L0op/medtronic-pb560/file-set-2/Mechanical Part Drawings/2971700/2971700B00.pdf

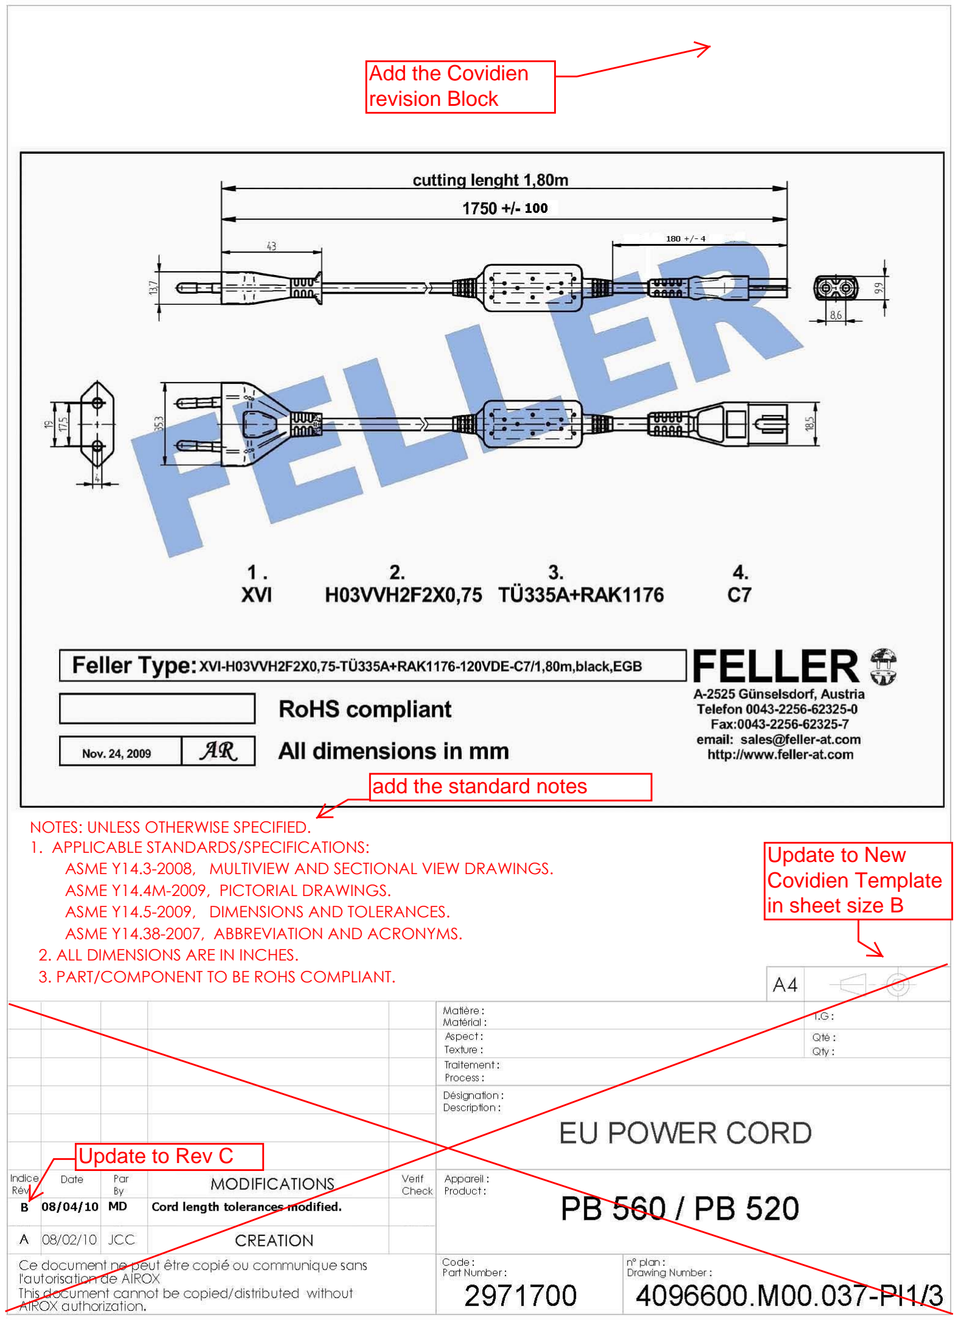
[picture p10: page 1]

NOTES: UNLESS OTHERWISE SPECIFIED.
1. APPLICABLE STANDARDS/SPECIFICATIONS:
ASME Y14.3-2008, MULTIVIEW AND SECTIONAL VIEW DRAWINGS. ASME Y14.4M-2009, PICTORIAL DRAWINGS.
ASME Y14.5-2009, DIMENSIONS AND TOLERANCES.
ASME Y14.38-2007, ABBREVIATION AND ACRONYMS.
2. ALL DIMENSIONS ARE IN INCHES.
3. PART/COMPONENT TO BE ROHS COMPLIANT.

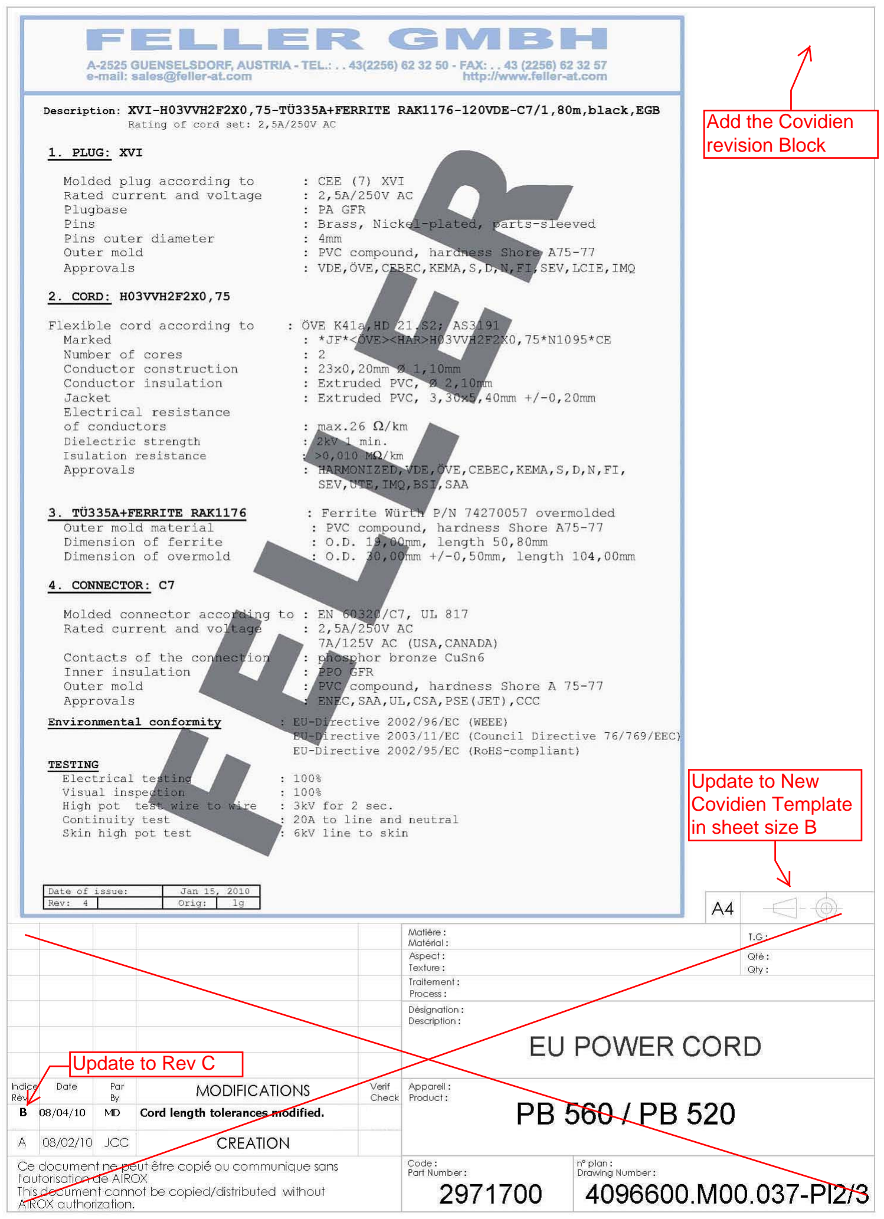
[picture p11: page 2]
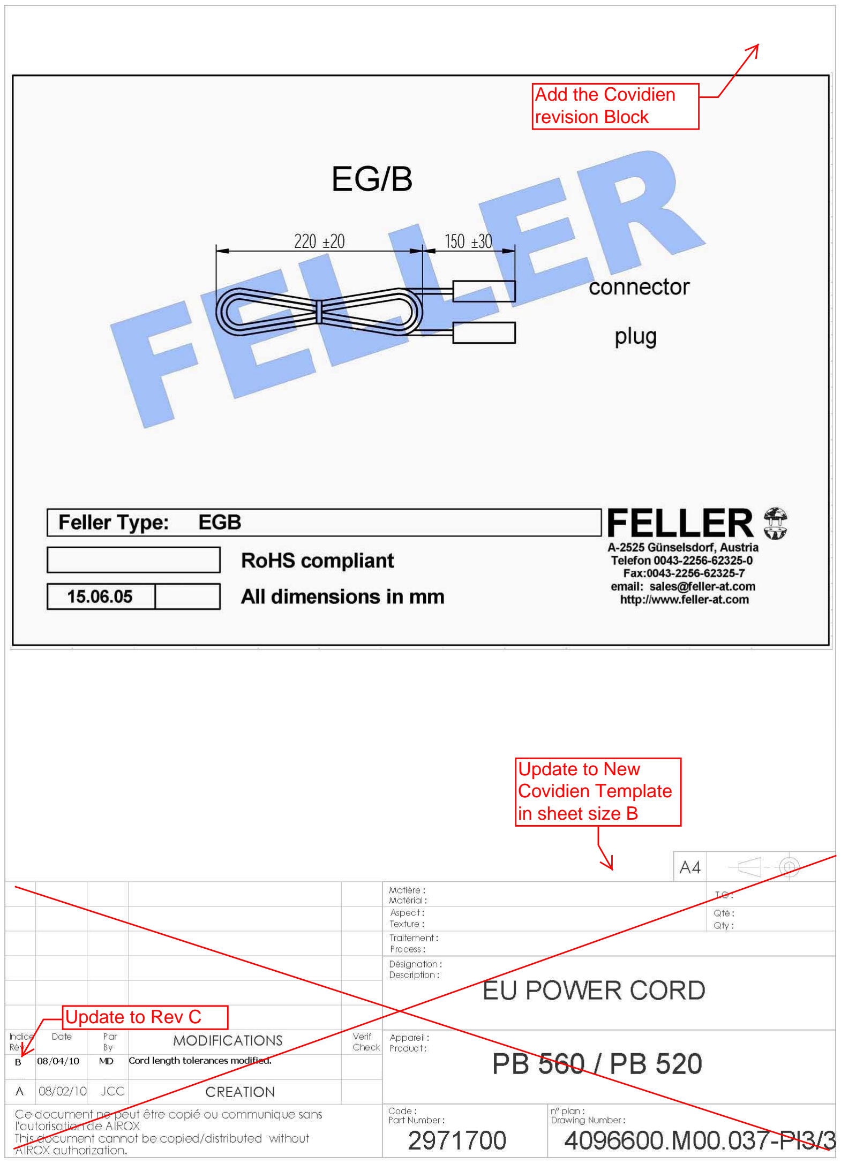
[picture p12: page 3]
