L0op/medtronic-pb560/file-set-2/Mechanical Part Drawings/3810200/38102000300.pdf

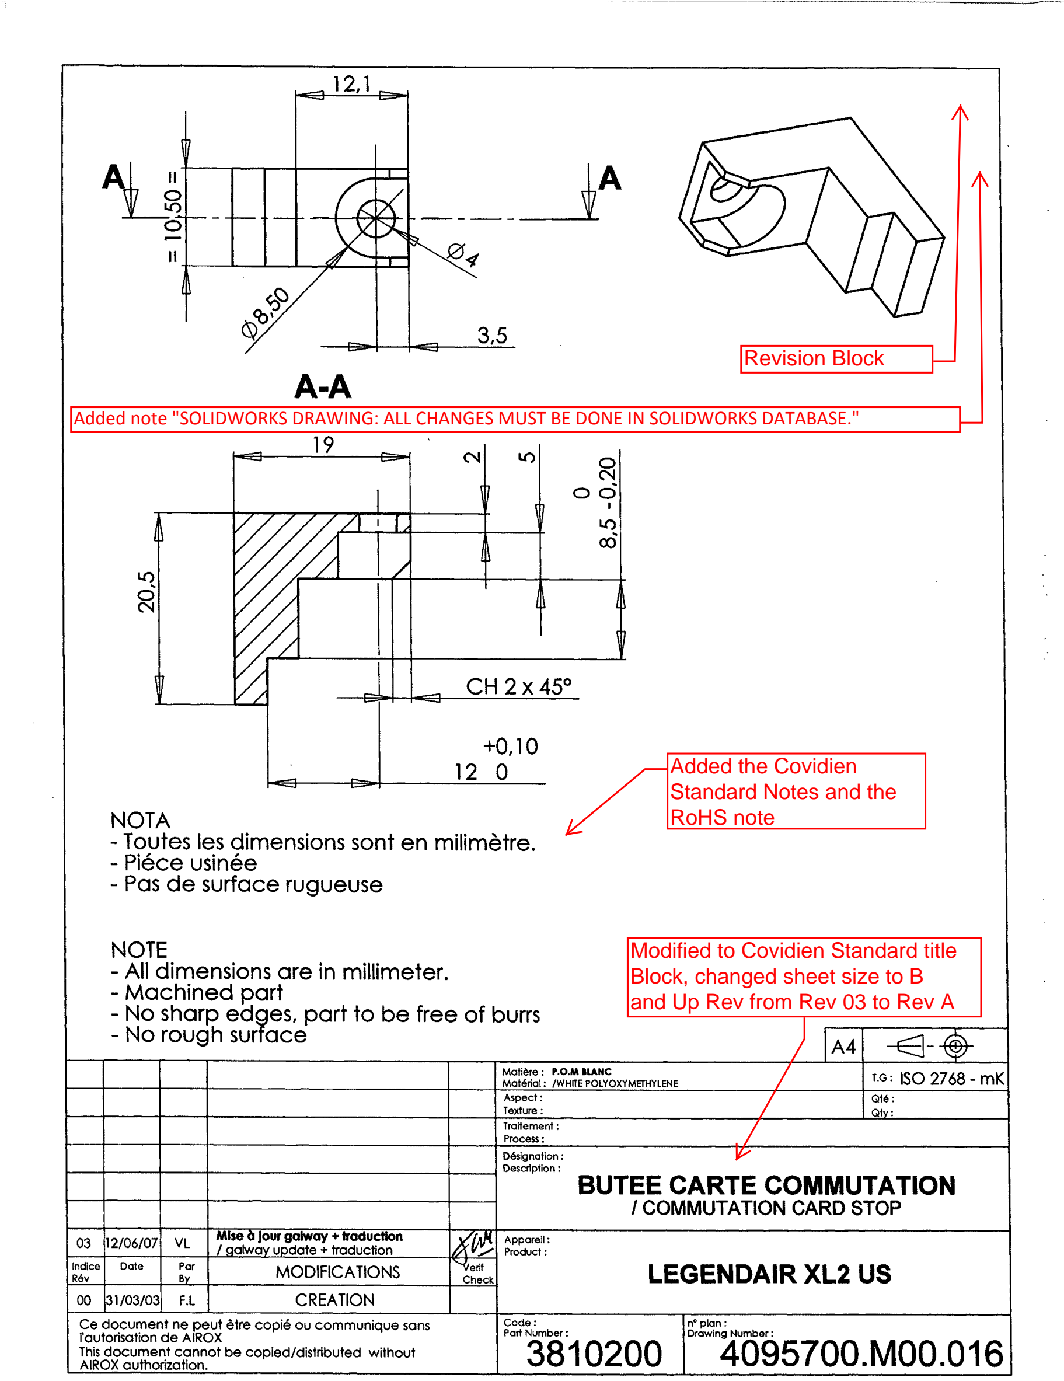
[picture p13: page 1]
