L0op/medtronic-pb560/file-set-2/Mechanical Part Drawings/3810200/3810200_Approved_Revision_03.pdf

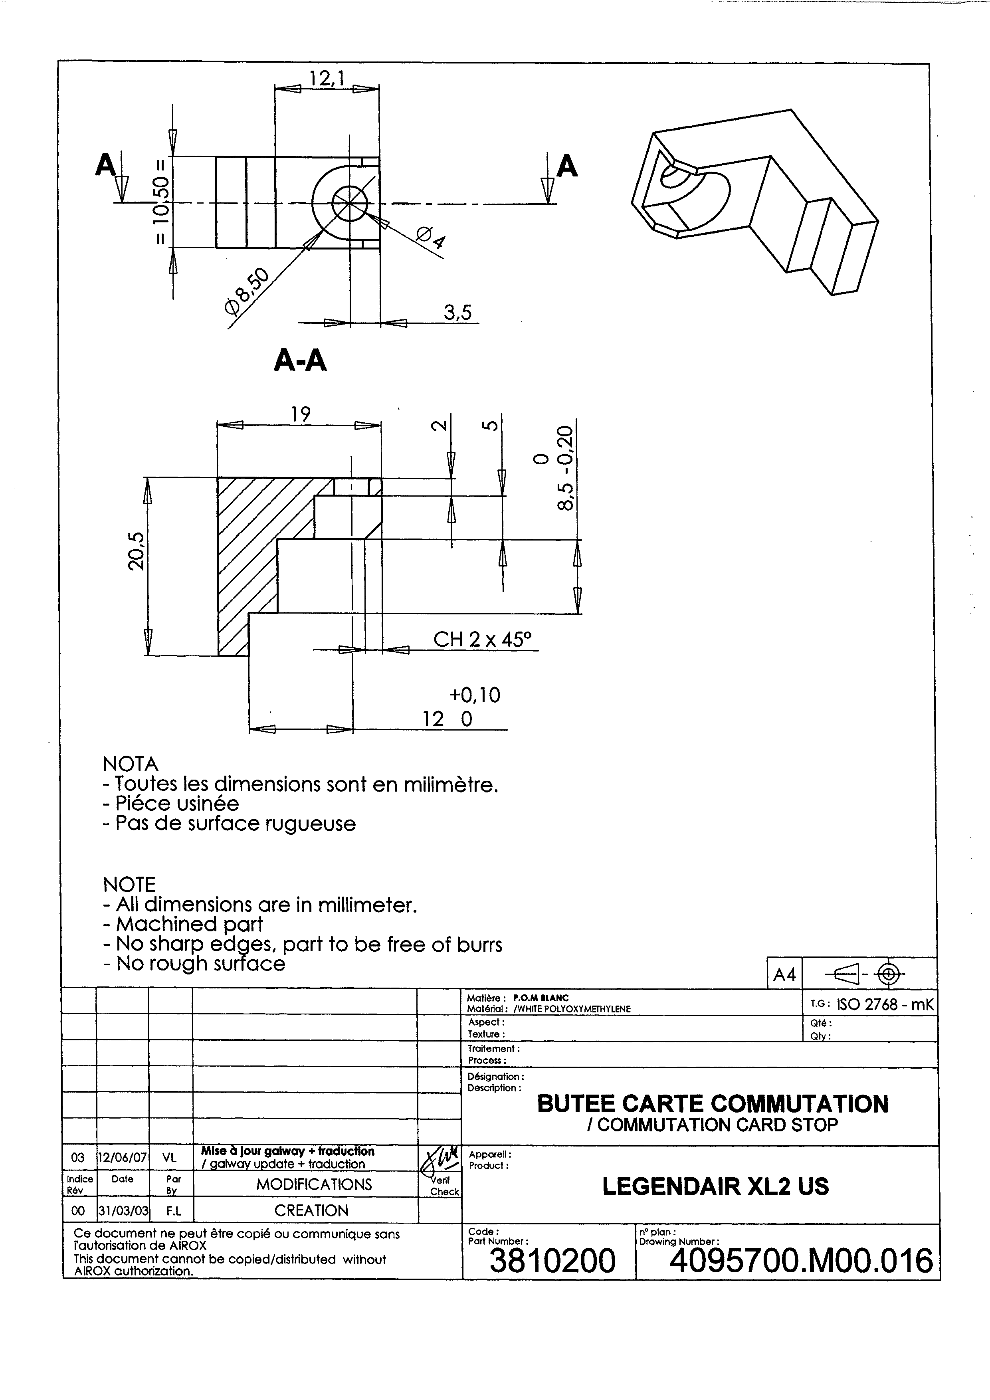
[picture p14: page 1]
