L0op/medtronic-pb560/file-set-2/Electronic PCBAs/10096315_Blower_Driver_PCBA/BOM/10096315_Blower_Driver_PCBA_BOM.xls

Creator | Jenaro | Julio
Type
Description
Title Block
Item Number | Description | Subclass | Lifecycle Phase | Rev | Rev Incorp Date | Rev Release Date | Effectivity Date
10096315 | BLOWER DRIVER CARD | Part | Production | A ECO-R252633 | 31/Jul/2013 05:51:48 PM BST | 06/Jan/2015 04:58:11 PM GMT
Page Two
UOM | Additional Categories Part | Alternate Part(s) | Alternate FG Part(s) | Restricted Access | Vendor User Group | Data Classification | Attachment Destination | Created By | Create Date | Legacy Data Source | Divesture Destination
Each | PART CATEGORY|Pc Board |  |  |  | V - Jabil SH | Confidential |  | Searcy, Teresa | 07/Jun/2012 06:03:06 PM BST | Agile RMS
Page Three
Product Family(s) | Item Type | Lot Serial Control | Document Number | RoHS Compliant | Bio Approval Number | Integration Description | Project(s) | Notes | Handling/Storage | Legacy Number
 | Customized | None | NODOCUMENT | Unknown |  | BLOWER DRIVER CARD | RSP - PB560-520 | Product Family : RSP - VENTILATOR SYSTEMS, Commodity Code: BPCS Add-Updt : FC02.17, Country of Origin: BPCS Add : FR = FRANCE, Shelf Life Days:BPCS Add-Updt : 0, Must Single Issue: BPCS Add : NO, Item Class: BPCS Add-Updt : GL-66 PB500 Series Ventilators/Gen 1, Controlled AML? : YES
Manufacturers
Attachments(Image) | Manufacture Part Has Redline | Mfr. Name | Mfr. Part Number | Mfr. Part Description | Mfr. Part Lifecycle Phase | Preferred Status | Sites | Reference Notes | RoHS Compliant? | RoHS Compliance Statement
true | false | JABIL SUPPLIER - SHANGHAI UPP CO.,LTD.(LOC) | 10096315 |  | Active | Preferred |  | CUSTOM PART PER COVIDIEN P/N 10096315 | Yes | Legacy Inventory Status: Cleared
Attachments
Is Checked Out | Has Been Redlined | Filename | File Description | File Size | File Type | Attachment Type | Modified Date | Last View Date | Checkout User | Checkout Date | Checkout Location | Checkin User | Folder Number | Folder Version
false | false | 10096315X0100.pdf | Redlined Rev-X01 to Rev-A | 141245 | pdf |  | 17/Jun/2015 06:55:30 AM BST | 17/Jun/2015 06:55:30 AM BST |  |  |  | Migration, Data | FF0007734088 | 1
false | false | 10096315_A_ECO-R252633.pdf | RMS Historical PDF - ECO-R252633 | 118400 | pdf |  | 17/Aug/2015 04:53:30 PM BST | 17/Aug/2015 04:53:30 PM BST |  |  |  | Migration, Data | FF0009842444 | 1
false | false | 10096315A00.PDF | Approved Rev-A | 122083 | PDF |  | 17/Jun/2015 06:55:30 AM BST | 17/Jun/2015 06:55:30 AM BST |  |  |  | Migration, Data | FF0007734091 | 1
false | false | 10096315A00.zip | Approved Rev-A, Source Files | 6838324 | zip |  | 17/Jun/2015 06:55:31 AM BST | 17/Jun/2015 06:55:31 AM BST |  |  |  | Migration, Data | FF0007734094 | 1
false | false | 10096315_A_ECO-R231090.pdf | RMS Historical PDF - ECO-R231090 | 118415 | pdf |  | 17/Aug/2015 04:53:30 PM BST | 17/Aug/2015 04:53:29 PM BST |  |  |  | Migration, Data | FF0009842442 | 1
