L0op/medtronic-pb560/file-set-2/Electronic PCBAs/10096315_Blower_Driver_PCBA/PCB/10096505A00/eqfs.dxf

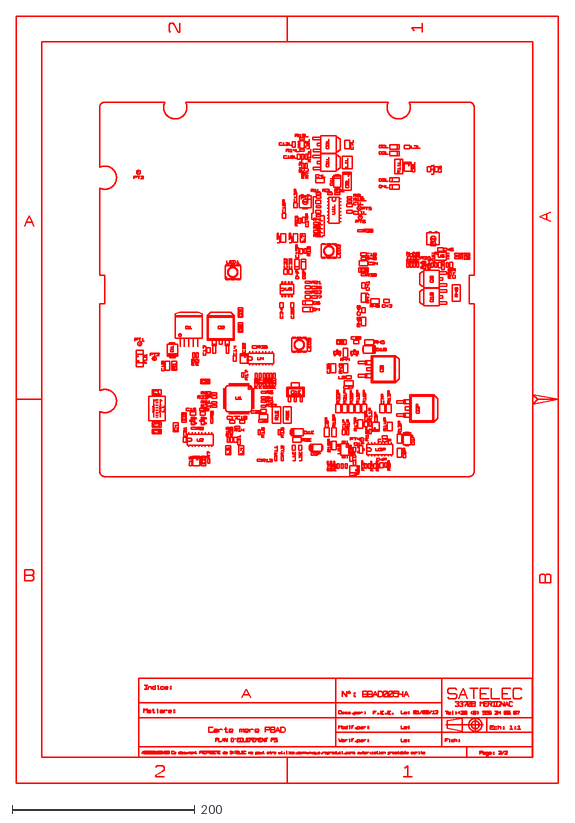
[picture p29: CAD file, 2020-04-01]
file-set-2/Electronic PCBAs/10096315_Blower_Driver_PCBA/PCB/10096505A00/eqfs.dxf
594.7 x 840.3
