L0op/medtronic-pb560/file-set-2/Electronic PCBAs/10096510_Battery_Connection_PCBA/3D_Model/contact ressort.SLDPRT

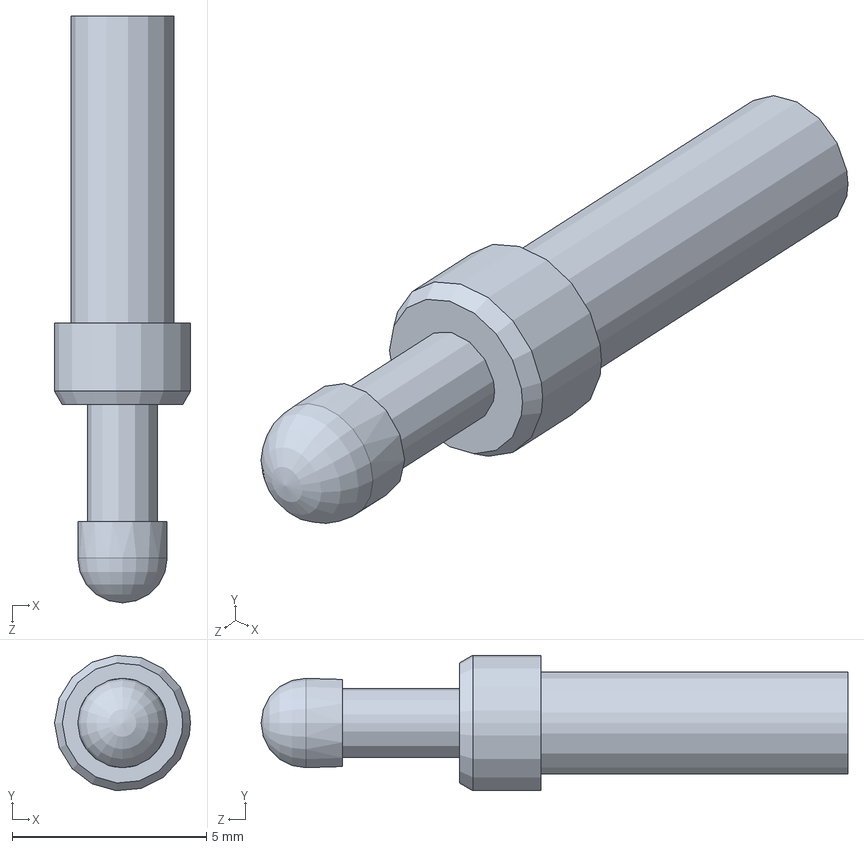
[picture p30: CAD file, 2020-04-01]
file-set-2/Electronic PCBAs/10096510_Battery_Connection_PCBA/3D_Model/contact ressort.SLDPRT
3.50 x 3.49 x 15.1 mm
