L0op/medtronic-pb560/file-set-2/Electronic PCBAs/GR106768_Buzzer_PCBA/3D_Model/cache transfo.SLDPRT

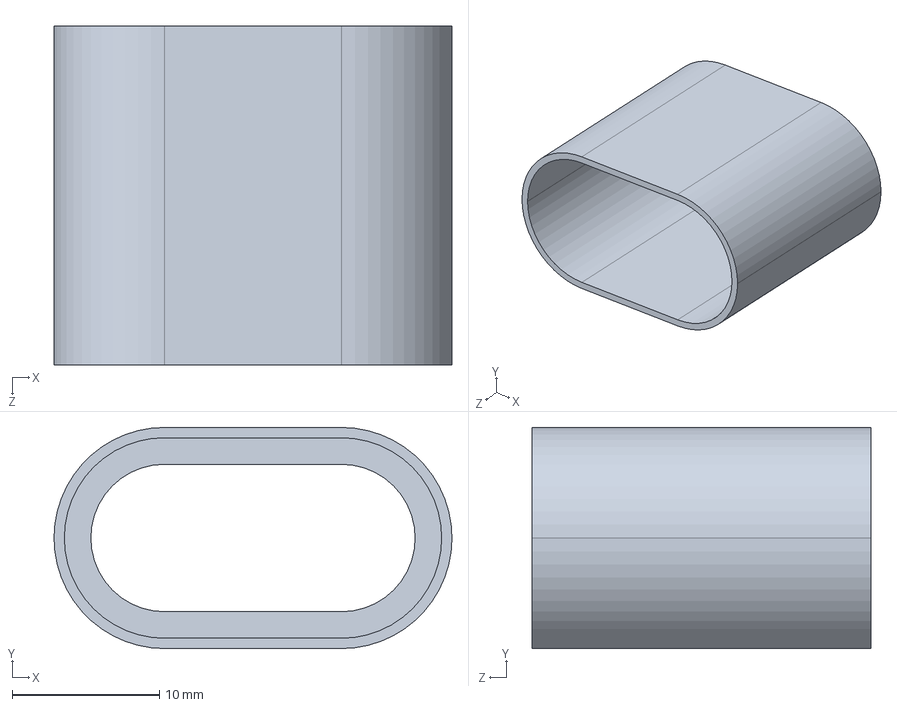
[picture p32: CAD file, 2020-04-01]
file-set-2/Electronic PCBAs/GR106768_Buzzer_PCBA/3D_Model/cache transfo.SLDPRT
27.0 x 15.0 x 23.0 mm
