L0op/medtronic-pb560/file-set-2/Electronic PCBAs/GR106768_Buzzer_PCBA/PCBA/switch.SLDPRT

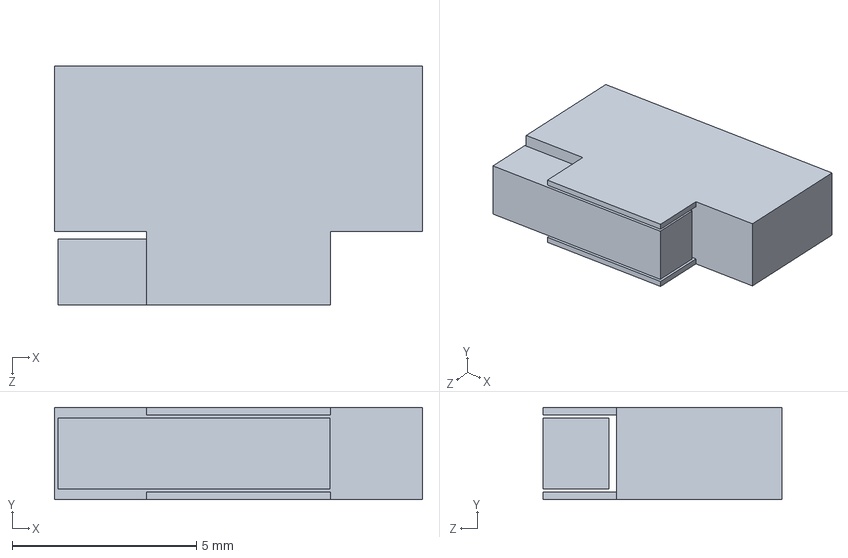
[picture p33: CAD file, 2020-04-01]
file-set-2/Electronic PCBAs/GR106768_Buzzer_PCBA/PCBA/switch.SLDPRT
10.0 x 2.50 x 6.50 mm
