L0op/medtronic-pb560/file-set-2/Mechanical Part Drawings/2982400/Battery Drawing.SLDPRT

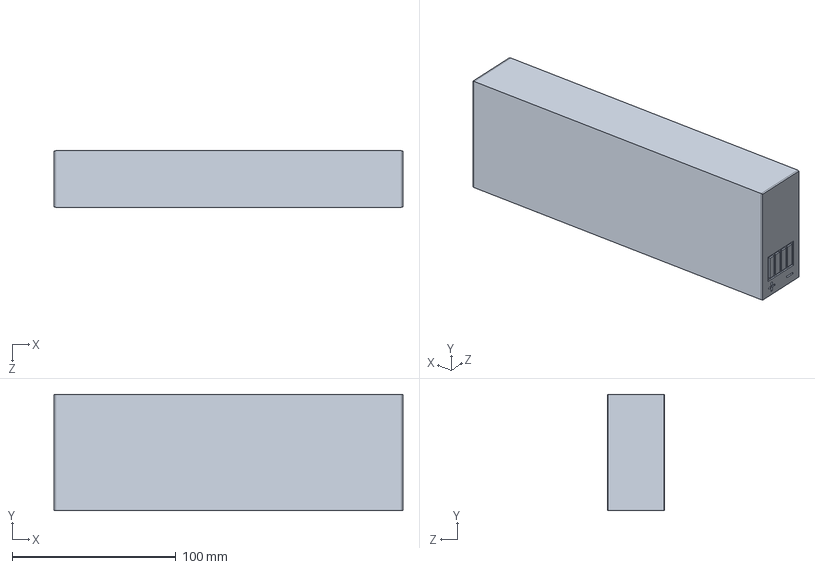
[picture p34: CAD file, 2020-04-01]
file-set-2/Mechanical Part Drawings/2982400/Battery Drawing.SLDPRT
213.0 x 71.0 x 34.5 mm
