L0op/medtronic-pb560/file-set-2/Mechanical Part Drawings/3829000/mica transparent.SLDPRT

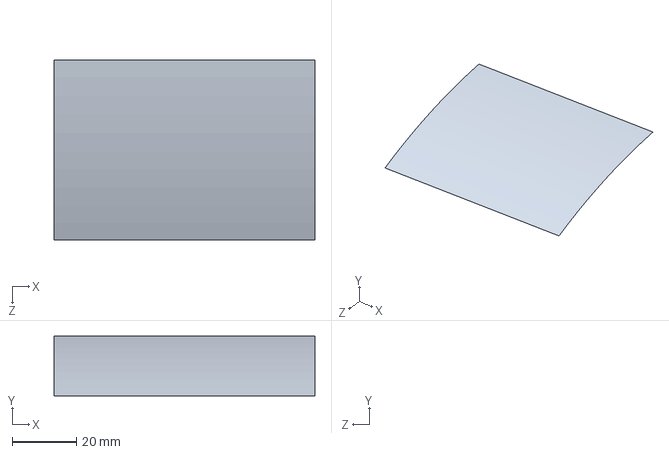
[picture p35: CAD file, 2020-04-01]
file-set-2/Mechanical Part Drawings/3829000/mica transparent.SLDPRT
81.0 x 18.5 x 56.0 mm
