L0op/medtronic-pb560/file-set-2/Electronic PCBAs/10005011_Power Management_PCBA/3842800_POWER SUPPLY BOARD - TANTALUM LESS_PCBA/PCB/Power Supply Board 3842800 (Tantalum Less) INDC/eqfc.dxf

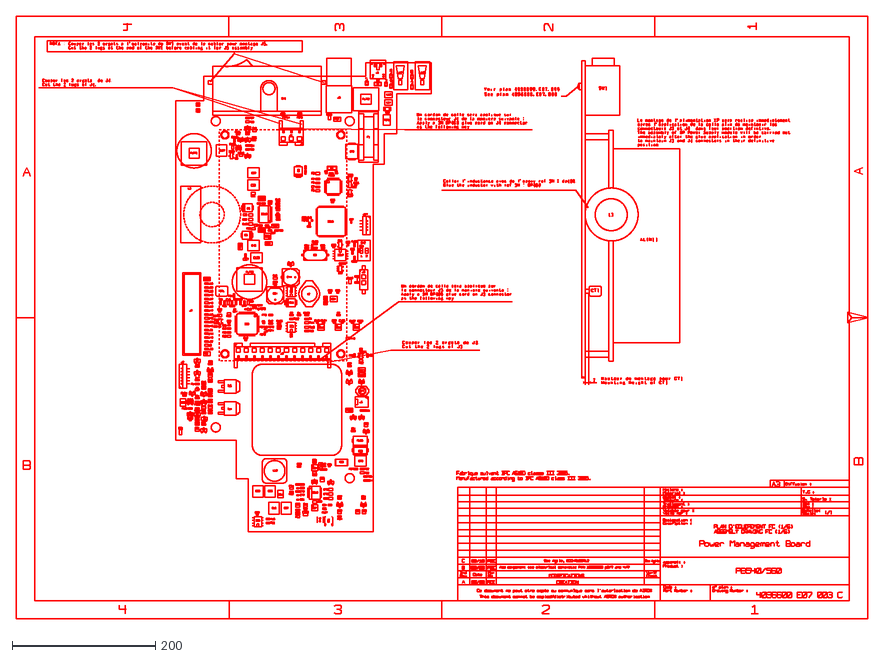
[picture p36: CAD file, 2020-04-01]
file-set-2/Electronic PCBAs/10005011_Power Management_PCBA/3842800_POWER SUPPLY BOARD - TANTALUM LESS_PCBA/PCB/Power Supply Board 3842800 (Tantalum Less) INDC/eqfc.dxf
1188.3 x 840.3
