L0op/medtronic-pb560/file-set-2/Electronic PCBAs/10005011_Power Management_PCBA/3842800_POWER SUPPLY BOARD - TANTALUM LESS_PCBA/PCBA/39-26-7265.SLDPRT

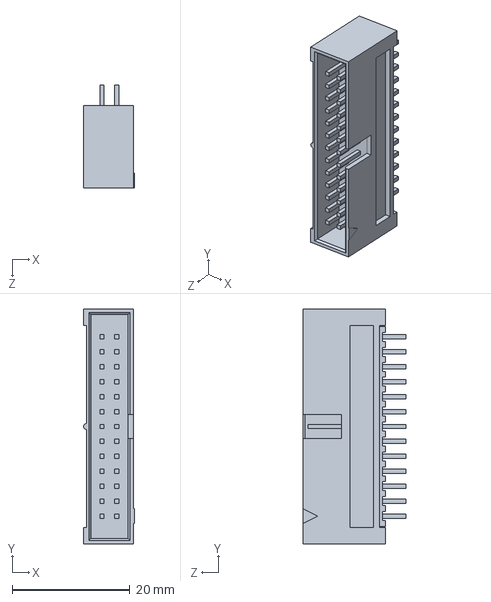
[picture p37: CAD file, 2020-04-01]
file-set-2/Electronic PCBAs/10005011_Power Management_PCBA/3842800_POWER SUPPLY BOARD - TANTALUM LESS_PCBA/PCBA/39-26-7265.SLDPRT
8.65 x 40.0 x 17.5 mm
