L0op/medtronic-pb560/file-set-2/Electronic PCBAs/10096510_Battery_Connection_PCBA/3D_Model/39-26-7108.SLDPRT

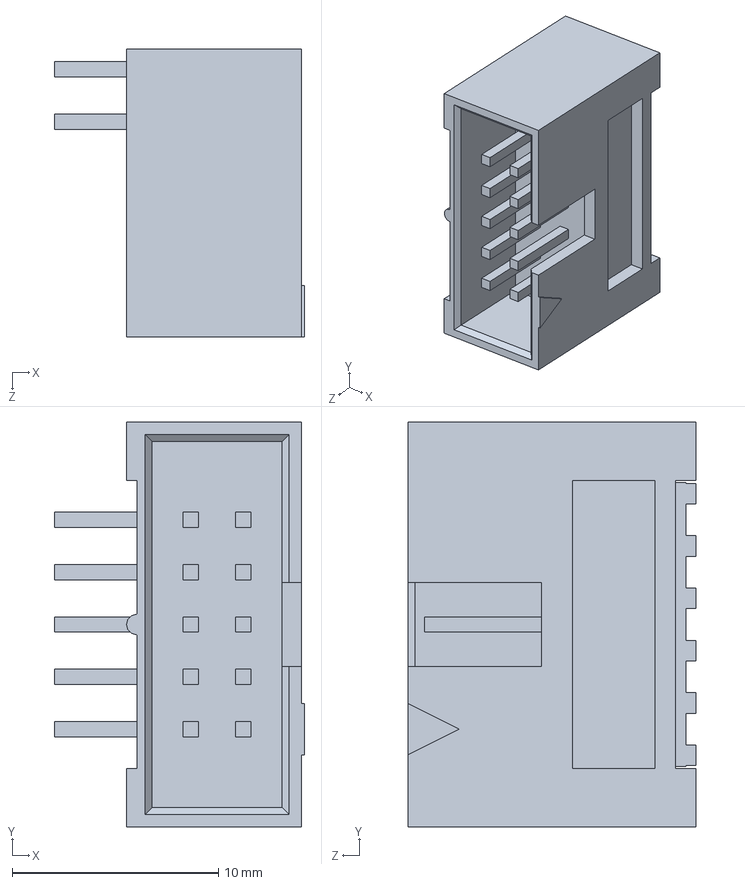
[picture p39: CAD file, 2020-04-01]
file-set-2/Electronic PCBAs/10096510_Battery_Connection_PCBA/3D_Model/39-26-7108.SLDPRT
12.1 x 19.7 x 14.0 mm
