L0op/medtronic-pb560/file-set-2/Electronic PCBAs/10096510_Battery_Connection_PCBA/PCB/10096506A00/eqfc.dxf

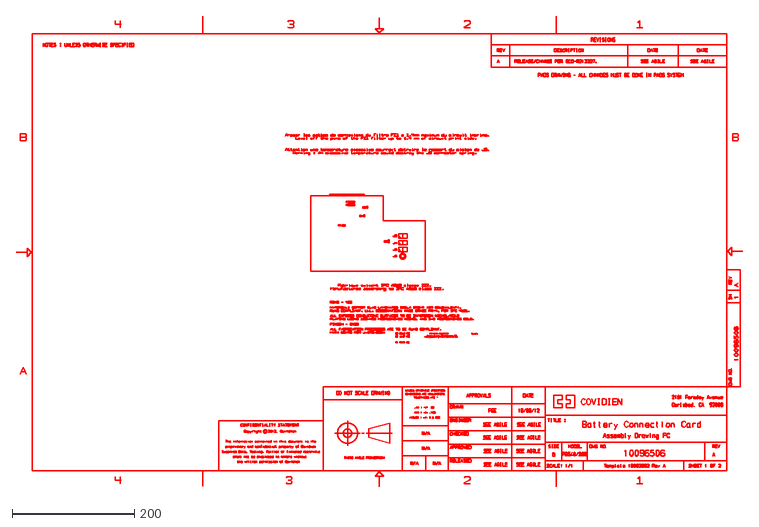
[picture p40: CAD file, 2020-04-01]
file-set-2/Electronic PCBAs/10096510_Battery_Connection_PCBA/PCB/10096506A00/eqfc.dxf
1188.1 x 770.1
