L0op/medtronic-pb560/file-set-2/Electronic PCBAs/10106052_PowerPack_PCBA/PCBA/MOLEX 02661-4020.SLDPRT

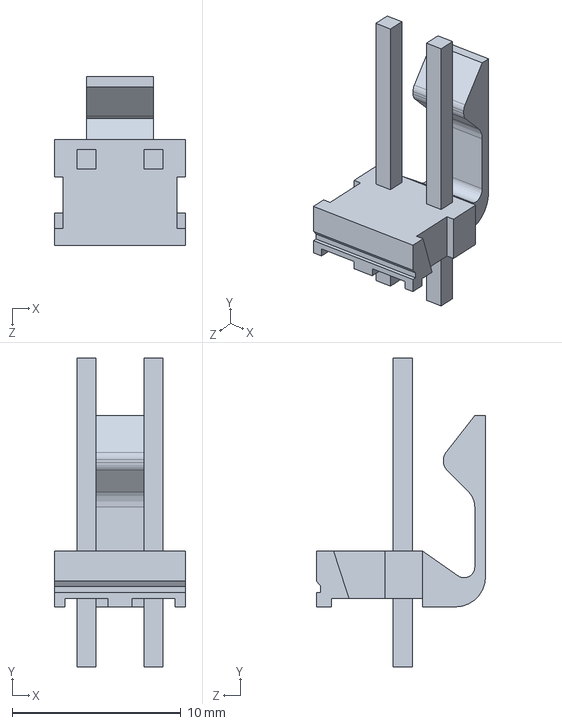
[picture p41: CAD file, 2020-04-01]
file-set-2/Electronic PCBAs/10106052_PowerPack_PCBA/PCBA/MOLEX 02661-4020.SLDPRT
7.77 x 18.3 x 10.0 mm
