L0op/medtronic-pb560/file-set-2/Electronic PCBAs/GR106768_Buzzer_PCBA/PCBA/buzzer1.SLDPRT

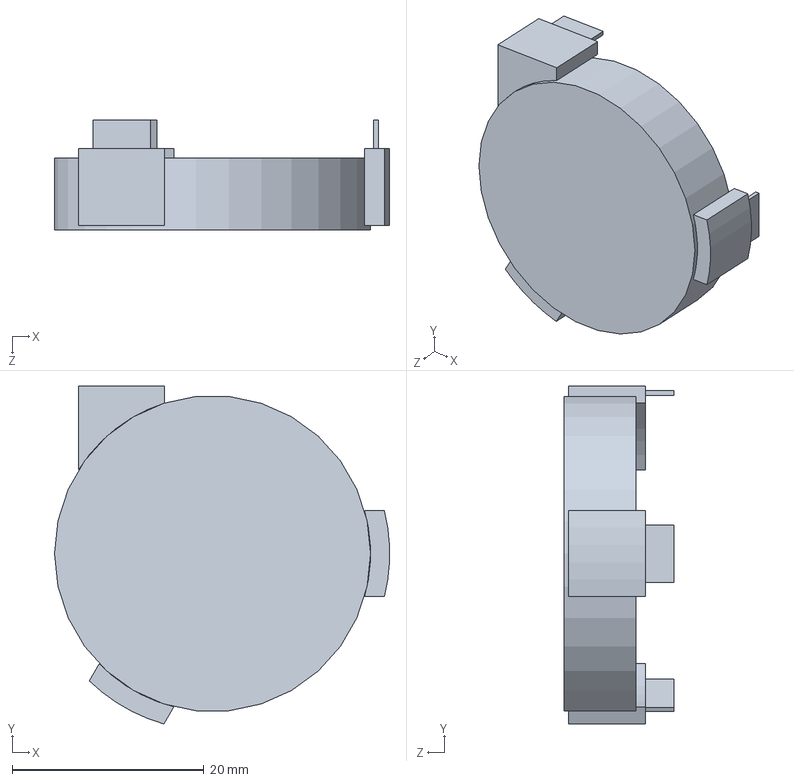
[picture p42: CAD file, 2020-04-01]
file-set-2/Electronic PCBAs/GR106768_Buzzer_PCBA/PCBA/buzzer1.SLDPRT
35.0 x 35.3 x 11.5 mm
