L0op/medtronic-pb560/file-set-2/Electronic PCBAs/GR106769_CPU_PCBA/3D_Model/capteurpressionASDX001D44R.SLDPRT

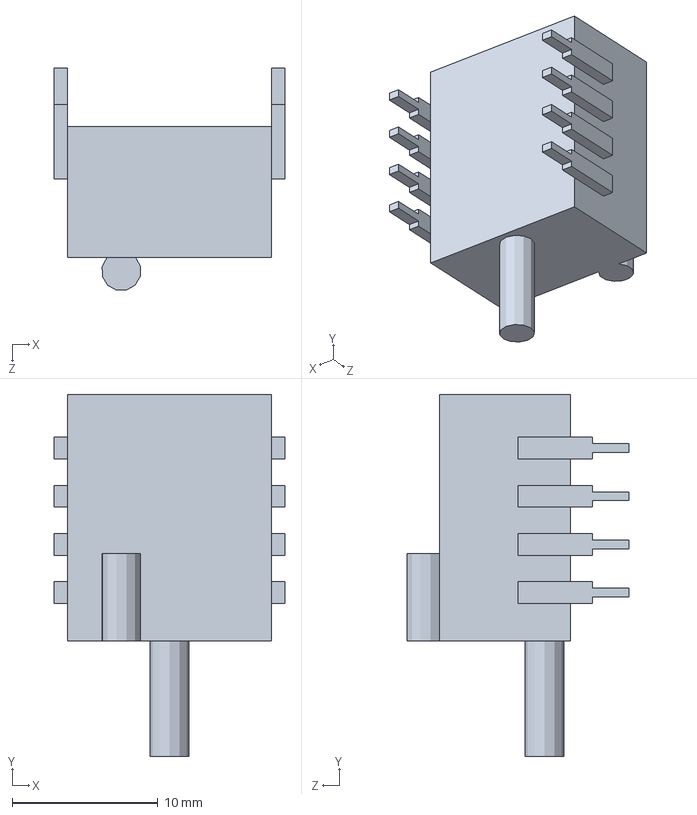
[picture p43: CAD file, 2020-04-01]
file-set-2/Electronic PCBAs/GR106769_CPU_PCBA/3D_Model/capteurpressionASDX001D44R.SLDPRT
15.8 x 24.8 x 15.2 mm
