L0op/medtronic-pb560/file-set-2/Mechanical Part Drawings/2967200/suspente.SLDPRT

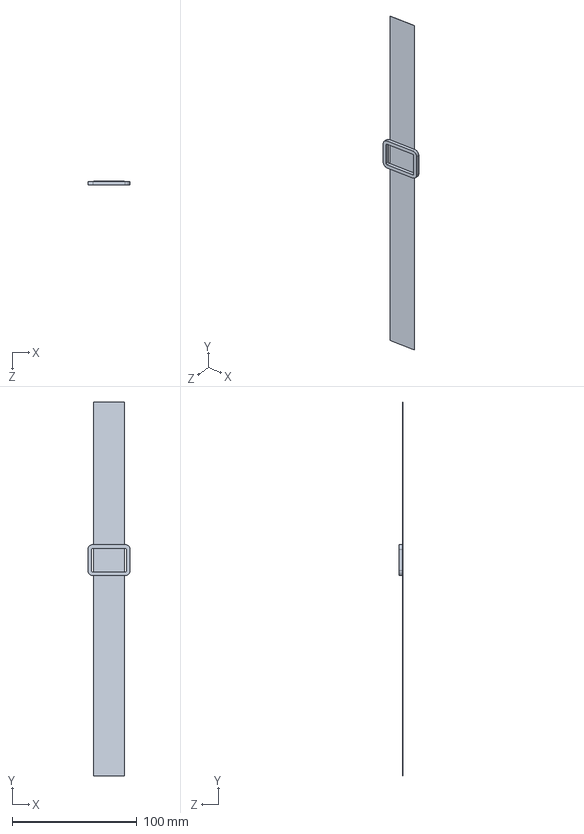
[picture p44: CAD file, 2020-04-01]
file-set-2/Mechanical Part Drawings/2967200/suspente.SLDPRT
34.0 x 300.0 x 3.20 mm
