L0op/medtronic-pb560/file-set-2/Mechanical Part Drawings/3829000/accroche sangle 25.SLDPRT

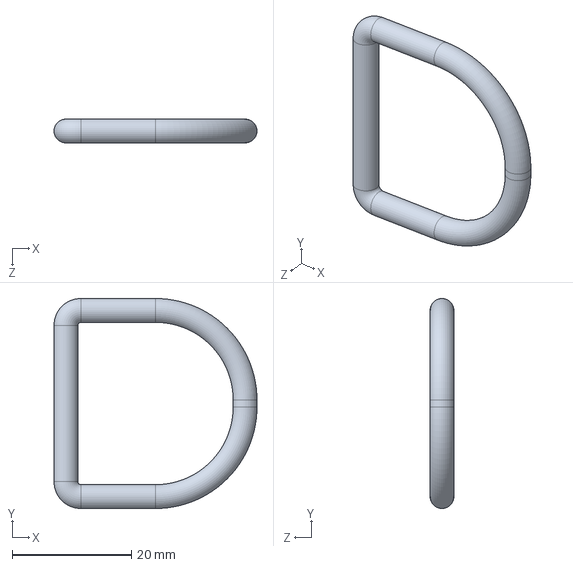
[picture p45: CAD file, 2020-04-01]
file-set-2/Mechanical Part Drawings/3829000/accroche sangle 25.SLDPRT
34.0 x 35.2 x 4.00 mm
