L0op/medtronic-pb560/file-set-2/Electronic PCBAs/10005011_Power Management_PCBA/3842800_POWER SUPPLY BOARD - TANTALUM LESS_PCBA/PCBA/condensateur dia 10.SLDPRT

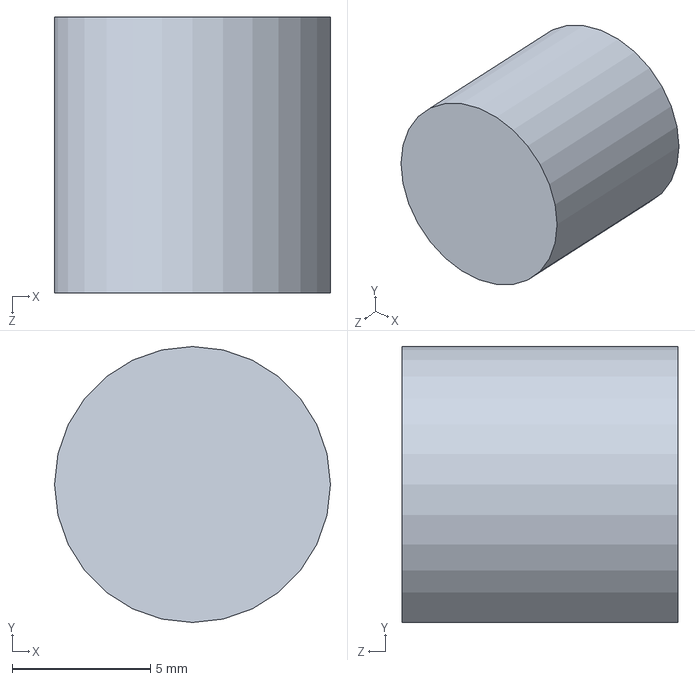
[picture p46: CAD file, 2020-04-01]
file-set-2/Electronic PCBAs/10005011_Power Management_PCBA/3842800_POWER SUPPLY BOARD - TANTALUM LESS_PCBA/PCBA/condensateur dia 10.SLDPRT
10.0 x 10.0 x 10.0 mm
