L0op/medtronic-pb560/file-set-2/Electronic PCBAs/10096315_Blower_Driver_PCBA/PCB/10096505A00/per.dxf

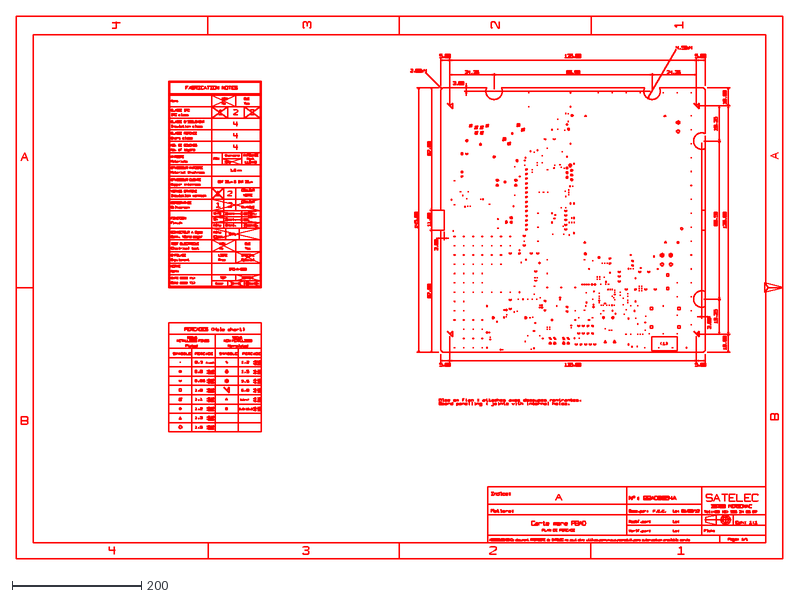
[picture p47: CAD file, 2020-04-01]
file-set-2/Electronic PCBAs/10096315_Blower_Driver_PCBA/PCB/10096505A00/per.dxf
1188.3 x 840.3
