L0op/medtronic-pb560/file-set-2/Electronic PCBAs/10096510_Battery_Connection_PCBA/PCB/10096506A00/eqfs.dxf

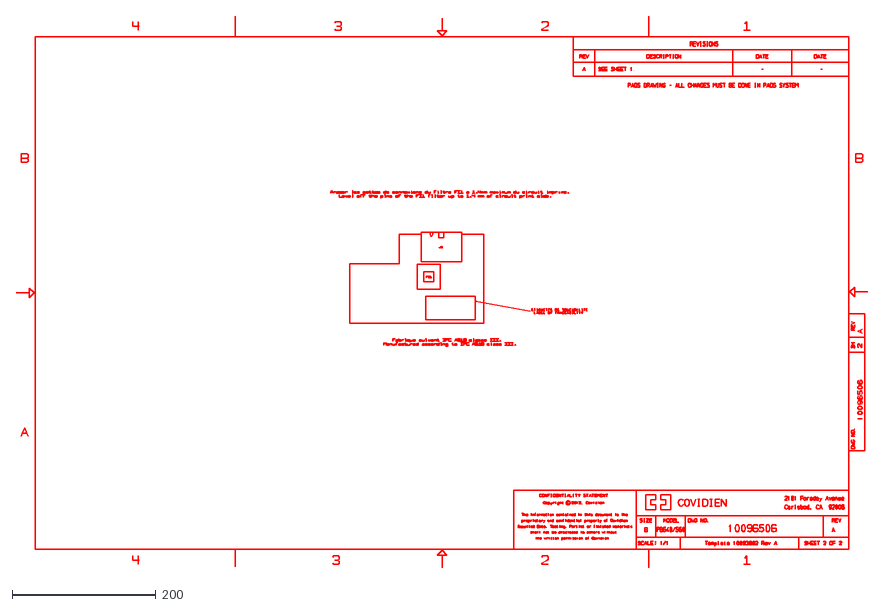
[picture p48: CAD file, 2020-04-01]
file-set-2/Electronic PCBAs/10096510_Battery_Connection_PCBA/PCB/10096506A00/eqfs.dxf
1186.1 x 768.8
