L0op/medtronic-pb560/file-set-2/Mechanical Part Drawings/10079556/Insp Mod Connector.SLDPRT

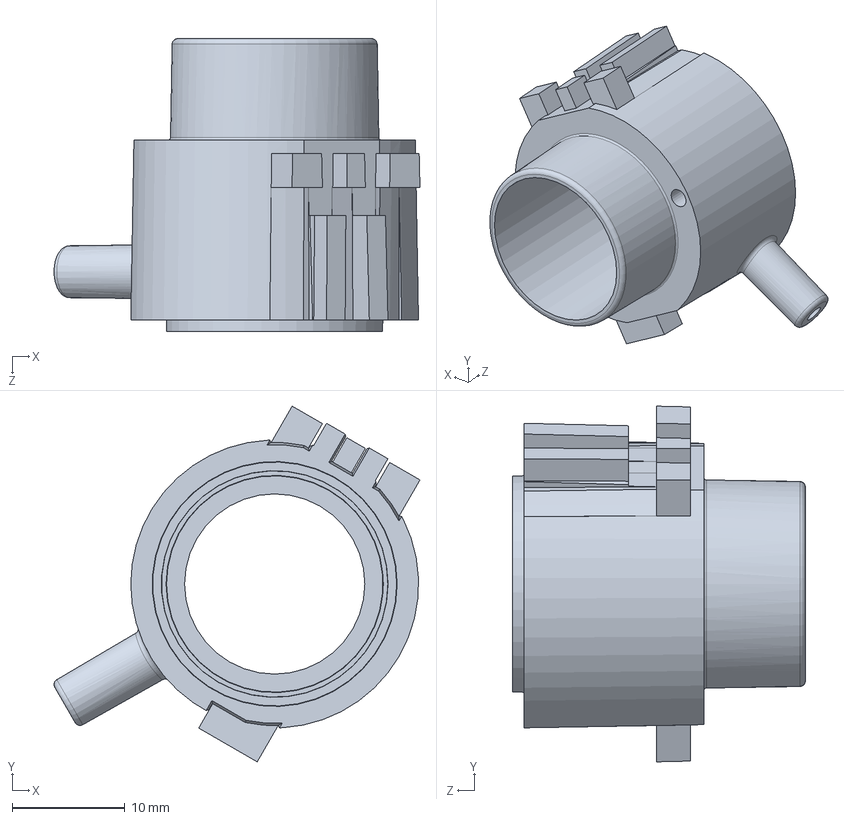
[picture p49: CAD file, 2020-04-01]
file-set-2/Mechanical Part Drawings/10079556/Insp Mod Connector.SLDPRT
32.5 x 31.6 x 26.0 mm
