L0op/medtronic-pb560/file-set-2/Electronic PCBAs/10005011_Power Management_PCBA/3842800_POWER SUPPLY BOARD - TANTALUM LESS_PCBA/PCBA/09-48-4128.SLDPRT

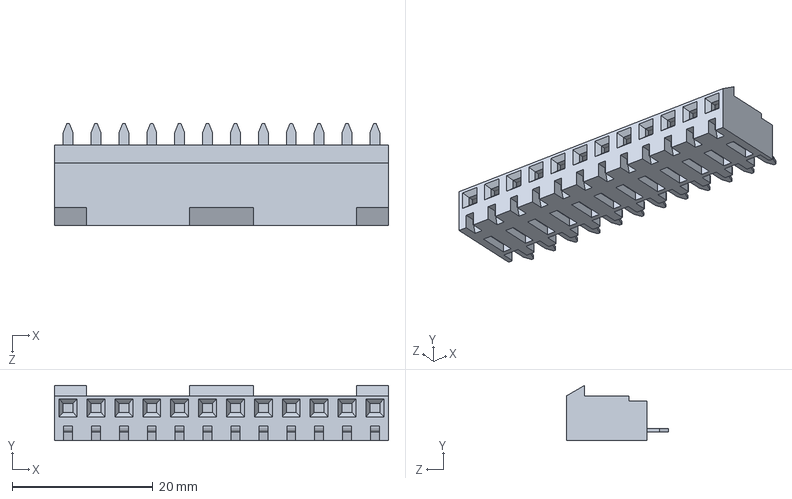
[picture p50: CAD file, 2020-04-01]
file-set-2/Electronic PCBAs/10005011_Power Management_PCBA/3842800_POWER SUPPLY BOARD - TANTALUM LESS_PCBA/PCBA/09-48-4128.SLDPRT
47.4 x 7.82 x 14.5 mm
