L0op/medtronic-pb560/file-set-2/Electronic PCBAs/10096510_Battery_Connection_PCBA/3D_Model/connecteur batterie.SLDPRT

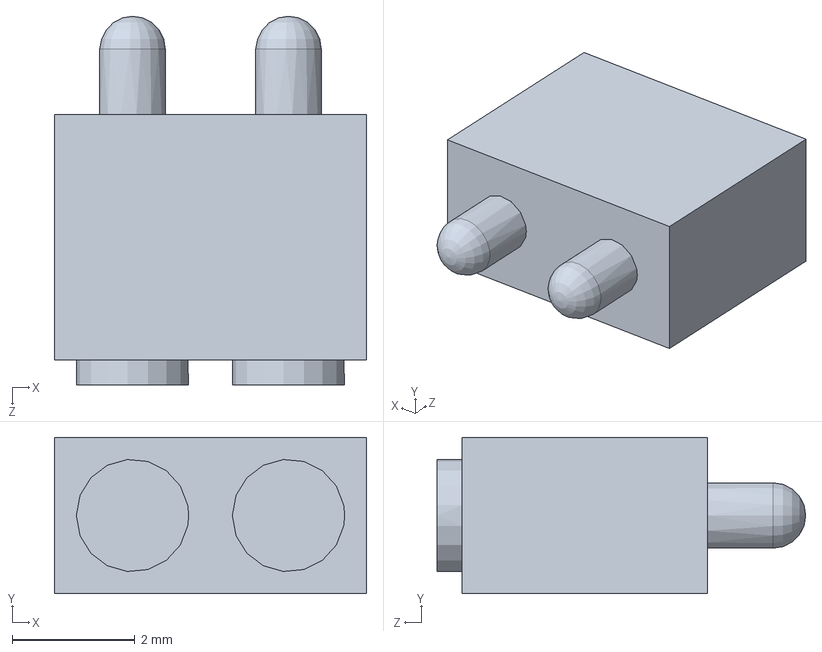
[picture p51: CAD file, 2020-04-01]
file-set-2/Electronic PCBAs/10096510_Battery_Connection_PCBA/3D_Model/connecteur batterie.SLDPRT
5.08 x 2.54 x 6.00 mm
