L0op/medtronic-pb560/file-set-2/Electronic PCBAs/GR106769_CPU_PCBA/3D_Model/capteur pression absolue.SLDPRT

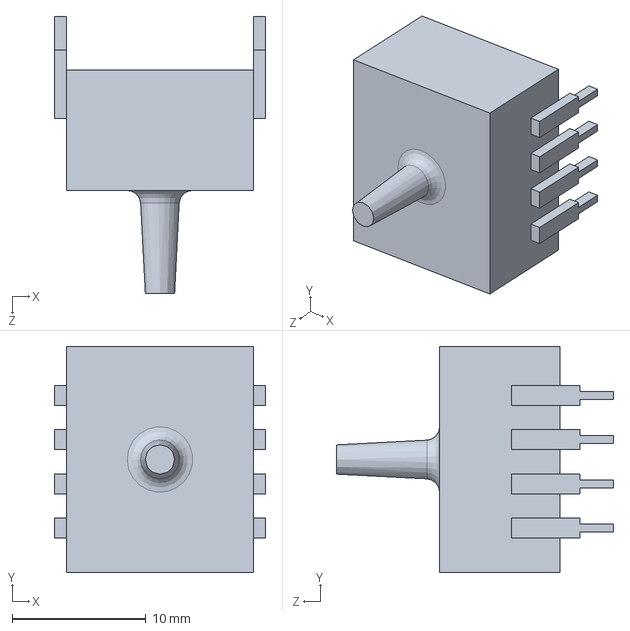
[picture p52: CAD file, 2020-04-01]
file-set-2/Electronic PCBAs/GR106769_CPU_PCBA/3D_Model/capteur pression absolue.SLDPRT
15.8 x 16.9 x 20.7 mm
