L0op/medtronic-pb560/file-set-2/3D CAD Models/entretoise hexa  m3x8.SLDPRT

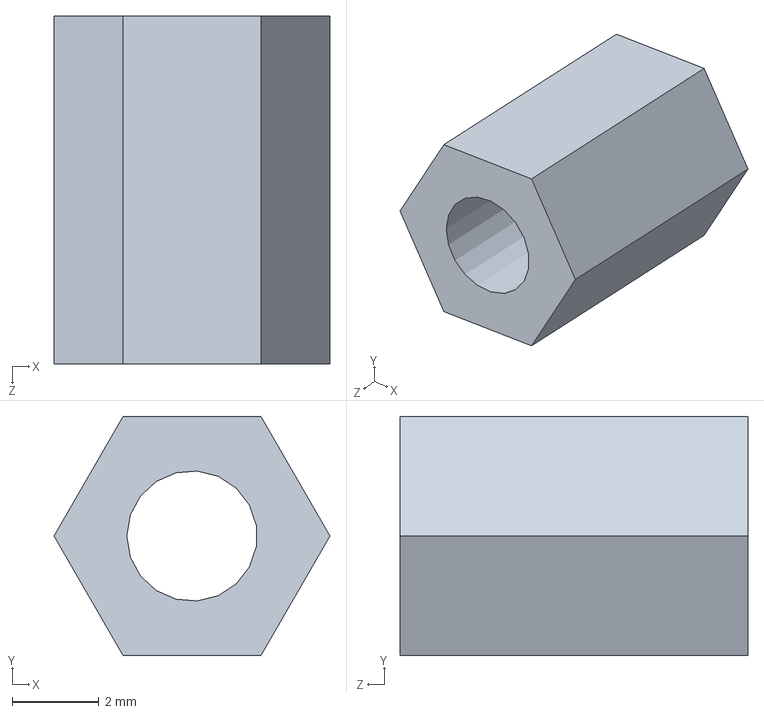
[picture p53: CAD file, 2020-04-01]
file-set-2/3D CAD Models/entretoise hexa m3x8.SLDPRT
6.35 x 5.50 x 8.00 mm
