L0op/medtronic-pb560/file-set-2/Electronic PCBAs/10106052_PowerPack_PCBA/PCBA/JST S2B-ZR-SM4A-TF.SLDPRT

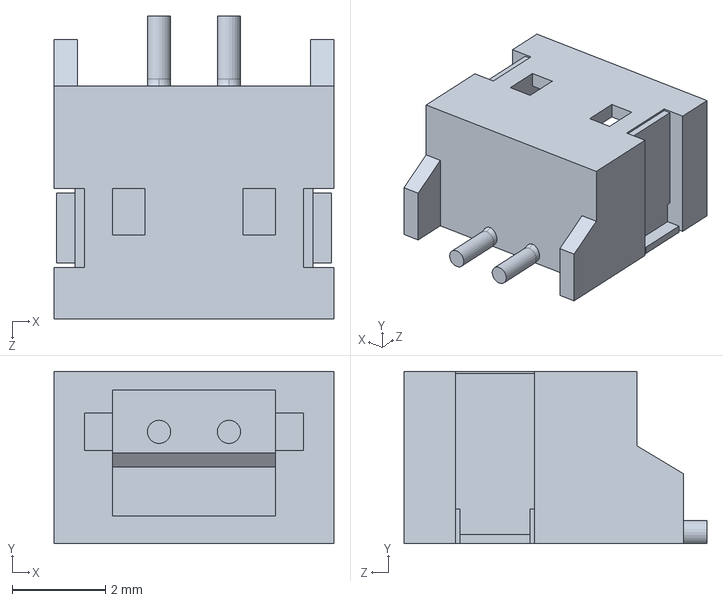
[picture p54: CAD file, 2020-04-01]
file-set-2/Electronic PCBAs/10106052_PowerPack_PCBA/PCBA/JST S2B-ZR-SM4A-TF.SLDPRT
6.00 x 3.70 x 6.50 mm
