L0op/medtronic-pb560/file-set-2/Electronic PCBAs/GR106769_CPU_PCBA/3D_Model/feritte nappe afficheur.SLDPRT

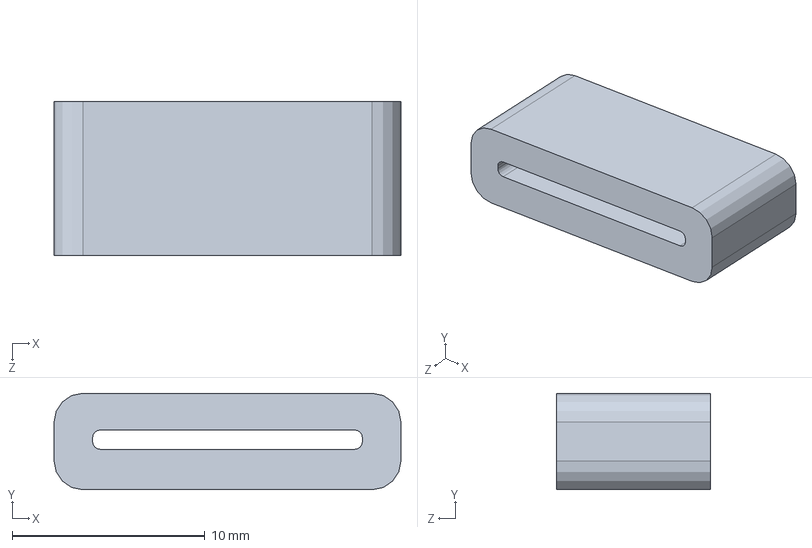
[picture p55: CAD file, 2020-04-01]
file-set-2/Electronic PCBAs/GR106769_CPU_PCBA/3D_Model/feritte nappe afficheur.SLDPRT
18.0 x 5.00 x 8.00 mm
