L0op/medtronic-pb560/file-set-2/Mechanical Part Drawings/3829000/toile dessus.SLDPRT

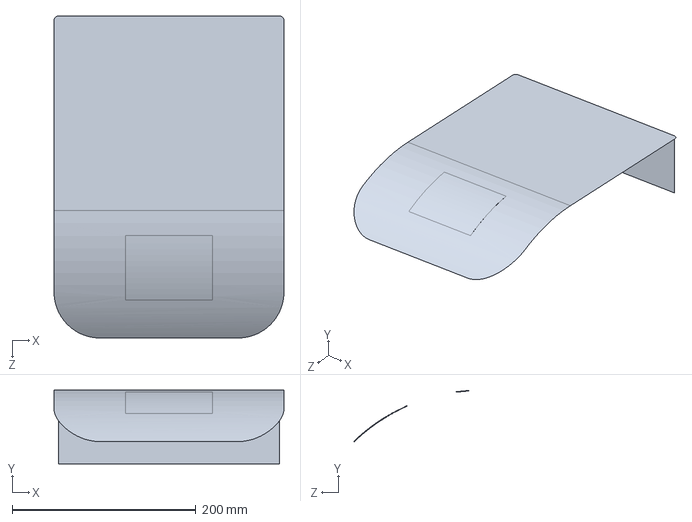
[picture p56: CAD file, 2020-04-01]
file-set-2/Mechanical Part Drawings/3829000/toile dessus.SLDPRT
250.0 x 79.9 x 350.0 mm
