L0op/medtronic-pb560/file-set-2/Electronic PCBAs/10005011_Power Management_PCBA/3842800_POWER SUPPLY BOARD - TANTALUM LESS_PCBA/PCBA/connecteur USB miniB.SLDPRT

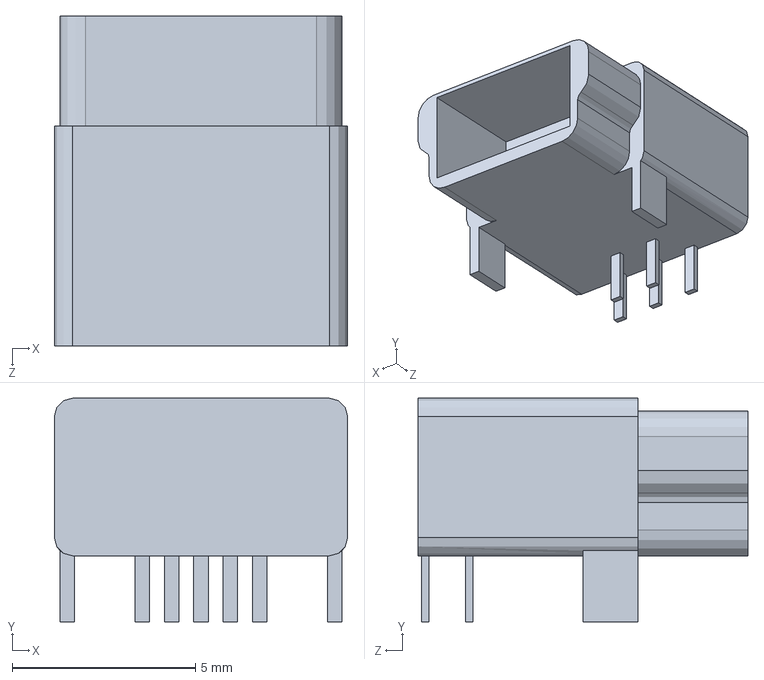
[picture p57: CAD file, 2020-04-01]
file-set-2/Electronic PCBAs/10005011_Power Management_PCBA/3842800_POWER SUPPLY BOARD - TANTALUM LESS_PCBA/PCBA/connecteur USB miniB.SLDPRT
8.00 x 6.10 x 9.00 mm
