L0op/medtronic-pb560/file-set-2/Electronic PCBAs/GR106768_Buzzer_PCBA/3D_Model/condensateur.SLDPRT

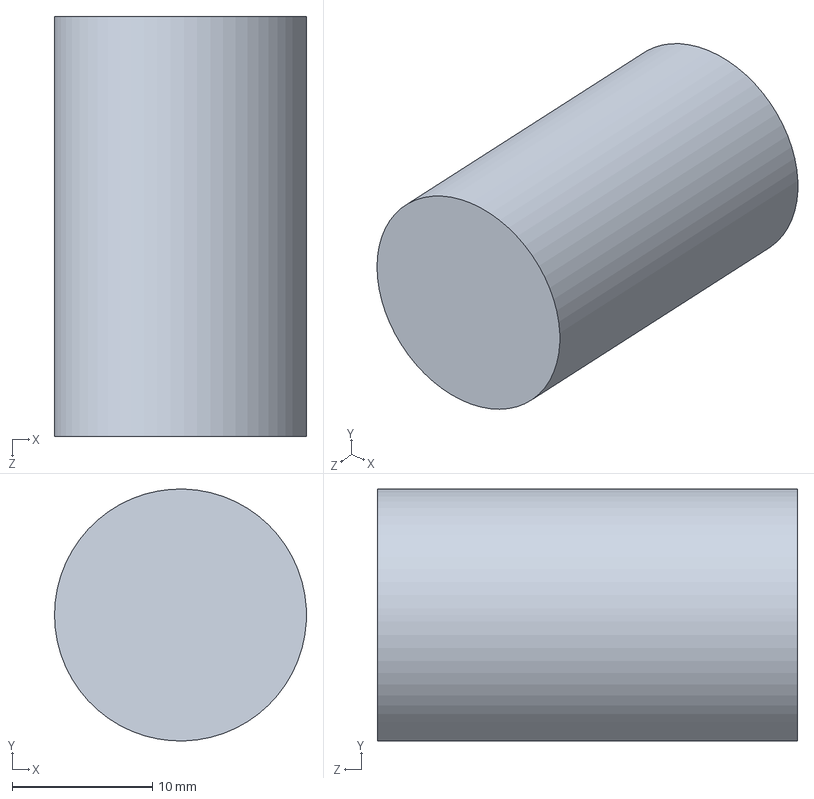
[picture p58: CAD file, 2020-04-01]
file-set-2/Electronic PCBAs/GR106768_Buzzer_PCBA/3D_Model/condensateur.SLDPRT
18.0 x 18.0 x 30.0 mm
