L0op/medtronic-pb560/file-set-2/Mechanical Part Drawings/3829000/mousqueton.SLDPRT

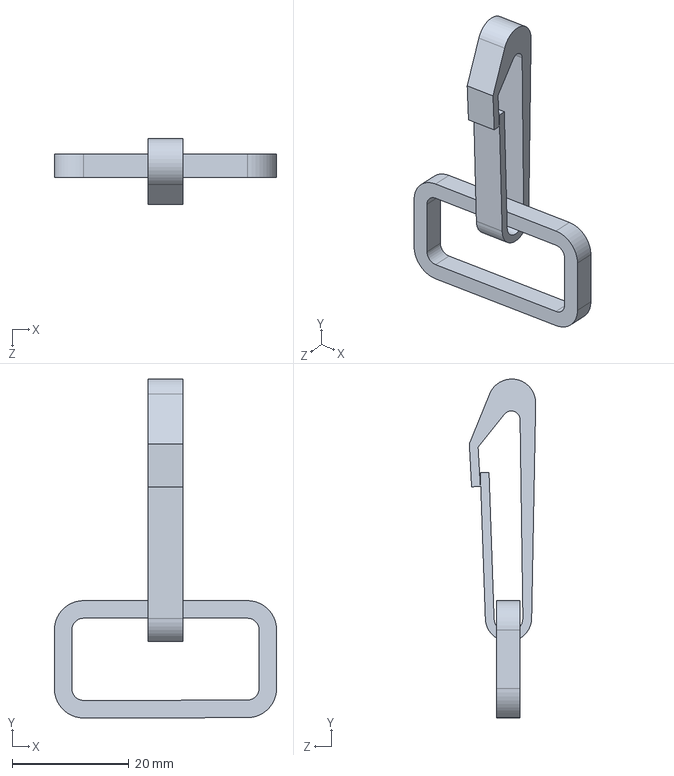
[picture p59: CAD file, 2020-04-01]
file-set-2/Mechanical Part Drawings/3829000/mousqueton.SLDPRT
38.0 x 58.0 x 11.3 mm
