L0op/medtronic-pb560/file-set-2/Electronic PCBAs/GR106769_CPU_PCBA/3D_Model/connector.SLDPRT

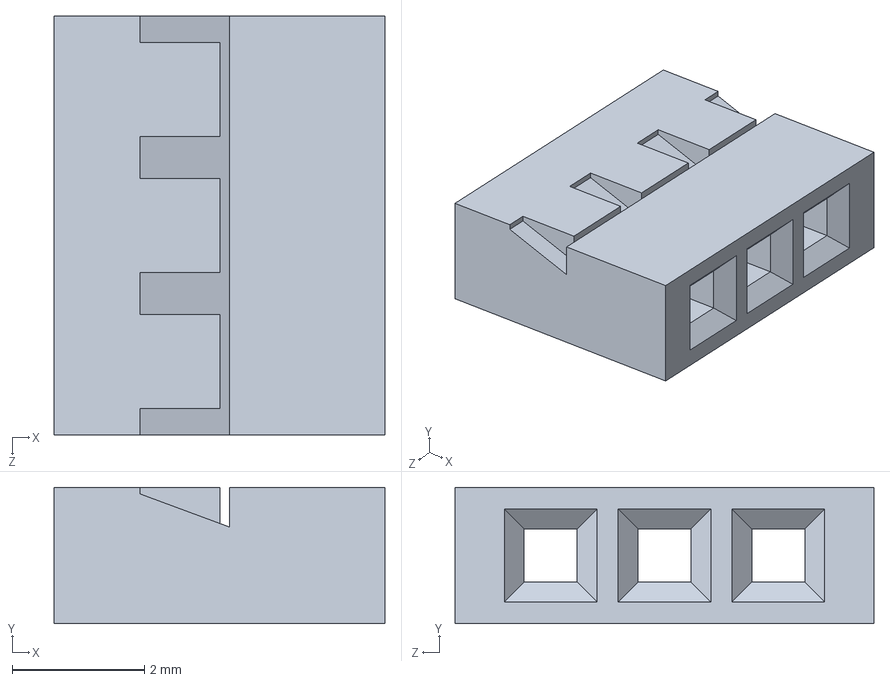
[picture p61: CAD file, 2020-04-01]
file-set-2/Electronic PCBAs/GR106769_CPU_PCBA/3D_Model/connector.SLDPRT
5.00 x 2.06 x 6.33 mm
