L0op/medtronic-pb560/file-set-2/Mechanical Part Drawings/2967200/ceinturage.SLDPRT

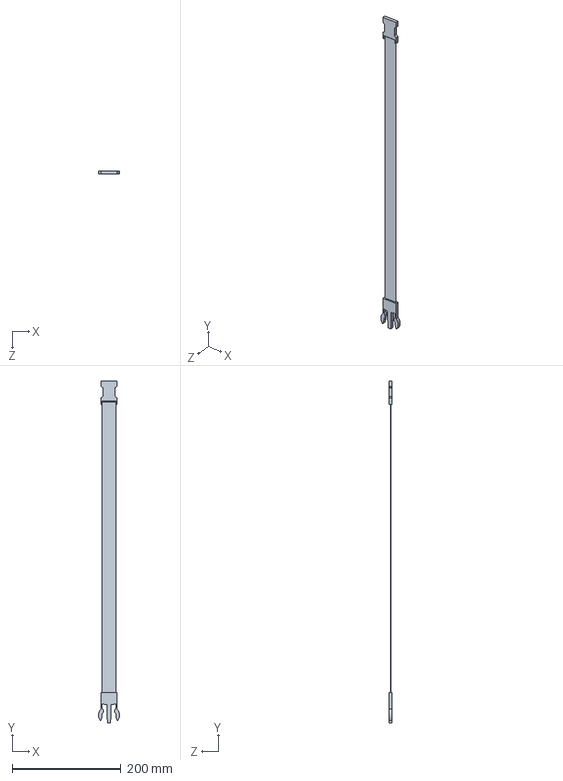
[picture p62: CAD file, 2020-04-01]
file-set-2/Mechanical Part Drawings/2967200/ceinturage.SLDPRT
39.0 x 630.3 x 6.00 mm
