L0op/medtronic-pb560/file-set-2/Electronic PCBAs/10096315_Blower_Driver_PCBA/3D_Model/regulateur.SLDPRT

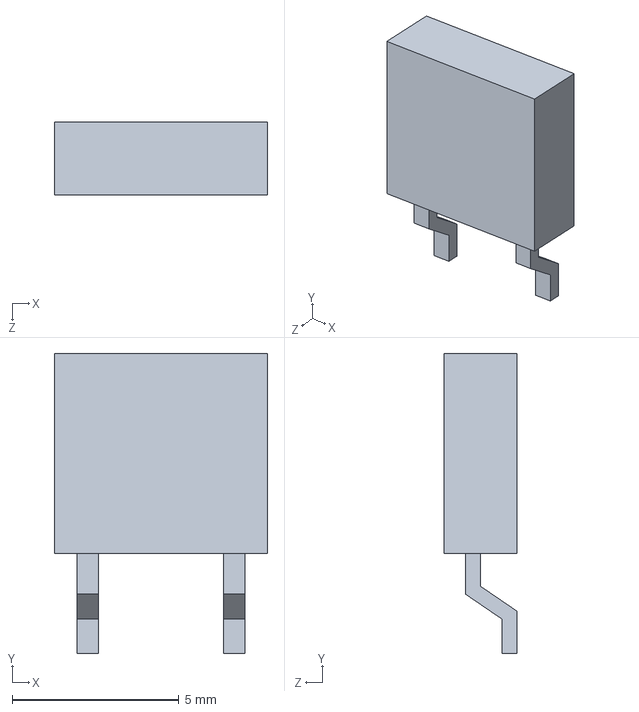
[picture p64: CAD file, 2020-04-01]
file-set-2/Electronic PCBAs/10096315_Blower_Driver_PCBA/3D_Model/regulateur.SLDPRT
6.40 x 9.00 x 2.20 mm
