L0op/medtronic-pb560/file-set-2/Electronic PCBAs/GR106769_CPU_PCBA/3D_Model/Vis KA22x5 hexalobes.SLDPRT

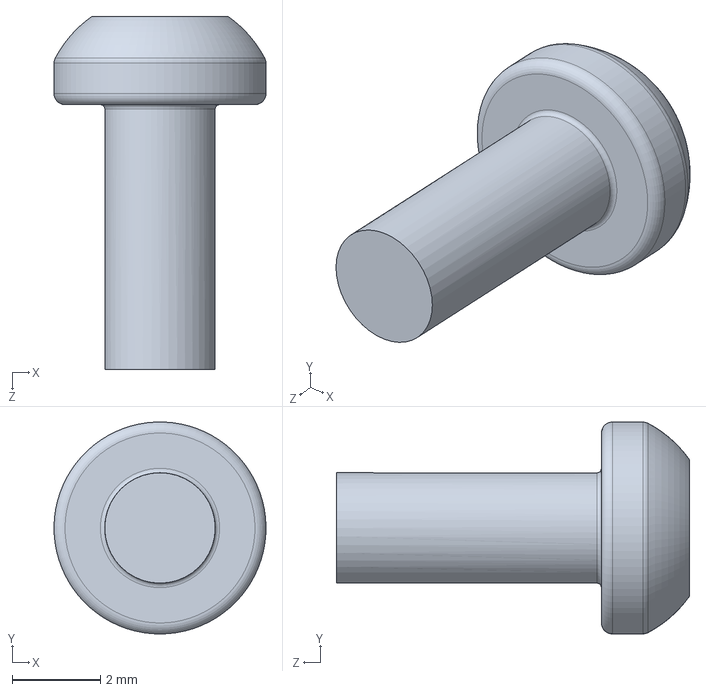
[picture p65: CAD file, 2020-04-01]
file-set-2/Electronic PCBAs/GR106769_CPU_PCBA/3D_Model/Vis KA22x5 hexalobes.SLDPRT
4.80 x 4.80 x 8.00 mm
