L0op/medtronic-pb560/file-set-2/Mechanical Part Drawings/2967200/sangle bandoulliere droite.SLDPRT

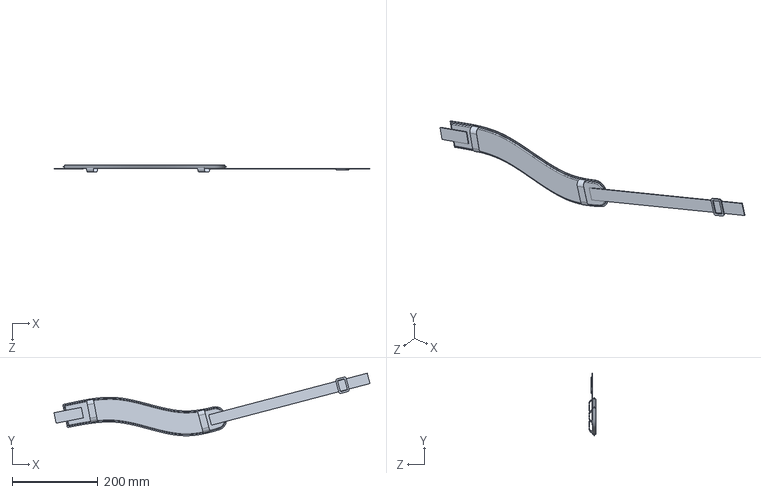
[picture p66: CAD file, 2020-04-01]
file-set-2/Mechanical Part Drawings/2967200/sangle bandoulliere droite.SLDPRT
737.2 x 146.2 x 16.2 mm
