L0op/medtronic-pb560/file-set-2/3D CAD Models/Back End Cap.SLDPRT

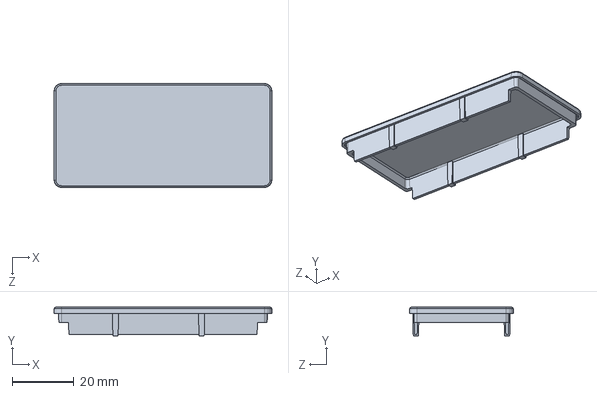
[picture p67: CAD file, 2020-04-01]
file-set-2/3D CAD Models/Back End Cap.SLDPRT
70.9 x 9.30 x 33.9 mm
