L0op/medtronic-pb560/file-set-2/Electronic PCBAs/10106052_PowerPack_PCBA/PCBA/MOLEX 43650-0229.SLDPRT

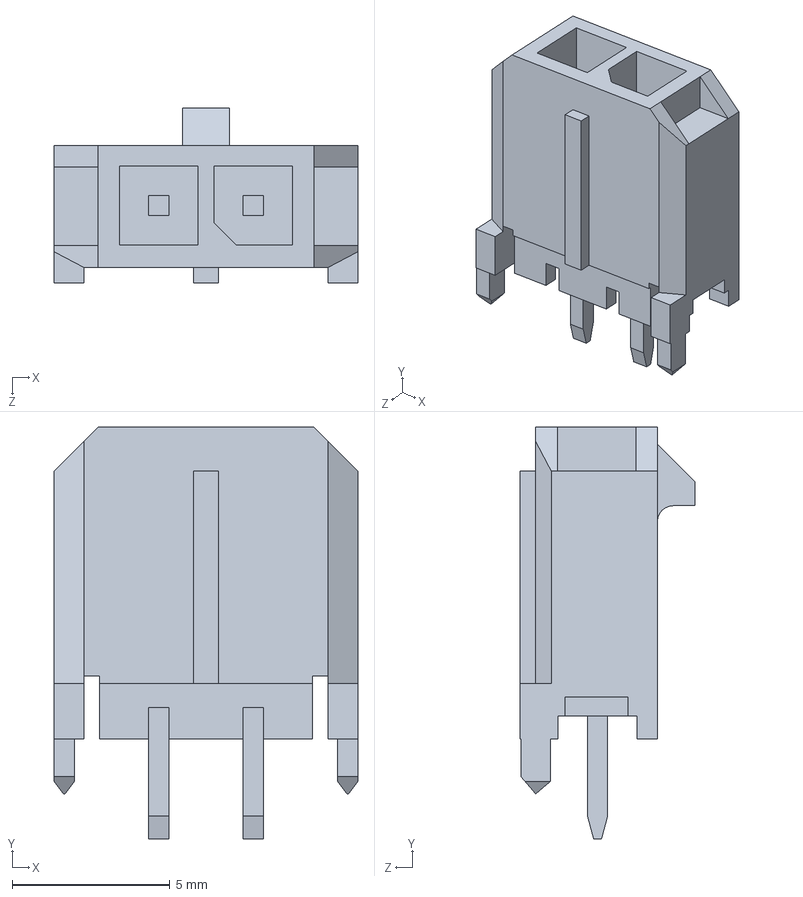
[picture p69: CAD file, 2020-04-01]
file-set-2/Electronic PCBAs/10106052_PowerPack_PCBA/PCBA/MOLEX 43650-0229.SLDPRT
9.65 x 13.1 x 5.57 mm
