L0op/medtronic-pb560/file-set-2/Electronic PCBAs/10096315_Blower_Driver_PCBA/3D_Model/cable nappe 10 fils.SLDPRT

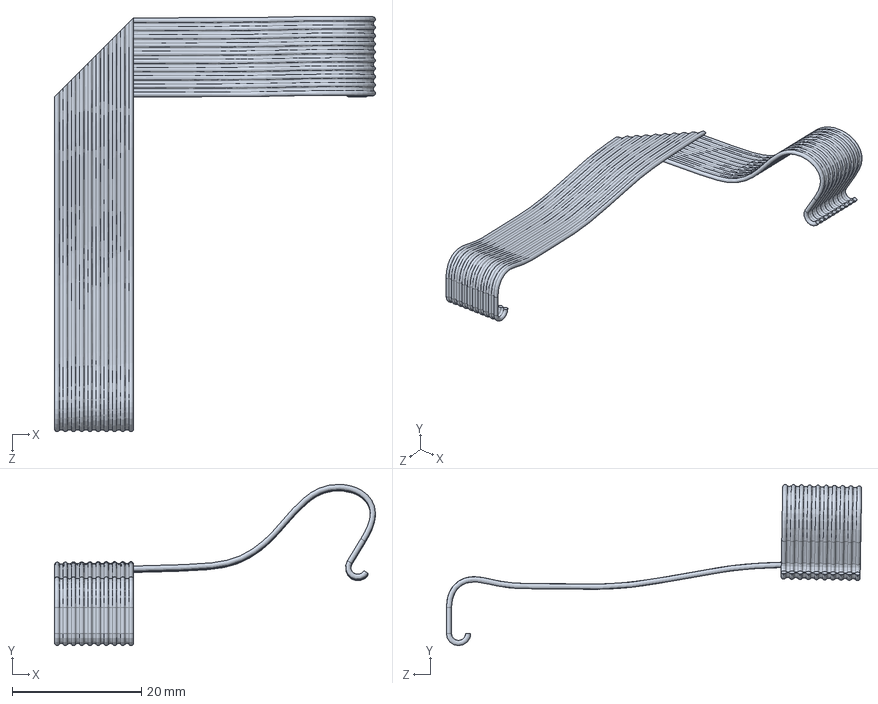
[picture p71: CAD file, 2020-04-01]
file-set-2/Electronic PCBAs/10096315_Blower_Driver_PCBA/3D_Model/cable nappe 10 fils.SLDPRT
49.7 x 24.9 x 64.3 mm
