L0op/medtronic-pb560/file-set-2/Electronic PCBAs/GR106769_CPU_PCBA/3D_Model/AFFICHEUR TWIN.SLDPRT

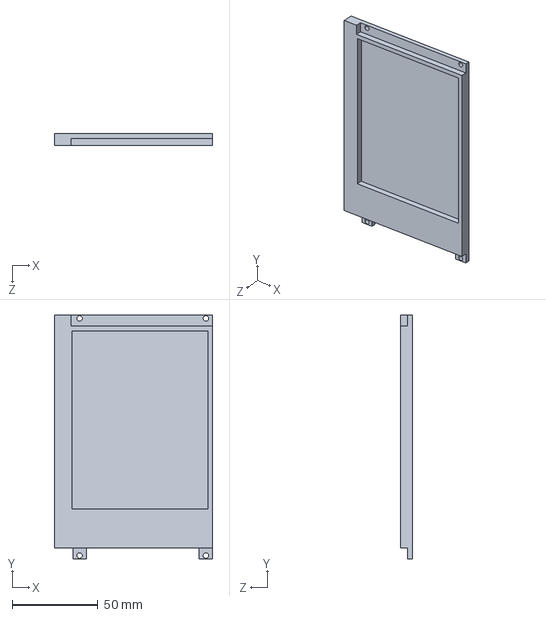
[picture p72: CAD file, 2020-04-01]
file-set-2/Electronic PCBAs/GR106769_CPU_PCBA/3D_Model/AFFICHEUR TWIN.SLDPRT
92.6 x 142.6 x 7.00 mm
