L0op/medtronic-pb560/file-set-2/Electronic PCBAs/10096315_Blower_Driver_PCBA/3D_Model/7810-0000xxSE.SLDPRT

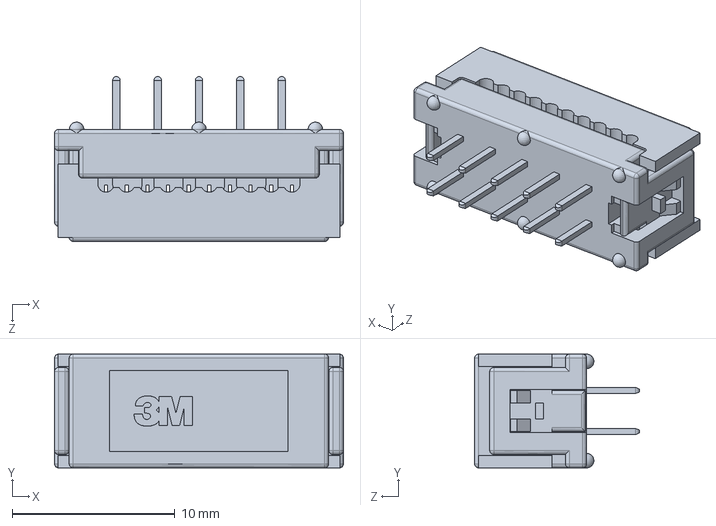
[picture p73: CAD file, 2020-04-01]
file-set-2/Electronic PCBAs/10096315_Blower_Driver_PCBA/3D_Model/7810-0000xxSE.SLDPRT
17.8 x 7.00 x 10.1 mm
