L0op/medtronic-pb560/file-set-2/Electronic PCBAs/GR106769_CPU_PCBA/3D_Model/Rondelle plate - ZU  3 x 6 EP 0.8.sldprt

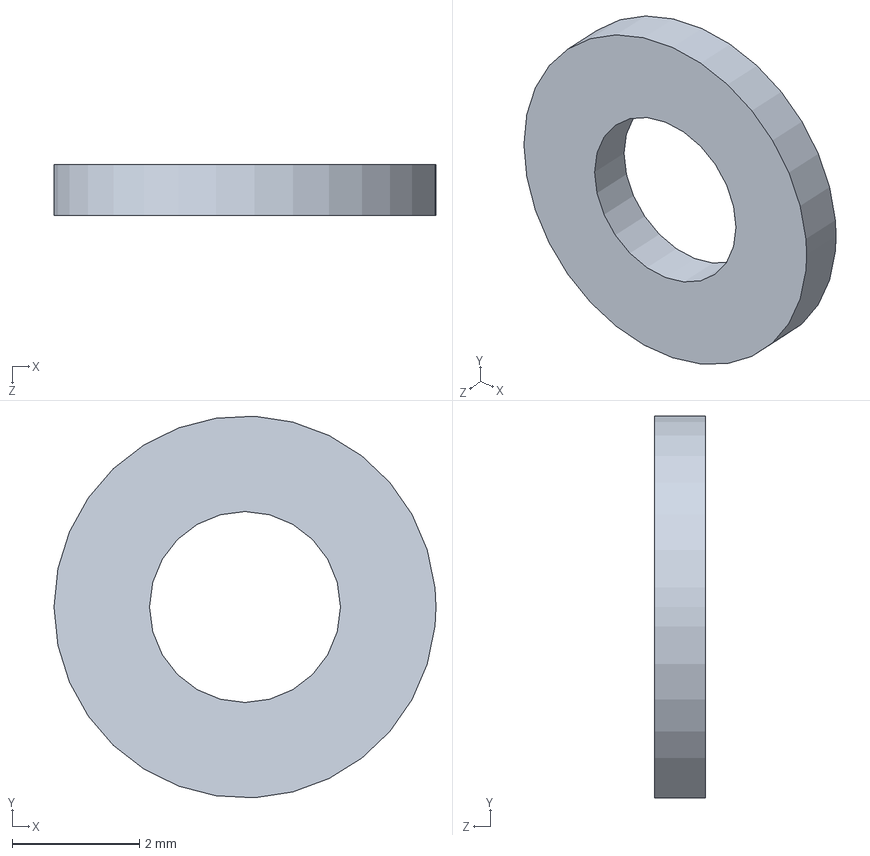
[picture p74: CAD file, 2020-04-01]
file-set-2/Electronic PCBAs/GR106769_CPU_PCBA/3D_Model/Rondelle plate - ZU 3 x 6 EP 0.8.sldprt
6.00 x 5.99 x 0.8 mm
