L0op/medtronic-pb560/file-set-2/Electronic PCBAs/10096315_Blower_Driver_PCBA/3D_Model/22-05-7028.SLDPRT

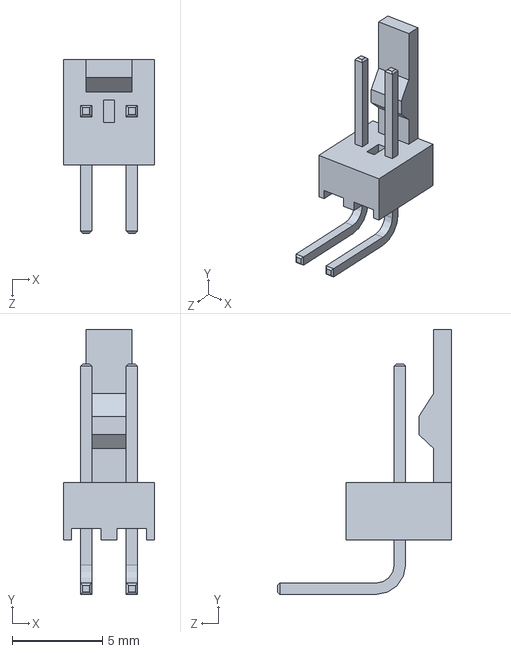
[picture p76: CAD file, 2020-04-01]
file-set-2/Electronic PCBAs/10096315_Blower_Driver_PCBA/3D_Model/22-05-7028.SLDPRT
5.08 x 14.7 x 9.65 mm
