L0op/medtronic-pb560/file-set-2/Electronic PCBAs/10096315_Blower_Driver_PCBA/3D_Model/22-05-7098.SLDPRT

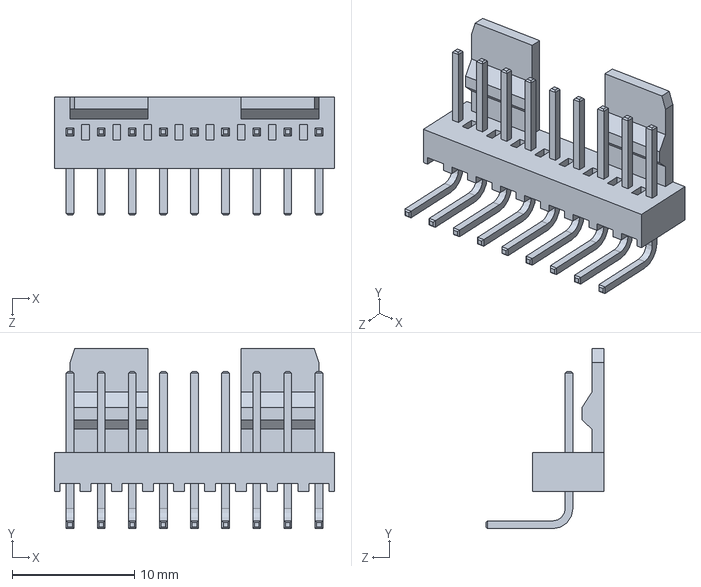
[picture p80: CAD file, 2020-04-01]
file-set-2/Electronic PCBAs/10096315_Blower_Driver_PCBA/3D_Model/22-05-7098.SLDPRT
22.9 x 14.7 x 9.65 mm
