L0op/medtronic-pb560/file-set-2/Electronic PCBAs/GR106769_CPU_PCBA/3D_Model/capot 3 capteurs P phase 2.SLDPRT

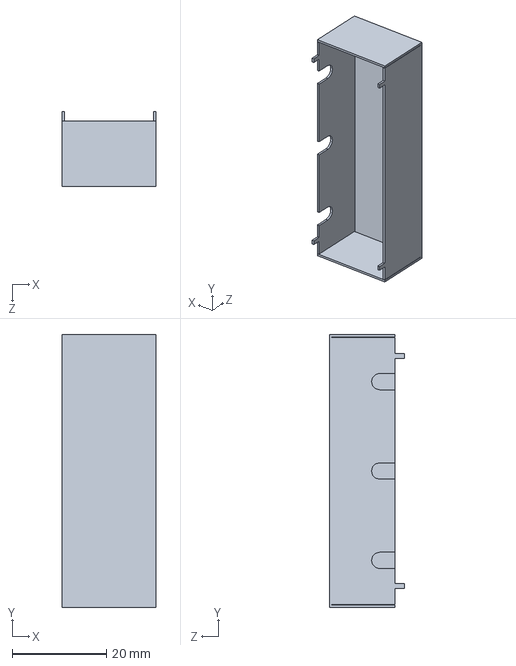
[picture p81: CAD file, 2020-04-01]
file-set-2/Electronic PCBAs/GR106769_CPU_PCBA/3D_Model/capot 3 capteurs P phase 2.SLDPRT
19.9 x 58.0 x 16.0 mm
