L0op/medtronic-pb560/file-set-2/Electronic PCBAs/GR106769_CPU_PCBA/3D_Model/entretoise hexa  m3x12.SLDPRT

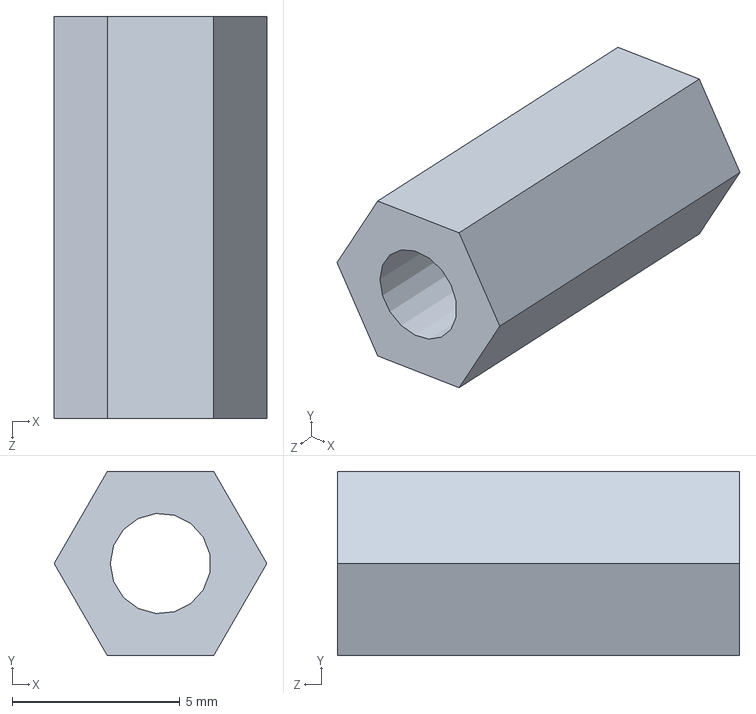
[picture p83: CAD file, 2020-04-01]
file-set-2/Electronic PCBAs/GR106769_CPU_PCBA/3D_Model/entretoise hexa m3x12.SLDPRT
6.35 x 5.50 x 12.0 mm
