L0op/medtronic-pb560/file-set-2/Electronic PCBAs/GR106769_CPU_PCBA/3D_Model/condensateur C88.SLDPRT

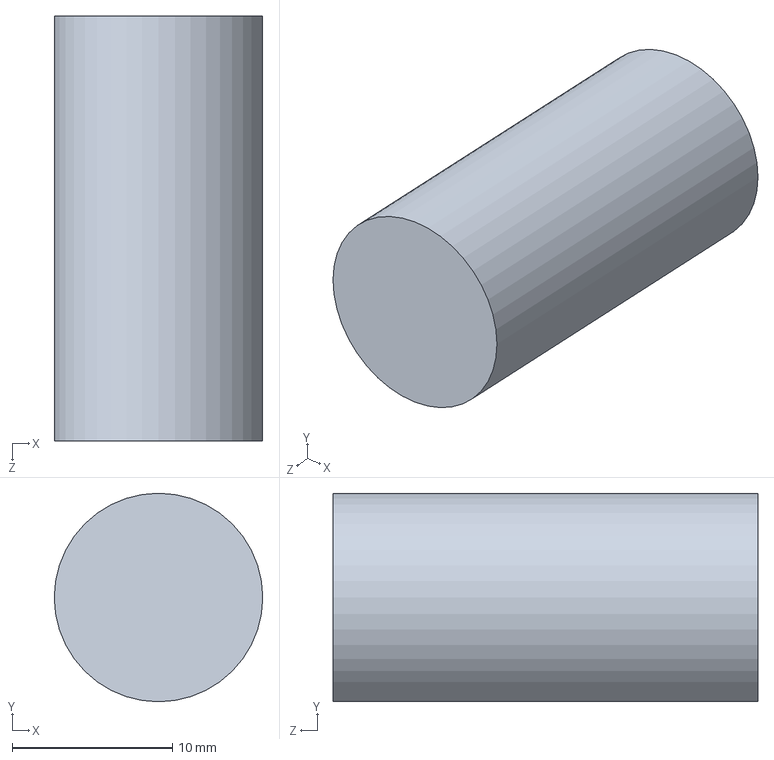
[picture p84: CAD file, 2020-04-01]
file-set-2/Electronic PCBAs/GR106769_CPU_PCBA/3D_Model/condensateur C88.SLDPRT
13.0 x 13.0 x 26.5 mm
