L0op/medtronic-pb560/file-set-2/Electronic PCBAs/GR106769_CPU_PCBA/3D_Model/39-28-5264.SLDPRT

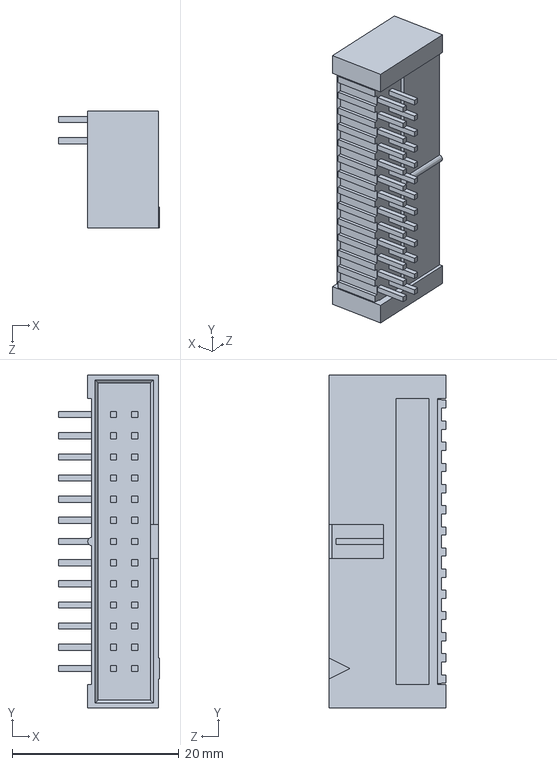
[picture p86: CAD file, 2020-04-01]
file-set-2/Electronic PCBAs/GR106769_CPU_PCBA/3D_Model/39-28-5264.SLDPRT
12.1 x 40.0 x 14.0 mm
