L0op/medtronic-pb560/file-set-2/3D CAD Models/connect molex 22-01-2025.SLDPRT

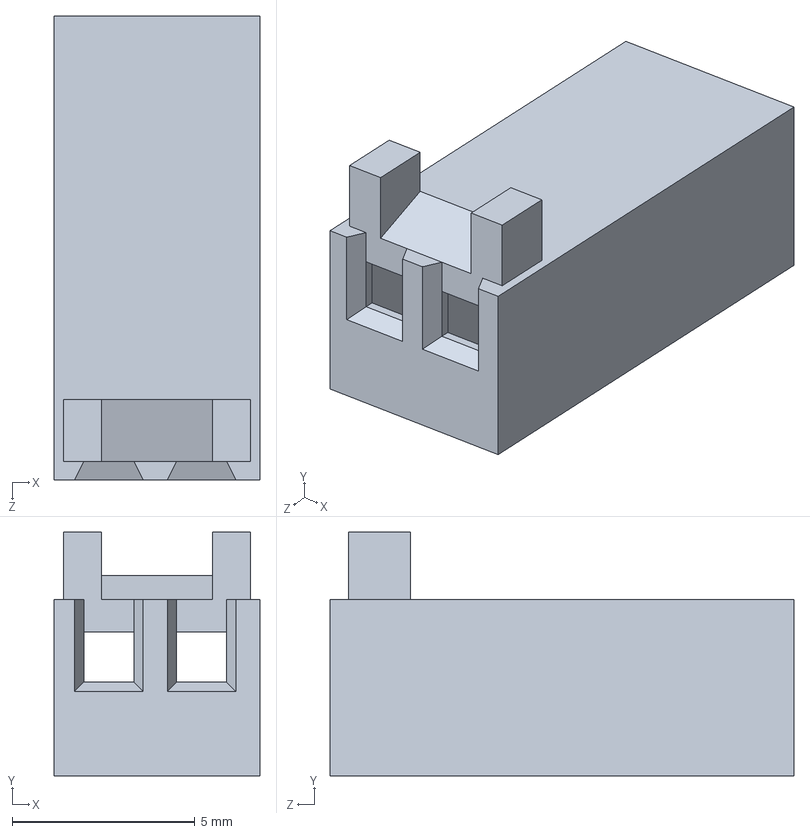
[picture p87: CAD file, 2020-04-01]
file-set-2/3D CAD Models/connect molex 22-01-2025.SLDPRT
5.64 x 6.68 x 12.7 mm
