L0op/medtronic-pb560/file-set-2/3D CAD Models/transfo.SLDPRT

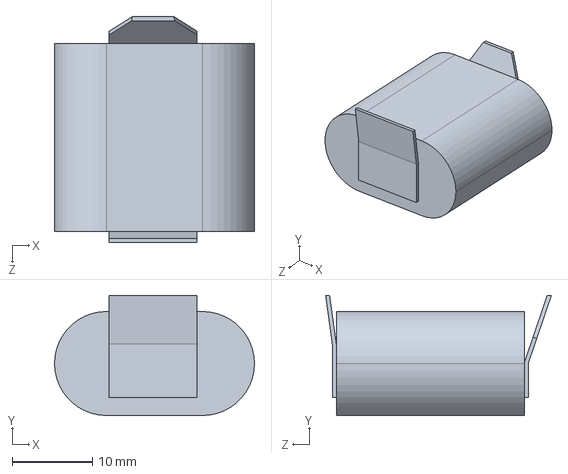
[picture p90: CAD file, 2020-04-01]
file-set-2/3D CAD Models/transfo.SLDPRT
25.0 x 15.0 x 28.2 mm
