L0op/medtronic-pb560/file-set-2/Electronic PCBAs/GR106769_CPU_PCBA/3D_Model/embase cpu.SLDPRT

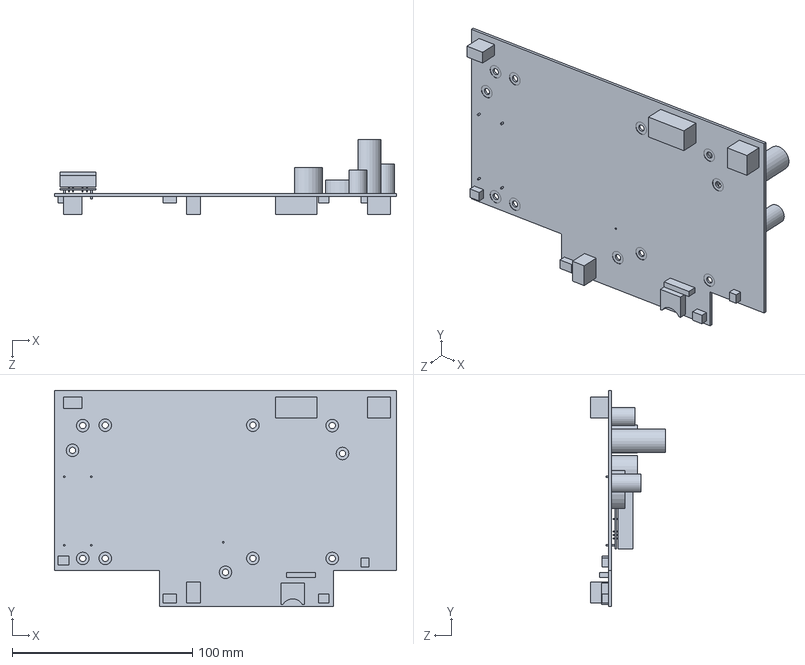
[picture p91: CAD file, 2020-04-01]
file-set-2/Electronic PCBAs/GR106769_CPU_PCBA/3D_Model/embase cpu.SLDPRT
190.0 x 120.0 x 41.5 mm
