L0op/medtronic-pb560/file-set-2/3D CAD Models/tuyau pression vanne pilot1.6x4.8.SLDPRT

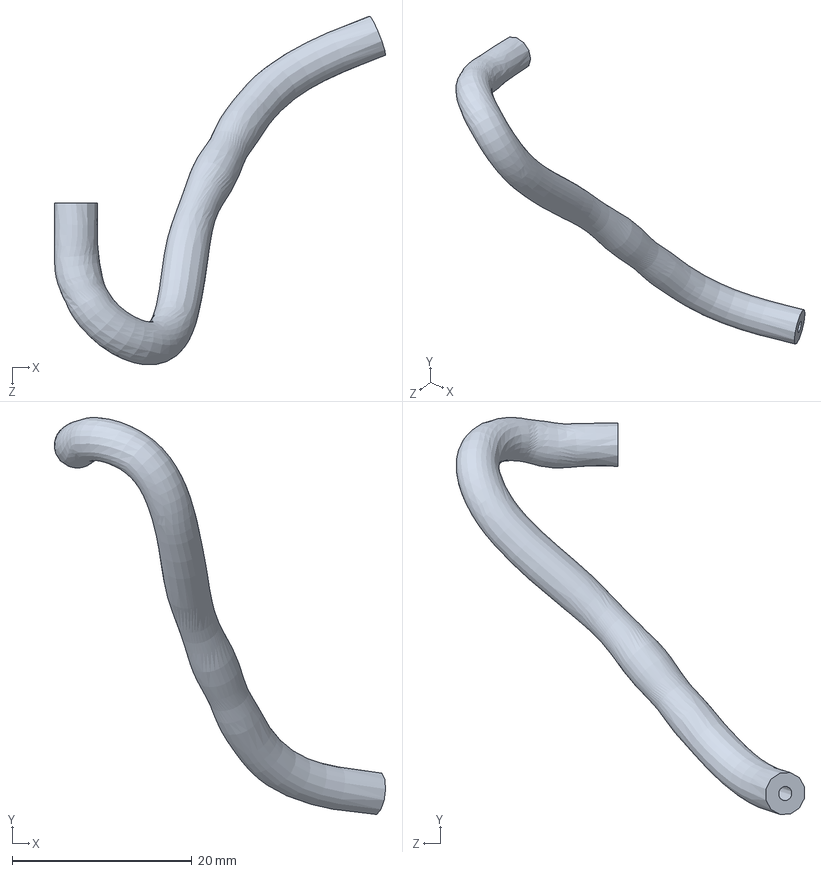
[picture p92: CAD file, 2020-04-01]
file-set-2/3D CAD Models/tuyau pression vanne pilot1.6x4.8.SLDPRT
36.8 x 44.2 x 38.7 mm
