L0op/medtronic-pb560/file-set-2/3D CAD Models/Batt PCB.SLDPRT

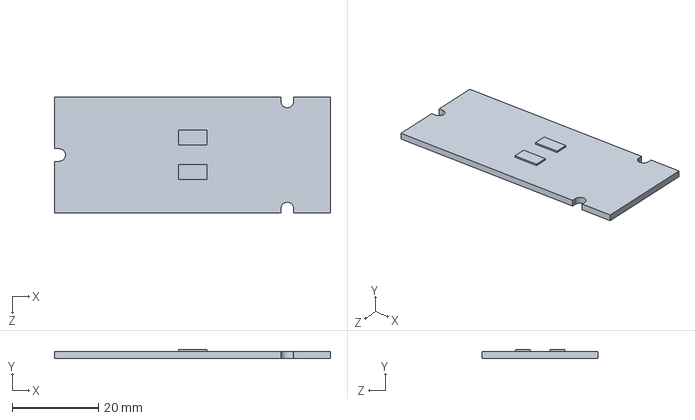
[picture p93: CAD file, 2020-04-01]
file-set-2/3D CAD Models/Batt PCB.SLDPRT
63.9 x 2.00 x 26.9 mm
