L0op/medtronic-pb560/file-set-2/3D CAD Models/tuyau sortie vanne pilot1.6x4.8.SLDPRT

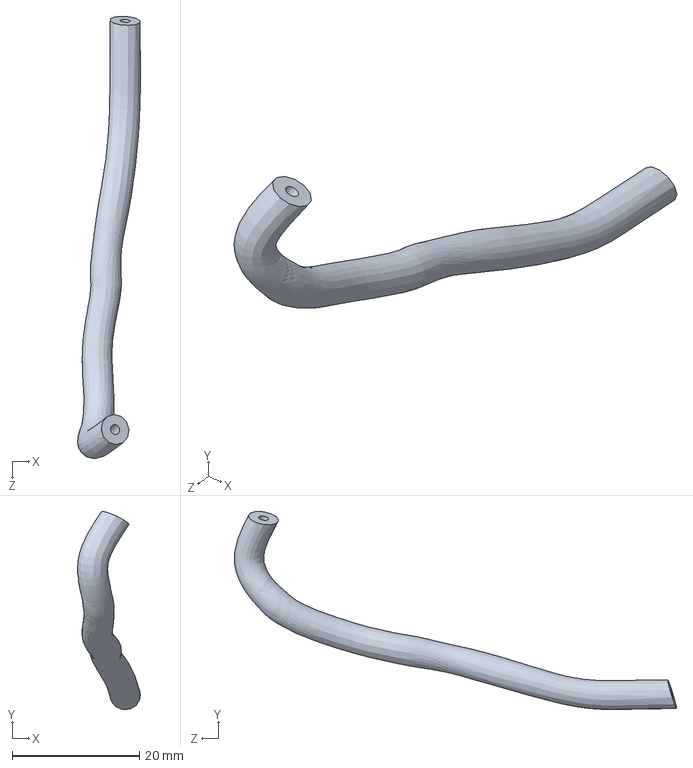
[picture p94: CAD file, 2020-04-01]
file-set-2/3D CAD Models/tuyau sortie vanne pilot1.6x4.8.SLDPRT
9.88 x 31.1 x 69.5 mm
