L0op/medtronic-pb560/file-set-2/3D CAD Models/connect molex 22-01-2087.SLDPRT

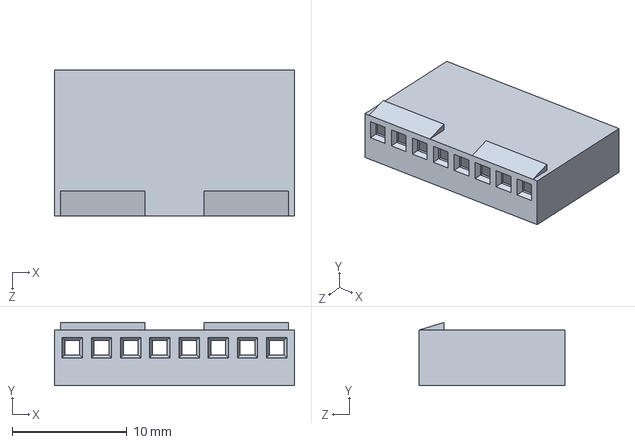
[picture p95: CAD file, 2020-04-01]
file-set-2/3D CAD Models/connect molex 22-01-2087.SLDPRT
20.9 x 5.49 x 12.7 mm
