L0op/medtronic-pb560/file-set-2/3D CAD Models/I0 178 Entretoise AR Legendair.SLDPRT

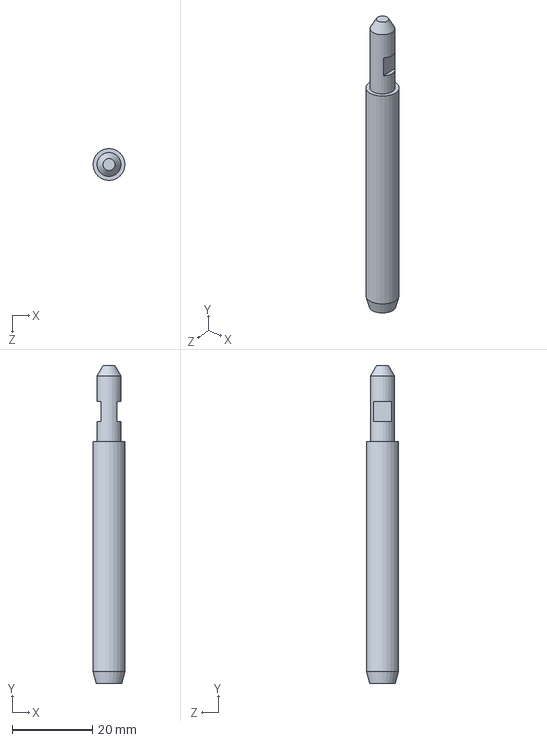
[picture p96: CAD file, 2020-04-01]
file-set-2/3D CAD Models/I0 178 Entretoise AR Legendair.SLDPRT
8.00 x 79.5 x 8.00 mm
