L0op/medtronic-pb560/file-set-2/3D CAD Models/3M 4032 x30mm.SLDPRT

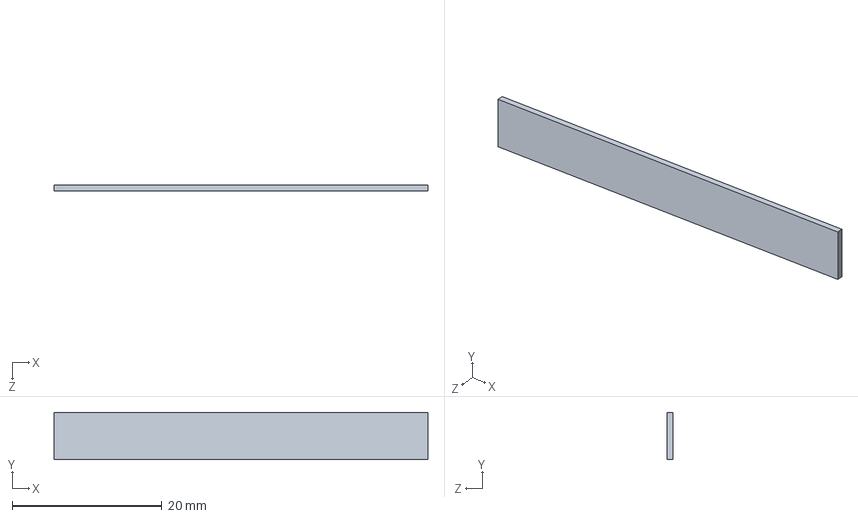
[picture p97: CAD file, 2020-04-01]
file-set-2/3D CAD Models/3M 4032 x30mm.SLDPRT
50.0 x 6.35 x 0.8 mm
