L0op/medtronic-pb560/file-set-2/3D CAD Models/Cable tie (ref AML).SLDPRT

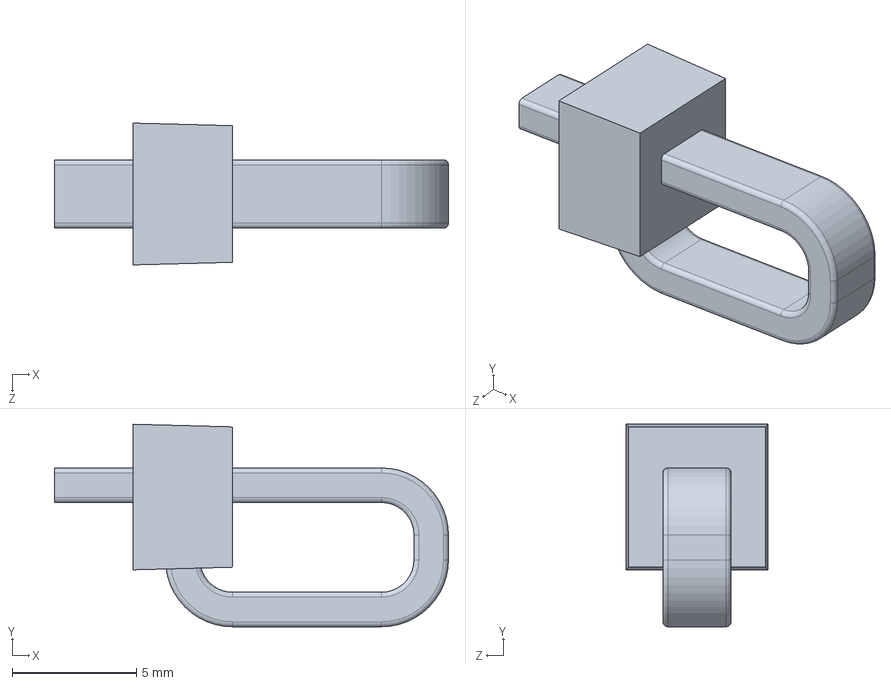
[picture p98: CAD file, 2020-04-01]
file-set-2/3D CAD Models/Cable tie (ref AML).SLDPRT
15.9 x 8.15 x 5.71 mm
