L0op/medtronic-pb560/file-set-2/3D CAD Models/tuyau  droit sortie vanne O2.SLDPRT

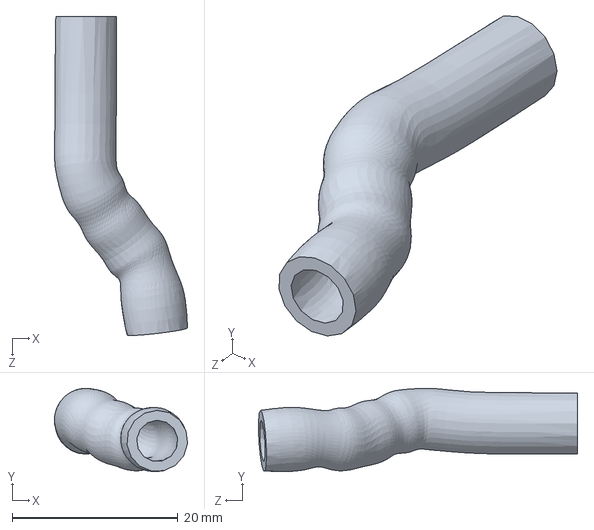
[picture p99: CAD file, 2020-04-01]
file-set-2/3D CAD Models/tuyau droit sortie vanne O2.SLDPRT
16.1 x 10.0 x 38.5 mm
