L0op/medtronic-pb560/file-set-2/3D CAD Models/I0 179 Entretoise Mediane Legendair.SLDPRT

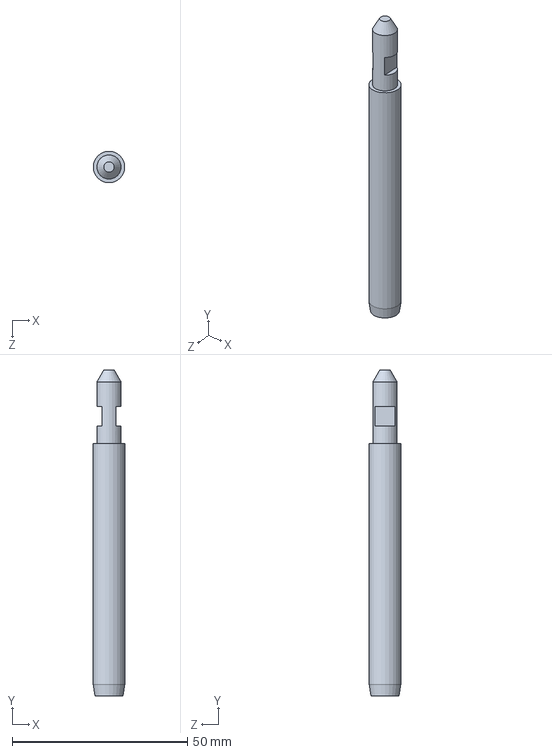
[picture p100: CAD file, 2020-04-01]
file-set-2/3D CAD Models/I0 179 Entretoise Mediane Legendair.SLDPRT
9.00 x 93.0 x 9.00 mm
