L0op/medtronic-pb560/file-set-2/3D CAD Models/Batt Contacts tab.SLDPRT

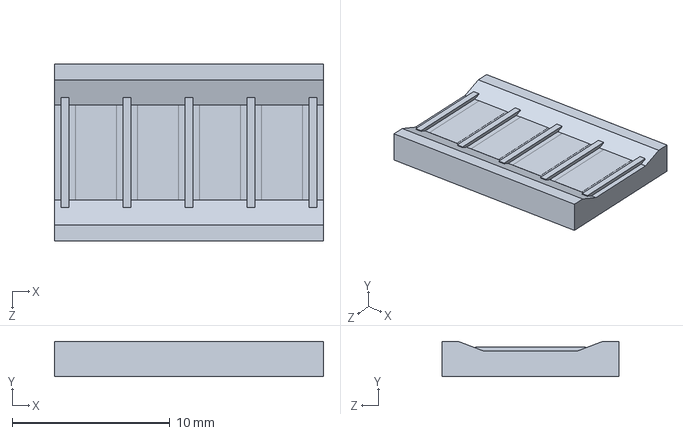
[picture p101: CAD file, 2020-04-01]
file-set-2/3D CAD Models/Batt Contacts tab.SLDPRT
17.0 x 2.25 x 11.2 mm
