L0op/medtronic-pb560/file-set-2/3D CAD Models/Extruded housing.SLDPRT

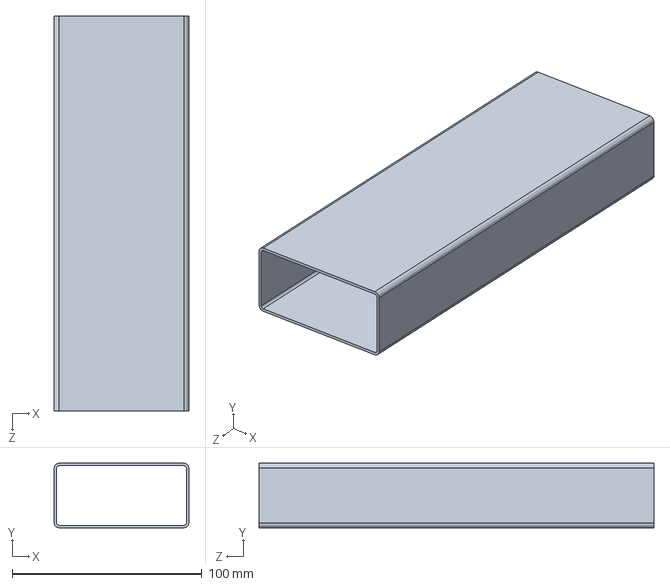
[picture p102: CAD file, 2020-04-01]
file-set-2/3D CAD Models/Extruded housing.SLDPRT
71.0 x 34.0 x 208.0 mm
