L0op/medtronic-pb560/file-set-2/3D CAD Models/etiq reperage vanne O2.SLDPRT

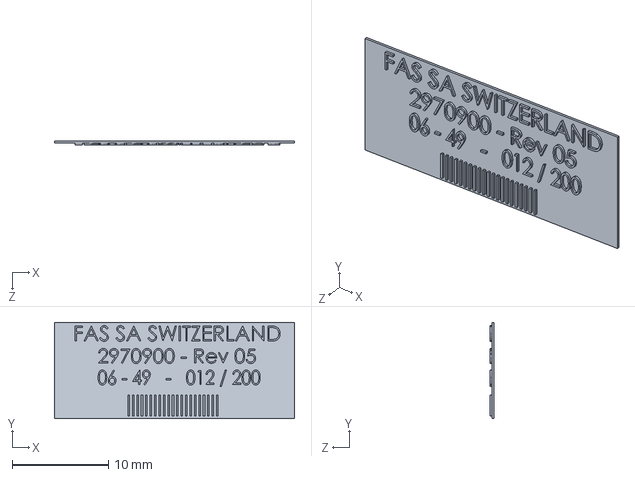
[picture p103: CAD file, 2020-04-01]
file-set-2/3D CAD Models/etiq reperage vanne O2.SLDPRT
25.0 x 10.0 x 0.4 mm
