L0op/medtronic-pb560/file-set-2/3D CAD Models/1mm bumper.SLDPRT

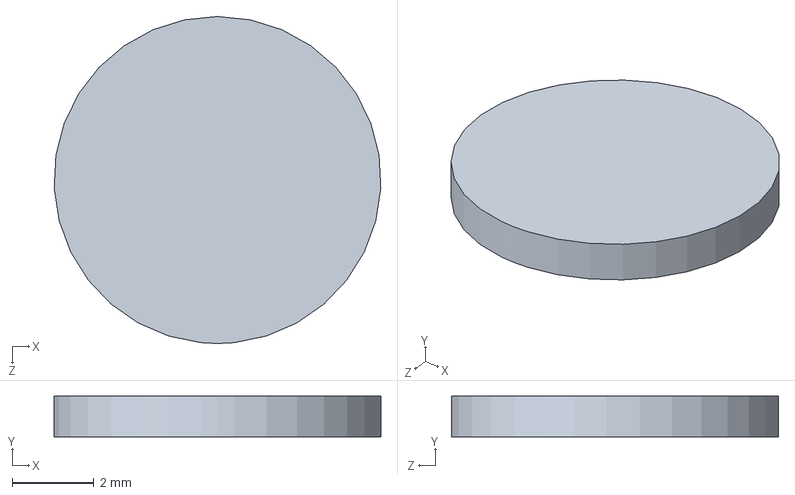
[picture p104: CAD file, 2020-04-01]
file-set-2/3D CAD Models/1mm bumper.SLDPRT
7.99 x 1.00 x 8.00 mm
