L0op/medtronic-pb560/file-set-2/3D CAD Models/capteur debit.SLDPRT

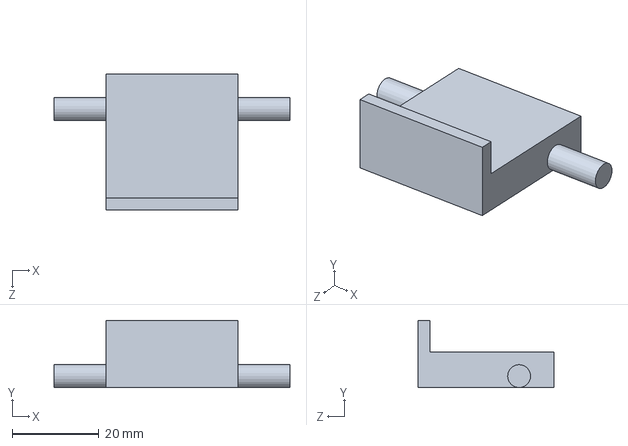
[picture p105: CAD file, 2020-04-01]
file-set-2/3D CAD Models/capteur debit.SLDPRT
54.5 x 15.5 x 31.5 mm
