L0op/medtronic-pb560/file-set-1/Manufacturing Documents/PB560 - Quality Process Flow - Manufacturing Procedures/10095162H00_PB560 ASSEMBLY PROCEDURE 2.pdf

P/N: | 10095162
Rev: | H
Title: | PB560 Assembly procedure 2
INSTRUCTIONS | Page 1 of 19
Template # 10034696 | Rev B

Appendices to this Procedure
P/N | Description | Rev.
N/A | N/A | N/A

DOCUMENTATION ASSOCIATED TO THIS PROCEDURE
10038461 PB560 DHR
REV | ECO | PREPARED BY | APPROVED BY | DATE | SUMMARY
N/A | N/A | N/A | N/A | N/A | Refer to Agile, Rev C for previous revision history.
D | ECO-R230620 | | Refer to Agile | Refer to Agile | Update procedure to reflect changes to PHR 10038461
E | ECO-R242465 | | Refer to Agile | Refer to Agile | Update procedure to re-arrange the Assembly sequence outlined in section ‘Expiratory Conical Block and Support’
F | ECO-R259799 | | Refer to Agile | Refer to Agile | Add instruction to record Assembly Part Revisions
G | EC048873 | | Refer to Agile | Refer to Agile | Removing G-AMFG-1771-00 from references and adding 10021625, Tube Cutting .Removing decimal point from balloon numbers.
H | EC114172 | | Refer to Agile | Refer to Agile | Add picture of new blower label which has scannable barcode. Add instruction to record blower lot code or serial number.

Title: | PB560 Assembly procedure 2
INSTRUCTIONS | Page 2 of 19

### 1. PURPOSE

This assembly instruction details the steps required to assemble the PB560.

### 2. SCOPE

This procedure covers the PB560 ventilator product

### 3. DEFINITIONS

DHR – Device History Record
S/N – Serial Number
OP - Operation

### 4. REFERENCES

10038461 | PB560 DHR
10095162 | PB560 Assembly procedure 2
10095163 | PB560 Assembly procedure 3
G-QAM001 | Quality Manual
10021625 | Tube Cutting – PB540/PB560/PB520
10009491 | Mfg. Guidelines to Completion of Records
10021626 | LOG - PB540/PB560/PB520 Tube Cutting
10021524 | Preventative Maintenance PB540 / PB560 / PB520
G-AMFG-1814-00 | Cosmetic Criteria, MONITORS / PB540 / PB560 / PB520
G-AMFG-1013-00 | MRB Documentation
G-AMFG-2733-00 | PB540 / PB560 / PB520 DHR & S/N Printing Procedure
G-AMFG-1817-00 | Generic line clearance procedure
10037309 | PB520/PB540/PB560 line clearance procedure
10039893 | PB520/PB540/PB560 Line Clearance LOG
10021526 | PB520/PB540/PB560 lot code and serial number assignment
10039975 | PB560 child serial number assignment log

### 5. GENERAL REQUIREMENTS

- Ensure all relevant materials, tools, fixtures & jigs are available at the work station before commencing assembly/ manufacture.

DHR Notes:

- When completing PB560 DHR’s – record all entries / data / dates per Galway Mfg. Guidelines for Completion of Records 10009491.
- When printing the DHR: ensure all pages are double sided, stapled at the top corner & all pages of DHR are present. Note: The manufacturing assembly sequence of the unit may alter/vary to accommodate manufacturing capability
- Record any components used for FRU in FRU Requirements section of DHR.

Title: | PB560 Assembly procedure 2
INSTRUCTIONS | Page 3 of 19

General Notes:

- Before using any calibrated equipment, make sure that the calibration data (on calibration label) has not expired and there is no obvious damage to the equipment.
- If a torque tool is dropped on the floor during assembly, send for re-calibration.
- When connecting cables to connectors, check that male pins are straight. If not, place board into MRB.
- Torx screwdrivers to be used only for screw removal where required, and starting off / aligning screws into the holes. Do not use screwdrivers to tighten screws (there are specific torques for this)
- Hex wrenches to be used only for nut removal if required. Do not use to tighten nuts (there are specific calibrated angle torque tools for this)
- Ensure all tubing is inserted into connections fully
- Ensure all harnesses are fully pushed into mating connectors
- Note: Paint work can be scratched with sharp objects. To avoid scratching, ensure the Unit is not kept beside sharp objects. Use ESD safe foam to leave unit on during assembly.
- When printing serial numbers for production, record detail on log 10039975 – PB560 child serial number assignment log.
- When recording the requested component serial/lot numbers on the DHR, please refer to product BOM for corresponding part numbers.
- Note: If rework/repair is completed at any stage where dis-assembly is required, record all details on the last page of the DHR discrepancy log, 10038461. On the new DHR verify that s/ns and labelling revision are still correct, and that the appropriate final assembly checks are completed. If there is not sufficient space on the DHR, add a second DHR to include the additional information.
- Note: If a unit is being reworked / repaired, the battery must be removed to avoid potential shorting of the power supply in case of a screw dropping on the PCBA. Exceptions to this are when only an upper housing is being replaced (no risk screws causing shorts).
- Note: At the start of each week, it is the responsibility of the Line Leader / Production Supervisor to print out a copy of the BOM from Galway BPCS and sign & date it.
- Compare revisions for any changes from previous week’s build.
- Prior to recording revisions on DHR, ensure that they match revisions on printout
- Contact a quality engineer, line supervisor or manufacturing engineer when any discrepancies noted

Traceability:
- All component S/N and Lot Numbers as listed on the DHR LOG 10038461 must be recorded.

Title: | PB560 Assembly procedure 2
INSTRUCTIONS | Page 4 of 19

### 6. PROCEDURE

TUBE CUTTING

1. Cut the tubes (blln # 11, 12 & 13), per below length as per 10021625 & record on log 10021626.
2. Silicone tube (blln#13) is cut to a length of 62mm with a tolerance of +/- 1mm, per page 10021625 Tube Cutting Procedure.
3. Note: It is permissible to complete batch cutting of ref blln#13
4. Ensure all tubes are stored in separate tote bins for each tube length

Materials:

Balloon Number | Part Number | Description | Size | Qty | Size | Qty | Size | Qty | Size | Qty
11 | Refer to BOM | Silicone tubing 3.2x6.4 | 150mm | 2 | 200mm | 2 | 50mm | 1 | 70mm | 1
12 | Refer to BOM | Silicone tubing 1.6x4.8 | 120mm | 1 | | | | | 70mm | 5
13 | Refer to BOM | Silicone tubing diameter 15x21 | 62mm | 1

Title: | PB560 Assembly procedure 2
INSTRUCTIONS | Page 5 of 19
TUBE ASSEMBLY

Materials:
Balloon Number | Part Number | Description | Qty
14 | Refer to BOM | Tee shape connector | 1
15 | Refer to BOM | Straight connector | 1
11 | Refer to BOM | Silicone tubing 3.2 x 6.4 | 1 x 70mm
12 | Refer to BOM | Silicone tubing 1.6x4.8 | 4 x 70mm

Note: Prior to commencing assembly, select the correct length tubing for the below assembly and place on assembly bench. Check each tube end for straightness; reject tubes that are not straight.

1. Assemble the straight and right angled connectors to the tubing as per fig 1 and fig 2.
2. Ensure that the tubes are fully sealing on the connector – see fig 3and 4 for examples of correct and incorrect sealing.
3. Ensure that wider end of connector is connected to the 2969500 tube(blln #11) and the narrower end is connected to the 2969600 tube (blln #12)
4. Ensure tubing is cut a squarely as possible so as cut tubes can be pushed correctly into place ref fig 5 & 6.

Ensure that wider end of connector is connected to the 2969500 tube and the narrower end is
connected to the 2969600 tube | Fig 1

Fig 2

Title: | PB560 Assembly procedure 2
INSTRUCTIONS | Page 6 of 19

Note : Ensure tubing is cut a squarely as possible so as cut tubes can be pushed correctly into place ref fig 5 & 6.

## √ Correct

Fig 4

Fig 6

√ C | X Incorrect orrect

## X Incorrect

Title: | PB560 Assembly procedure 2
INSTRUCTIONS | Page 7 of 19
PREPARATION OF THE INSPIRATORY CONICAL BLOCK

Materials:
Balloon Number | Part Number | Description | Qty
21 | Refer to BOM | Inspiratory Conical Fitting | 1
22 | Refer to BOM | Inspiratory Label | 1
23 | Refer to BOM | Label, Exhal. Valve, Prox Pressure, PB560 | 1
14/12 | Refer to BOM | Tee shape connector with tubing | 1
11 | Refer to BOM | Silicone tubing 32x64 | 1 x 200mm 1 x 150mm
12 | Refer to BOM | Silicone tubing 16x48 | 1 x 70mm 1 x 120mm
24 | Refer to BOM | Internal FIO2 Cable | 1
724 | Refer to BOM | Wire Ferrite REF: 74271142 | 1
725 | Refer to BOM | Double Sided Tape Adhesive 0.01M | A/R

Equipment:
- Straight tweezers
- Torque driver 4.4 in-lbs
- 10mm socket 10038462
- Inspiratory Block Labelling Fixture 10031632
- Isopropyl Alcohol - 901048
- Kim wipes - 901731

Note: Prior to commencing assembly, select the correct length tubing for the below assembly and place on assembly bench. Check each tube end for straightness; reject tubes which are not straight.

Process

1. Inspect the Inspiratory Conical Fitting for flash and blow out with air-gun. If any flash noted, contact Quality or Manufacturing Engineer.
2. Clean the Inspiratory Conical Fitting, fig 1 with alcohol and kimwipes (around the label application area).
3. Record the revision of the labels (blln #22 & #23) (this will either be on the label or on the label waste) on the DHR log P/N 10038461. Each individual label must be checked for revision.
4. Remove outer film from labels (blln #22 & #23) prior to affixing onto Inspiratory Conical Block.

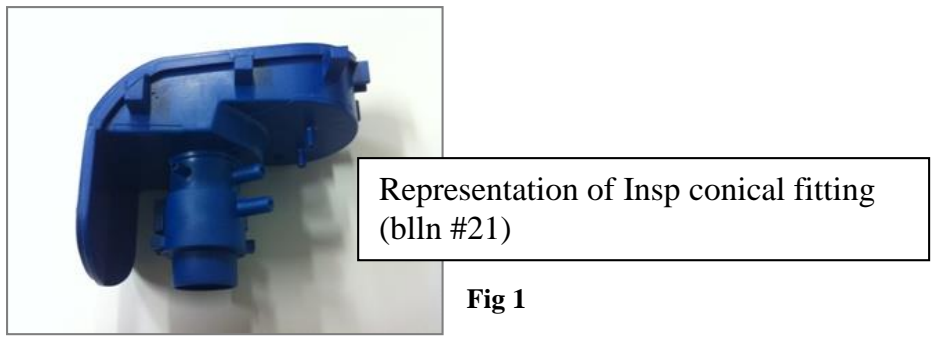
[picture p138: figure]
Fig 1; Representation of Insp conical fitting (blln #21)
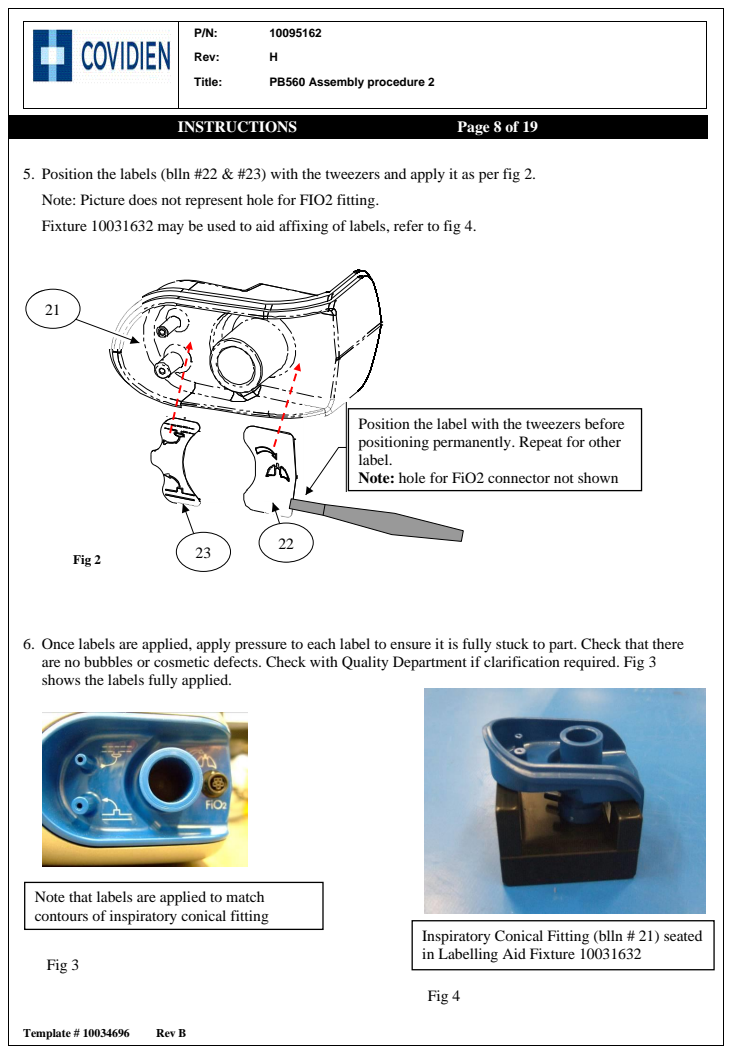
[picture p139: page 8]
Title:; PB560 Assembly procedure 2; INSTRUCTIONS; Page 8 of 19; Fig 4; Fig 3; Fig 2

5. Position the labels (blln #22 & #23) with the tweezers and apply it as per fig 2.
Note: Picture does not represent hole for FIO2 fitting.
Fixture 10031632 may be used to aid affixing of labels, refer to fig 4.

Positionner l’étiquette avec la
Position the label with the tweezers before
pince brucelles avant son collage
positioning permanently. Repeat for other
définitif. Répéter l’oppération pour
label.
l’autre étiquette.
Note: hole for FiO2 connector not shown

6. Once labels are applied, apply pressure to each label to ensure it is fully stuck to part. Check that there
are no bubbles or cosmetic defects. Check with Quality Department if clarification required. Fig 3
shows the labels fully applied.

Note that labels are applied to match
contours of inspiratory conical fitting

Inspiratory Conical Fitting (blln # 21) seated
in Labelling Aid Fixture 10031632

Title: | PB560 Assembly procedure 2
INSTRUCTIONS | Page 9 of 19
7. If it is fitted, remove the Hex nut from the Internal FIO2 Cable Assy (blln #24) taking care not to damage the J5 connector when removing and assemble to the Inspiratory Conical Fitting as shown in figure 5 and 6. Take care not to damage the J5 connector when refitting the hex nut.

Note: If a serrated washer is fitted this is not used as part of this assembly.

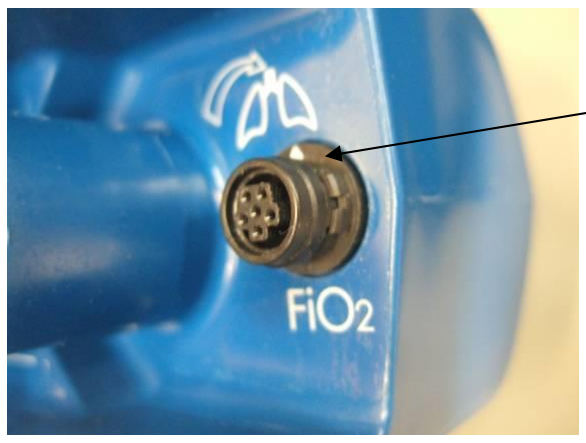
[picture p140: figure]

8. Refit the hex nut hand tighten as shown in figure 6.

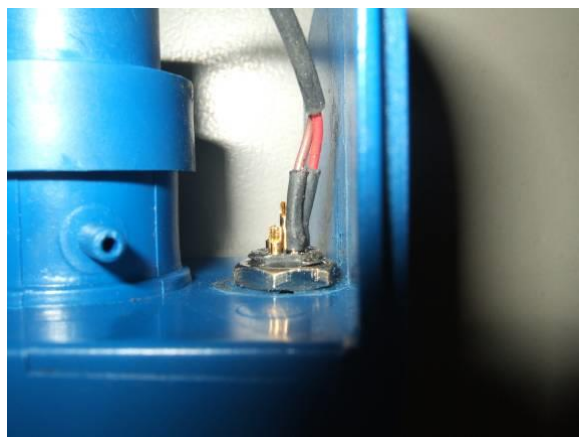
[picture p141: figure]

9. Using FiO2 socket (10038462) torque the nut to 4.4in Ibs as shown in fig 7

Fig 5

Fig 6

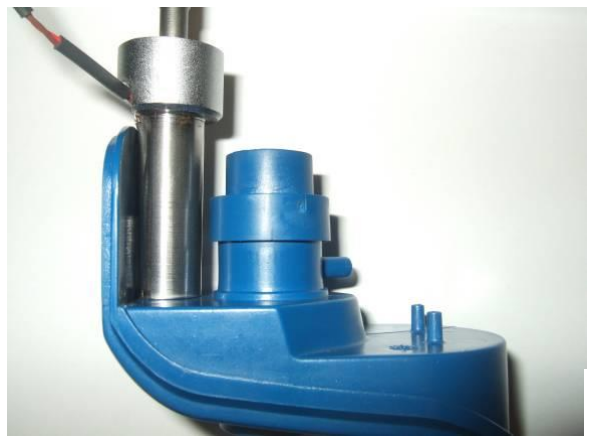
[picture p142: figure]

Fig 7

NOTE: When tightening the FiO2 nut ensure the tool is not pushing against the Inspiratory Conical fitting.
Care must be taken that the tool is positioned correctly when tightening this nut.

Arrow head

NOTE: Note: The connector is keyed and must be orientated with the white arrow head pointing away from the FiO2 symbol.

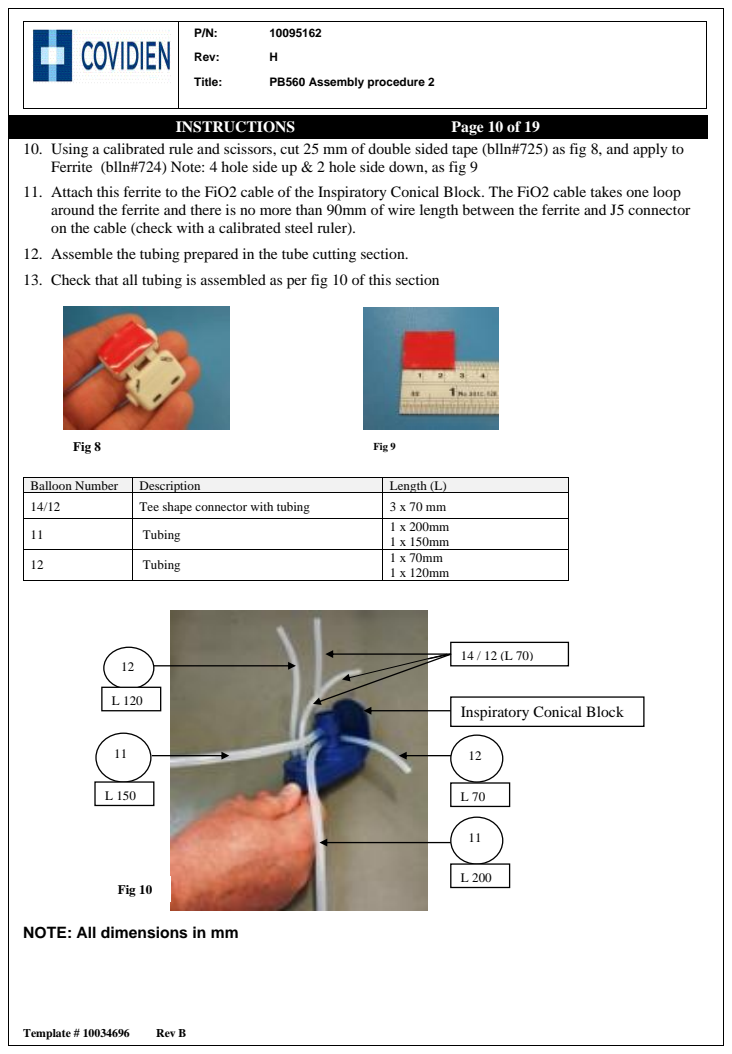
[picture p143: page 10]
Title:; PB560 Assembly procedure 2; INSTRUCTIONS; Page 10 of 19; Fig 8; Fig 9; Fig 10

10. Using a calibrated rule and scissors, cut 25 mm of double sided tape (blln#725) as fig 8, and apply to
Ferrite (blln#724) Note: 4 hole side up & 2 hole side down, as fig 9
11. Attach this ferrite to the FiO2 cable of the Inspiratory Conical Block. The FiO2 cable takes one loop
around the ferrite and there is no more than 90mm of wire length between the ferrite and J5 connector
on the cable (check with a calibrated steel ruler).
12. Assemble the tubing prepared in the tube cutting section.
13. Check that all tubing is assembled as per fig 10 of this section

Balloon Number | Description | Length (L)
14/12 | Tee shape connector with tubing | 3 x 70 mm
11 | Tubing | 1 x 200mm 1 x 150mm

12 | Tubing | 1 x 70mm 1 x 120mm

Inspiratory Conical Block

NOTE: All dimensions in mm

Title: | PB560 Assembly procedure 2
INSTRUCTIONS | Page 11 of 19
EXPIRATORY CONICAL BLOCK AND SUPPORT

Materials:
Balloon Number | Part Number | Description | Qty
31 | Refer to BOM | Expiratory Conical Block | 1
32 | Refer to BOM | Label, Expiratory Single Use, PB560 | 1
33 | Refer to BOM | Expiratory Conical fitting support | 1
34 | Refer to BOM | Bulkhead connector (Baffle conduit fluted) | 2
35 | Refer to BOM | Label, Valve Connection, PB560 | 1
11 | Refer to BOM | Silicone tubing 3.2 x 6.4 | 1 x 200mm 1 x 150mm

Equipment:
Isopropyl Alcohol, 901048
Kim wipes P/N 901731
4.4 in-lbs torque driver.
16mm socket 3834400
Straight tweezers
Note: Prior to commencing assembly, select the correct length tubing for the below assembly, refer to table above and procedure 10021625 and place on assembly bench. Visually check that each tube has been cut square. There should be no gap between the end of the tube and the barb when assembled later in this procedure, fig 7.

Process
1. Clean the Expiratory Block (blln #31) with alcohol and kimwipes around area where labels are being applied. Check for flash and MRB if required.
2. Record the revision of the labels (blln #32 & 35) (this will either be on the label or on the label waste) on the DHR log P/N 10038461. Each individual label must be checked for revision.
3. Remove outer film from labels (blln #32 & #35) prior to affixing onto Expiratory Conical Block.
4. Centre and affix the label (blln #32 and #35) with the tweezers (to avoid finger marks) on the expiratory return. See fig 1and fig 2 of this section.
5. Once applied, apply pressure to label to ensure it is fully stuck to part. Check that there are no bubbles or cosmetic defects. Check with Quality Department if clarification required
Note:
Prior to commencing assembly, select the correct length tubing for the below assembly, ref table above and procedure 10021625 and place on assembly bench. Visually check that each tube has been cut square. There should be no gap between the end of the tube and the barb when assembled later in this procedure ref fig 5.

blln 32

31

blln 35

Fig 1 | Fig 2

Title: | PB560 Assembly procedure 2
INSTRUCTIONS | Page 12 of 19
6. Fit the bulk head connectors (blln # 34) directly into the Expiratory Conical Block (blln # 31), see fig 3 for reference.
7. Assemble both parts of Expiratory Conical support together, see fig 4 for reference. Ensure that the bulkhead connector’s hex head sits correctly in the inset of the Expiratory Conical Fitting Support (blln # 33) - as outlined in fig 5.
8. Fit the 16mm hex socket tool, p/n 3834400 to the 4.4in-lb torque driver.
9. Hand tighten the nuts as outlined in fig 6, using the 16mm hex socket torque (p/n 3834400) to 4.4lbs, ensuring the block is placed on the workbench.
10. Connect the tubing prepared in procedure 10021626, see fig 7.

Note: ensure that the tubing is pushed all the way along the barb section until it is in all the way.

11. Figure 8 shows the diagrammatical assembly

NOTE: All dimensions in mm

### 4.4 in-lbs

Torque

Length
150mm

Fig 7
Length
200mm

Fig 8

Fig 3 | Fig 4 | Fig 5

4.4 in-1bs
Torque

Blln 31

Blln 33 Blln # 34

Fig 6

Title: | PB560 Assembly procedure 2
INSTRUCTIONS | Page 13 of 19
BLOWER HOUSING

Materials

Balloon Number | Part Number | Description | Qty
51 | Refer to BOM | Screw TCBX M3x5 | 4
52 | Refer to BOM | Shielding | 1
53 | Refer to BOM | Blower driver card | 1
54 | Refer to BOM | Hexagonal spacer M3xLength5 | 4
55 | Refer to BOM | Adhesive foam strip,3x20,length 95 +/- 2mm | 2
56 | Refer to BOM | Blower | 1
57 | Refer to BOM | Plastic collar | 1
13 | Refer to BOM | Silicone tubing diameter 15x21 | 0.062
59 | Refer to BOM | Power Supply Blower harness | 1
511 | Refer to BOM | Loctite 243 | A/R
11/15/12 | Refer to BOM | Straight connector with silicon tubing | 1
720 | Refer to BOM | Ty-wrap | 1
111 | Refer to BOM | Zinc-Plated Steel Tcb Screw Hexalobe D3x8 | 1
113 | Refer to BOM | M3 Fender Washer | 1

Equipment:
4.4 in-lb Torque Driver | Torx bit T10
Scissors | Isopropyl Alcohol, 901048
Kim wipes P/N 901731 | 6” or 12 “Calibrated steel ruler
5mm hex socket | 8.9in-lb Hand Torque tool

Process

1. Record Lot number (from | abel Fig 1A) or Serial number from | abel 1B and revision of
the Blower (blln #56) and serial number and revision of the Blower Driver Card (blln #53) on DHR LOG 10038461. Refer to fig 1 and 2 below:

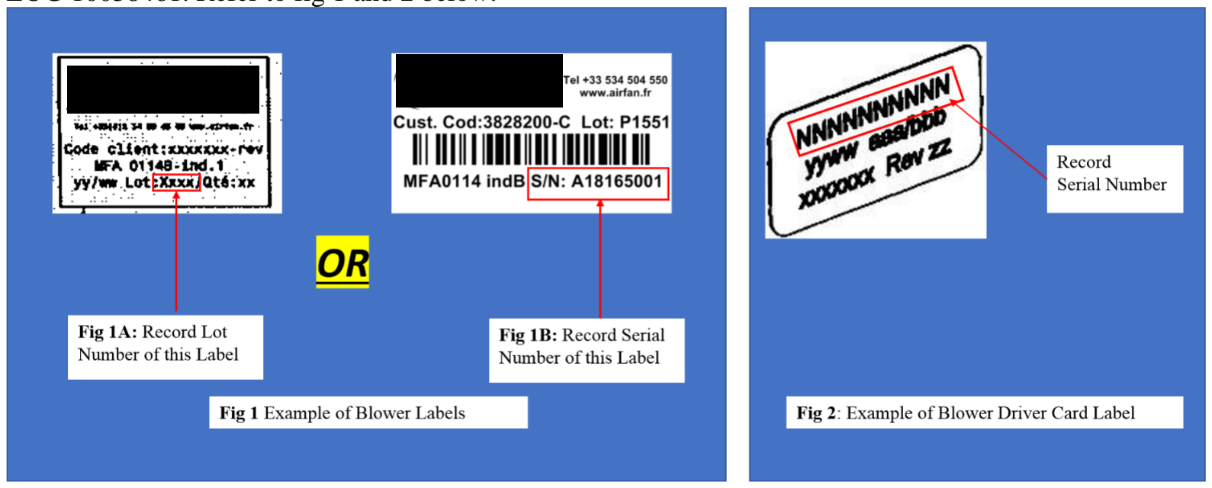
[picture p144: figure]

Title: | PB560 Assembly procedure 2
INSTRUCTIONS | Page 14 of 19
2. Using alcohol and kimwipe, wipe the blower housing where the strips (blln #55) and collar (blln #57) will be applied. See fig 3 below
3. Affix the 2 foam strips on the top of the blower as per fig 3 below
4. Screw the hexagonal spacers (blln #54) using a 4.4 in-lb Torque and 5mm hex socket in the location shown in fig 4 below
5. Apply a drop of thread-lock glue LOCTITE 243 (blln #511) at the start of the tapping of each spacer as per fig 5 below. Add an additional drop of Loctite beside Hex nut closest to spacer (i.e. in a visible location) so presence of Loctite can be confirmed at a later stage. See fig 5
6. Position the Blower Driver Card and install (but not torque) the top two M3x5 screws (blln #51). Add the shielding (blln #52) by positioning the harness under it, install two additional M3x5 (blln #51) screws and torque all four in a diagonal direction to 4.4in-lb, fig 6. Ensure that the cable is not pinched by the shielding by verifying that it can move freely under the shielding.Refer to Fig 7.
7. As a check that the Blower Driver Card is fully secured, verify that there is no gap between the screw head and the Blower Driver Card

Foam( blln #55)

Fig 3 | Fig 4

Torque hex spacers,
(blln #54 to 4.4lbs

Add drop of adhesive into the hex nut tapping as shown Add drop of adhesive approx 10mm directly below plastic
collar mounting hole

Fig 5

Fig 6

M3x5 screws,
blln #51

Shielding,
blln #52

M3x5 screws,
blln #51

Fig 7

Ensure cable is free to
move and not pinched

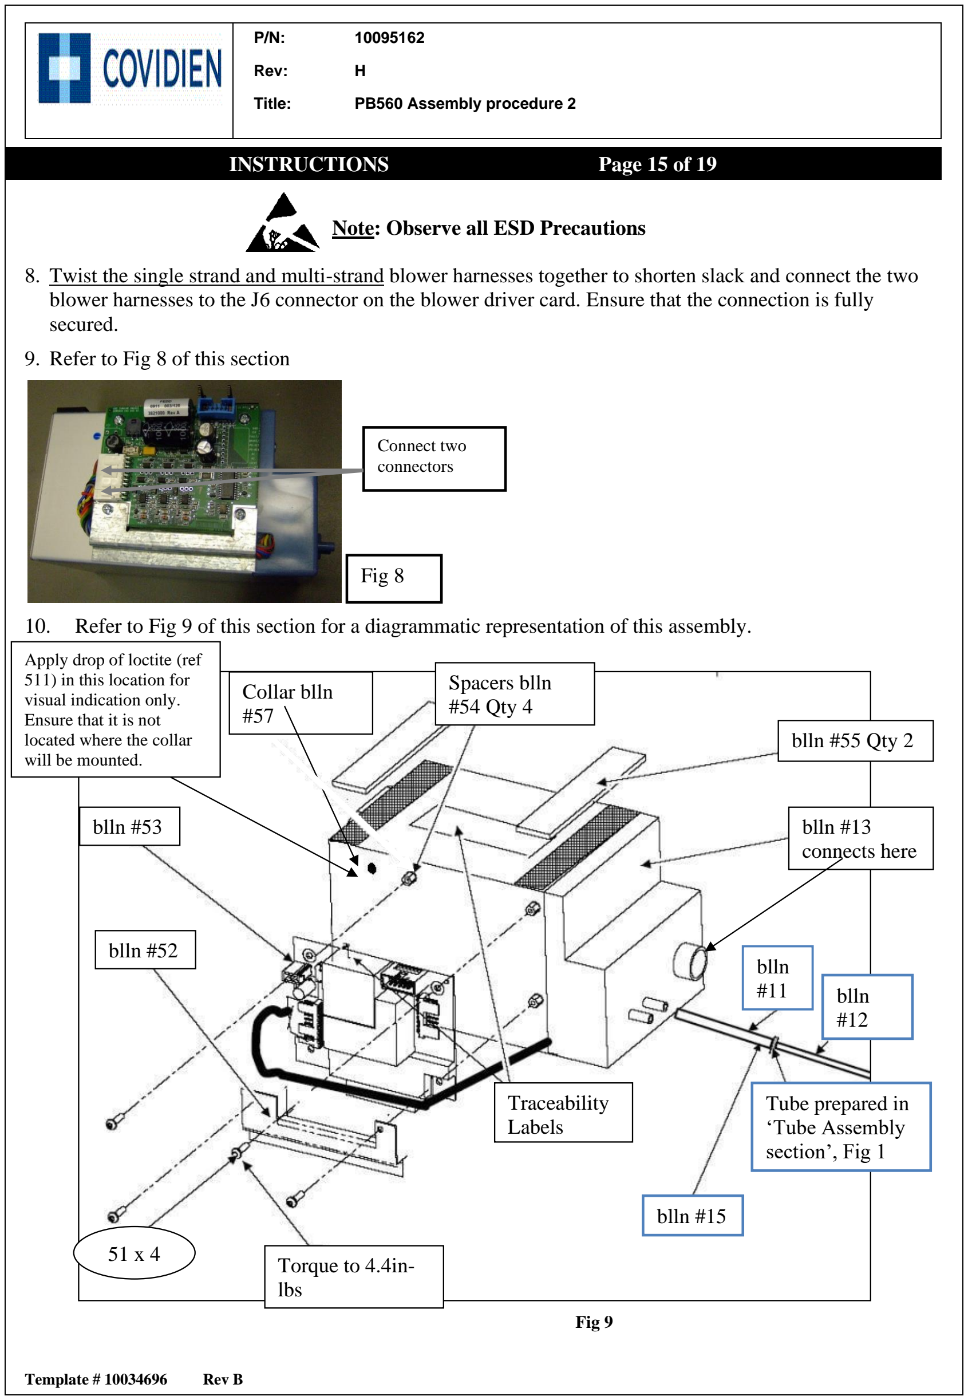
[picture p145: page 15]

Title: | PB560 Assembly procedure 2
INSTRUCTIONS | Page 15 of 19
8. Twist the single strand and multi-strand blower harnesses together to shorten slack and connect the two blower harnesses to the J6 connector on the blower driver card. Ensure that the connection is fully secured.
9. Refer to Fig 8 of this section
10. Refer to Fig 9 of this section for a diagrammatic representation of this assembly.

Fig 8

Connect two
connectors

Note: Observe all ESD Precautions

Fig 9

Collar blln
#57

blln #52

Spacers blln
#54 Qty 4

blln #53

Torque to 4.4in-lbs

blln #55 Qty 2

blln #13
connects here

blln
#11 | blln

| #12

blln #15

Tube prepared in
‘Tube Assembly
section’, Fig 1

Traceability
Labels

Apply drop of loctite (ref
511) in this location for
visual indication only.
Ensure that it is not
located where the collar
will be mounted.

51 x 4

Title: | PB560 Assembly procedure 2
INSTRUCTIONS | Page 16 of 19
11. Dress cabling using a ty-wrap as per fig 10 by, hand-tightening ty-wrap and cuting excess with pliers (do not use ty-wrap gun) as per fig 10. Verify that cabling is neat, i.e. no strands which are loose enough to come in contact with other components.
12. Attach the silicon tube (blln #13) to the blower, see fig.11 ensuring that the tubing is pushed all the way to the end.
13. Attach the tubing (blln #12/15/11) (ref fig 9 & 11 of this section), ensuring that the tubing is pushed all the way to the end of the barb / connection.
14. Connect the short end of the harness (blln #59) to the PCBA and fix the plastic collar (blln #57) around the ferrite so that it routes between the ferrite and the wire loop. See Fig 12 of this section. Ensure that the harness connection is fully secured.
15. Apply a drop of thread-lock glue LOCTITE 243 (blln #511) at the start of the tapping of the P-Clip mounting hole. Carefully mount the Plastic collar, now clipped onto the ferrite of harness (blln #59), to the Blower Housing using screw (blln#111) and washer (blln #113). Torque to 8.9 in-lbs. See fig 12 & 13 of this section. Ensure that the harness connection is fully secured.

Fig 11

Fig 10

720

silicon tube (blln #13)

Tubing assembly 12/15/11,
see fig 9 also

Affix collar here

M3x8 screw, (blln
#111) with M3

Fender Washer

Fig 13
Fig 12

Attach
harness

Title: | PB560 Assembly procedure 2
INSTRUCTIONS | Page 17 of 19
POWER SUPPLY HARNESS, EXPIRATORY & INSP BLOC INSTALLATION

Materials:
Balloon Number | Part Number | Description | Qty
85 | Refer to BOM | TCB Screw hexalobe D3 x 8 | 3
87 | Refer to BOM | CPU/Power supply harness | 1
88 | Refer to BOM | Hardwired buzzer card | 1
720 | Refer to BOM | Ty-wrap | 1
59 | Refer to BOM | Power supply/Blower driver harness | 1
725 | Refer to BOM | Double sided tape | 25mm
724 | Refer to BOM | Ferrite | 1

Process:
Note:

Ensure that the fan is installed in the correct orientation, arrow pointing up and the connector is securely connected
Check that both foam strips (55 & 714) are in place.
1. Connect the power supply blower harness (blln #59) on blower assembly to power management card. See fig 1. Ensure that the harness connection is fully secured in place using clamp as per fig 1

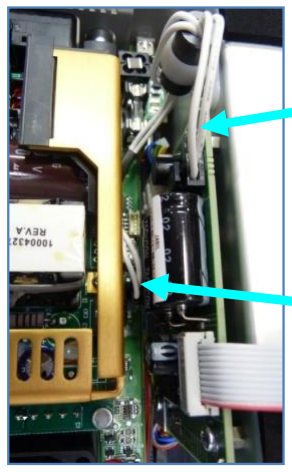
[picture p146: figure]

2. Position the blower in its place, connect free end of the 50mm silicone tubing from the O2 solenoid valve to the blower making sure that the silicon tubing is pushed all the way in, and fasten it with the ty-wrap (blln #720) using ty-wrap gun. See fig 5.

Note: Be careful not to catch cables during this step.

3. Fig 2 below indicates how Silicon Tube 15x21 (blln #13) and O2 Valve should be connected (tubing on the Inspiratory Conical Block not shown for clarity). Ensure all tubing is fully seated on blower.

Fig 1

Connect harness to
power management
PCBA

Power supply/Blower
driver harness

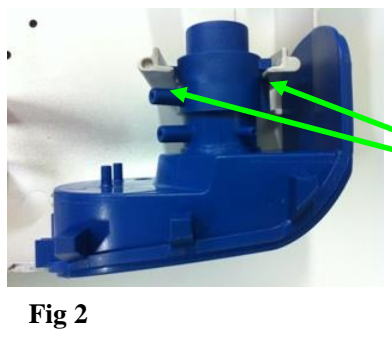
[picture p147: figure]
Fig 2

Note: this picture is
for representation
of insp block
positioning

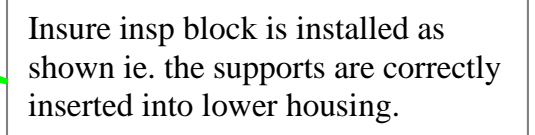
[picture p148: figure]
Insure insp block is installed as shown ie. the supports are correctly inserted into lower housing.

Title: | PB560 Assembly procedure 2
INSTRUCTIONS | Page 18 of 19
4. Take the Inspiratory Block assembly, remove the backing strip from the double sided tape on the ferrite and attach the ferrite in the position shown in fig 3. Connect the Inspiratory Conical Block assembly to the Blower Housing via Silicon Tube 15x21. fig 4.

Note that the FiO2 cable is routed under the Silicon Tube 15x21 and between lower housing features and conical block as indicated in Figure 5. See fig 2 for correct installation of insp block to lower housing

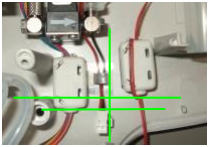
[picture p149: figure]
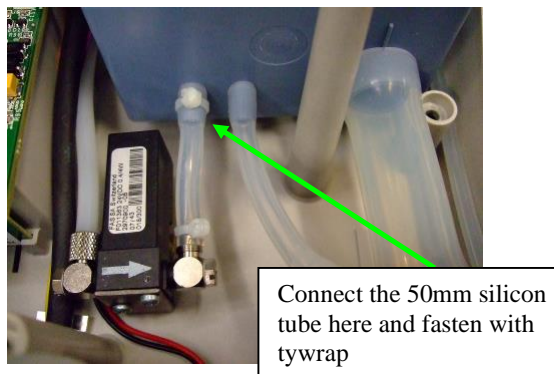
[picture p150: figure]
Connect the 50mm silicon tube here and fasten with tywrap
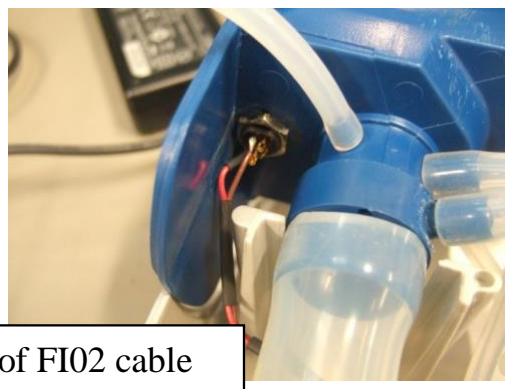
[picture p151: figure]
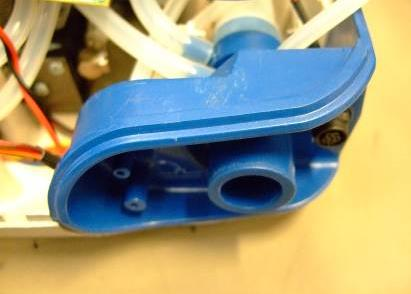
[picture p152: figure]

5. Fasten the expiratory conical block assembly by screwing (hand-tightened) the knurled knob under the appliance - Ref fig 7

Fig 4

Fig 6

Fig 3

Note routing of FI02 cable

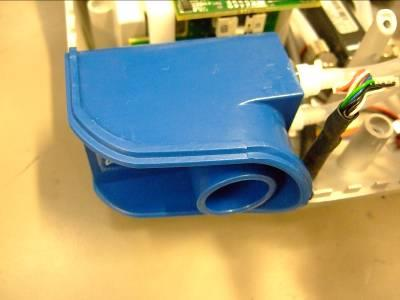
[picture p153: figure]

Title: | PB560 Assembly procedure 2
INSTRUCTIONS | Page 19 of 19

Note on routing of blower harness / DHR Check recording
Ensure that the harness is routed as shown in fig 8 of this section and that a ty-wrap is used to keep the single strand and multi-strand harnesses together. This will reduce risk of harness becoming caught between the PCBA and blower as in fig 9 of this section, which may lead to damage of the cable insulation.

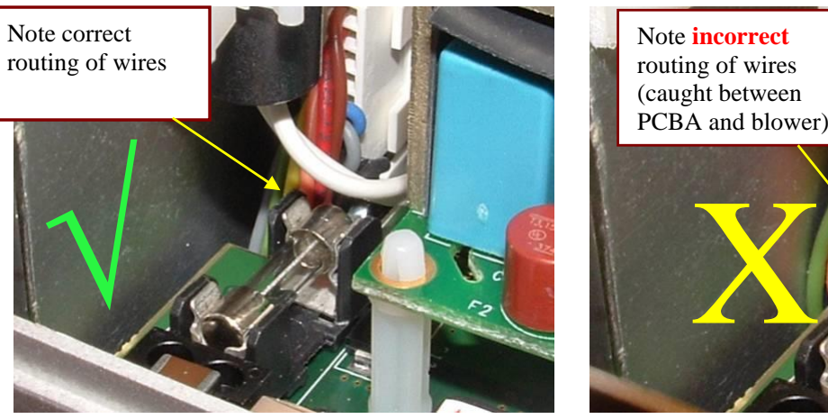
[picture p154: figure]
Note correct routing of wires
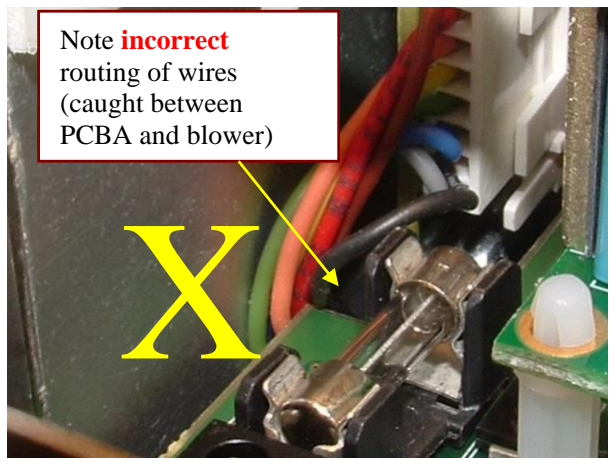
[picture p155: figure]
Note incorrect routing of wires (caught between PCBA and blower)

Fig 8 – correct routing | Fig 9 – incorrect routing

Note: verify collar is correctly secured to blower.

DHR LOG 10038461
1. Before moving unit to next stage, ensure that all applicable sections of DHR LOG 10038461 are completed.
2. Sign & Date DHR.
