L0op/medtronic-pb560/file-set-1/Manufacturing Documents/PB560 Power Pack - Quality Process Flow - Manufacturing Procedures/10140875D00 - PB500 Powerpack FRU DHR.pdf

P/N: | 10140875 | Page 1 of 2
Rev: | D
Title: | PB500 Powerpack FRU DHR

DEVICE HISTORY RECORD

Ref Procedure: 10099745

10131548 | Powerpack assy |

UUT S/N / Hotbed number:

(Blln #16) Keypad L/C: | | REV:
Keypad Test: | PASS / FAIL
DMM Cal ID: | _____________
PCBA to DC cable Test: | VDC | PASS / FAIL
Result for test on pins of AC OUT: | PASS / FAIL
AC LED: | PASS / FAIL
Hipot & Leakage Current Tests: | PASS / FAIL
Verify test report has been placed in package: |
Verify Number on packaging carton label matches DHR: |
10131169 | FRU PCBA (10153315) |

UUT S/N / Hotbed number:

(Blln #15) PowerPack PCBA S/N: S/N: | | REV:
S/W Version: | | Verify PP2A
Unit System Test UUT | PASS / FAIL
10132667 | FRU housing cover (10153316) |

(Blln#24) PowerPack ID Label Revision: REV

Quantity:

10132668 | Housing Door(10153317) |

Battery Change Label Rev: REV:

Quantity:

FRU completed by: Signature: | Date:

### 10131548 - PRODUCT RELEASE CERTIFICATION

This device has met the requirements of the PB500 Powerpack Release Authorisation Procedure. Production Release Personnel:
Name: | Date:

P/N: | 10140875 | Page 2 of 2
Rev: | D
Title: | PB500 Powerpack FRU DHR

DEVICE HISTORY RECORD

Ref Procedure: 10099745

Discrepancy Log

DISCREPANCY DETAIL:

SIGN: | DATE:

CORRECTIVE ACTION:

SIGN: | DATE:

RE-ASSEMBLY COMPLETED BY:

SIGN: | DATE:

Discrepancy Log

DISCREPANCY DETAIL:

SIGN: | DATE:

CORRECTIVE ACTION:

SIGN: | DATE:

RE-ASSEMBLY COMPLETED BY:

SIGN: | DATE:
