L0op/medtronic-pb560/file-set-2/Manufacturing Fixtures/PT00057819A00 Fixture, PB500 FRU Battery Assembly Aid.pdf

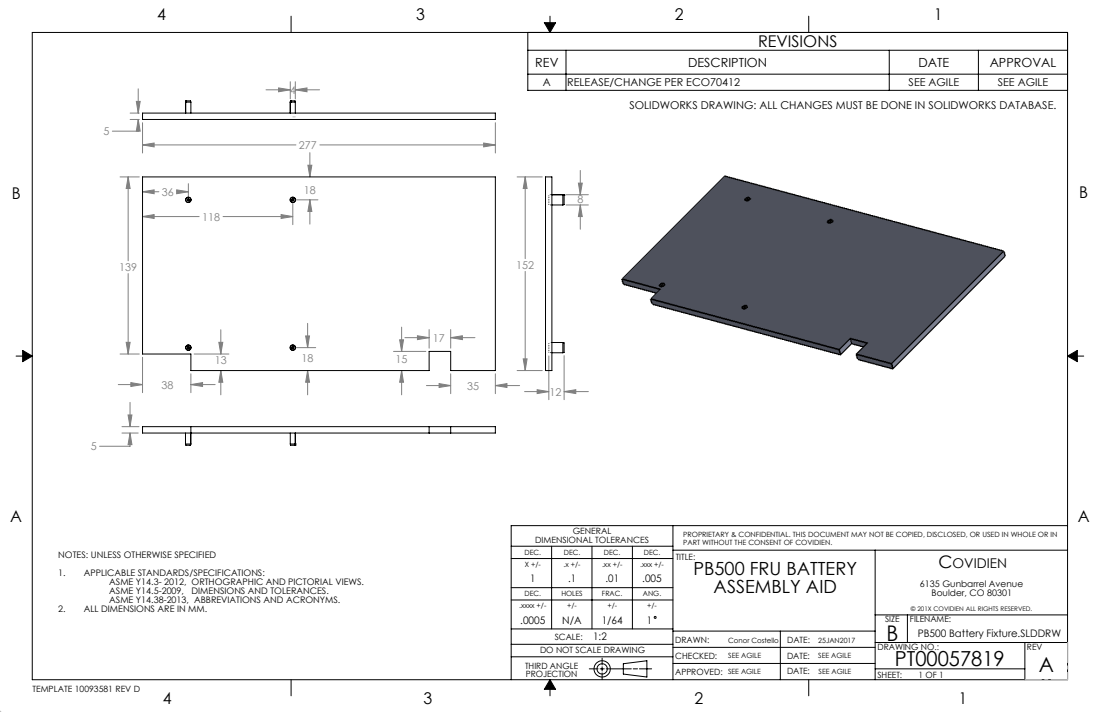
[picture p230: page 1]
2 TEMPLATE 10093581 REV D; .xxxx +/-; PB500 Battery Fixture.SLDDRW Conor Costello; 25JAN2017; THIRD ANGLE; .xxx +/-; SHEET:; DIMENSIONAL TOLERANCES

REVISIONS

REV | DESCRIPTION | DATE | APPROVAL
A | RELEASE/CHANGE PER ECO70412 | SEE AGILE | SEE AGILE

SOLIDWORKS DRAWING: ALL CHANGES MUST BE DONE IN SOLIDWORKS DATABASE.

PROPRIETARY & CONFIDENTIAL. THIS DOCUMENT MAY NOT BE COPIED, DISCLOSED, OR USED IN WHOLE OR IN
PART WITHOUT THE CONSENT OF COVIDIEN.

NOTES: UNLESS OTHERWISE SPECIFIED
1. APPLICABLE STANDARDS/SPECIFICATIONS:

TITLE: PB500 FRU BATTERY ASSEMBLY AID | COVIDIEN 6135 Gunbarrel Avenue Boulder, CO 80301 © 201X COVIDIEN ALL RIGHTS RESERVED. B N/A

ASME Y14.3- 2012, ORTHOGRAPHIC AND PICTORIAL VIEWS.
ASME Y14.5-2009, DIMENSIONS AND TOLERANCES.
ASME Y14.38-2013, ABBREVIATIONS AND ACRONYMS.

2. ALL DIMENSIONS ARE IN MM.

SIZE | FILENAME:

1:2 SCALE: | DRAWN: CHECKED: SEE AGILE APPROVED: SEE AGILE | DATE: DATE: SEE AGILE DATE: SEE AGILE
DO NOT SCALE DRAWING | | | DRAWING NO.: PT00057819 | REV A
