L0op/medtronic-pb560/file-set-1/Manufacturing Documents/PB560 - Quality Process Flow - Manufacturing Procedures/10037308AJ00.pdf

## QUALITY PROCESS FLOWCHART

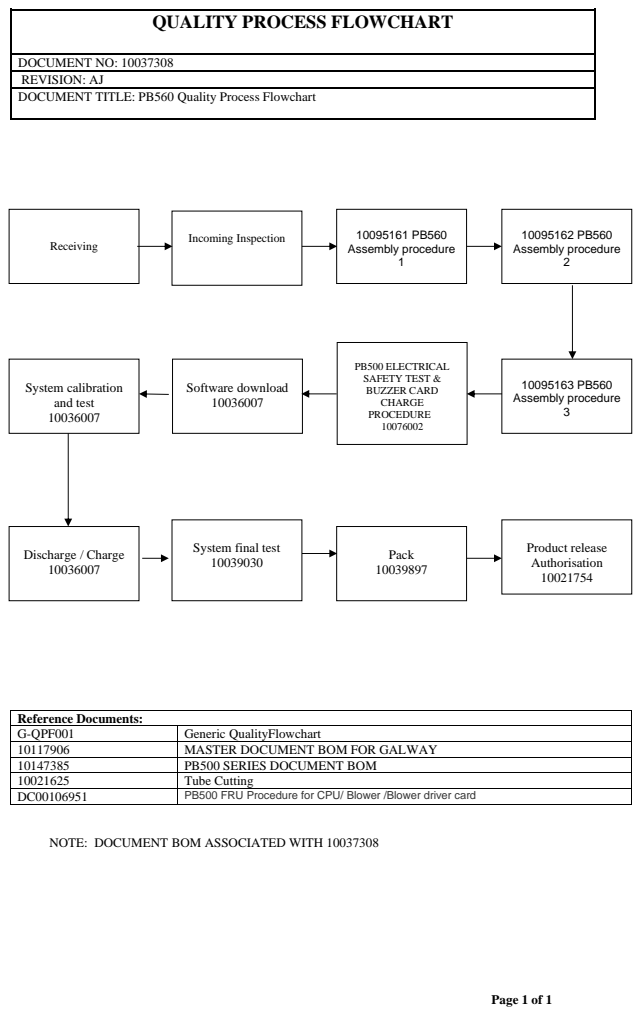
[picture p231: page 1]
Page 1 of 1; Reference Documents:; 10095162 PB560 Assembly procedure 2; 10095163 PB560 Assembly procedure 3; PB500 ELECTRICAL SAFETY TEST & BUZZER CARD CHARGE PROCEDURE 10076002; Software download 10036007; System calibration and test 10036007; 10095161 PB560 Assembly procedure 1; Discharge / Charge 10036007; Pack; Product release Authorisation 10021754

DOCUMENT NO: 10037308
REVISION: AJ
DOCUMENT TITLE: PB560 Quality Process Flowchart

Incoming Inspection Receiving

System final test

G-QPF001 | Generic QualityFlowchart
10117906 | MASTER DOCUMENT BOM FOR GALWAY
10147385 | PB500 SERIES DOCUMENT BOM
10021625 | Tube Cutting
DC00106951 | PB500 FRU Procedure for CPU/ Blower /Blower driver card

NOTE: DOCUMENT BOM ASSOCIATED WITH 10037308
