L0op/medtronic-pb560/file-set-1/Manufacturing Documents/PB560 Power Pack - Quality Process Flow - Manufacturing Procedures/10071204L00 - PB500 Series Power Pack Quality Process Flow.pdf

# QUALITY PROCESS FLOWCHART

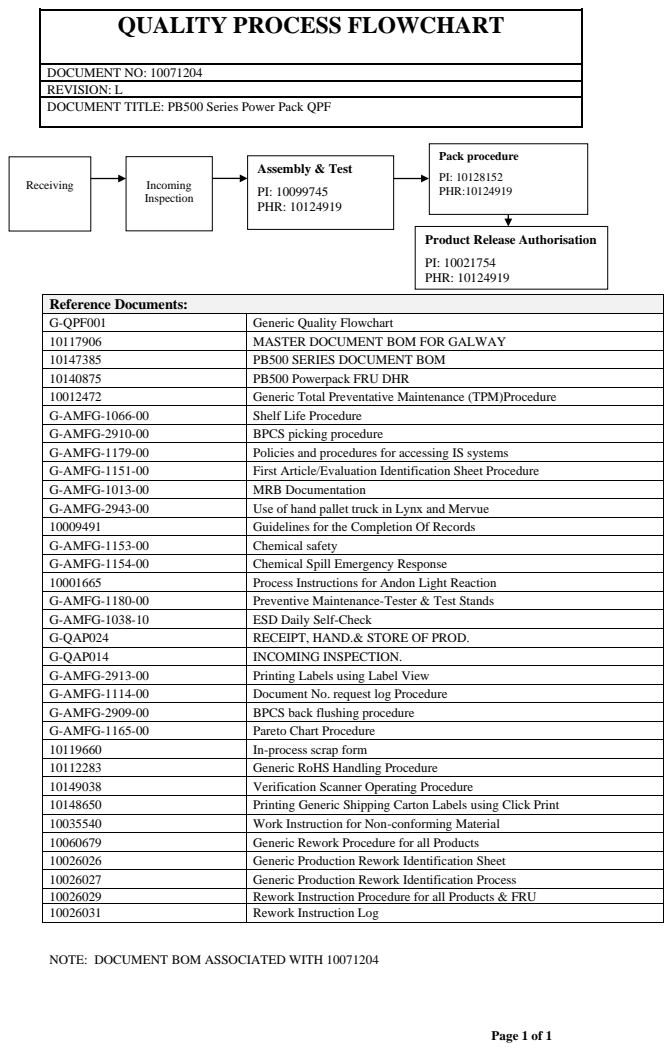
[picture p232: page 1]
Page 1 of 1; Reference Documents:; Incoming Inspection; Assembly & Test; PI: 10099745 PHR: 10124919; Receiving; Pack procedure; PI: 10128152 PHR:10124919; PI: 10021754 PHR: 10124919

DOCUMENT NO: 10071204
REVISION: L
DOCUMENT TITLE: PB500 Series Power Pack QPF

Product Release Authorisation

G-QPF001 | Generic Quality Flowchart
10117906 | MASTER DOCUMENT BOM FOR GALWAY
10147385 | PB500 SERIES DOCUMENT BOM
10140875 | PB500 Powerpack FRU DHR
10012472 | Generic Total Preventative Maintenance (TPM)Procedure
G-AMFG-1066-00 | Shelf Life Procedure
G-AMFG-2910-00 | BPCS picking procedure
G-AMFG-1179-00 | Policies and procedures for accessing IS systems
G-AMFG-1151-00 | First Article/Evaluation Identification Sheet Procedure
G-AMFG-1013-00 | MRB Documentation
G-AMFG-2943-00 | Use of hand pallet truck in Lynx and Mervue
10009491 | Guidelines for the Completion Of Records
G-AMFG-1153-00 | Chemical safety
G-AMFG-1154-00 | Chemical Spill Emergency Response
10001665 | Process Instructions for Andon Light Reaction
G-AMFG-1180-00 | Preventive Maintenance-Tester & Test Stands
G-AMFG-1038-10 | ESD Daily Self-Check
G-QAP024 | RECEIPT, HAND.& STORE OF PROD.
G-QAP014 | INCOMING INSPECTION.
G-AMFG-2913-00 | Printing Labels using Label View
G-AMFG-1114-00 | Document No. request log Procedure
G-AMFG-2909-00 | BPCS back flushing procedure
G-AMFG-1165-00 | Pareto Chart Procedure
10119660 | In-process scrap form
10112283 | Generic RoHS Handling Procedure
10149038 | Verification Scanner Operating Procedure
10148650 | Printing Generic Shipping Carton Labels using Click Print
10035540 | Work Instruction for Non-conforming Material
10060679 | Generic Rework Procedure for all Products
10026026 | Generic Production Rework Identification Sheet
10026027 | Generic Production Rework Identification Process
10026029 | Rework Instruction Procedure for all Products & FRU
10026031 | Rework Instruction Log

NOTE: DOCUMENT BOM ASSOCIATED WITH 10071204
