L0op/medtronic-pb560/file-set-2/Mechanical Part Drawings/2970900/S0122148g (2).pdf

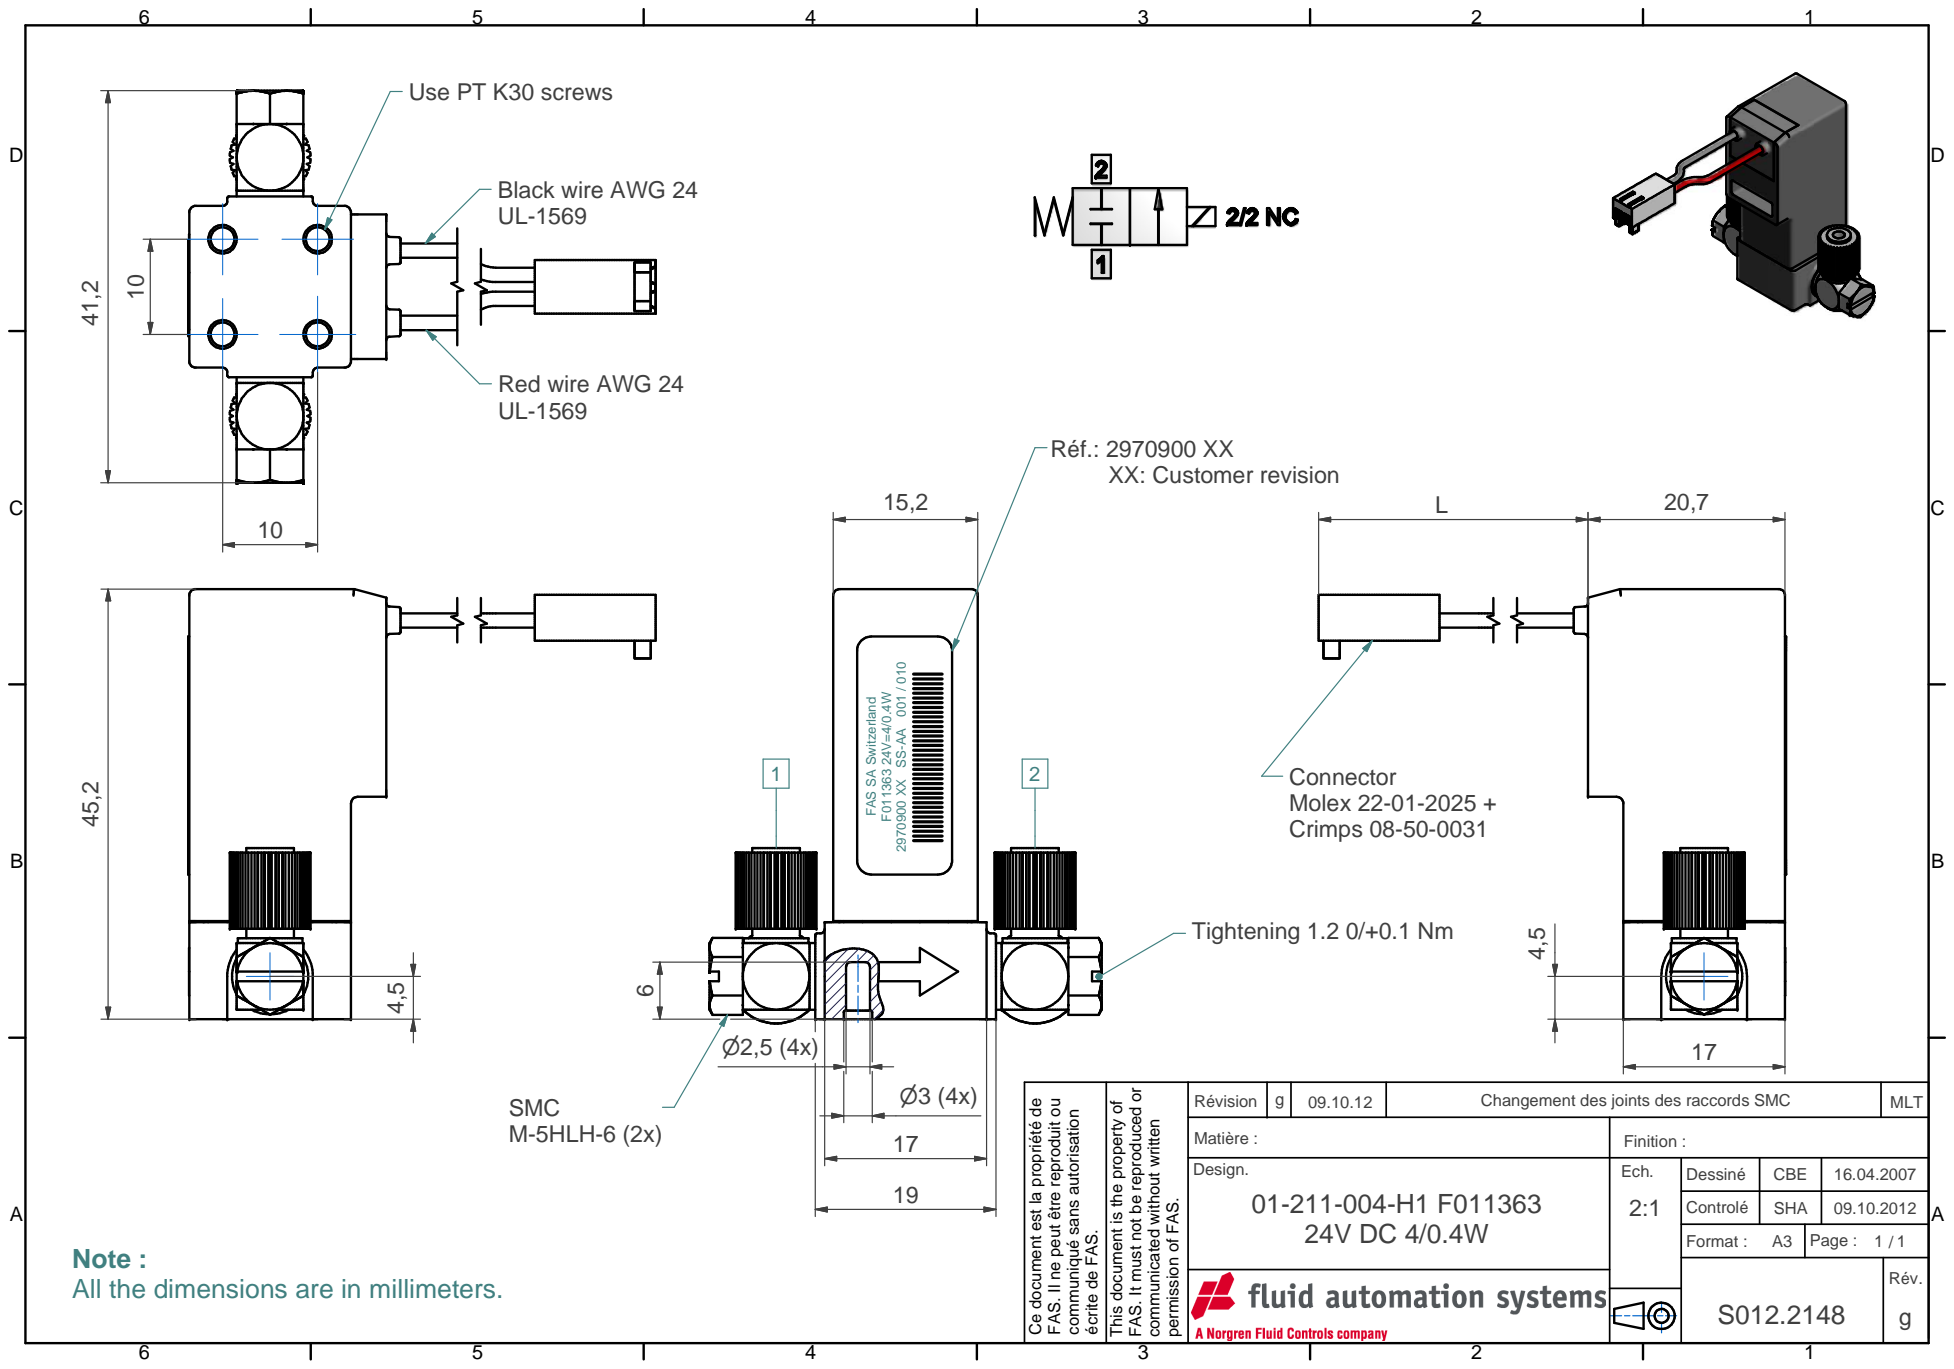
[picture p250: page 1]
wit; rla; Révision; Matière :; Finition :; Design.; Ech.; Dessiné; Controlé; Format :; Page :; Rév.; rié; uit; niq; ris; tio; rit; his; nic; mis; sio; CBE; SHA; Connector Molex 22-01-2025 + Crimps 08-50-0031; SMC M-5HLH-6 (2x); Tightening 1.2 0/+0.1 Nm; Changement des joints des raccords SMC; MLT

Use PT K30 screws

Black wire AWG 24

Red wire AWG 24

Réf.: 2970900 XX
XX: Customer revision

Note :
All the dimensions are in millimeters.
