L0op/medtronic-pb560/file-set-2/Mechanical Part Drawings/3809700/3809700A00.PDF

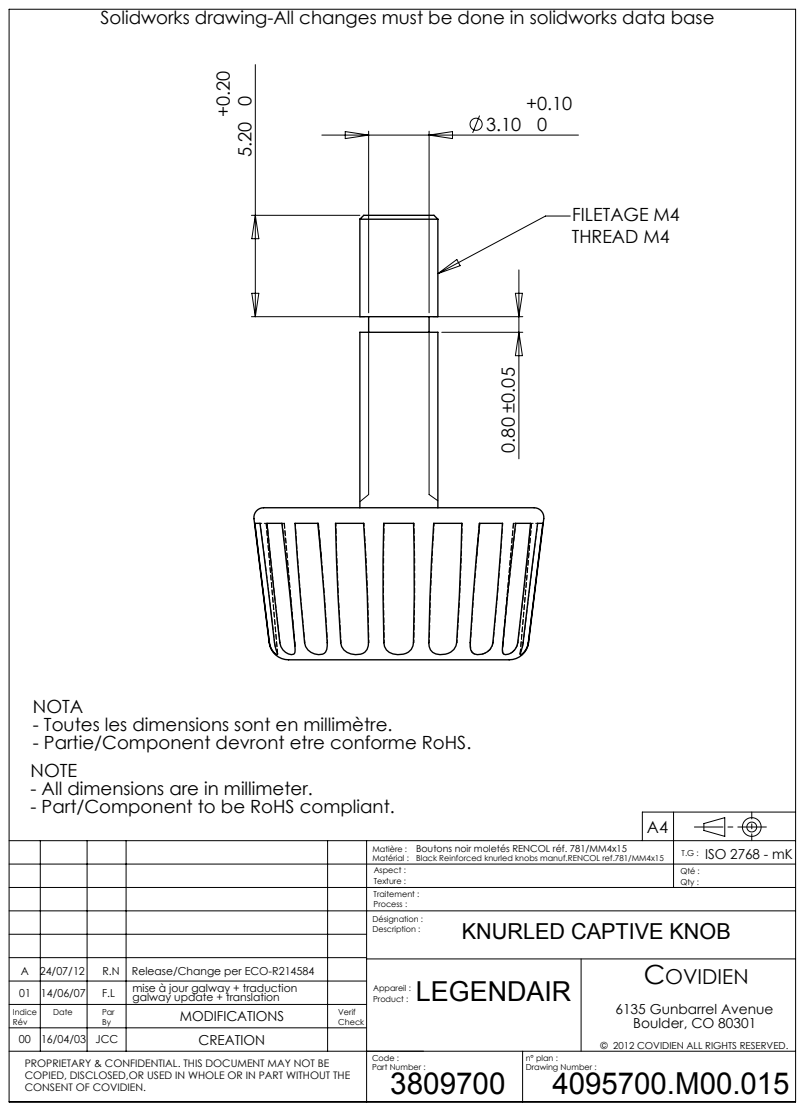
[picture p252: page 1]
6135 Gunbarrel Avenue Boulder, CO 80301; FILETAGE M4 THREAD M4; Texture :; Aspect :; ISO 2768 - mK; Qty :; Qté :; Process :; Drawing Number :; n° plan :; Part Number :; Product :; Description :; Matérial :; Code :; Appareil :; Désignation :; Traitement :; Matière :

Solidworks drawing-All changes must be done in solidworks data base 0.80 ±0.05

NOTA
- Toutes les dimensions sont en millimètre.
- Partie/Component devront etre conforme RoHS.
NOTE
- All dimensions are in millimeter.
- Part/Component to be RoHS compliant.

Boutons noir moletés RENCOL réf. 781/MM4x15
Black Reinforced knurled knobs manuf.RENCOL ref.781/MM4x15

KNURLED CAPTIVE KNOB

24/07/12 R.N Release/Change per ECO-R214584
mise à jour galway + traduction 01 14/06/07 F.L
00 16/04/03 JCC
PROPRIETARY & CONFIDENTIAL. THIS DOCUMENT MAY NOT BE
COPIED, DISCLOSED,OR USED IN WHOLE OR IN PART WITHOUT THE
CONSENT OF COVIDIEN.

galway update + translation
Par

© 2012 COVIDIEN ALL RIGHTS RESERVED.
