L0op/medtronic-pb560/file-set-2/Mechanical Part Drawings/3812500/3812500A00 .PDF

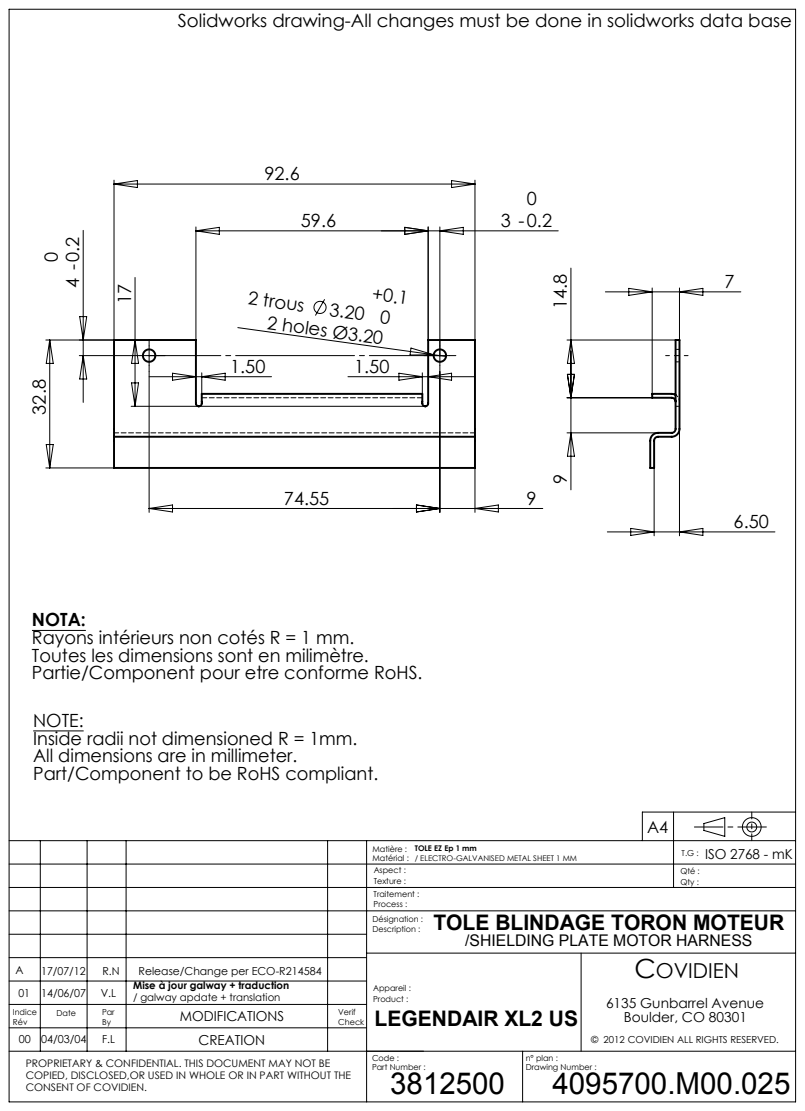
[picture p253: page 1]
6135 Gunbarrel Avenue Boulder, CO 80301; 2 trous 3.20 0 2 holes Ø3.20; LEGENDAIR XL2 US; Matière :; Traitement :; Désignation :; Appareil :; Code :; Release/Change per ECO-R214584; Matérial :; Description :; Product :; Part Number :; n° plan : Drawing Number :; Process :; Qté : Qty :; ISO 2768 - mK; Aspect : Texture :; Mise à jour galway + traduction

Solidworks drawing-All changes must be done in solidworks data base

NOTA:
Rayons intérieurs non cotés R = 1 mm.
Toutes les dimensions sont en milimètre.
Partie/Component pour etre conforme RoHS.

NOTE:
Inside radii not dimensioned R = 1mm.
All dimensions are in millimeter.
Part/Component to be RoHS compliant.

TOLE EZ Ep 1 mm
/ ELECTRO-GALVANISED METAL SHEET 1 MM
TOLE BLINDAGE TORON MOTEUR
/SHIELDING PLATE MOTOR HARNESS

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

/ galway apdate + translation V.L

© 2012 COVIDIEN ALL RIGHTS RESERVED.
