L0op/medtronic-pb560/file-set-2/Mechanical Part Drawings/3814200/3814200A00.PDF

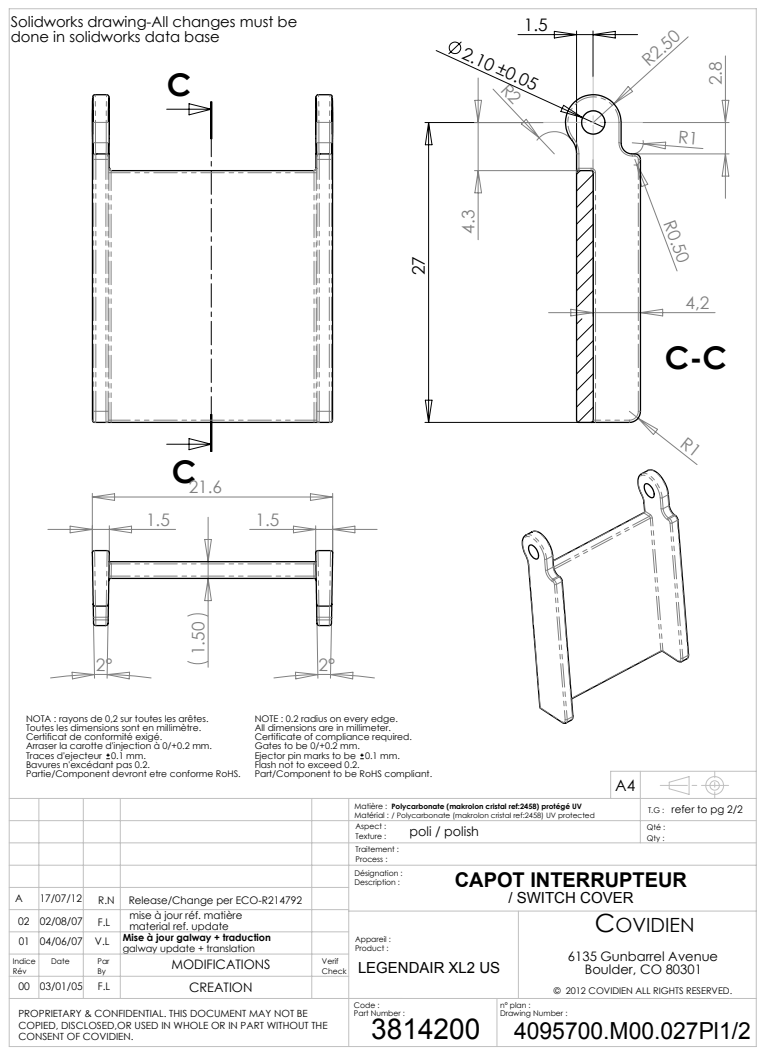
[picture p254: page 1]
6135 Gunbarrel Avenue Boulder, CO 80301; LEGENDAIR XL2 US; Matière :; Traitement :; Désignation :; Appareil :; Code :; Matérial :; Description :; Product :; Part Number :; n° plan : Drawing Number :; Process :; Qté : Qty :; Aspect : Texture :; refer to pg 2/2

Solidworks drawing-All changes must be
done in solidworks data base

NOTA : rayons de 0,2 sur toutes les arêtes.
Toutes les dimensions sont en millimètre.
Certificat de conformité exigé.
Arraser la carotte d'injection à 0/+0.2 mm.
Traces d'ejecteur 0.1 mm.
Bavures n'excédant pas 0.2.
Partie/Component devront etre conforme RoHS.

NOTE : 0.2 radius on every edge.
All dimensions are in millimeter.
Certificate of compliance required.
Gates to be 0/+0.2 mm.
Ejector pin marks to be 0.1 mm.
Flash not to exceed 0.2.
Part/Component to be RoHS compliant.

Polycarbonate (makrolon cristal ref:2458) protégé UV
/ Polycarbonate (makrolon cristal ref:2458) UV protected
poli / polish
CAPOT INTERRUPTEUR
/ SWITCH COVER

A 17/07/12 R.N Release/Change per ECO-R214792
01 04/06/07 V.L Mise à jour galway + traduction

mise à jour réf. matière
material ref. update
galway update + translation
Par

© 2012 COVIDIEN ALL RIGHTS RESERVED.

PROPRIETARY & CONFIDENTIAL. THIS DOCUMENT MAY NOT BE
COPIED, DISCLOSED,OR USED IN WHOLE OR IN PART WITHOUT THE
CONSENT OF COVIDIEN.

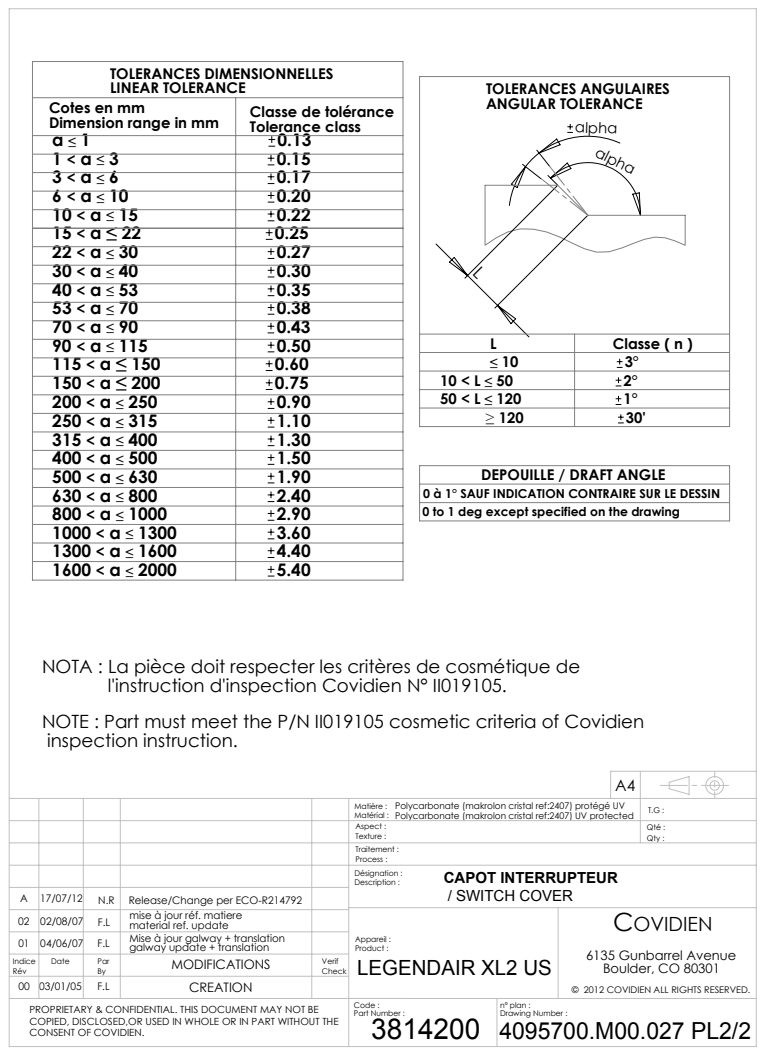
[picture p255: page 2]
L Classe ( n ); TOLERANCES ANGULAIRES ANGULAR TOLERANCE; 6135 Gunbarrel Avenue Boulder, CO 80301; CAPOT INTERRUPTEUR; LEGENDAIR XL2 US; Matière :; Traitement :; Désignation :; Appareil :; Code :; Mise à jour galway + translation; mise à jour réf. matiere; Matérial :; Description :; Product :; Part Number :; n° plan : Drawing Number :; Process :; Qté : Qty :; Aspect : Texture :; / SWITCH COVER

TOLERANCES DIMENSIONNELLES
LINEAR TOLERANCE
Cotes en mm
Dimension range in mm

Classe de tolérance
Tolerance class

DEPOUILLE / DRAFT ANGLE

0 à 1° SAUF INDICATION CONTRAIRE SUR LE DESSIN
0 to 1 deg except specified on the drawing

NOTA : La pièce doit respecter les critères de cosmétique de
l'instruction d'inspection Covidien N° II019105.
NOTE : Part must meet the P/N II019105 cosmetic criteria of Covidien
inspection instruction.

Polycarbonate (makrolon cristal ref:2407) protégé UV
Polycarbonate (makrolon cristal ref:2407) UV protected

A 17/07/12 N.R Release/Change per ECO-R214792
PROPRIETARY & CONFIDENTIAL. THIS DOCUMENT MAY NOT BE
COPIED, DISCLOSED,OR USED IN WHOLE OR IN PART WITHOUT THE
CONSENT OF COVIDIEN.

material ref. update
galway update + translation

© 2012 COVIDIEN ALL RIGHTS RESERVED.
