L0op/medtronic-pb560/file-set-2/Mechanical Part Drawings/3823600/3823600C00.PDF

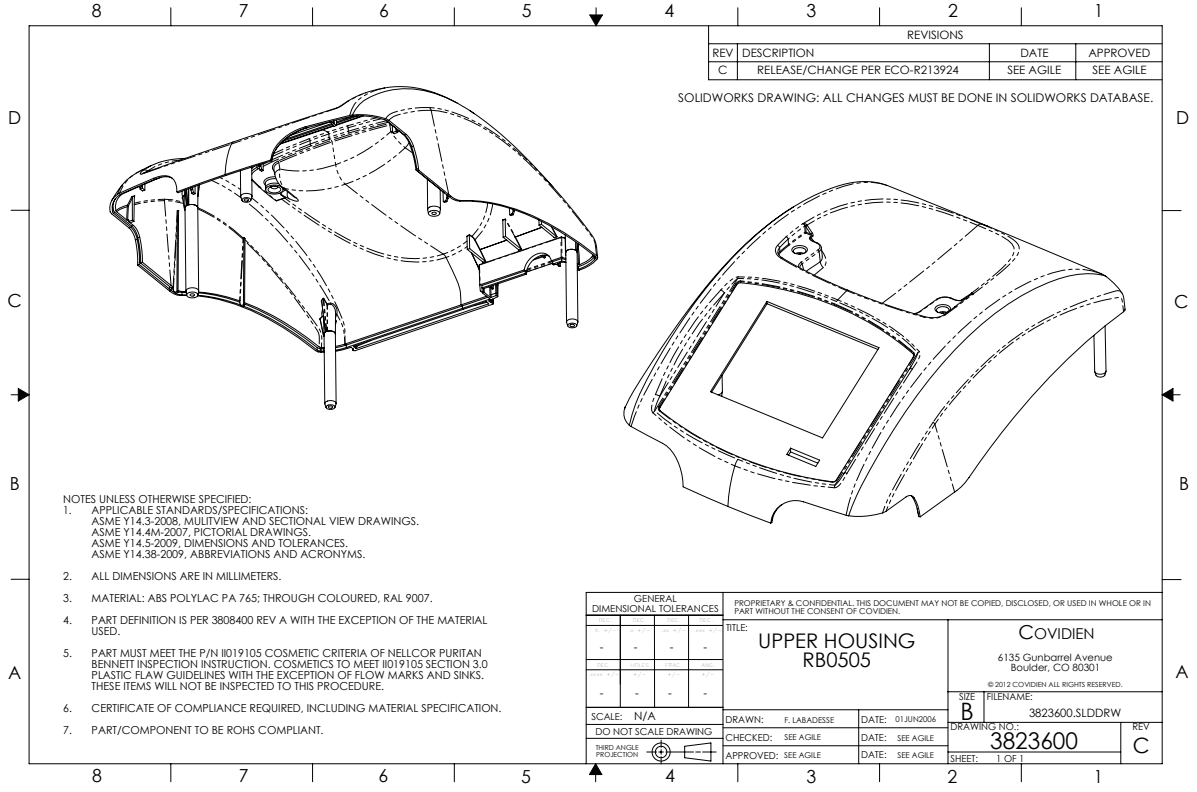
[picture p256: page 1]
F. LABADESSE; 01JUN2006; THIRD ANGLE; SHEET:; DATE:; DRAWING NO.:; SEE AGILE; .xxxx +/-; .xxx +/-

REVISIONS

REV | DESCRIPTION | DATE | APPROVED
C | RELEASE/CHANGE PER ECO-R213924 | SEE AGILE | SEE AGILE

SOLIDWORKS DRAWING: ALL CHANGES MUST BE DONE IN SOLIDWORKS DATABASE.

NOTES UNLESS OTHERWISE SPECIFIED:
1. APPLICABLE STANDARDS/SPECIFICATIONS:
ASME Y14.3-2008, MULITVIEW AND SECTIONAL VIEW DRAWINGS.
ASME Y14.4M-2007, PICTORIAL DRAWINGS.
ASME Y14.5-2009, DIMENSIONS AND TOLERANCES.
ASME Y14.38-2009, ABBREVIATIONS AND ACRONYMS.
2. ALL DIMENSIONS ARE IN MILLIMETERS.
3. MATERIAL: ABS POLYLAC PA 765; THROUGH COLOURED, RAL 9007.
4. PART DEFINITION IS PER 3808400 REV A WITH THE EXCEPTION OF THE MATERIAL
USED.
5. PART MUST MEET THE P/N II019105 COSMETIC CRITERIA OF NELLCOR PURITAN
BENNETT INSPECTION INSTRUCTION. COSMETICS TO MEET II019105 SECTION 3.0
PLASTIC FLAW GUIDELINES WITH THE EXCEPTION OF FLOW MARKS AND SINKS.
THESE ITEMS WILL NOT BE INSPECTED TO THIS PROCEDURE.
6. CERTIFICATE OF COMPLIANCE REQUIRED, INCLUDING MATERIAL SPECIFICATION.
7. PART/COMPONENT TO BE ROHS COMPLIANT.

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

TITLE: UPPER HOUSING RB0505 | COVIDIEN 6135 Gunbarrel Avenue Boulder, CO 80301 © 2012 COVIDIEN ALL RIGHTS RESERVED. B -

- | - -
DO NOT SCALE DRAWING | | 3823600 | REV C

SIZE | FILENAME: 3823600.SLDDRW
