L0op/medtronic-pb560/file-set-2/Mechanical Part Drawings/3824300/3824300B00.PDF

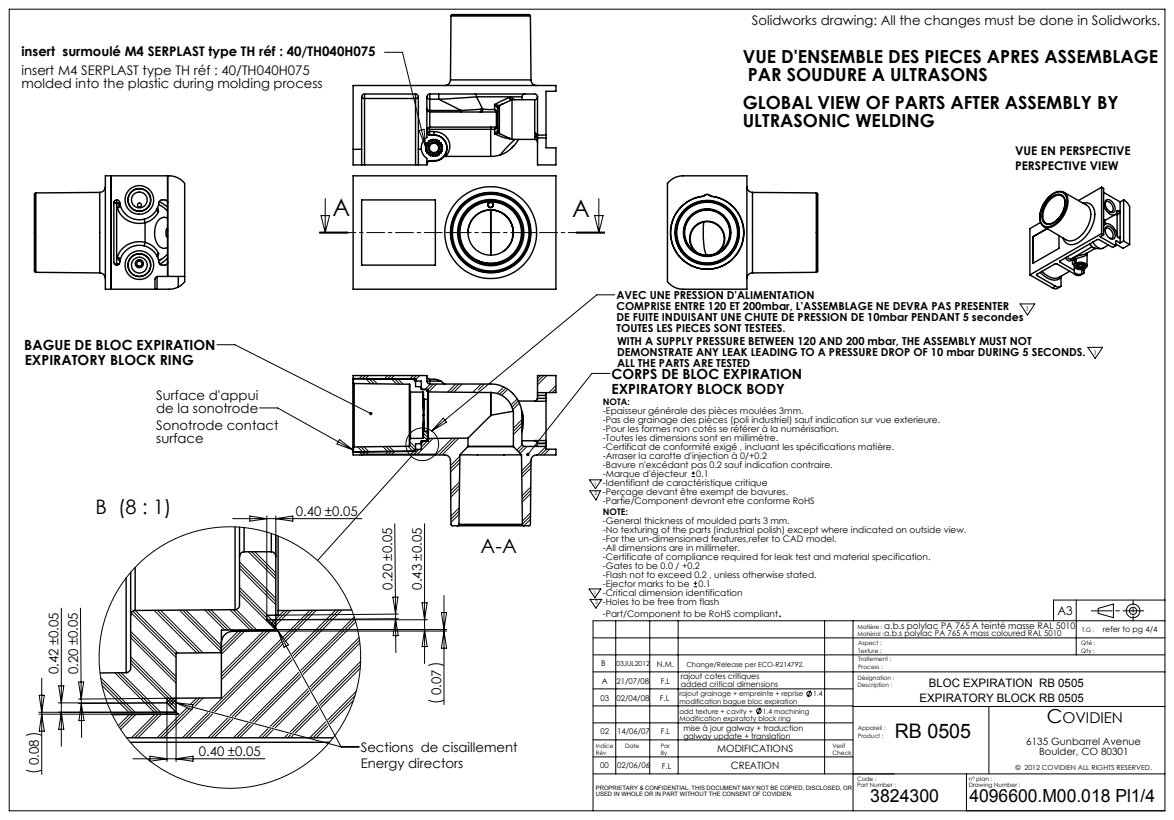
[picture p257: page 1]
6135 Gunbarrel Avenue Boulder, CO 80301; Texture :; Qty :; Qté :; Process :; Drawing Number :; n° plan :; Part Number :; Product :; Description :; Matérial :; Code :; Appareil :; Désignation :; Traitement :; Aspect :; Matière :; USED IN WHOLE OR IN PART WITHOUT THE CONSENT OF COVIDIEN.; refer to pg 4/4

Solidworks drawing: All the changes must be done in Solidworks.
VUE D'ENSEMBLE DES PIECES APRES ASSEMBLAGE
PAR SOUDURE A ULTRASONS
GLOBAL VIEW OF PARTS AFTER ASSEMBLY BY
ULTRASONIC WELDING

insert surmoulé M4 SERPLAST type TH réf : 40/TH040H075
insert M4 SERPLAST type TH réf : 40/TH040H075
molded into the plastic during molding process

VUE EN PERSPECTIVE
PERSPECTIVE VIEW

AVEC UNE PRESSION D'ALIMENTATION
COMPRISE ENTRE 120 ET 200mbar, L'ASSEMBLAGE NE DEVRA PAS PRESENTER
DE FUITE INDUISANT UNE CHUTE DE PRESSION DE 10mbar PENDANT 5 secondes
TOUTES LES PIECES SONT TESTEES.
WITH A SUPPLY PRESSURE BETWEEN 120 AND 200 mbar, THE ASSEMBLY MUST NOT
DEMONSTRATE ANY LEAK LEADING TO A PRESSURE DROP OF 10 mbar DURING 5 SECONDS.
ALL THE PARTS ARE TESTED
CORPS DE BLOC EXPIRATION
EXPIRATORY BLOCK BODY
NOTA:
-Epaisseur générale des pièces moulées 3mm.
-Pas de grainage des pièces (poli industriel) sauf indication sur vue exterieure.
-Pour les formes non cotés se référer à la numérisation.
-Toutes les dimensions sont en millimètre.
-Certificat de conformité exigé , incluant les spécifications matière.
-Arraser la carotte d'injection à 0/+0.2
-Bavure n'excédant pas 0.2 sauf indication contraire.
-Marque d'éjecteur 0.1
-Identifiant de caractéristique critique
-Perçage devant être exempt de bavures.
-Partie/Component devront etre conforme RoHS
NOTE:
-General thickness of moulded parts 3 mm.
-No texturing of the parts (industrial polish) except where indicated on outside view.
-For the un-dimensioned features,refer to CAD model.
-All dimensions are in millimeter.
-Certificate of compliance required for leak test and material specification.
-Gates to be 0.0 / +0.2
-Flash not to exceed 0.2 , unless otherwise stated.
-Ejector marks to be 0.1
-Critical dimension identification
-Holes to be free from flash
-Part/Component to be RoHS compliant.

BAGUE DE BLOC EXPIRATION
EXPIRATORY BLOCK RING 0.20 ±0.05

Surface d'appui
de la sonotrode
Sonotrode contact
surface

a.b.s polylac PA 765 A teinté masse RAL 5010
a.b.s polylac PA 765 A mass coloured RAL 5010

B 03JUL2012 N.M. Change/Release per ECO-R214792.
rajout cotes critiques A 21/07/08 F.L

added critical dimensions

BLOC EXPIRATION RB 0505
EXPIRATORY BLOCK RB 0505

rajout grainage + empreinte + reprise 1.4 03 02/04/08 F.L

modification bague bloc expiration
add texture + cavity + 1.4 machining
Modification expiratoty block ring
galway update + translation
Par

mise à jour galway + traduction 02 14/06/07 F.L

Sections de cisaillement
Energy directors

© 2012 COVIDIEN ALL RIGHTS RESERVED.

PROPRIETARY & CONFIDENTIAL. THIS DOCUMENT MAY NOT BE COPIED, DISCLOSED, OR

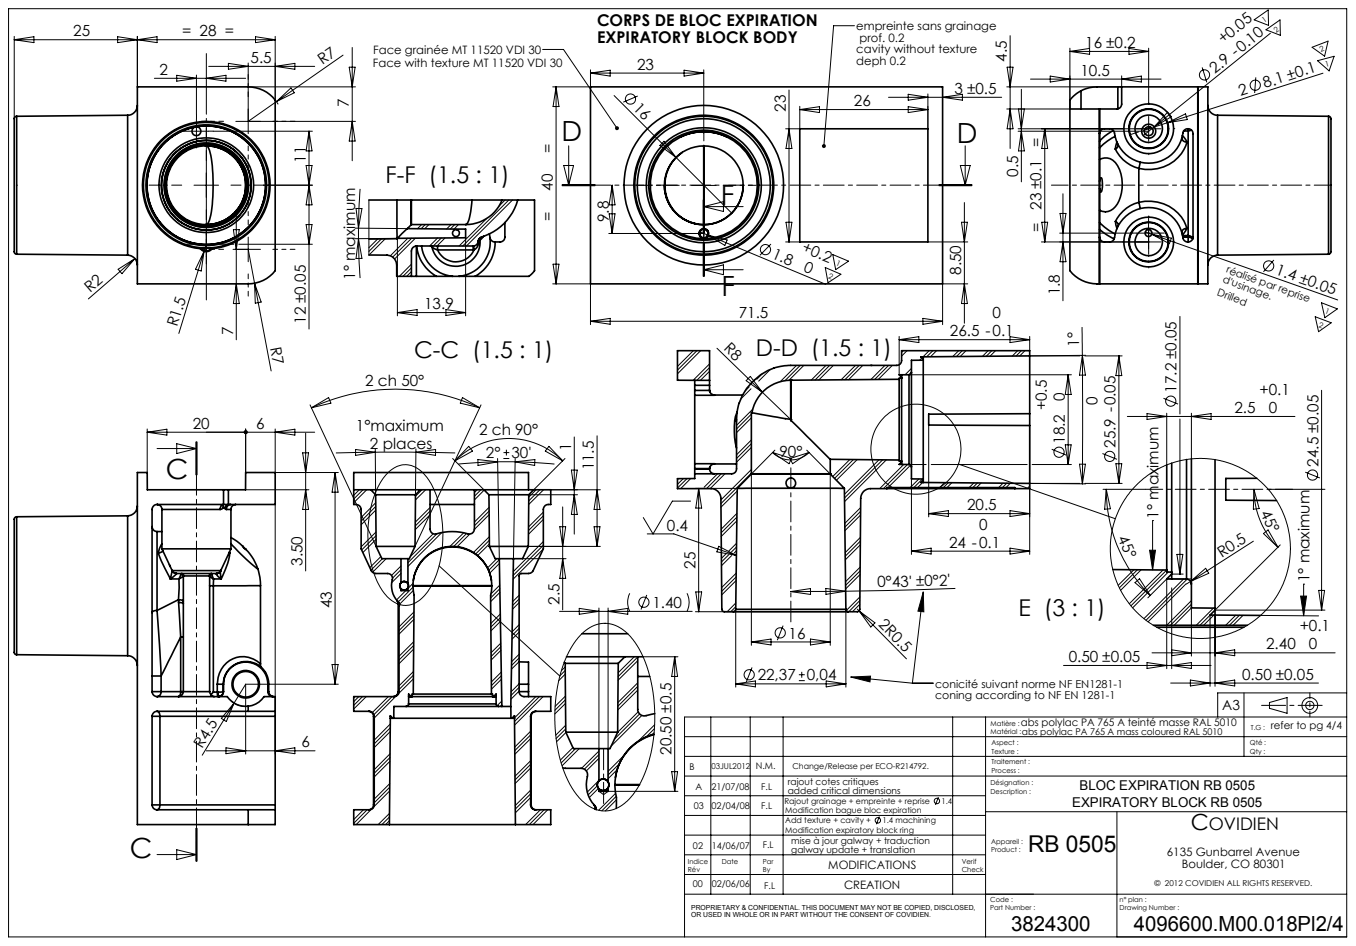
[picture p258: page 2]
6135 Gunbarrel Avenue Boulder, CO 80301; 2 places; 1° maximum; Texture :; Qty :; Qté :; Process :; Product :; Description :; Matérial :; 03JUL2012 N.M.; Change/Release per ECO-R214792.; Appareil :; Désignation :; Traitement :; Aspect :; Matière :; refer to pg 4/4

CORPS DE BLOC EXPIRATION
EXPIRATORY BLOCK BODY

empreinte sans grainage
prof. 0.2
cavity without texture
deph 0.2

Face grainée MT 11520 VDI 30
Face with texture MT 11520 VDI 30

réalisé par reprise

conicité suivant norme NF EN1281-1
coning according to NF EN 1281-1

abs polylac PA 765 A teinté masse RAL 5010
abs polylac PA 765 A mass coloured RAL 5010

rajout cotes critiques A 21/07/08 F.L
Rajout grainage + empreinte + reprise 1.4 03 02/04/08 F.L

added critical dimensions
Modification bague bloc expiration
Add texture + cavity + 1.4 machining
Modification expiratory block ring
galway update + translation

BLOC EXPIRATION RB 0505
EXPIRATORY BLOCK RB 0505

mise à jour galway + traduction 02 14/06/07 F.L

PROPRIETARY & CONFIDENTIAL. THIS DOCUMENT MAY NOT BE COPIED, DISCLOSED,
OR USED IN WHOLE OR IN PART WITHOUT THE CONSENT OF COVIDIEN.

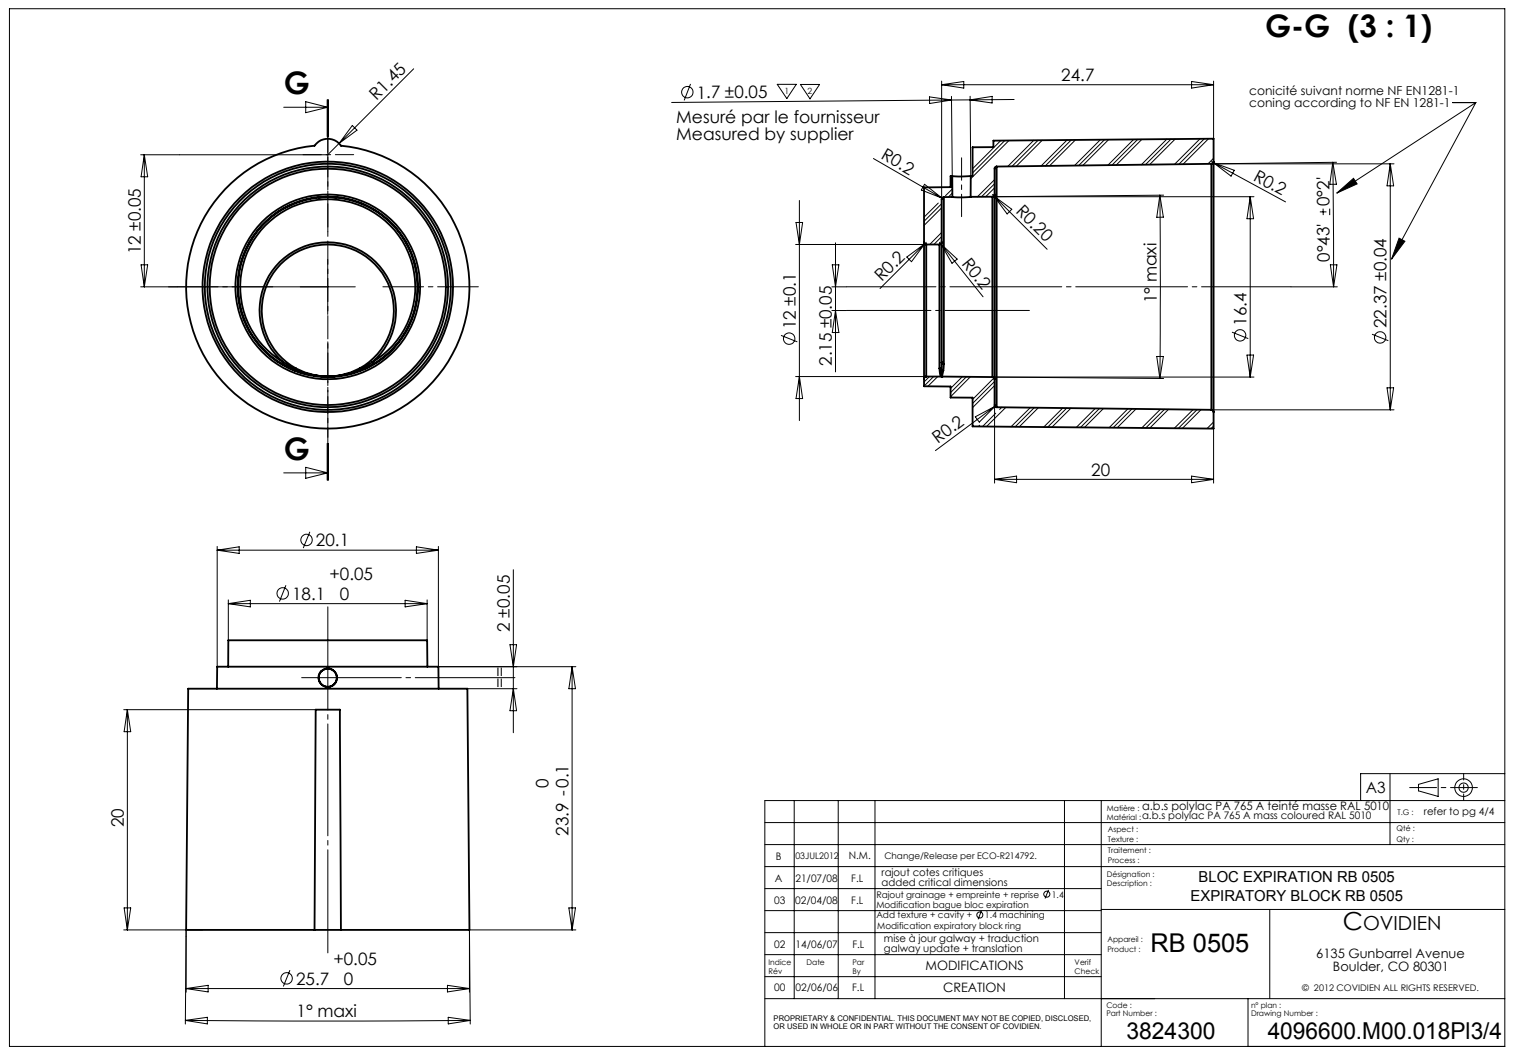
[picture p259: page 3]
6135 Gunbarrel Avenue Boulder, CO 80301; 1° maxi; Texture :; Qty :; Qté :; Process :; Product :; Description :; Matérial :; Appareil :; Désignation :; Traitement :; Aspect :; Matière :; refer to pg 4/4

Mesuré par le fournisseur
Measured by supplier

conicité suivant norme NF EN1281-1
coning according to NF EN 1281-1

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

added critical dimensions
Rajout grainage + empreinte + reprise 1.4
Modification bague bloc expiration
Add texture + cavity + 1.4 machining
Modification expiratory block ring
galway update + translation

BLOC EXPIRATION RB 0505
EXPIRATORY BLOCK RB 0505

mise à jour galway + traduction 02 14/06/07 F.L

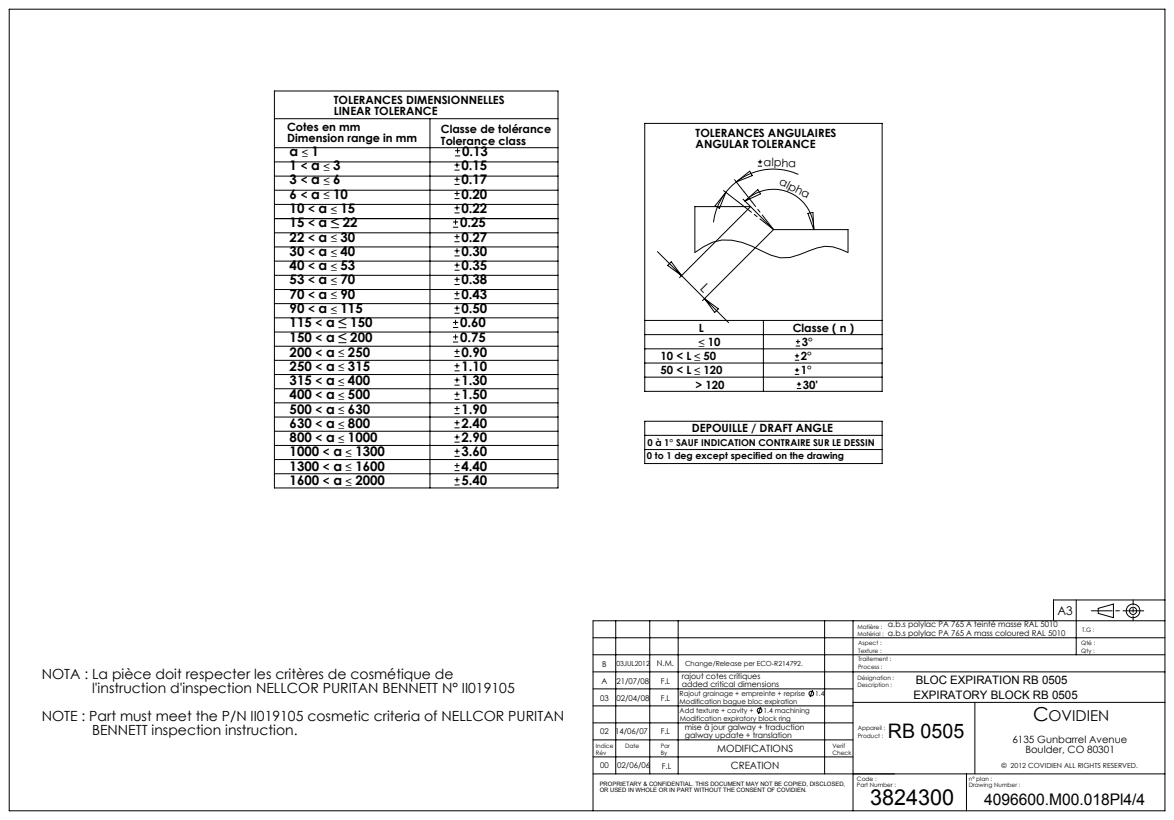
[picture p260: page 4]
L Classe ( n ); TOLERANCES ANGULAIRES ANGULAR TOLERANCE; 6135 Gunbarrel Avenue Boulder, CO 80301; Matière :; Aspect :; Traitement :; Désignation :; Appareil :; mise à jour galway + traduction; Matérial :; Description :; Product :; Process :; Qté : Qty :; Texture :

TOLERANCES DIMENSIONNELLES
LINEAR TOLERANCE
Cotes en mm
Dimension range in mm

Classe de tolérance
Tolerance class

DEPOUILLE / DRAFT ANGLE

0 à 1° SAUF INDICATION CONTRAIRE SUR LE DESSIN
0 to 1 deg except specified on the drawing

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

B 03JUL2012 N.M. Change/Release per ECO-R214792.
A 21/07/08 F.L rajout cotes critiques

NOTA : La pièce doit respecter les critères de cosmétique de
l'instruction d'inspection NELLCOR PURITAN BENNETT N° II019105
NOTE : Part must meet the P/N II019105 cosmetic criteria of NELLCOR PURITAN
BENNETT inspection instruction.

added critical dimensions

BLOC EXPIRATION RB 0505
EXPIRATORY BLOCK RB 0505

03 02/04/08 F.L Rajout grainage + empreinte + reprise 1.4

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
