L0op/medtronic-pb560/file-set-2/Mechanical Part Drawings/10047943/10047943A01.pdf

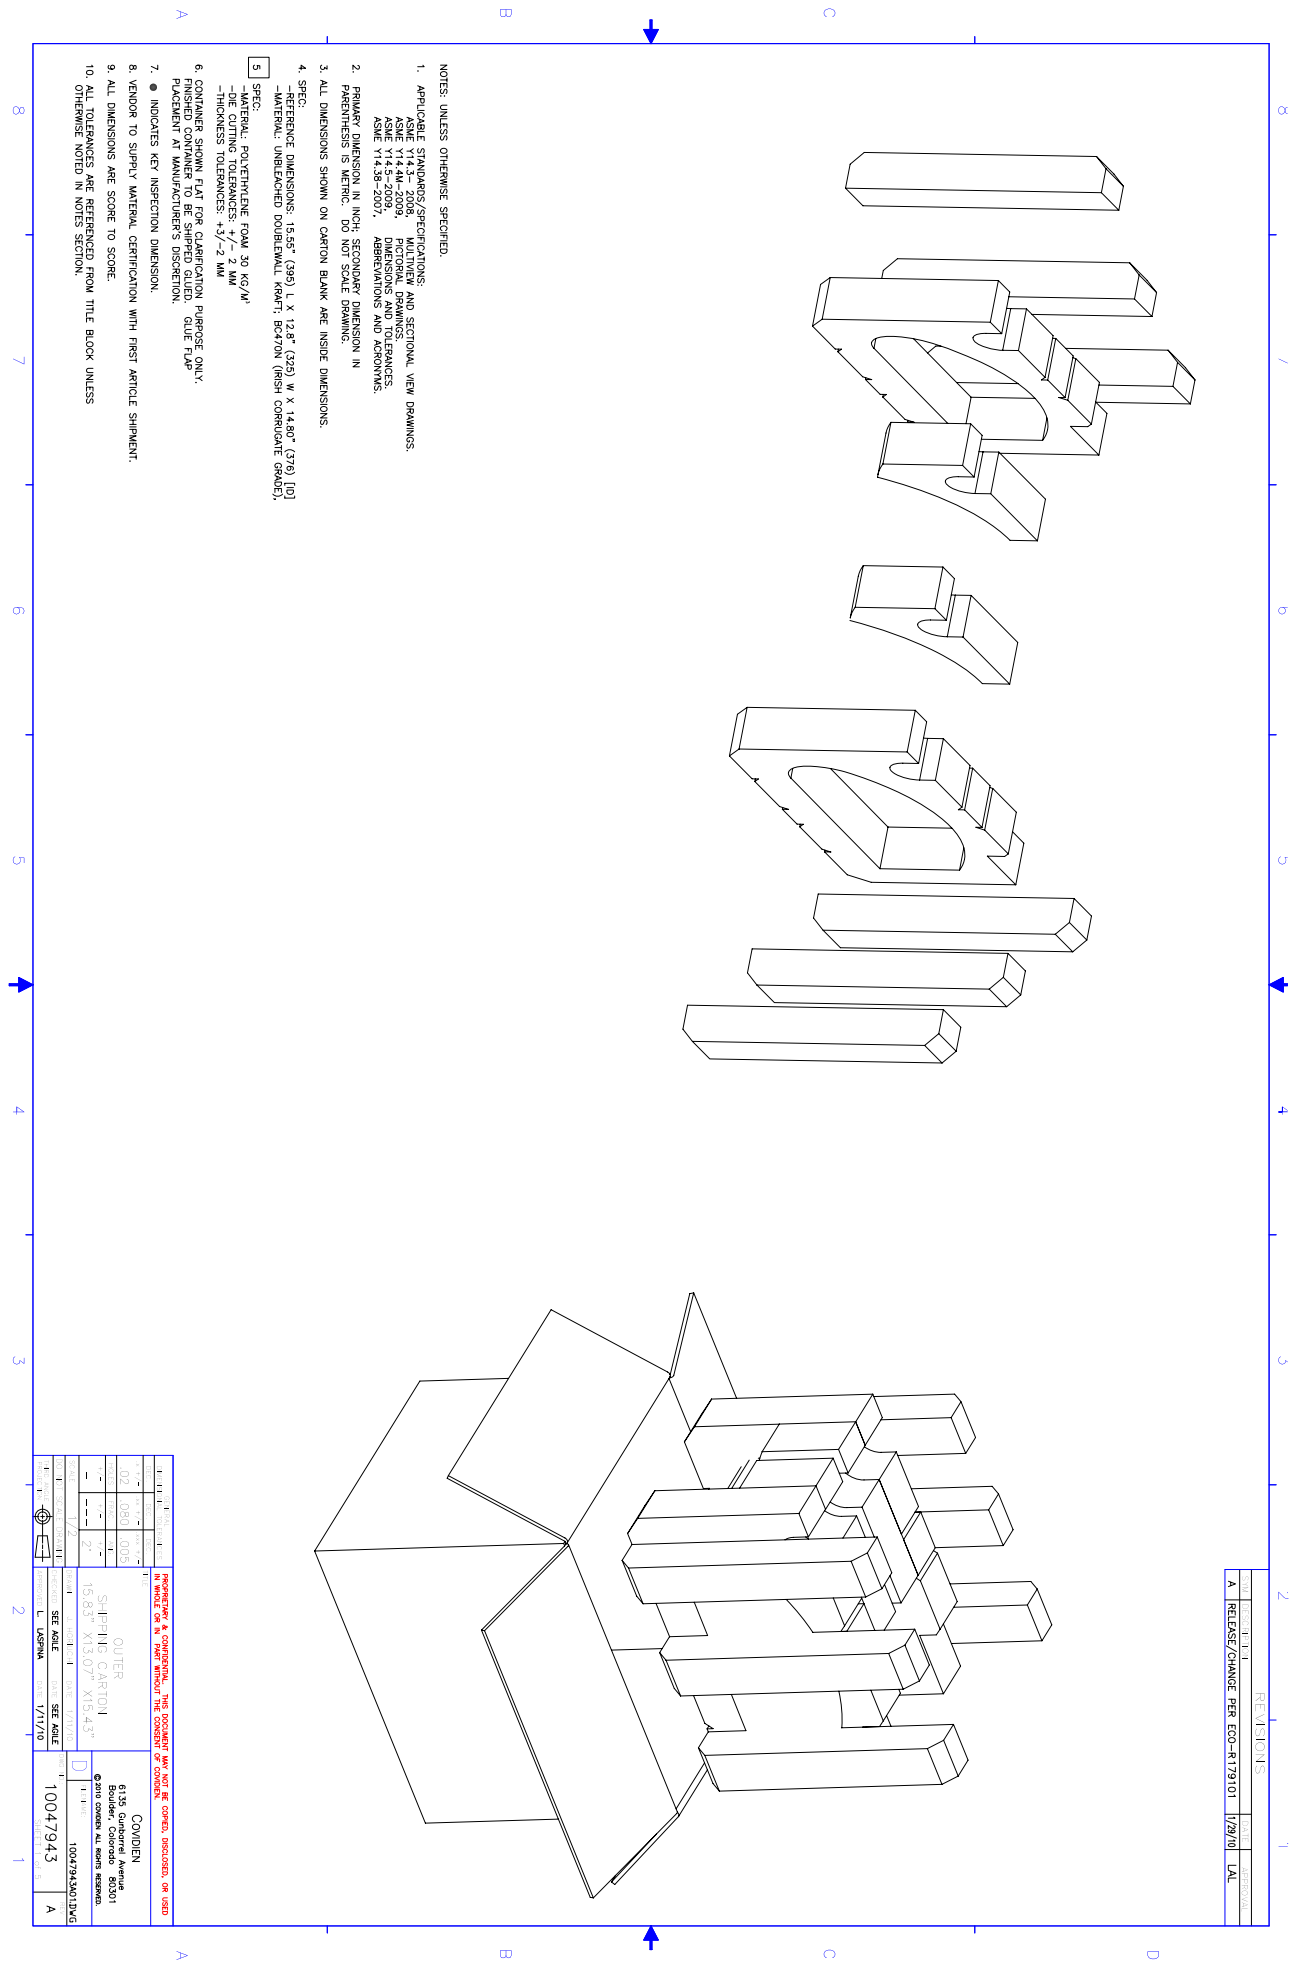
[picture p261: page 1]
