L0op/medtronic-pb560/file-set-2/Mechanical Part Drawings/10047943/10047943A02.pdf

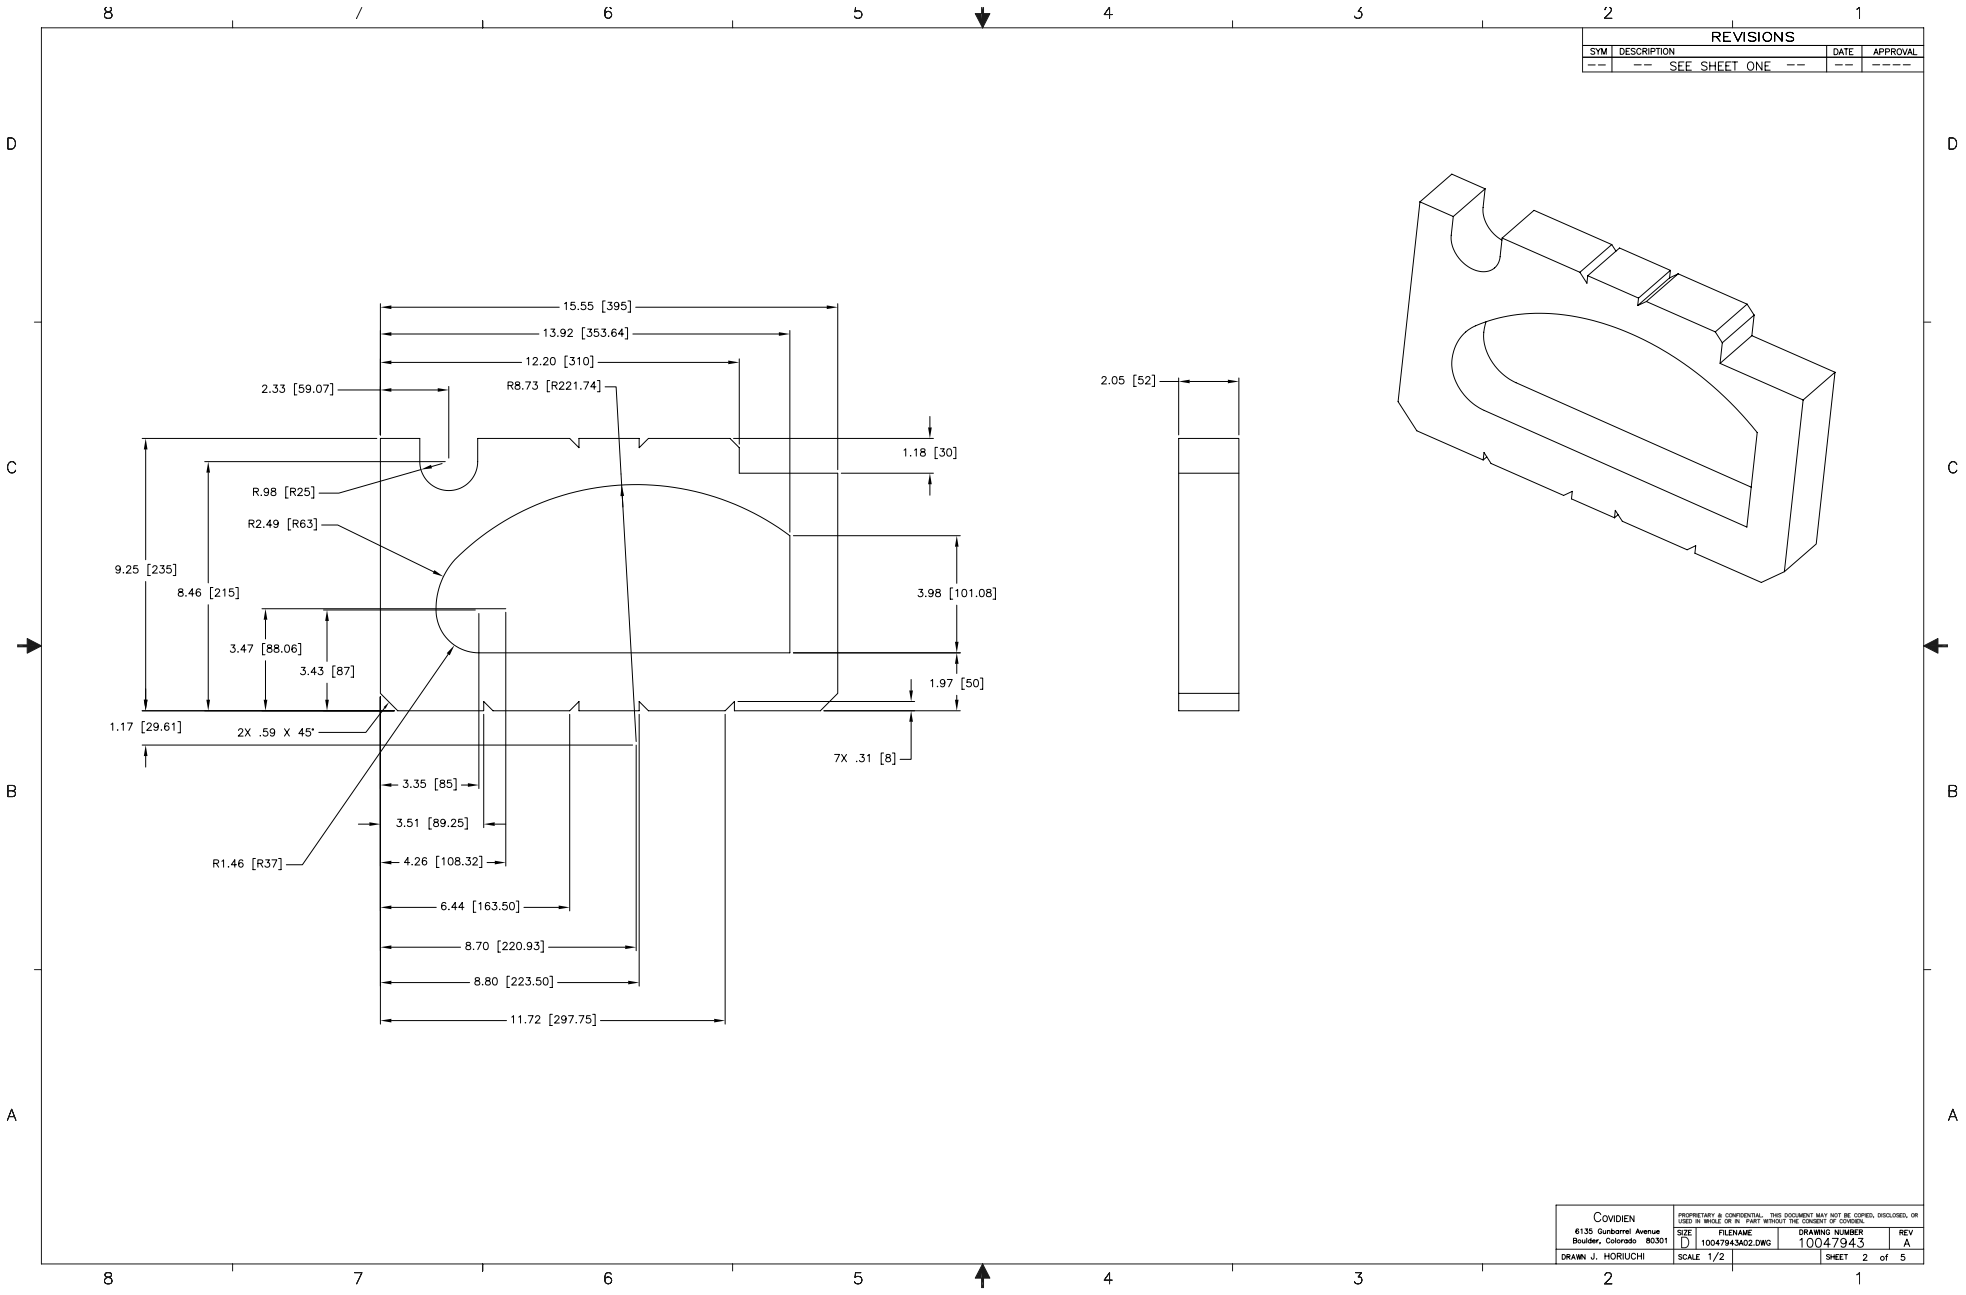
[picture p262: page 1]
