L0op/medtronic-pb560/file-set-2/Mechanical Part Drawings/10047943/10047943A03.pdf

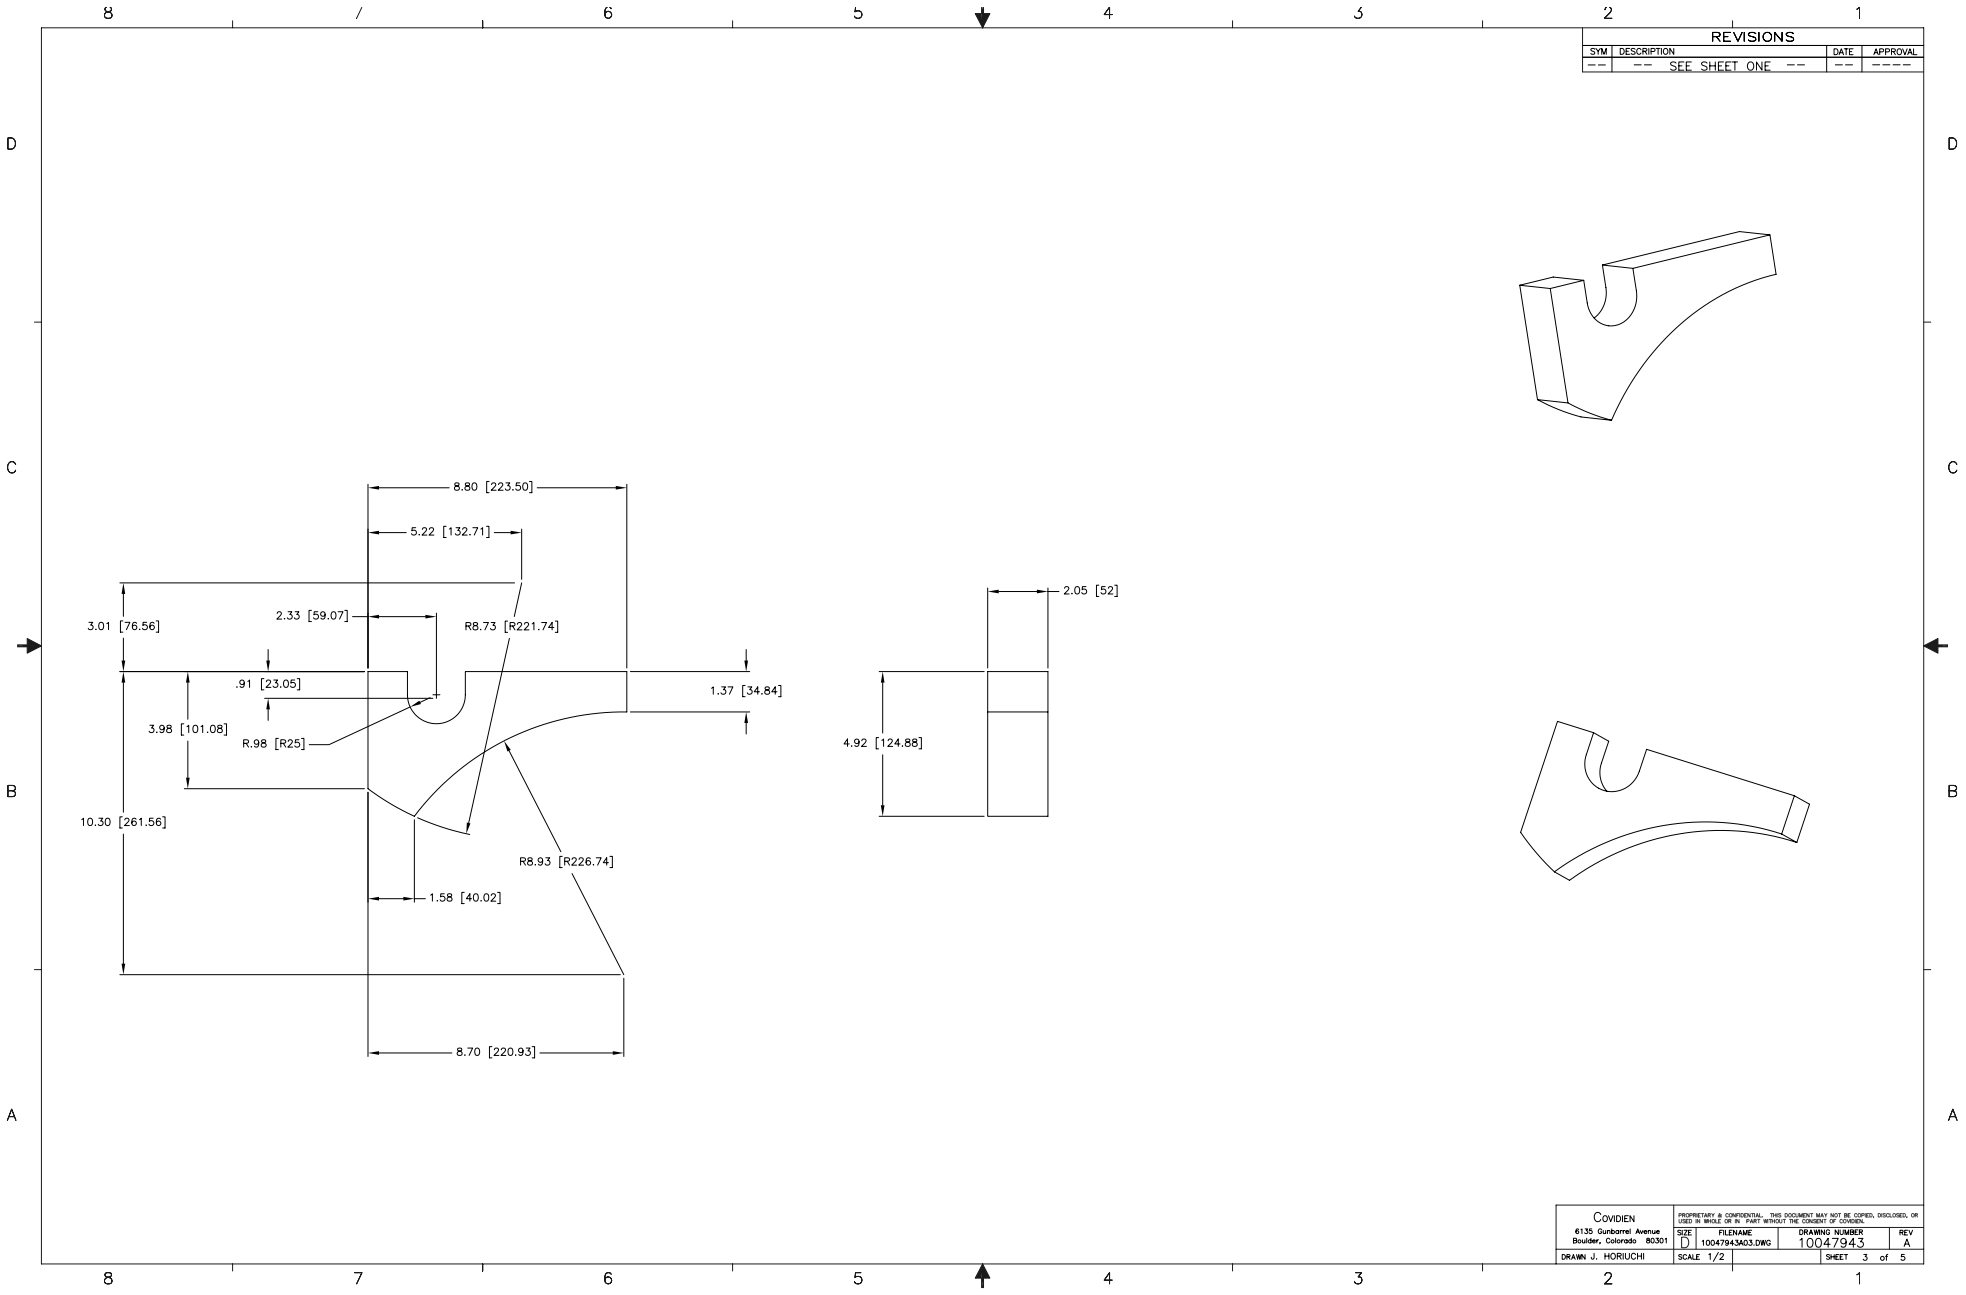
[picture p263: page 1]
