L0op/medtronic-pb560/file-set-2/Mechanical Part Drawings/10047943/10047943A04.pdf

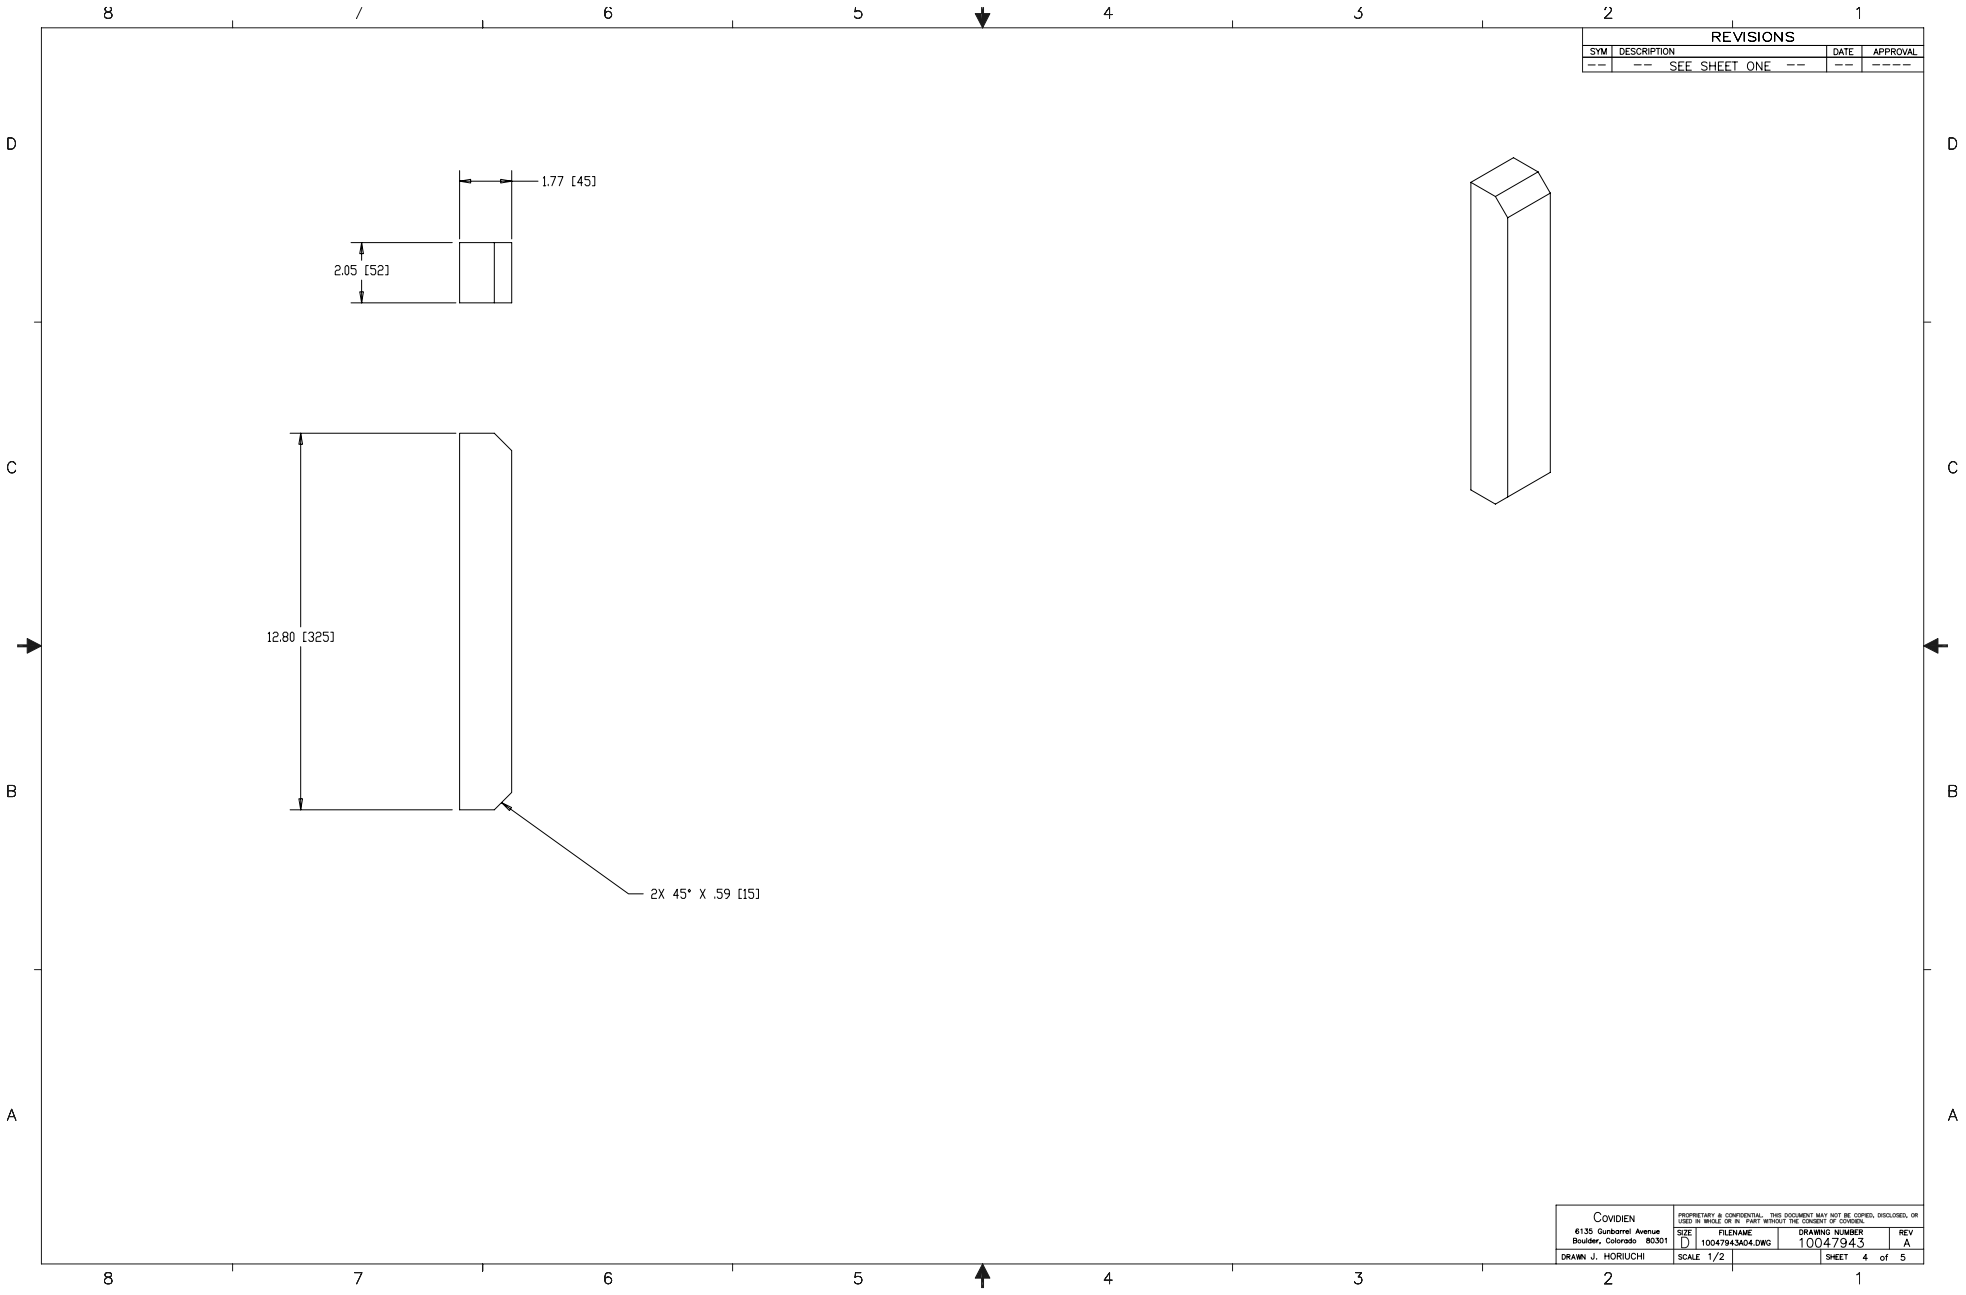
[picture p264: page 1]
