L0op/medtronic-pb560/file-set-2/Mechanical Part Drawings/10047943/10047943A05.pdf

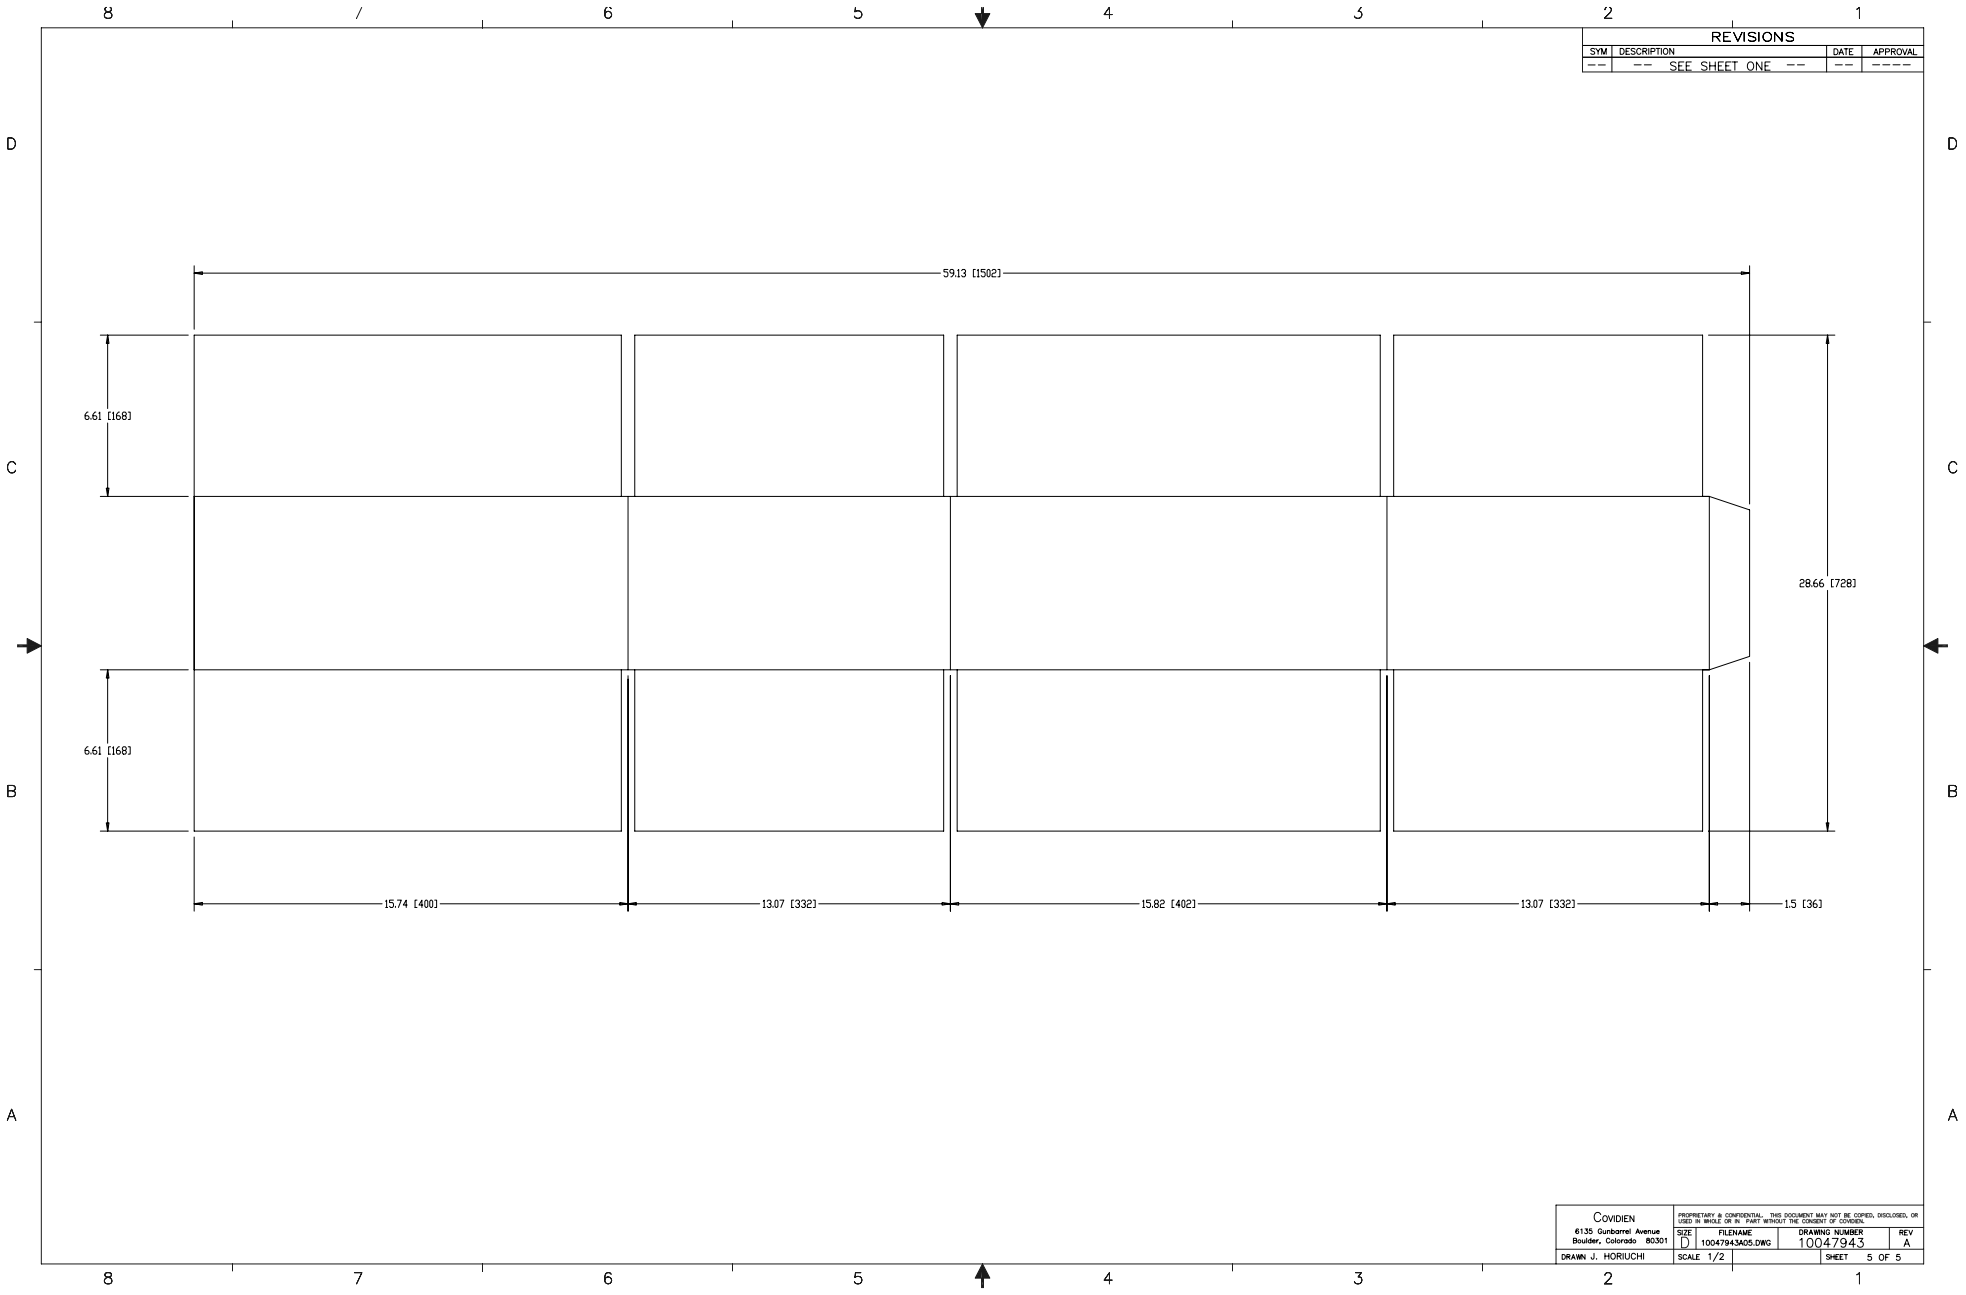
[picture p265: page 1]
