L0op/medtronic-pb560/file-set-2/Electronic PCBAs/GR106768_Buzzer_PCBA/SCH/10125624A00.sch

## EAGLE design file-set-2/Electronic PCBAs/GR106768_Buzzer_PCBA/SCH/10125624A00.sch (2020-04-01)

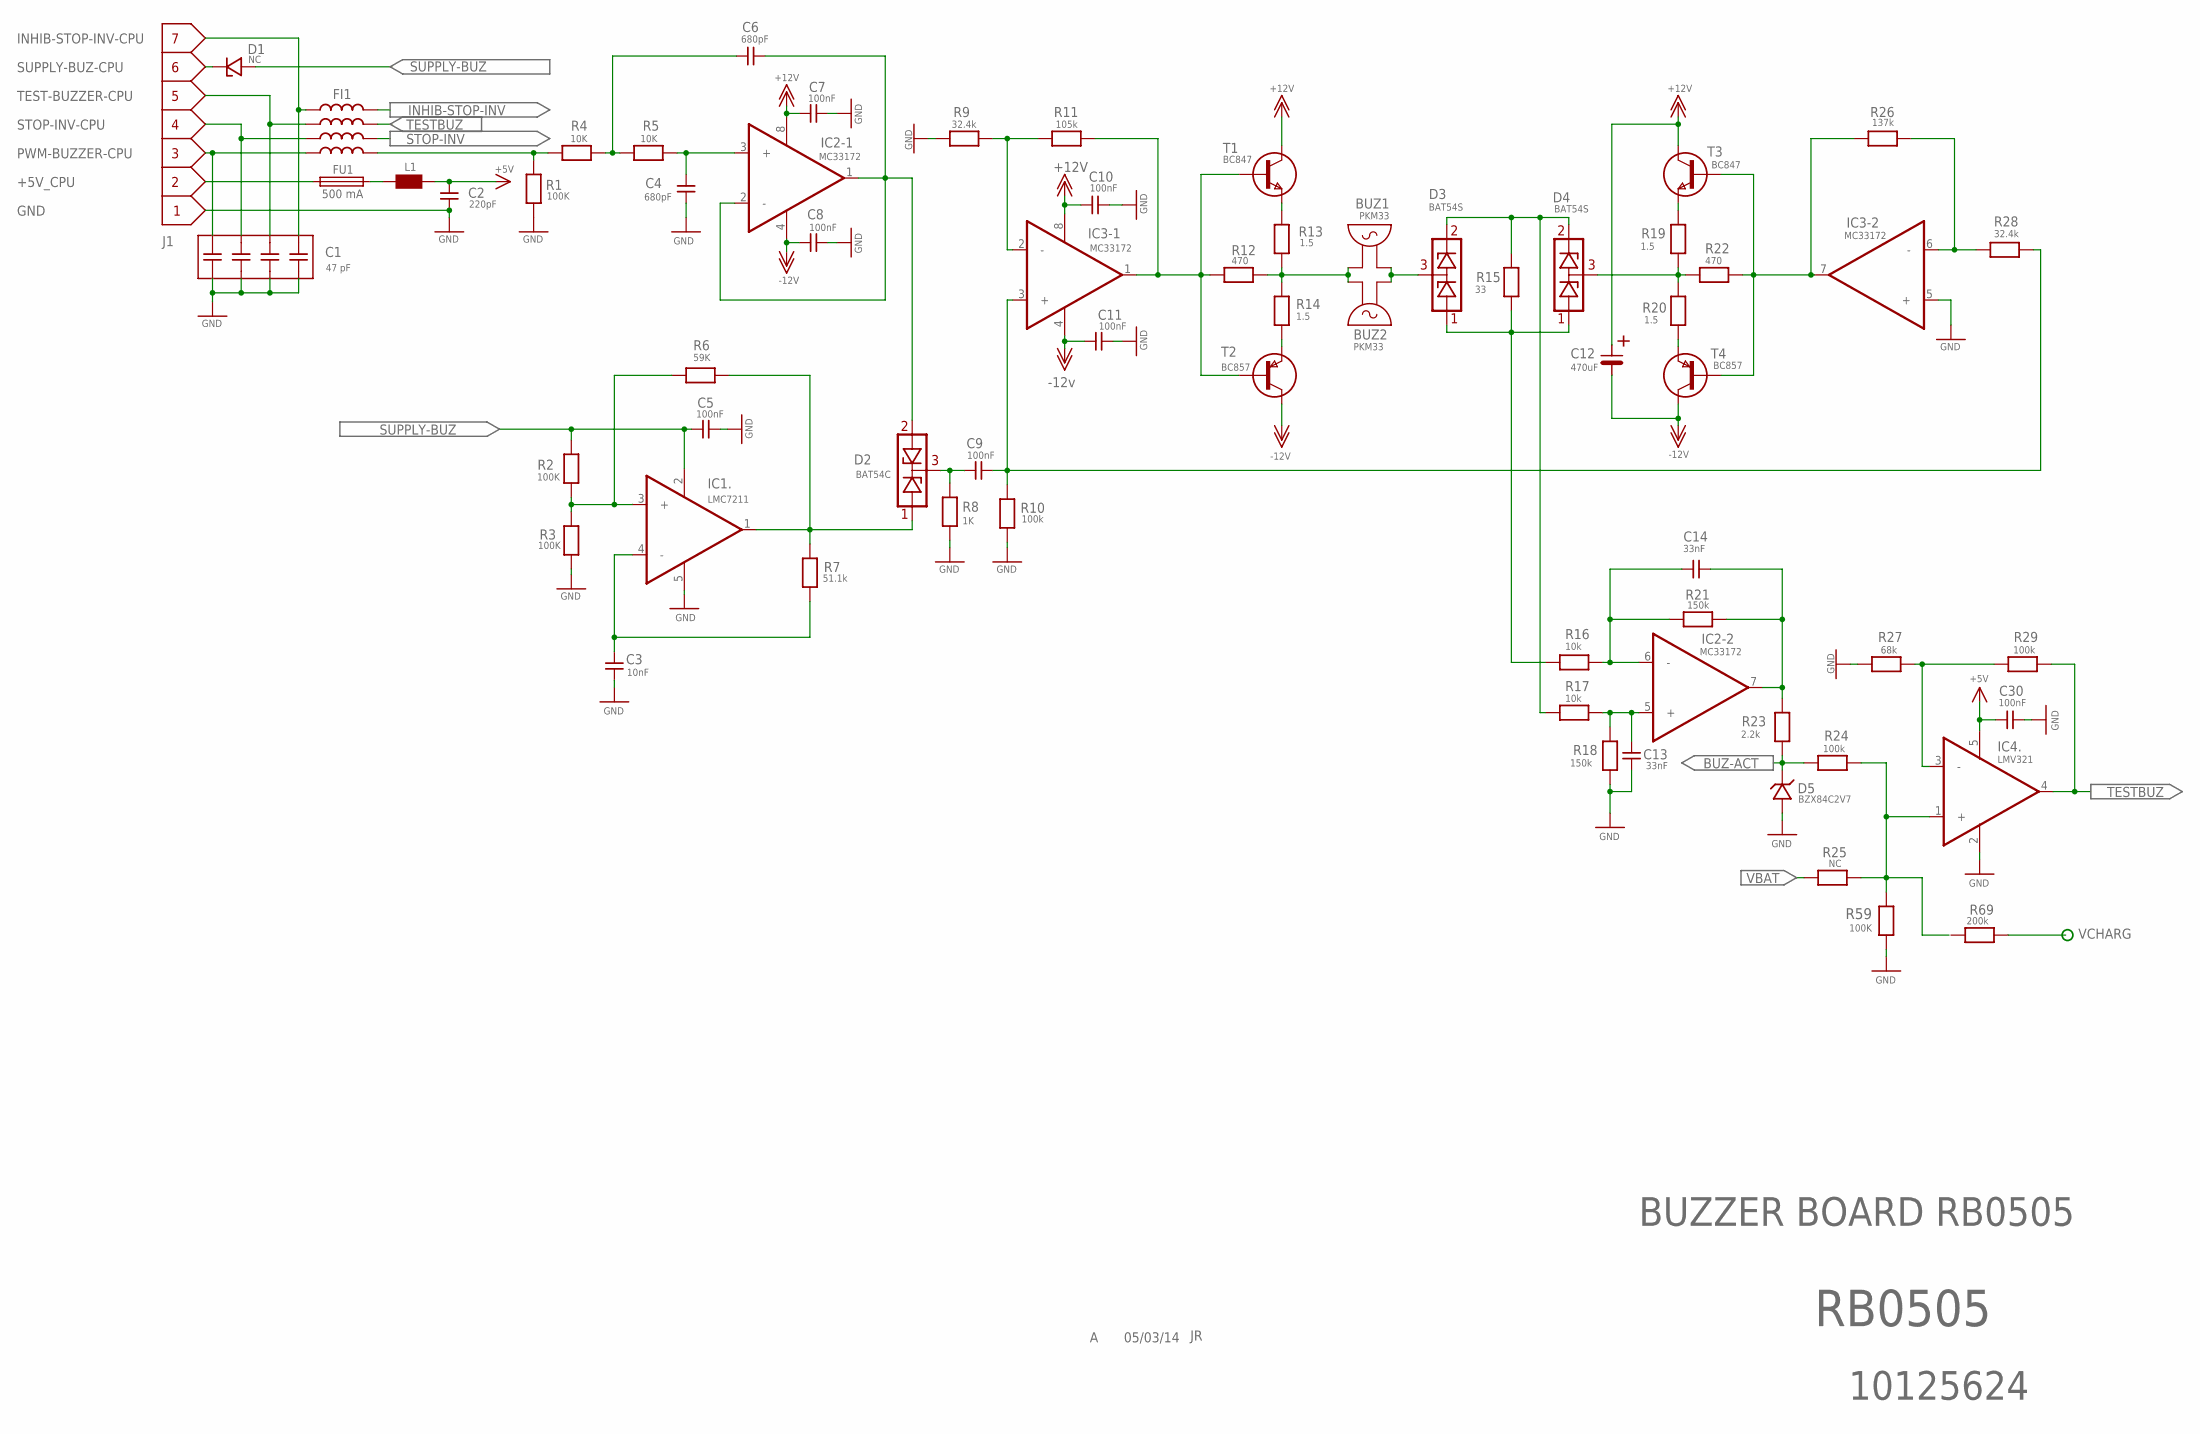
[picture p267: schematic 10125624A00.sch, sheet 1]

Parts:
BUZ1, BUZ2: PKM33
C1: 47 pF; RESEAU_1
C2: 220pF; C0805
C3: 10nF; C0805
C4, C6: 680pF; C0603
C5, C9, C30: 100nF; C0805
C7, C8, C10, C11: 100nF; C0603
C12: 470uF; MV100?F
C13, C14: 33nF; C0805
D1: NC; SOD87
D2: BAT54C; SOT23_DI
D3, D4: BAT54S; SOT23DIO
D5: BZX84C2V7; SOT23DIO
FI1: WE-FA
FU1: 500 mA; SLOBLO
IC1: LMC7211; SOT23-5
IC2, IC3: MC33172; SO8
IC4: LMV321; SOT23-5
J1: B7B_ZR_SM3_TF; 7B_ZR_SM3_TF
L1: 742792; 0805
R1, R2, R3, R59: 100K; R0805
R4, R5: 10K; R0805
R6: 59K; R0805
R7: 51.1k; R0805
R8: 1K; R0805
R9, R28: 32.4k; R0805
R10, R24, R29: 100k; R0805
R11: 105k; R0805
R12, R22: 470; R0805
R13, R14, R19, R20: 1.5; R0805
R15: 33; R0805
R16, R17: 10k; R0805
R18, R21: 150k; R0805
R23: 2.2k; R0805
R25: NC; R0805
R26: 137k; R0805
R27: 68k; R0805
R69: 200k; R0805
T1, T3: BC847; SOT23
T2, T4: BC857; SOT23

Connections:
+5V: C2.2, C30.1, IC4.5 (VCC), L1.2
+5V_CPU: FU1.1, J1.2
+12V: C7.1, C10.2, C12.+, IC2.8 (VCC), IC3.8 (VCC), T1.C, T3.C
-12V: C8.1, C11.2, C12.-, IC2.4 (GND), IC3.4 (GND), T2.C, T4.C
BUZ-ACT: D5.3 (K), R23.2, R24.2
GND: C1.1, C1.2, C1.3, C1.4, C2.1, C3.1, C4.2, C5.2, C7.2, C8.2, C10.1, C11.1, C13.2, C30.2, D5.1 (A), IC1.5 (GND), IC3.5 (+), IC4.2 (GND), J1.1, R1.1, R3.1, R8.2, R9.1, R10.1, R18.1, R27.2, R59.1
INHIB-STOP-INV: FI1.L4A
INHIB-STOP-INV-CPU: C1.8, FI1.L4B, J1.7
unnamed: IC3.1 (OUT), R11.2, R12.1, T1.B, T2.B
unnamed: IC3.2 (-), R9.2, R11.1
unnamed: C9.2, D2.3, R8.1
unnamed: FU1.2, L1.1
unnamed: D4.3, R19.1, R20.2, R22.1
unnamed: C3.2, IC1.4 (-), R7.1
unnamed: IC3.6 (-), R26.2, R28.1
unnamed: IC1.3 (+), R2.1, R3.2, R6.1
unnamed: IC3.7 (OUT), R22.2, R26.1, T3.B, T4.B
unnamed: R19.2, T3.E
unnamed: R13.2, T1.E
unnamed: R14.1, T2.E
unnamed: R20.1, T4.E
unnamed: BUZ1.IN- (2), BUZ2.IN- (2), R12.2, R13.1, R14.2
unnamed: C9.1, IC3.3 (+), R10.2, R28.2
unnamed: D3.2, D4.2, R15.2, R17.1
unnamed: C14.1, IC2.6 (-), R16.2, R21.1
unnamed: C13.1, IC2.5 (+), R17.2, R18.2
unnamed: IC4.3 (-), R27.1, R29.2
unnamed: C14.2, IC2.7 (OUT), R21.2, R23.1
unnamed: D2.1, IC1.1 (OUT), R6.2, R7.2
unnamed: BUZ1.IN+ (1), BUZ2.IN+ (1), D3.3
unnamed: D3.1, D4.1, R15.1, R16.1
unnamed: C6.1, D2.2, IC2.1 (OUT), IC2.2 (-)
unnamed: C4.1, IC2.3 (+), R5.1
unnamed: C6.2, R4.1, R5.2
unnamed: IC4.1 (+), R24.1, R25.1, R59.2
PWM-BUZ: FI1.L1A, R1.2, R4.2
PWM-BUZZER-CPU: C1.5, FI1.L1B, J1.3
STOP-INV: FI1.L2A
STOP-INV-CPU: C1.6, FI1.L2B, J1.4
SUPPLY-BUZ: C5.1, D1.A, IC1.2 (VCC), R2.2
SUPPLY-BUZ-CPU: D1.K, J1.6
TEST-BUZZER-CPU: C1.7, FI1.L3B, J1.5
TESTBUZ: FI1.L3A, IC4.4 (OUT), R29.1
VBAT: R25.2
VCHARG: R69.1

Notes on the sheet:
RB0505
05/03/14
10125624
BUZZER BOARD RB0505

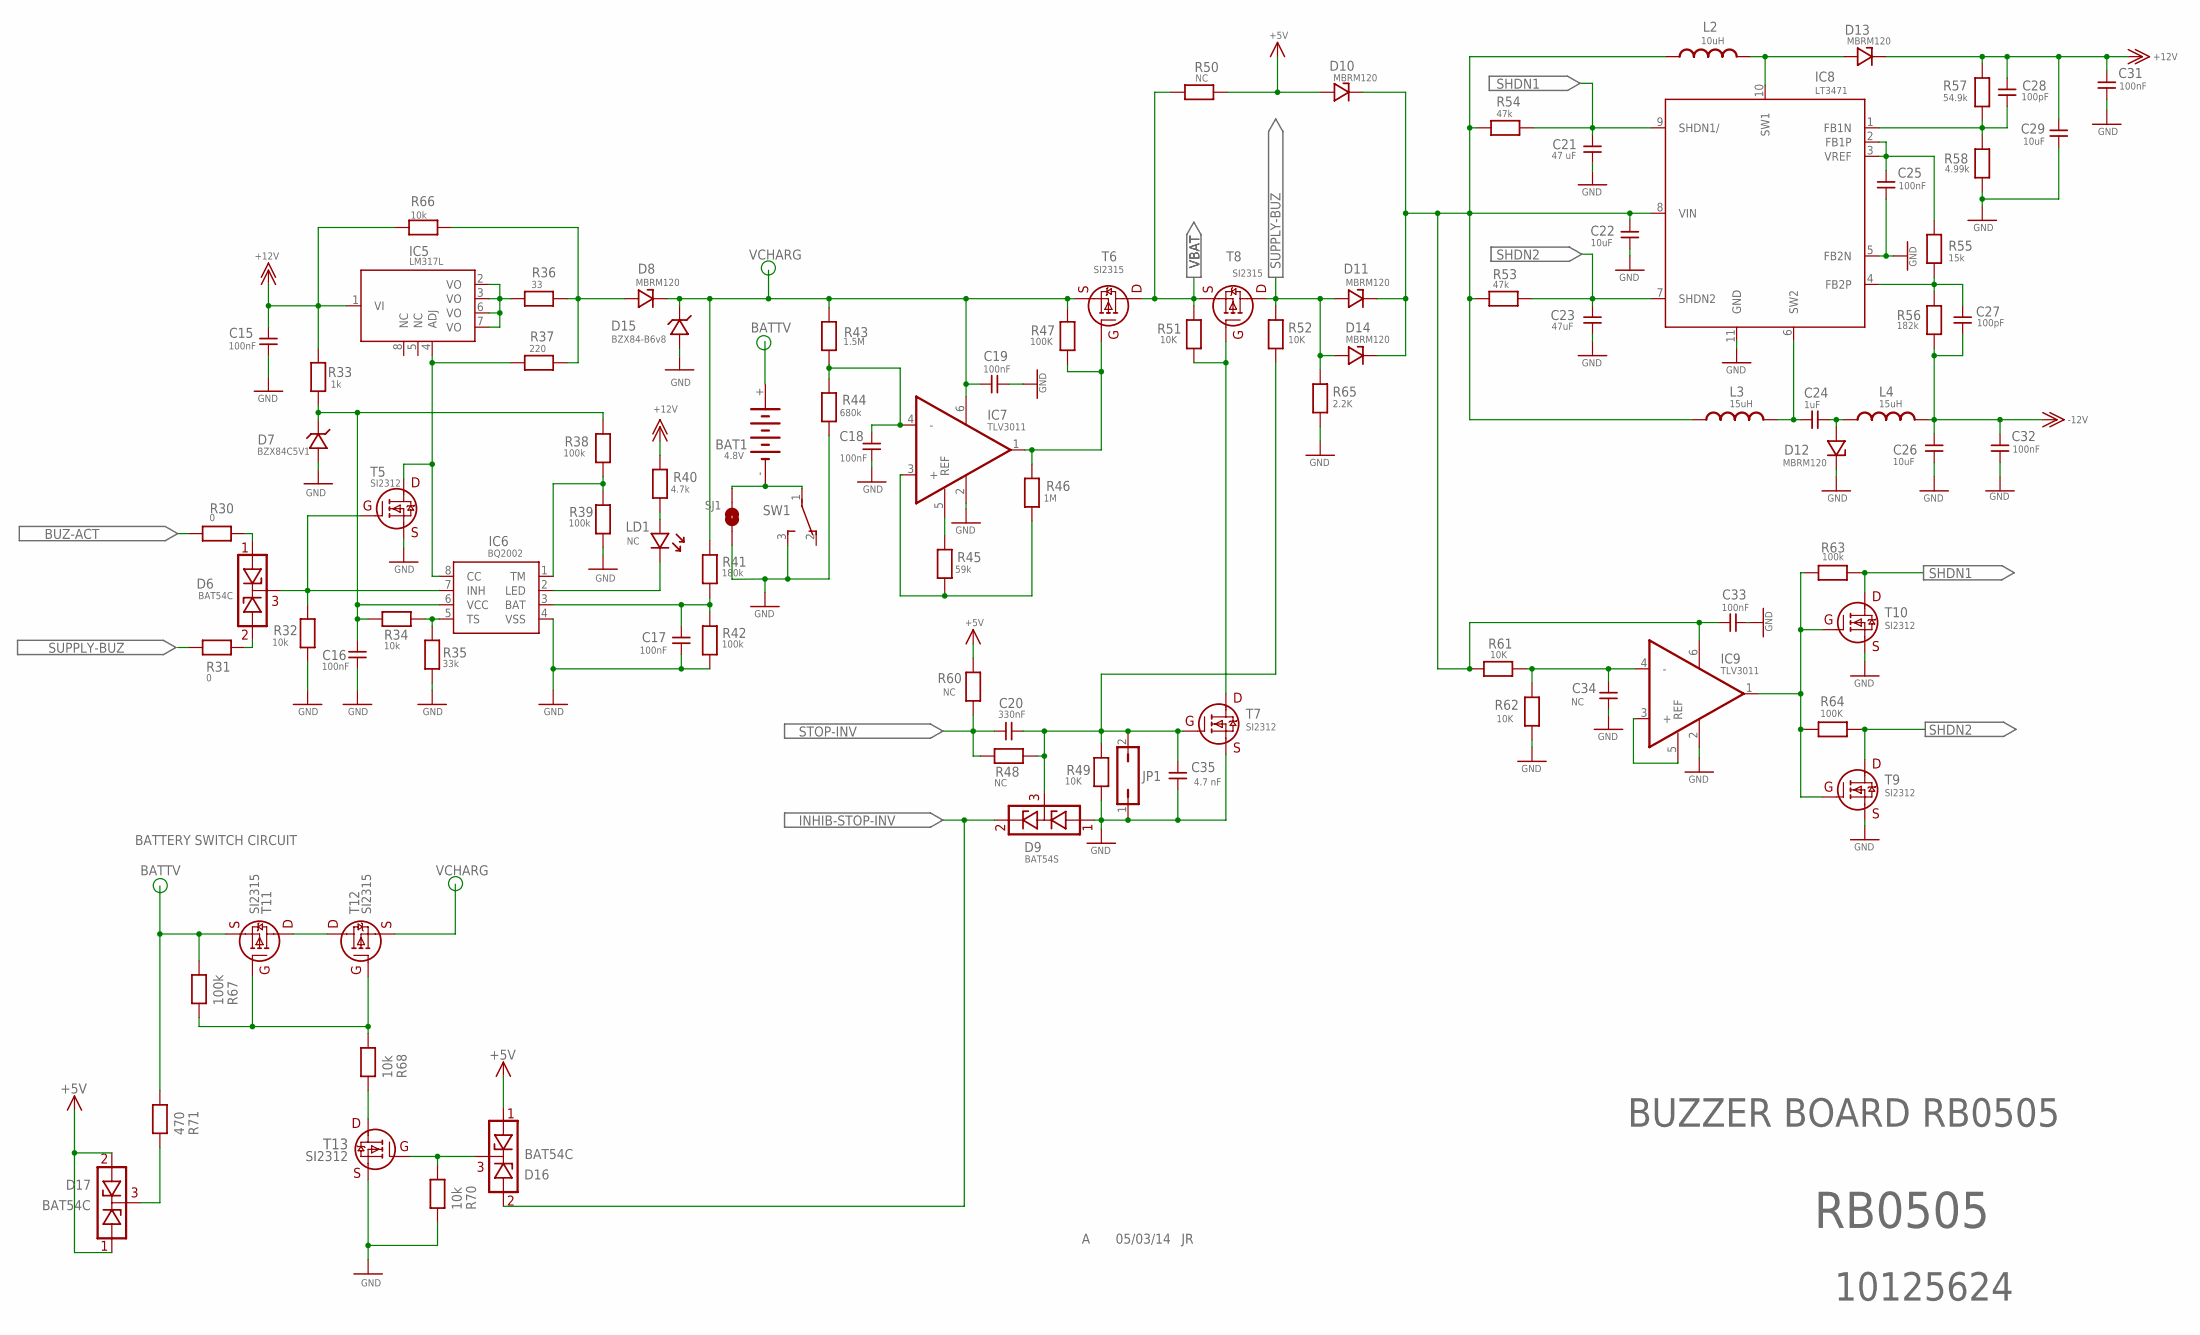
[picture p268: schematic 10125624A00.sch, sheet 2]

Parts:
BAT1: 4.8V; 4V110R
C15, C16, C17, C18, C19, C25, C31, C32, C33: 100nF; C0805
C20: 330nF; C0805
C21: 47 uF; C0805
C22, C26, C29: 10uF; C0805
C23: 47uF; C0805
C24: 1uF; C0805
C27, C28: 100pF; C0805
C34: NC; C0805
C35: 4.7 nF; C0805
D6, D16, D17: BAT54C; SOT23_DI
D7: BZX84C5V1; SOT23DIO
D8, D10, D11, D12, D13, D14: MBRM120; SOD87
D9: BAT54S; SOT23DIO
D15: BZX84-B6v8; SOT23DIO
IC5: LM317L; SO8
IC6: BQ2002; SO8
IC7, IC9: TLV3011; SOT23-6
IC8: LT3471; DFN10
JP1: JP1Q; JP1
L2: 10uH; WE-TPC-MH
L3, L4: 15uH; WE-TPC-MH
LD1: NC; LED3
R30, R31: 0; R0805
R32, R34, R66, R68, R70: 10k; R0805
R33: 1k; R0805
R35: 33k; R0805
R36: 33; R0805
R37: 220; R0805
R38, R39, R42, R63, R67: 100k; R0805
R40: 4.7k; R0805
R41: 180k; R0805
R43: 1.5M; R0805
R44: 680k; R0805
R45: 59k; R0805
R46: 1M; R0805
R47, R64: 100K; R0805
R48, R50, R60: NC; R0805
R49, R51, R52, R61, R62: 10K; R0805
R53, R54: 47k; R0805
R55: 15k; R0805
R56: 182k; R0805
R57: 54.9k; R0805
R58: 4.99k; R0805
R65: 2.2K; R0805
R71: 470; R0805
SJ1: SJW
SW1: NK236
T5, T7, T9, T10, T13: SI2312; SOT23MOS
T6, T8, T11, T12: SI2315; SOT23MOS

Connections:
+5V: D10.A, D16.1, D17.1, D17.2, R50.2, R60.2
+12V: C15.2, C28.2, C29.2, C31.2, D13.K, IC5.1 (VI), R33.2, R40.1, R57.1, R66.2
-12V: C26.1, C27.1, C32.2, L4.2, R56.2
BATTV: R67.2, R71.2, T11.S
BUZ-ACT: R30.1
GND: C15.1, C16.2, C17.1, C18.2, C19.2, C21.1, C22.2, C23.1, C25.1, C26.2, C29.1, C31.1, C32.1, C33.2, C34.1, C35.1, D7.1 (A), D9.1, D12.K, D15.1 (A), IC6.4 (VSS), IC7.2 (VSS), IC8.5 (FB2N), IC8.11 (GND), IC9.2 (VSS), JP1.1, R32.1, R35.1, R39.1, R42.2, R44.1, R49.1, R58.2, R62.1, R65.1, R70.1, SJ1.1, SW1.3, T5.S, T7.S, T9.S, T10.S, T13.S
GT1: C20.1, C35.2, D9.3, JP1.2, R48.2, R49.2, R52.1, T7.G
INHIB-STOP-INV: D9.2, D16.2
unnamed: IC5.2 (VO), IC5.3 (VO), IC5.6 (VO), IC5.7 (VO), R36.2
unnamed: D8.A, R36.1, R37.1, R66.1
unnamed: IC9.3 (+), IC9.5 (REF)
unnamed: C34.2, IC9.4 (-), R61.1, R62.2
unnamed: C22.1, C33.1, D10.K, D11.K, D14.K, IC8.8 (VIN), IC9.6 (VCC), L2.1, L3.1, R53.1, R54.1, R61.2
unnamed: BAT1.-, SJ1.2, SW1.1
unnamed: IC9.1 (OUT), R63.1, R64.1, T9.G, T10.G
unnamed: IC5.4 (ADJ), IC6.8 (CC), R37.2, T5.D
unnamed: T11.D, T12.D
unnamed: C17.2, IC6.3 (BAT), R41.2, R42.1
unnamed: D17.3, R71.1
unnamed: D6.3, IC6.7 (INH), R32.2, T5.G
unnamed: IC7.3 (+), R45.1, R46.1
unnamed: IC6.1 (TM), R38.1, R39.2
unnamed: R51.1, T7.D, T8.G
unnamed: D13.A, IC8.10 (SW1), L2.2
unnamed: R67.1, R68.2, T11.G, T12.G
unnamed: R68.1, T13.D
unnamed: C24.2, IC8.6 (SW2), L3.2
unnamed: C24.1, D12.A, L4.1
unnamed: C27.2, IC8.4 (FB2P), R55.2, R56.1
unnamed: D6.2, R31.2
unnamed: C25.2, IC8.2 (FB1P), IC8.3 (VREF), R55.1
unnamed: C28.1, IC8.1 (FB1N), R57.2, R58.1
unnamed: D6.1, R30.2
unnamed: D16.3, R70.2, T13.G
unnamed: IC6.5 (TS), R34.1, R35.2
unnamed: LD1.A, R40.2
unnamed: IC7.1 (OUT), R46.2, R47.1, T6.G
unnamed: C18.1, IC7.4 (-), R43.1, R44.2
unnamed: C16.1, D7.3 (K), IC6.6 (VCC), R33.1, R34.2, R38.2
unnamed: IC7.5 (REF), R45.2
unnamed: IC6.2 (LED), LD1.K
SHDN1: C21.2, IC8.9 (SHDN1/), R54.2, R63.2, T10.D
SHDN2: C23.2, IC8.7 (SHDN2), R53.2, R64.2, T9.D
STOP-INV: C20.2, R48.1, R60.1
SUPPLY-BUZ: D11.A, D14.A, R31.1, R52.2, R65.2, T8.D
VBAT: R50.1, R51.2, T6.D, T8.S
VCHARG: C19.1, D8.K, D15.3 (K), IC7.6 (VCC), R41.1, R43.2, R47.2, T6.S, T12.S

Notes on the sheet:
RB0505
05/03/14
10125624
BUZZER BOARD RB0505
BATTERY SWITCH CIRCUIT
