L0op/medtronic-pb560/file-set-2/Electronic PCBAs/GR106769_CPU_PCBA/SCH/10125623A00.sch

## EAGLE design file-set-2/Electronic PCBAs/GR106769_CPU_PCBA/SCH/10125623A00.sch (2020-04-01)

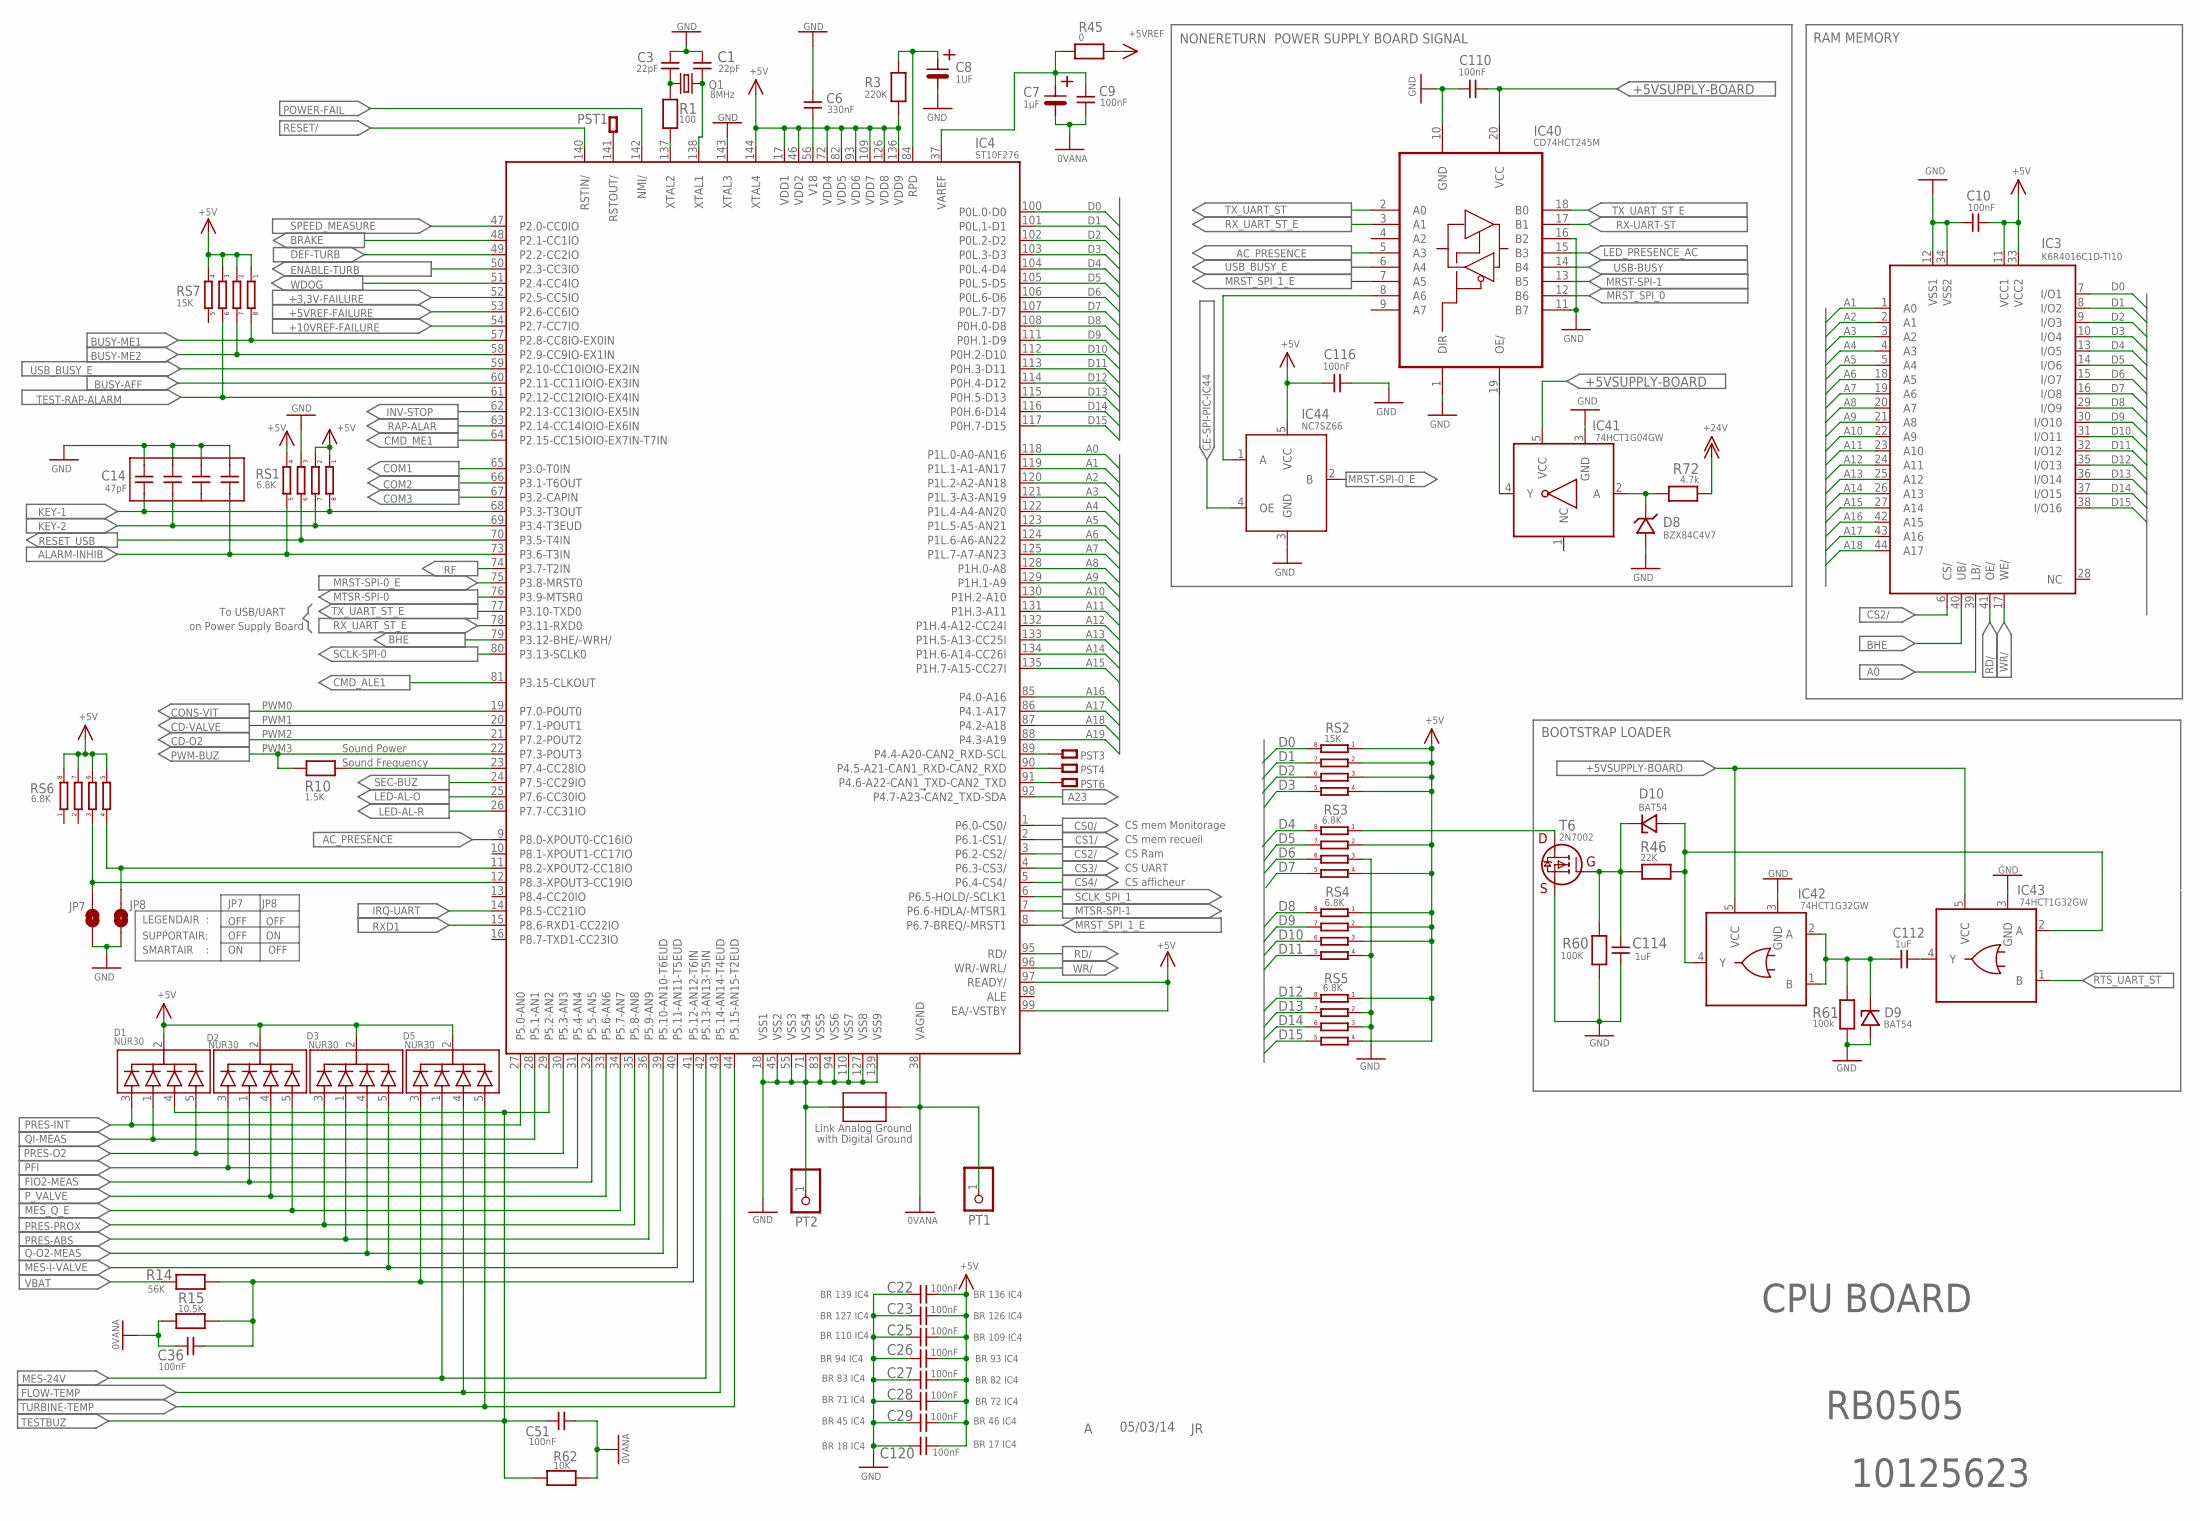
[picture p269: schematic 10125623A00.sch, sheet 1]

Parts:
C1, C3: 22pF; C0603
C6: 330nF; C0805
C7: 1µF; TANTALB
C8: 1UF; TANTALB
C9, C10, C22, C23, C25, C26, C27, C28, C29, C36, C51, C110, C116, C120: 100nF; C0805
C14: 47pF; RESEAU2
C112, C114: 1uF; C0603
D1, D2, D3, D5: NUR30; 5SOT23
D8: BZX84C4V7; SOT23DIO
D9, D10: BAT54; SOT23DIO
IC3: K6R4016C1D-TI10; TSOPIIZ4
IC4: ST10F276; TQFP144
IC40: CD74HCT245M; SO20
IC41: 74HCT1G04GW; SOT23-5
IC42, IC43: 74HCT1G32GW; SOT23-5
IC44: NC7SZ66; SOT23-5
JP7, JP8: JUMP_0U; 0805
JPL1: LIAISON_MASSES; LIAISONS_MASSES
PST1, PST3, PST4, PST6: PAST01; 1X01
PT1, PT2: PINHD-1X1; 1X01
Q1: 8MHz; SM49
R1: 100; R0805
R3: 220K; R0805
R10: 1.5K; R0805
R14: 56K; R0805
R15: 10.5K; R0805
R45: 0; R0805
R46: 22K; R0805
R60: 100K; R0805
R61: 100k; R0805
R62: 10K; R0805
R72: 4.7k; R0805
RS1, RS3, RS4, RS5, RS6: 6.8K; BCN16_4_
RS2, RS7: 15K; BCN16_4_
T6: 2N7002; SOT23MOS

Connections:
0VANA: C7.-, C9.1, C36.2, C51.2, IC4.38 (VAGND), JPL1.2, PT1.1, R15.1, R62.1
+3,3V-FAILURE: IC4.52 (P2.5-CC5IO)
+5V: C10.1, C22.2, C23.2, C25.2, C26.2, C27.2, C28.2, C29.2, C116.2, C120.2, D1.2, D2.2, D3.2, D5.2, IC3.11 (VCC1), IC3.33 (VCC2), IC4.17 (VDD1), IC4.46 (VDD2), IC4.72 (VDD4), IC4.82 (VDD5), IC4.93 (VDD6), IC4.97 (READY/), IC4.99 (EA/-VSTBY), IC4.109 (VDD7), IC4.126 (VDD8), IC4.136 (VDD9), IC4.144 (XTAL4), IC44.5 (VCC), R3.2, RS1.1, RS1.2, RS1.4, RS2.1, RS2.2, RS2.3, RS2.4, RS3.2, RS3.4, RS4.1, RS4.2, RS4.3, RS5.1, RS5.4, RS6.5, RS6.6, RS6.7, RS6.8, RS7.1, RS7.2, RS7.3, RS7.4
+5VREF: R45.2
+5VREF-FAILURE: IC4.53 (P2.6-CC6IO)
+5VSUPPLY-BOARD: C110.1, IC40.20 (VCC), IC41.5 (VCC), IC42.5 (VCC), IC43.5 (VCC)
+10VREF-FAILURE: IC4.54 (P2.7-CC7IO)
+24V: R72.1
A0: IC3.39 (LB/), IC4.118 (P1L.0-A0-AN16)
A1: IC3.1 (A0), IC4.119 (P1L.1-A1-AN17)
A2: IC3.2 (A1), IC4.120 (P1L.2-A2-AN18)
A3: IC3.3 (A2), IC4.121 (P1L.3-A3-AN19)
A4: IC3.4 (A3), IC4.122 (P1L.4-A4-AN20)
A5: IC3.5 (A4), IC4.123 (P1L.5-A5-AN21)
A6: IC3.18 (A5), IC4.124 (P1L.6-A6-AN22)
A7: IC3.19 (A6), IC4.125 (P1L.7-A7-AN23)
A8: IC3.20 (A7), IC4.128 (P1H.0-A8)
A9: IC3.21 (A8), IC4.129 (P1H.1-A9)
A10: IC3.22 (A9), IC4.130 (P1H.2-A10)
A11: IC3.23 (A10), IC4.131 (P1H.3-A11)
A12: IC3.24 (A11), IC4.132 (P1H.4-A12-CC24I)
A13: IC3.25 (A12), IC4.133 (P1H.5-A13-CC25I)
A14: IC3.26 (A13), IC4.134 (P1H.6-A14-CC26I)
A15: IC3.27 (A14), IC4.135 (P1H.7-A15-CC27I)
A16: IC3.42 (A15), IC4.85 (P4.0-A16)
A17: IC3.43 (A16), IC4.86 (P4.1-A17)
A18: IC3.44 (A17), IC4.87 (P4.2-A18)
A19: IC4.88 (P4.3-A19)
A23: IC4.92 (P4.7-A23-CAN2_TXD-SDA)
AC_PRESENCE: IC4.9 (P8.0-XPOUT0-CC16IO), IC40.5 (A3)
ALARM-INHIB: C14.8, IC4.73 (P3.6-T3IN), RS1.5
BHE: IC3.40 (UB/), IC4.79 (P3.12-BHE/-WRH/)
BLOAD: RS3.1, T6.D
BRAKE: IC4.48 (P2.1-CC1IO)
BUSY-AFF: IC4.60 (P2.11-CC11IOIO-EX3IN)
BUSY-ME1: IC4.57 (P2.8-CC8IO-EX0IN), RS7.8
BUSY-ME2: IC4.58 (P2.9-CC9IO-EX1IN), RS7.7
CD-O2: IC4.21 (P7.2-POUT2)
CD-VALVE: IC4.20 (P7.1-POUT1)
CE-SPI-PIC-IC44: IC44.4 (OE)
CMD_ALE1: IC4.81 (P3.15-CLKOUT)
CMD_ME1: IC4.64 (P2.15-CC15IOIO-EX7IN-T7IN)
COM1: IC4.65 (P3.0-T0IN)
COM2: IC4.66 (P3.1-T6OUT)
COM3: IC4.67 (P3.2-CAPIN)
CONS-VIT: IC4.19 (P7.0-POUT0)
CS0/: IC4.1 (P6.0-CS0/)
CS1/: IC4.2 (P6.1-CS1/)
CS2/: IC3.6 (CS/), IC4.3 (P6.2-CS2/)
CS3/: IC4.4 (P6.3-CS3/)
CS4/: IC4.5 (P6.4-CS4/)
D0: IC3.7 (I/O1), IC4.100 (P0L.0-D0), RS2.8
D1: IC3.8 (I/O2), IC4.101 (P0L.1-D1), RS2.7
D2: IC3.9 (I/O3), IC4.102 (P0L.2-D2), RS2.6
D3: IC3.10 (I/O4), IC4.103 (P0L.3-D3), RS2.5
D4: IC3.13 (I/O5), IC4.104 (P0L.4-D4), RS3.8
D5: IC3.14 (I/O6), IC4.105 (P0L.5-D5), RS3.7
D6: IC3.15 (I/O7), IC4.106 (P0L.6-D6), RS3.6
D7: IC3.16 (I/O8), IC4.107 (P0L.7-D7), RS3.5
D8: IC3.29 (I/O9), IC4.108 (P0H.0-D8), RS4.8
D9: IC3.30 (I/O10), IC4.111 (P0H.1-D9), RS4.7
D10: IC3.31 (I/O11), IC4.112 (P0H.2-D10), RS4.6
D11: IC3.32 (I/O12), IC4.113 (P0H.3-D11), RS4.5
D12: IC3.35 (I/O13), IC4.114 (P0H.4-D12), RS5.8
D13: IC3.36 (I/O14), IC4.115 (P0H.5-D13), RS5.7
D14: IC3.37 (I/O15), IC4.116 (P0H.6-D14), RS5.6
D15: IC3.38 (I/O16), IC4.117 (P0H.7-D15), RS5.5
DEF-TURB: IC4.49 (P2.2-CC2IO)
ENABLE-TURB: IC4.50 (P2.3-CC3IO)
FIO2-MEAS: D2.1 (3), IC4.32 (P5.5-AN5)
FLOW-TEMP: D5.4, IC4.43 (P5.14-AN14-T4EUD)
GND: C1.2, C3.2, C6.2, C8.-, C10.2, C14.1, C14.2, C14.3, C14.4, C22.1, C23.1, C25.1, C26.1, C27.1, C28.1, C29.1, C110.2, C114.1, C116.1, C120.1, D8.1 (A), D9.1 (A), IC3.12 (VSS1), IC3.34 (VSS2), IC4.18 (VSS1), IC4.45 (VSS2), IC4.55 (VSS3), IC4.71 (VSS4), IC4.83 (VSS5), IC4.94 (VSS6), IC4.110 (VSS7), IC4.127 (VSS8), IC4.139 (VSS9), IC4.143 (XTAL3), IC40.1 (DIR), IC40.10 (GND), IC40.11 (B7), IC40.16 (B2), IC41.3 (GND), IC42.3 (GND), IC43.3 (GND), IC44.3 (GND), JP7.1, JP8.1, JPL1.1, PT2.1, R60.1, R61.2, RS1.3, RS3.3, RS4.4, RS5.2, RS5.3, T6.S
INV-STOP: IC4.62 (P2.13-CC13IOIO-EX5IN)
IRQ-UART: IC4.14 (P8.5-CC21IO)
KEY-1: C14.5, IC4.68 (P3.3-T3OUT), RS1.8
KEY-2: C14.6, IC4.69 (P3.4-T3EUD), RS1.7
LED-AL-O: IC4.25 (P7.6-CC30IO)
LED-AL-R: IC4.26 (P7.7-CC31IO)
LED_PRESENCE_AC: IC40.15 (B3)
MES-24V: D5.1 (3), IC4.42 (P5.13-AN13-T5IN)
MES-I-VALVE: D3.5, IC4.40 (P5.11-AN11-T5EUD)
MES_Q_E: D2.5, IC4.34 (P5.7-AN7)
MRST-SPI-0_E: IC4.75 (P3.8-MRST0), IC44.2 (B)
MRST-SPI-1: IC40.13 (B5)
MRST_SPI_0: IC40.12 (B6)
MRST_SPI_1_E: IC4.8 (P6.7-BREQ/-MRST1), IC40.7 (A5)
MTSR-SPI-0: IC4.76 (P3.9-MTSR0)
MTSR-SPI-1: IC4.7 (P6.6-HDLA/-MTSR1)
unnamed: C3.1, Q1.1, R1.1
unnamed: IC4.137 (XTAL2), R1.2
unnamed: C8.+, IC4.84 (RPD), R3.1
unnamed: IC4.23 (P7.4-CC28IO), R10.2
unnamed: IC4.141 (RSTOUT/), PST1.1
unnamed: IC4.89 (P4.4-A20-CAN2_RXD-SCL), PST3.1
unnamed: IC4.90 (P4.5-A21-CAN1_RXD-CAN2_RXD), PST4.1
unnamed: IC4.91 (P4.6-A22-CAN1_TXD-CAN2_TXD), PST6.1
unnamed: C7.+, C9.2, IC4.37 (VAREF), R45.1
unnamed: C1.1, IC4.138 (XTAL1), Q1.2
unnamed: IC4.11 (P8.2-XPOUT2-CC18IO), JP8.2, RS6.4
unnamed: C36.1, D5.3 (1), IC4.41 (P5.12-AN12-T6IN), R14.2, R15.2
unnamed: IC4.12 (P8.3-XPOUT3-CC19IO), JP7.2, RS6.3
unnamed: D10.1 (A), IC42.4 (Y), IC43.2 (A), R46.2
unnamed: IC40.19 (OE/), IC41.4 (Y)
unnamed: D8.3 (K), IC41.2 (A), R72.2
unnamed: C112.2, IC43.4 (Y)
unnamed: C112.1, D9.3 (K), IC42.1 (B), IC42.2 (A), R61.1
unnamed: IC40.8 (A6), IC44.1 (A)
unnamed: C6.1, IC4.56 (V18)
unnamed: C114.2, D10.3 (K), R46.1, R60.2, T6.G
PFI: D2.3 (1), IC4.31 (P5.4-AN4)
POWER-FAIL: IC4.142 (NMI/)
PRES-ABS: D3.1 (3), IC4.36 (P5.9-AN9)
PRES-INT: D1.3 (1), IC4.27 (P5.0-AN0)
PRES-O2: D1.5, IC4.30 (P5.3-AN3)
PRES-PROX: D3.3 (1), IC4.35 (P5.8-AN8)
PWM-BUZ: IC4.22 (P7.3-POUT3), R10.1
P_VALVE: D2.4, IC4.33 (P5.6-AN6)
Q-O2-MEAS: D3.4, IC4.39 (P5.10-AN10-T6EUD)
QI-MEAS: D1.1 (3), IC4.28 (P5.1-AN1)
RAP-ALAR: IC4.63 (P2.14-CC14IOIO-EX6IN)
RD/: IC3.41 (OE/), IC4.95 (RD/)
RESET/: IC4.140 (RSTIN/)
RESET_USB: IC4.70 (P3.5-T4IN), RS1.6
RF: IC4.74 (P3.7-T2IN)
RTS_UART_ST: IC43.1 (B)
RX-UART-ST: IC40.17 (B1)
RXD1: IC4.15 (P8.6-RXD1-CC22IO)
RX_UART_ST_E: IC4.78 (P3.11-RXD0), IC40.3 (A1)
SCLK-SPI-0: IC4.80 (P3.13-SCLK0)
SCLK_SPI_1: IC4.6 (P6.5-HOLD/-SCLK1)
SEC-BUZ: IC4.24 (P7.5-CC29IO)
SPEED_MEASURE: IC4.47 (P2.0-CC0IO)
TEST-RAP-ALARM: IC4.61 (P2.12-CC12IOIO-EX4IN), RS7.6
TESTBUZ: C51.1, D1.4, IC4.29 (P5.2-AN2), R62.2
TURBINE-TEMP: D5.5, IC4.44 (P5.15-AN15-T2EUD)
TX_UART_ST: IC40.2 (A0)
TX_UART_ST_E: IC4.77 (P3.10-TXD0), IC40.18 (B0)
USB-BUSY: IC40.14 (B4)
USB_BUSY_E: IC4.59 (P2.10-CC10IOIO-EX2IN), IC40.6 (A4)
VBAT: R14.1
WDOG: IC4.51 (P2.4-CC4IO)
WR/: IC3.17 (WE/), IC4.96 (WR/-WRL/)

Notes on the sheet:
RAM MEMORY
BR 139 IC4
BR 127 IC4
BR 110 IC4
BR 94 IC4
BR 83 IC4
BR 71 IC4
BR 45 IC4
BR 136 IC4
BR 126 IC4
BR 109 IC4
BR 93 IC4
BR 82 IC4
BR 72 IC4
BR 46 IC4
Link Analog Ground
with Digital Ground
CPU BOARD
RB0505
CS afficheur
CS mem Monitorage
CS mem recueil
CS Ram
PWM0
PWM2
PWM3
Sound Frequency
Sound Power
10125623
BR 18 IC4
BR 17 IC4
CS UART
To USB/UART
on Power Supply Board
05/03/14
PWM1
JP7 JP8
SMARTAIR :
LEGENDAIR :
SUPPORTAIR:
OFF OFF
OFF ON
ON OFF
BOOTSTRAP LOADER
NONERETURN POWER SUPPLY BOARD SIGNAL
