L0op/medtronic-pb560/file-set-2/Electronic PCBAs/GR106769_CPU_PCBA/SCH/10125623A00.sch

## EAGLE design file-set-2/Electronic PCBAs/GR106769_CPU_PCBA/SCH/10125623A00.sch (continued)

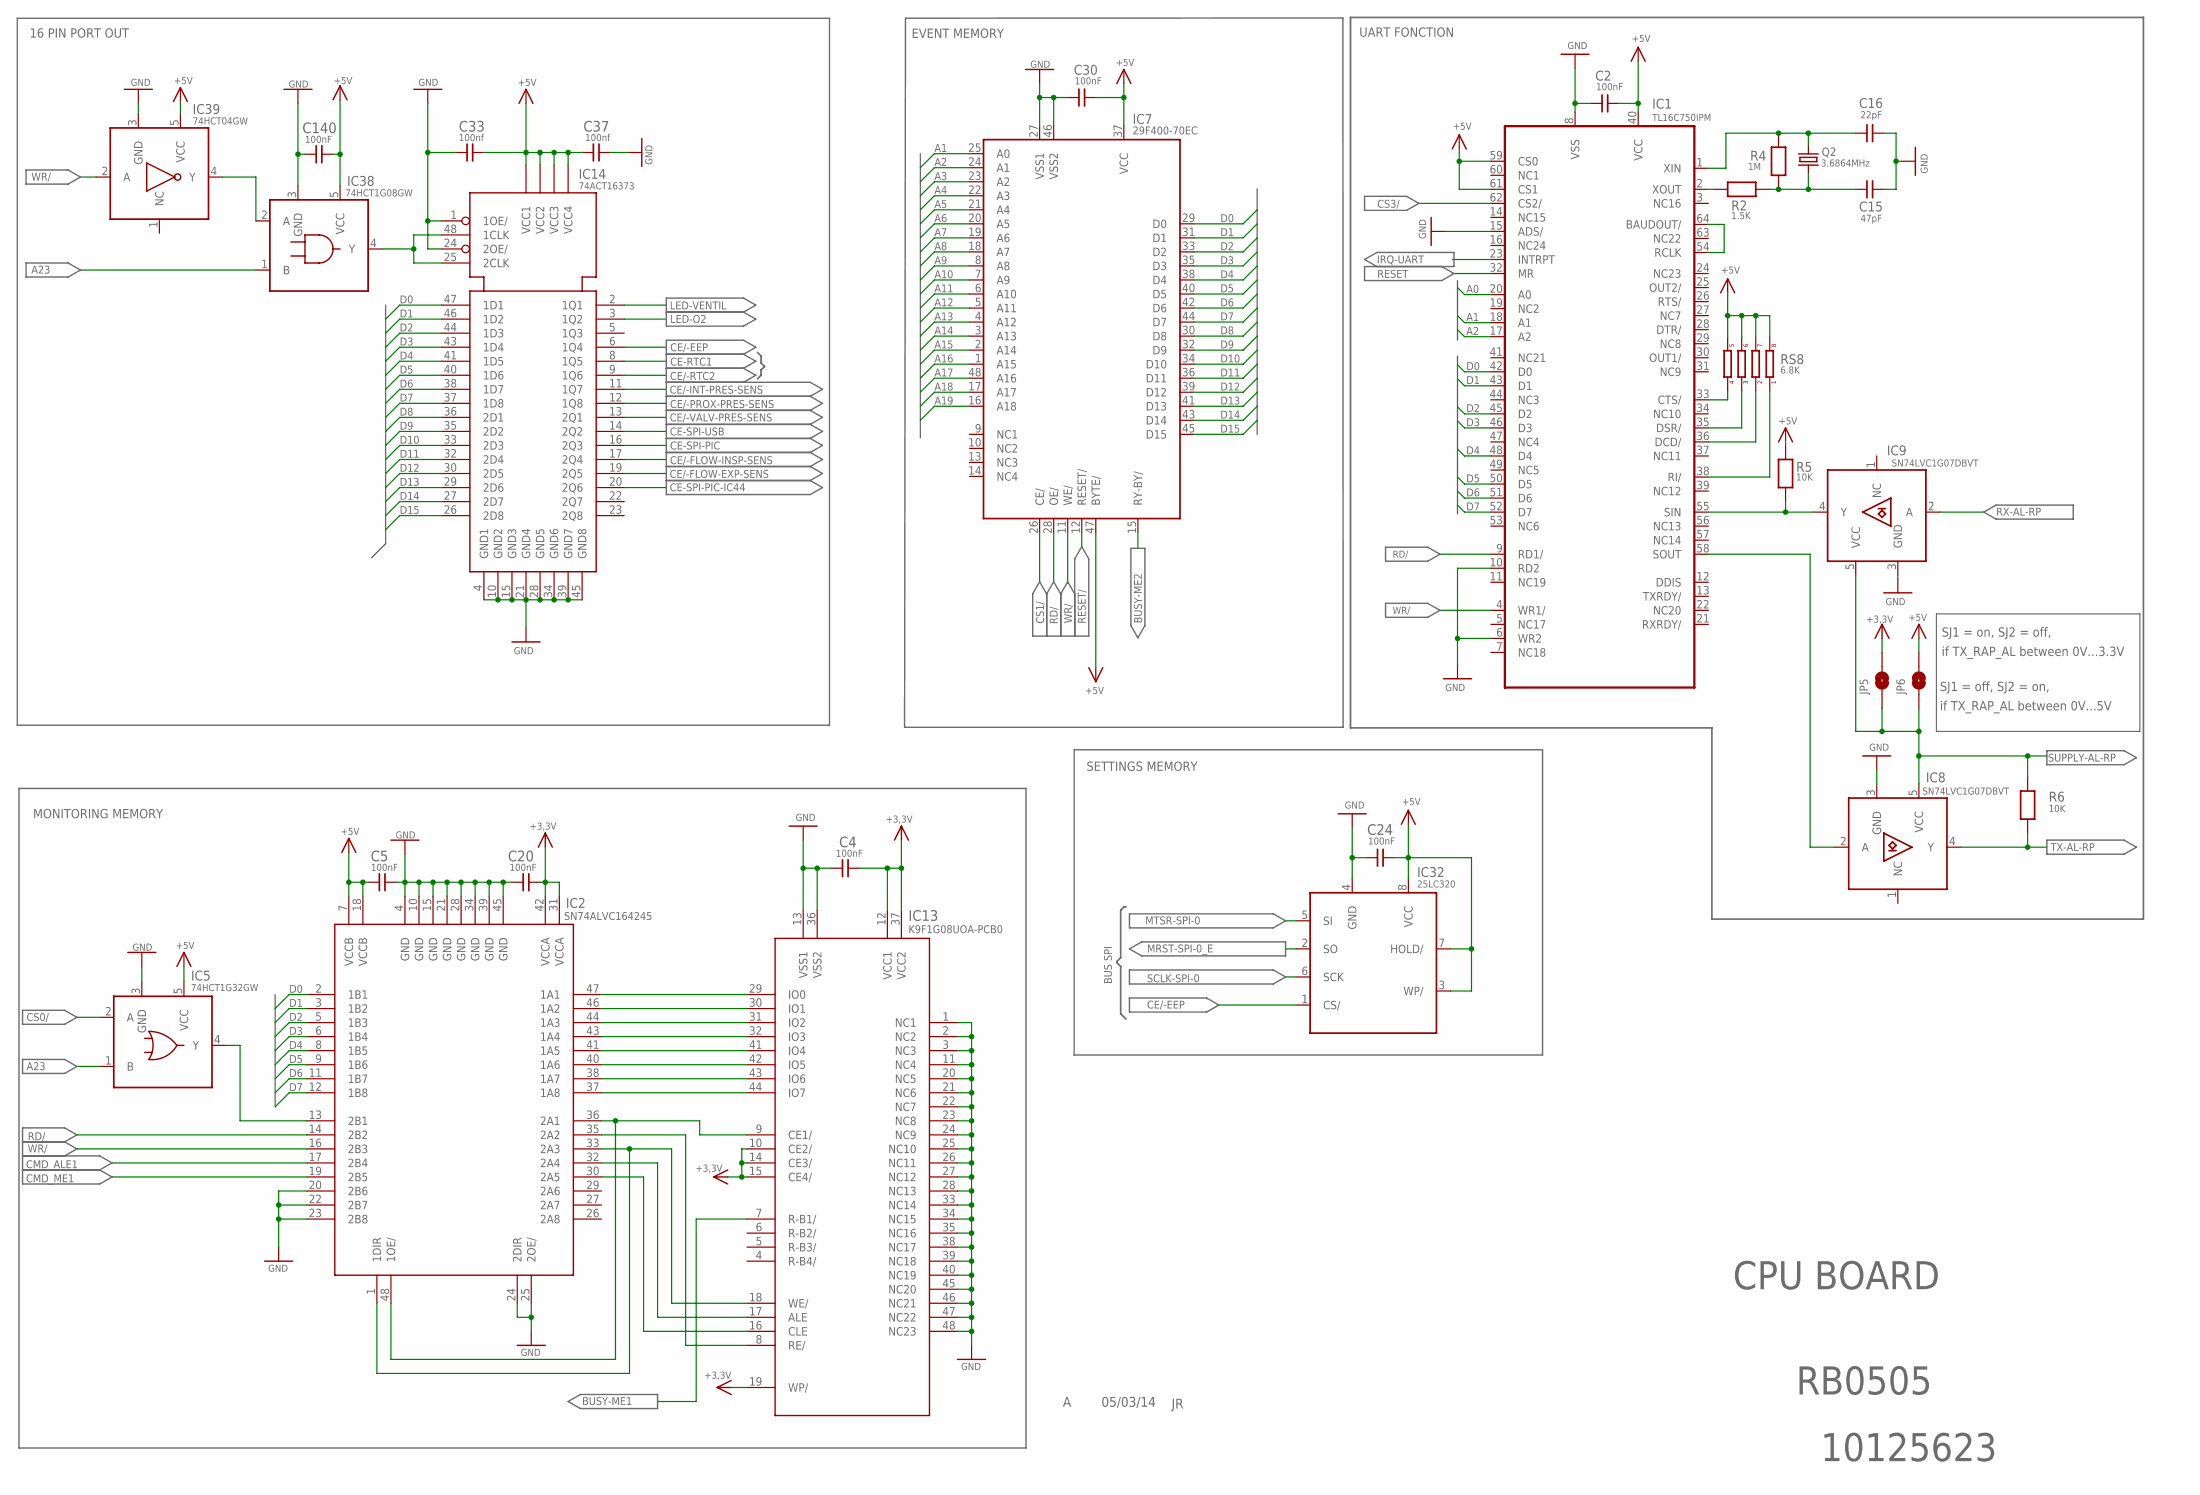
[picture p270: schematic 10125623A00.sch, sheet 2]

Parts:
C2, C4, C24, C30, C140: 100nF; C0805
C5, C20: 100nF; C0603
C15: 47pF; C0805
C16: 22pF; C0805
C33, C37: 100nf; C0805
IC1: TL16C750IPM; TQFP64
IC2: SN74ALVC164245; TSSOP48
IC5: 74HCT1G32GW; SOT23-5
IC7: Am29F400-EC; TS048
IC8, IC9: SN74LVC1G07DBVT; SOT753_DBV
IC13: K9F1G08UOA-PCB0; TS048
IC14: 74ACT16373; TSSOP48
IC32: 25LC320; SOIC8
IC38: 74HCT1G08GW; SOT23-5
IC39: 74HCT04GW; SOT23-5
JP5, JP6: JUMP_0U; 0805
Q2: 3.6864MHz; HC49UP
R2: 1.5K; R0805
R4: 1M; R0805
R5, R6: 10K; R0805
RS8: 6.8K; BCN16_4_

Connections:
+3,3V: C4.1, C20.1, IC2.31 (VCCA), IC2.42 (VCCA), IC13.10 (CE2/), IC13.12 (VCC1), IC13.14 (CE3/), IC13.15 (CE4/), IC13.19 (WP/), IC13.37 (VCC2), JP5.2
+5V: C2.1, C5.2, C24.1, C30.1, C33.1, C37.2, C140.2, IC1.40 (VCC), IC1.59 (CS0), IC1.61 (CS1), IC2.7 (VCCB), IC2.18 (VCCB), IC5.5 (VCC), IC7.37 (VCC), IC7.47 (BYTE/), IC14.7 (VCC1), IC14.18 (VCC2), IC14.31 (VCC3), IC14.42 (VCC4), IC32.3 (WP/), IC32.7 (HOLD/), IC32.8 (VCC), IC38.5 (VCC), IC39.5 (VCC), JP6.2, R5.2, RS8.5, RS8.6, RS8.7, RS8.8
A0: IC1.20 (A0)
A1: IC1.18 (A1), IC7.25 (A0)
A2: IC1.17 (A2), IC7.24 (A1)
A3: IC7.23 (A2)
A4: IC7.22 (A3)
A5: IC7.21 (A4)
A6: IC7.20 (A5)
A7: IC7.19 (A6)
A8: IC7.18 (A7)
A9: IC7.8 (A8)
A10: IC7.7 (A9)
A11: IC7.6 (A10)
A12: IC7.5 (A11)
A13: IC7.4 (A12)
A14: IC7.3 (A13)
A15: IC7.2 (A14)
A16: IC7.1 (A15)
A17: IC7.48 (A16)
A18: IC7.17 (A17)
A19: IC7.16 (A18)
A23: IC5.1 (B), IC38.1 (B)
BUSY-ME1: IC13.7 (R-B1/)
BUSY-ME2: IC7.15 (RY-BY/)
CE-RTC1: IC14.8 (1Q5)
CE-SPI-PIC: IC14.16 (2Q3)
CE-SPI-PIC-IC44: IC14.20 (2Q6)
CE-SPI-USB: IC14.14 (2Q2)
CE/-EEP: IC14.6 (1Q4), IC32.1 (CS/)
CE/-FLOW-EXP-SENS: IC14.19 (2Q5)
CE/-FLOW-INSP-SENS: IC14.17 (2Q4)
CE/-INT-PRES-SENS: IC14.11 (1Q7)
CE/-PROX-PRES-SENS: IC14.12 (1Q8)
CE/-RTC2: IC14.9 (1Q6)
CE/-VALV-PRES-SENS: IC14.13 (2Q1)
CMD_ALE1: IC2.17 (2B4)
CMD_ME1: IC2.19 (2B5)
CS0/: IC5.2 (A)
CS1/: IC7.26 (CE/)
CS3/: IC1.62 (CS2/)
D0: IC1.42 (D0), IC2.2 (1B1), IC7.29 (D0), IC14.47 (1D1)
D1: IC1.43 (D1), IC2.3 (1B2), IC7.31 (D1), IC14.46 (1D2)
D2: IC1.45 (D2), IC2.5 (1B3), IC7.33 (D2), IC14.44 (1D3)
D3: IC1.46 (D3), IC2.6 (1B4), IC7.35 (D3), IC14.43 (1D4)
D4: IC1.48 (D4), IC2.8 (1B5), IC7.38 (D4), IC14.41 (1D5)
D5: IC1.50 (D5), IC2.9 (1B6), IC7.40 (D5), IC14.40 (1D6)
D6: IC1.51 (D6), IC2.11 (1B7), IC7.42 (D6), IC14.38 (1D7)
D7: IC1.52 (D7), IC2.12 (1B8), IC7.44 (D7), IC14.37 (1D8)
D8: IC7.30 (D8), IC14.36 (2D1)
D9: IC7.32 (D9), IC14.35 (2D2)
D10: IC7.34 (D10), IC14.33 (2D3)
D11: IC7.36 (D11), IC14.32 (2D4)
D12: IC7.39 (D12), IC14.30 (2D5)
D13: IC7.41 (D13), IC14.29 (2D6)
D14: IC7.43 (D14), IC14.27 (2D7)
D15: IC7.45 (D15), IC14.26 (2D8)
GND: C2.2, C4.2, C5.1, C15.2, C16.1, C20.2, C24.2, C30.2, C33.2, C37.1, C140.1, IC1.6 (WR2), IC1.8 (VSS), IC1.10 (RD2), IC1.15 (ADS/), IC2.4 (GND), IC2.10 (GND), IC2.15 (GND), IC2.20 (2B6), IC2.21 (GND), IC2.22 (2B7), IC2.23 (2B8), IC2.24 (2DIR), IC2.25 (2OE/), IC2.28 (GND), IC2.34 (GND), IC2.39 (GND), IC2.45 (GND), IC5.3 (GND), IC7.27 (VSS1), IC7.46 (VSS2), IC8.3 (GND), IC9.3 (GND), IC13.1 (NC1), IC13.2 (NC2), IC13.3 (NC3), IC13.11 (NC4), IC13.13 (VSS1), IC13.20 (NC5), IC13.21 (NC6), IC13.22 (NC7), IC13.23 (NC8), IC13.24 (NC9), IC13.25 (NC10), IC13.26 (NC11), IC13.27 (NC12), IC13.28 (NC13), IC13.33 (NC14), IC13.34 (NC15), IC13.35 (NC16), IC13.36 (VSS2), IC13.38 (NC17), IC13.39 (NC18), IC13.40 (NC19), IC13.45 (NC20), IC13.46 (NC21), IC13.47 (NC22), IC13.48 (NC23), IC14.1 (1OE/), IC14.4 (GND1), IC14.10 (GND2), IC14.15 (GND3), IC14.21 (GND4), IC14.24 (2OE/), IC14.28 (GND5), IC14.34 (GND6), IC14.39 (GND7), IC14.45 (GND8), IC32.4 (GND), IC38.3 (GND), IC39.3 (GND)
IRQ-UART: IC1.23 (INTRPT)
LED-O2: IC14.3 (1Q2)
LED-VENTIL: IC14.2 (1Q1)
MRST-SPI-0_E: IC32.2 (SO)
MTSR-SPI-0: IC32.5 (SI)
unnamed: IC2.47 (1A1), IC13.29 (IO0)
unnamed: IC38.2 (A), IC39.4 (Y)
unnamed: C16.2, IC1.1 (XIN), Q2.1, R4.2
unnamed: IC2.13 (2B1), IC5.4 (Y)
unnamed: IC14.25 (2CLK), IC14.48 (1CLK), IC38.4 (Y)
unnamed: C15.1, Q2.2, R2.2, R4.1
unnamed: IC1.2 (XOUT), R2.1
unnamed: IC1.54 (RCLK), IC1.64 (BAUDOUT/)
unnamed: IC2.36 (2A1), IC2.48 (1OE/), IC13.9 (CE1/)
unnamed: IC2.46 (1A2), IC13.30 (IO1)
unnamed: IC2.44 (1A3), IC13.31 (IO2)
unnamed: IC2.43 (1A4), IC13.32 (IO3)
unnamed: IC1.33 (CTS/), RS8.4
unnamed: IC1.35 (DSR/), RS8.3
unnamed: IC1.36 (DCD/), RS8.2
unnamed: IC1.38 (RI/), RS8.1
unnamed: IC1.58 (SOUT), IC8.2 (A)
unnamed: IC2.41 (1A5), IC13.41 (IO4)
unnamed: IC2.40 (1A6), IC13.42 (IO5)
unnamed: IC2.35 (2A2), IC13.8 (RE/)
unnamed: IC2.32 (2A4), IC13.17 (ALE)
unnamed: IC2.30 (2A5), IC13.16 (CLE)
unnamed: IC2.38 (1A7), IC13.43 (IO6)
unnamed: IC2.37 (1A8), IC13.44 (IO7)
unnamed: IC2.1 (1DIR), IC2.33 (2A3), IC13.18 (WE/)
RD/: IC1.9 (RD1/), IC2.14 (2B2), IC7.28 (OE/)
RESET: IC1.32 (MR)
RESET/: IC7.12 (RESET/)
RX-AL-RP: IC9.2 (A)
RXD2: IC1.55 (SIN), IC9.4 (Y), R5.1
SCLK-SPI-0: IC32.6 (SCK)
SUPPLY-AL-RP: IC8.5 (VCC), IC9.5 (VCC), JP5.1, JP6.1, R6.2
TX-AL-RP: IC8.4 (Y), R6.1
WR/: IC1.4 (WR1/), IC2.16 (2B3), IC7.11 (WE/), IC39.2 (A)

Notes on the sheet:
MONITORING MEMORY
16 PIN PORT OUT
UART FONCTION
SJ1 = on, SJ2 = off,
if TX_RAP_AL between 0V...3.3V
SJ1 = off, SJ2 = on,
if TX_RAP_AL between 0V...5V
BUS SPI
SETTINGS MEMORY
CPU BOARD
RB0505
10125623
05/03/14
EVENT MEMORY
29F400-70EC

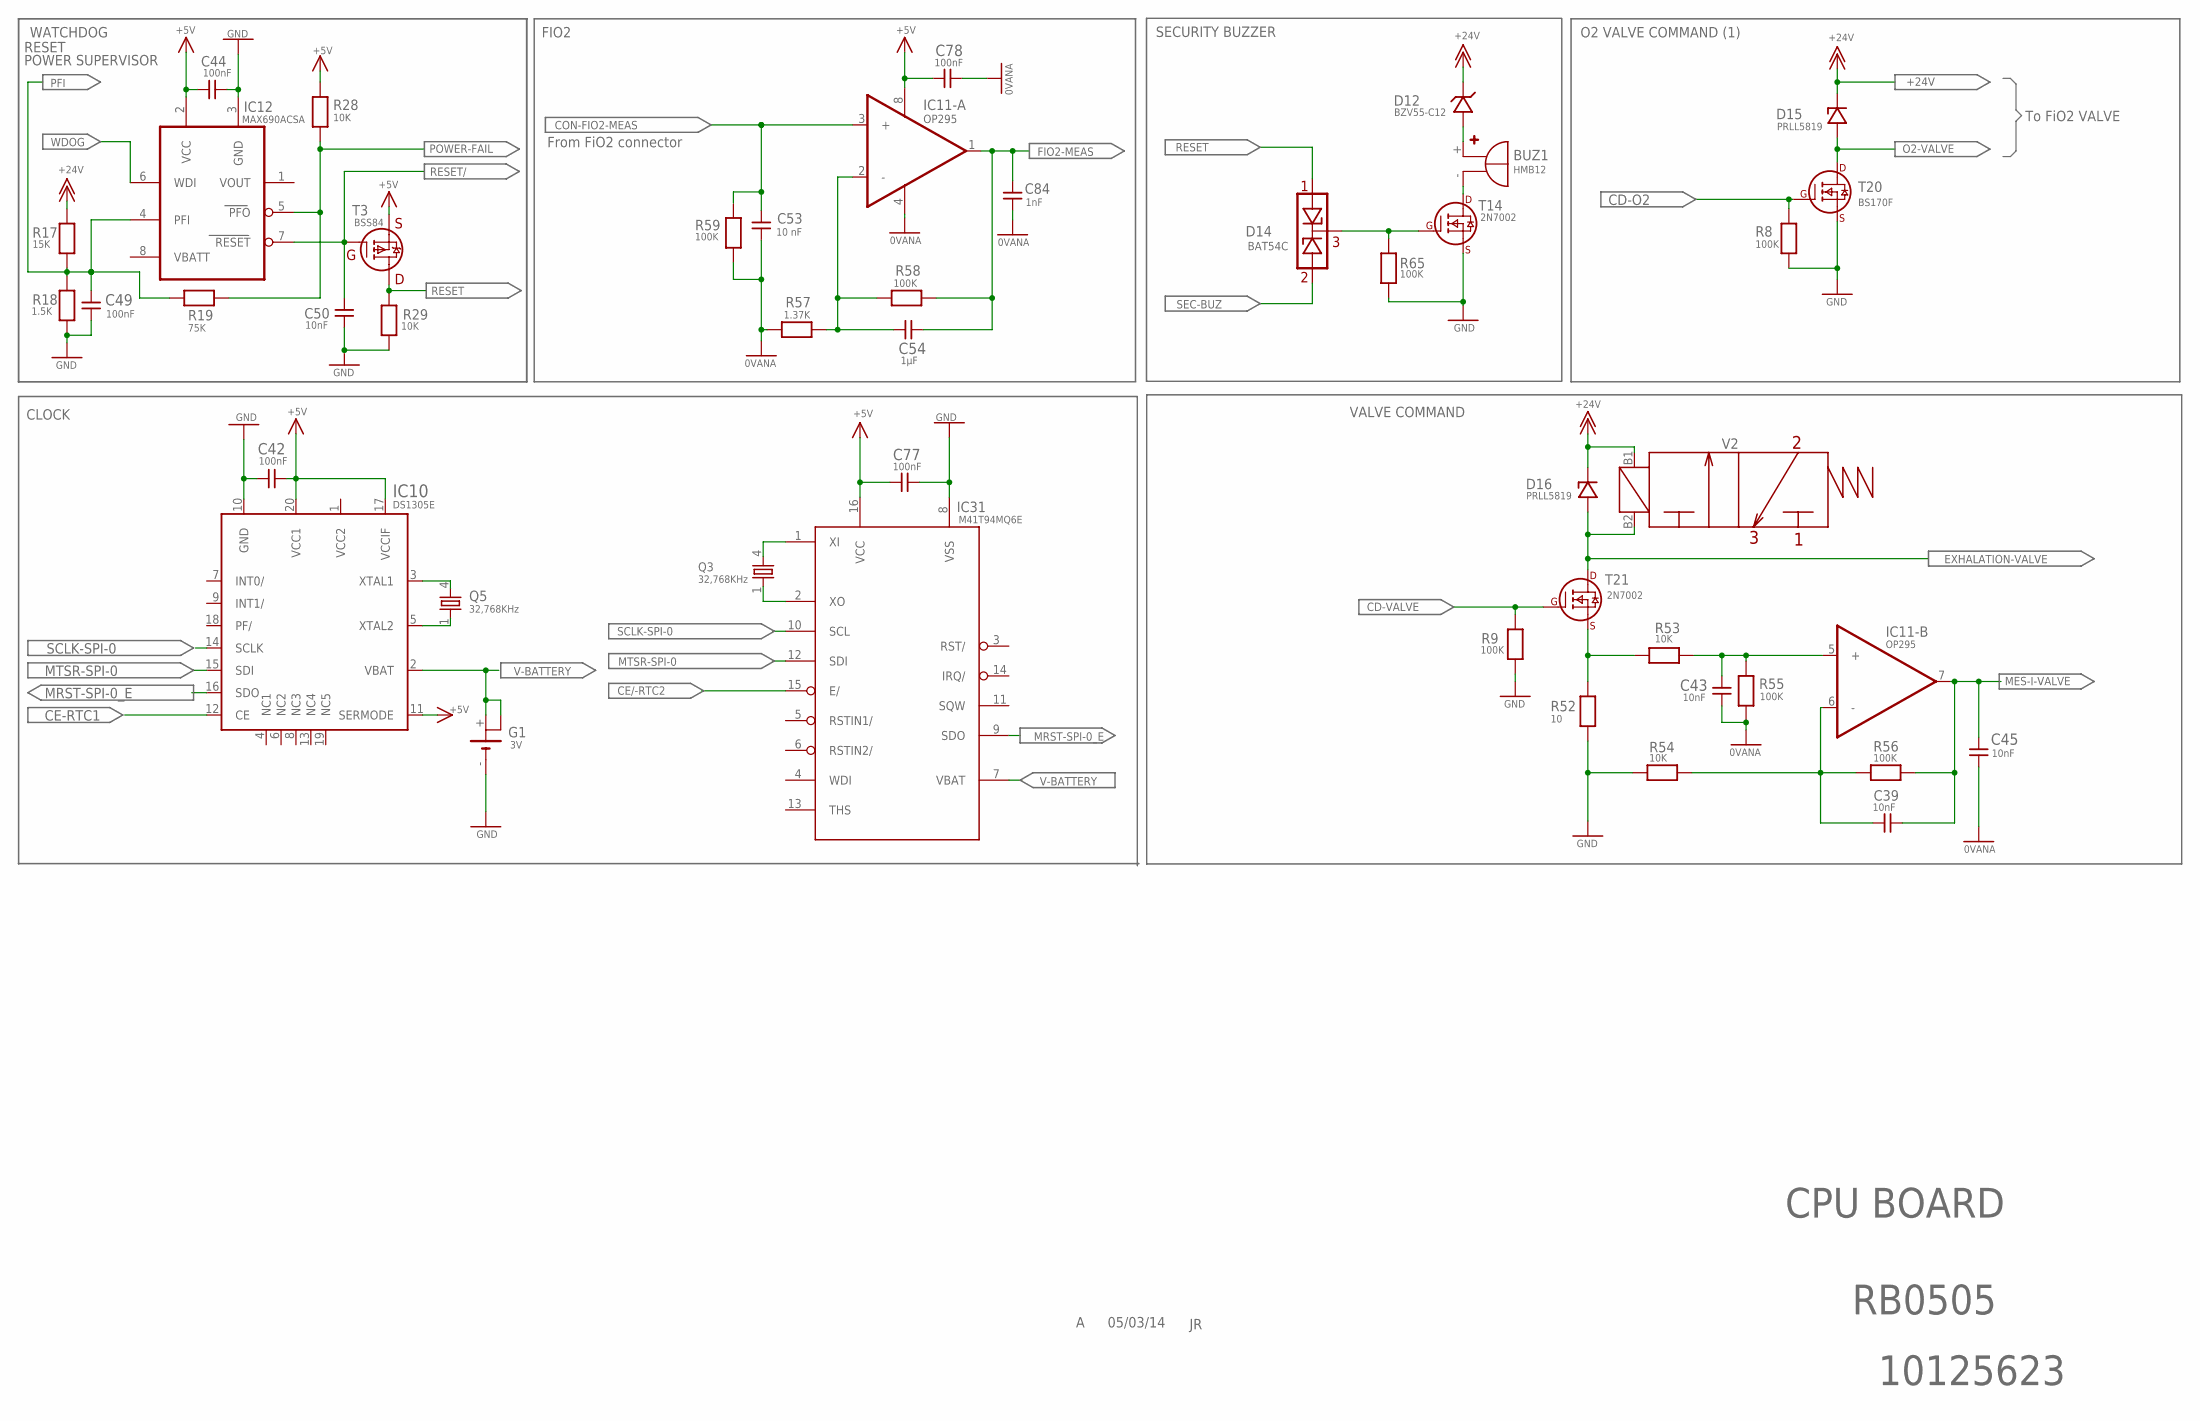
[picture p271: schematic 10125623A00.sch, sheet 3]

Parts:
BUZ1: HMB12; F/HMB
C39, C43, C45, C50: 10nF; C0805
C42, C44, C49, C77, C78: 100nF; C0805
C53: 10 nF; C0805
C54: 1µF; C0805
C84: 1nF; C0805
D12: BZV55-C12; SOT23DIO
D14: BAT54C; SOT23_DI
D15, D16: PRLL5819; SOD87
G1: 3V; KEY_3000
IC10: DS1305E; TSSOP20
IC11: OP295; SO8
IC12: MAX690ACSA; SO08
IC31: M41T94MQ6E; SO16
Q3, Q5: 32,768KHz; 86SMX
R8, R9, R55, R56, R58, R59, R65: 100K; R0805
R17: 15K; R0805
R18: 1.5K; R0805
R19: 75K; R0805
R28, R29, R53, R54: 10K; R0805
R52: 10; R0805
R57: 1.37K; R0805
T3: BSS84; SOT23MOS
T14, T21: 2N7002; DPAK
T20: BS170F; DPAK
V2: FAS-PPS-1P-3NIP-INJ

Connections:
0VANA: C43.1, C45.1, C53.1, C78.1, C84.1, IC11.4 (GND), R55.1, R57.1, R59.1
+5V: C42.1, C44.1, C77.2, C78.2, IC10.11 (SERMODE), IC10.17 (VCCIF), IC10.20 (VCC1), IC11.8 (VCC), IC12.2 (VCC), IC31.16 (VCC), R28.2, T3.S
+24V: D12.3 (K), D15.K, D16.K, R17.2, V2.B1
CD-O2: R8.2, T20.G (GATE)
CD-VALVE: R9.2, T21.G (GATE)
CE-RTC1: IC10.12 (CE)
CE/-RTC2: IC31.15 (E/)
CON-FIO2-MEAS: C53.2, IC11.3 (+), R59.2
EXHALATION-VALVE: D16.A, T21.D (DRAIN), V2.B2
FIO2-MEAS: C54.2, C84.2, IC11.1 (OUT), R58.2
GND: C42.2, C44.2, C49.1, C50.1, C77.1, G1.-, IC10.10 (GND), IC12.3 (GND), IC31.8 (VSS), R8.1, R9.1, R18.1, R29.2, R52.1, R54.1, R65.1, T14.S (SOURCE), T20.S (SOURCE)
IC11-B: C39.2, IC11.6 (-), R54.2, R56.2
MES-I-VALVE: C39.1, C45.2, IC11.7 (OUT), R56.1
MRST-SPI-0_E: IC10.16 (SDO), IC31.9 (SDO)
MTSR-SPI-0: IC10.15 (SDI), IC31.12 (SDI)
unnamed: C54.1, IC11.2 (-), R57.2, R58.1
unnamed: BUZ1.+, D12.1 (A)
unnamed: IC10.3 (XTAL1), Q5.4 (2)
unnamed: IC10.5 (XTAL2), Q5.1
unnamed: IC31.1 (XI), Q3.4 (2)
unnamed: IC31.2 (XO), Q3.1
unnamed: R52.2, R53.1, T21.S (SOURCE)
unnamed: C43.2, IC11.5 (+), R53.2, R55.2
unnamed: BUZ1.-, T14.D (DRAIN)
unnamed: D14.3, R65.2, T14.G (GATE)
O2-VALVE: D15.A, T20.D (DRAIN)
PFI: C49.2, IC12.4 (PFI), R17.1, R18.2, R19.1
POWER-FAIL: IC12.5 (PFO), R19.2, R28.1
RESET: D14.1, R29.1, T3.D
RESET/: C50.2, IC12.7 (RESET), T3.G
SCLK-SPI-0: IC10.14 (SCLK), IC31.10 (SCL)
SEC-BUZ: D14.2
V-BATTERY: G1.+, G1.PLUS, IC10.2 (VBAT), IC31.7 (VBAT)
WDOG: IC12.6 (WDI)

Notes on the sheet:
CLOCK
SECURITY BUZZER
O2 VALVE COMMAND (1)
To FiO2 VALVE
VALVE COMMAND
FIO2
From FiO2 connector
CPU BOARD
RB0505
10125623
05/03/14
WATCHDOG
RESET
POWER SUPERVISOR

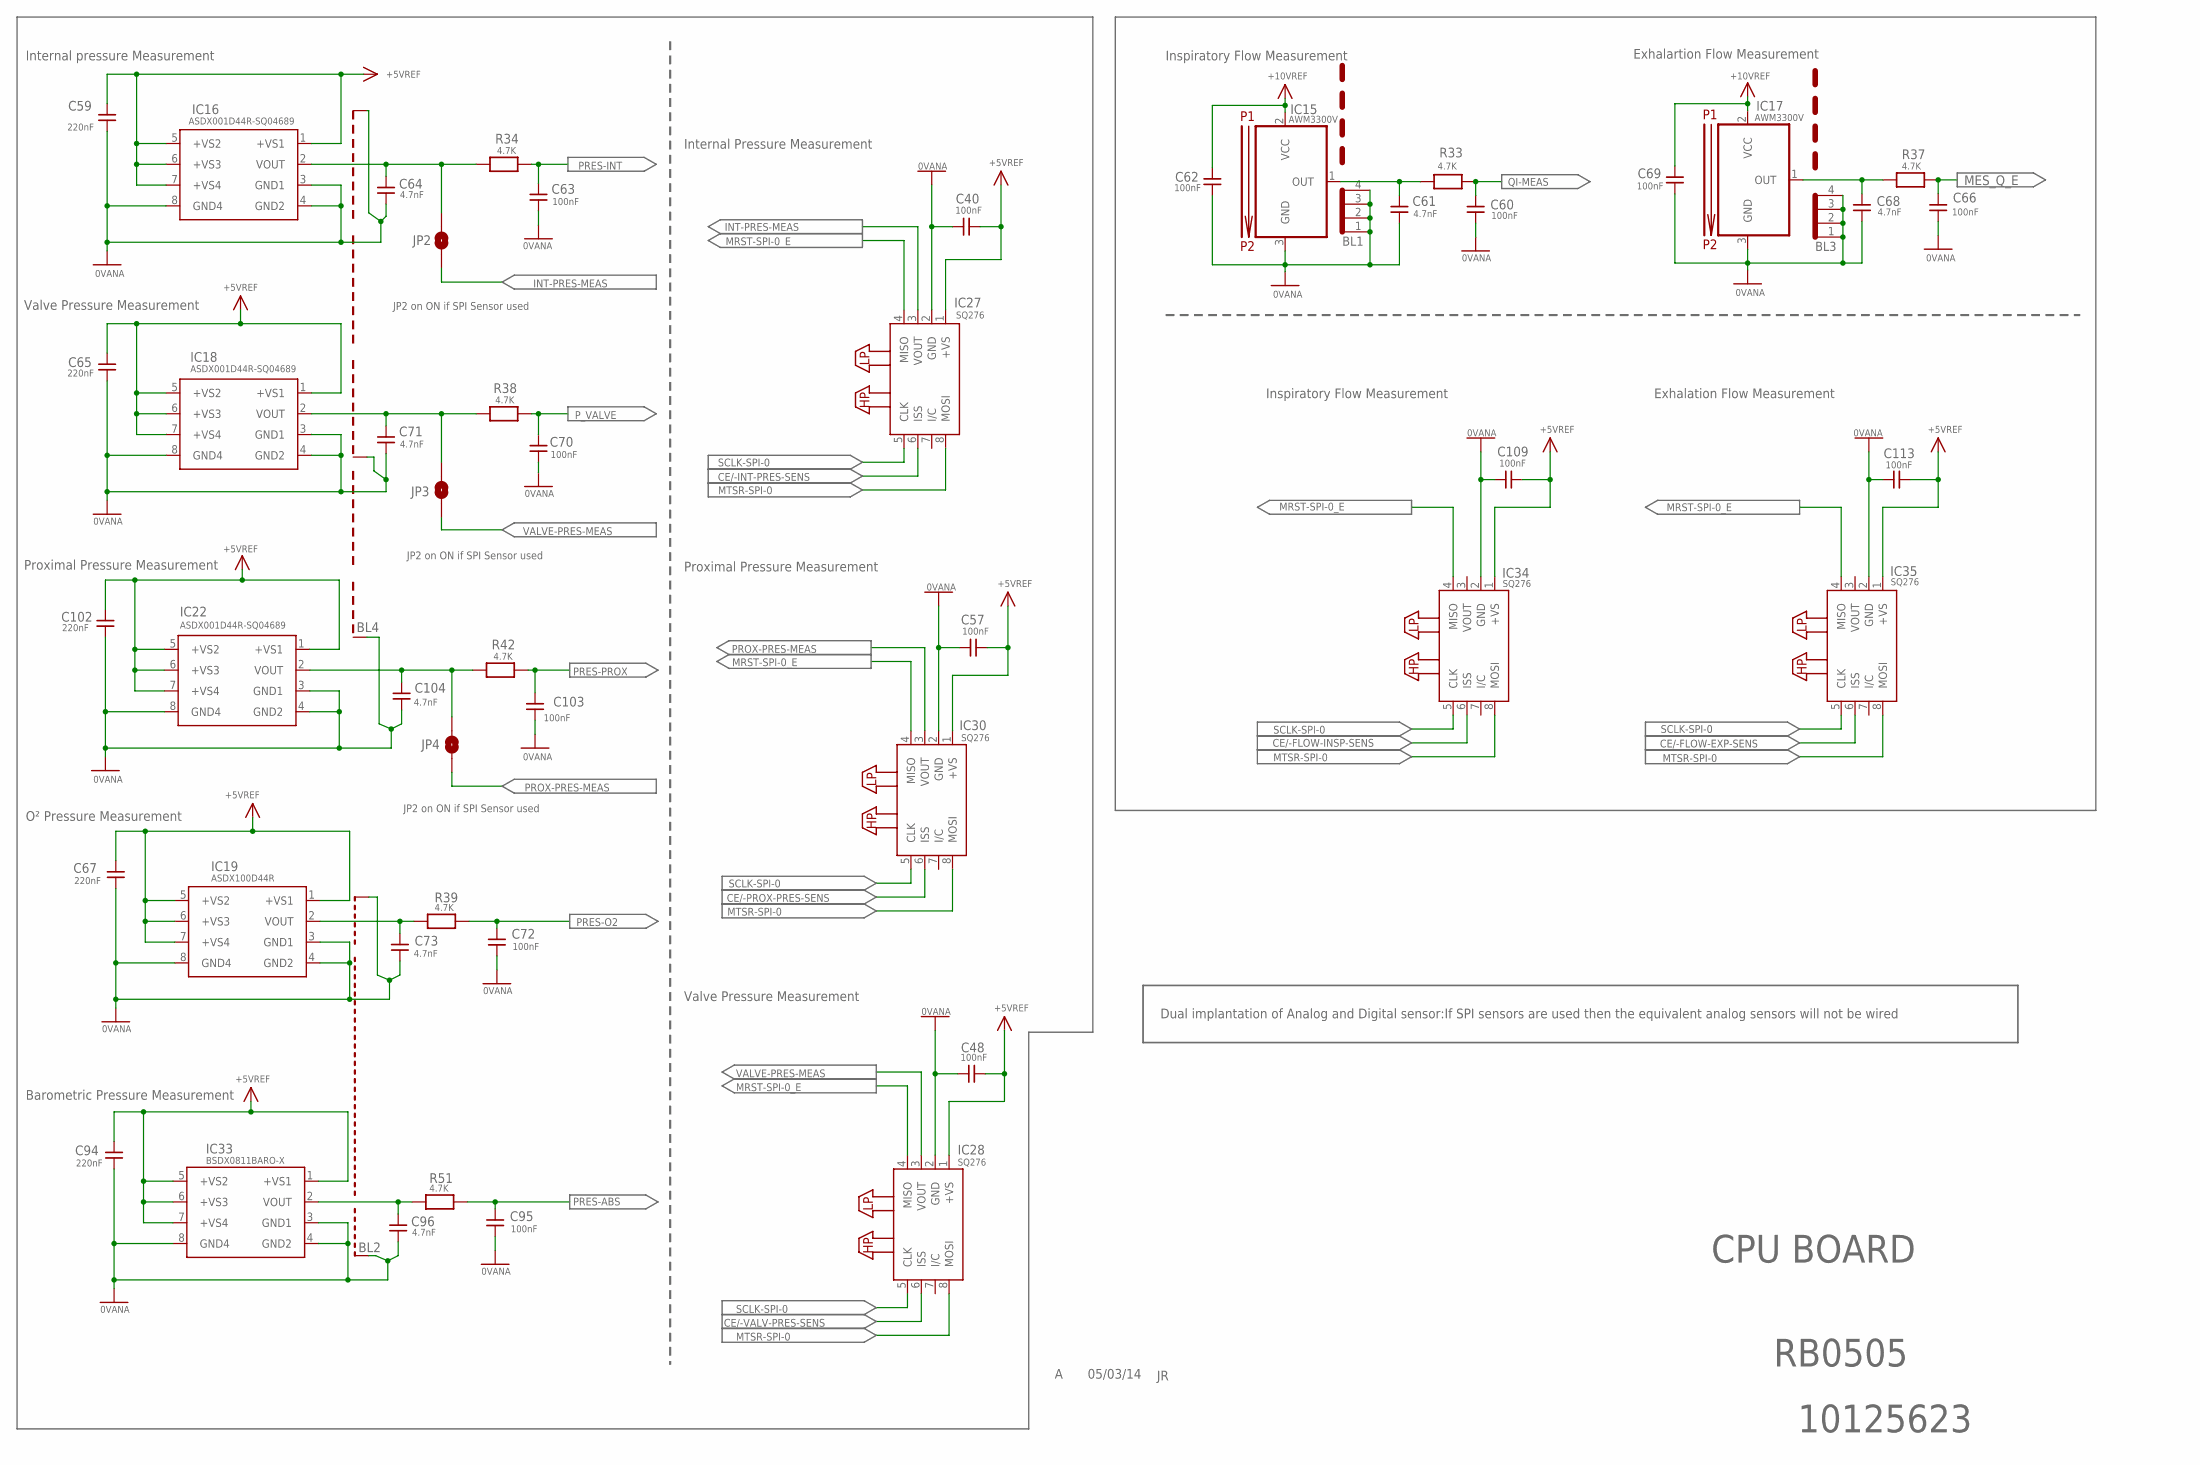
[picture p272: schematic 10125623A00.sch, sheet 4]

Parts:
BL1, BL3: BLIN-AWM33; BLIN-AWM
BL2: 2XBL-AWM
BL4: 3XBL-ADSX; 3XBL-AWM
C40, C48, C57, C60, C62, C63, C66, C69, C70, C72, C95, C103, C109, C113: 100nF; C0805
C59, C65, C67, C94, C102: 220nF; C1206
C61, C64, C68, C71, C73, C96, C104: 4.7nF; C0805
IC15, IC17: AWM3300V
IC16, IC18, IC22: ASDX001D44R-SQ04689; ASDX
IC19: ASDX100D44R; ASDX
IC27, IC28, IC30, IC34, IC35: SQ276
IC33: BSDX0811BARO-X; ASDX
JP2, JP3, JP4: JUMP_0U; 0805
R33, R34, R37, R38, R39, R42, R51: 4.7K; R0805

Connections:
0VANA: BL1.1, BL1.2, BL1.3, BL1.4, BL2.1 (OUT1), BL2.2 (OUT2), BL3.1, BL3.2, BL3.3, BL3.4, BL4.1, BL4.3, BL4.4, C40.2, C48.2, C57.2, C59.1, C60.1, C61.1, C62.1, C63.1, C64.1, C65.1, C66.1, C67.1, C68.1, C69.1, C70.1, C71.1, C72.1, C73.1, C94.1, C95.1, C96.1, C102.1, C103.1, C104.1, C109.2, C113.2, IC15.3 (GND), IC16.3 (GND1), IC16.4 (GND2), IC16.8 (GND4), IC17.3 (GND), IC18.3 (GND1), IC18.4 (GND2), IC18.8 (GND4), IC19.3 (GND1), IC19.4 (GND2), IC19.8 (GND4), IC22.3 (GND1), IC22.4 (GND2), IC22.8 (GND4), IC27.2 (GND), IC28.2 (GND), IC30.2 (GND), IC33.3 (GND1), IC33.4 (GND2), IC33.8 (GND4), IC34.2 (GND), IC35.2 (GND)
+5VREF: C40.1, C48.1, C57.1, C59.2, C65.2, C67.2, C94.2, C102.2, C109.1, C113.1, IC16.1 (+VS1), IC16.5 (+VS2), IC16.6 (+VS3), IC16.7 (+VS4), IC18.1 (+VS1), IC18.5 (+VS2), IC18.6 (+VS3), IC18.7 (+VS4), IC19.1 (+VS1), IC19.5 (+VS2), IC19.6 (+VS3), IC19.7 (+VS4), IC22.1 (+VS1), IC22.5 (+VS2), IC22.6 (+VS3), IC22.7 (+VS4), IC27.1 (+VS), IC28.1 (+VS), IC30.1 (+VS), IC33.1 (+VS1), IC33.5 (+VS2), IC33.6 (+VS3), IC33.7 (+VS4), IC34.1 (+VS), IC35.1 (+VS)
+10VREF: C62.2, C69.2, IC15.2 (VCC), IC17.2 (VCC)
CE/-FLOW-EXP-SENS: IC35.6 (ISS)
CE/-FLOW-INSP-SENS: IC34.6 (ISS)
CE/-INT-PRES-SENS: IC27.6 (ISS)
CE/-PROX-PRES-SENS: IC30.6 (ISS)
CE/-VALV-PRES-SENS: IC28.6 (ISS)
INT-PRES-MEAS: IC27.3 (VOUT), JP2.1
MES_QI1: C61.2, IC15.1 (OUT), R33.1
MES_QI4: C68.2, IC17.1 (OUT), R37.1
MES_Q_E: C66.2, R37.2
MRST-SPI-0_E: IC27.4 (MISO), IC28.4 (MISO), IC30.4 (MISO), IC34.4 (MISO), IC35.4 (MISO)
MTSR-SPI-0: IC27.8 (MOSI), IC28.8 (MOSI), IC30.8 (MOSI), IC34.8 (MOSI), IC35.8 (MOSI)
unnamed: C73.2, IC19.2 (VOUT), R39.1
unnamed: C64.2, IC16.2 (VOUT), JP2.2, R34.1
unnamed: C71.2, IC18.2 (VOUT), JP3.2, R38.1
unnamed: C104.2, IC22.2 (VOUT), JP4.2, R42.1
unnamed: C96.2, IC33.2 (VOUT), R51.1
PRES-ABS: C95.2, R51.2
PRES-INT: C63.2, R34.2
PRES-O2: C72.2, R39.2
PRES-PROX: C103.2, R42.2
PROX-PRES-MEAS: IC30.3 (VOUT), JP4.1
P_VALVE: C70.2, R38.2
QI-MEAS: C60.2, R33.2
SCLK-SPI-0: IC27.5 (CLK), IC28.5 (CLK), IC30.5 (CLK), IC34.5 (CLK), IC35.5 (CLK)
VALVE-PRES-MEAS: IC28.3 (VOUT), JP3.1

Notes on the sheet:
Internal pressure Measurement
Valve Pressure Measurement
O² Pressure Measurement
Proximal Pressure Measurement
Internal Pressure Measurement
JP2 on ON if SPI Sensor used
Inspiratory Flow Measurement
Exhalartion Flow Measurement
Exhalation Flow Measurement
Dual implantation of Analog and Digital sensor:If SPI sensors are used then the equivalent analog sensors will not be wired
CPU BOARD
RB0505
10125623
05/03/14
Barometric Pressure Measurement

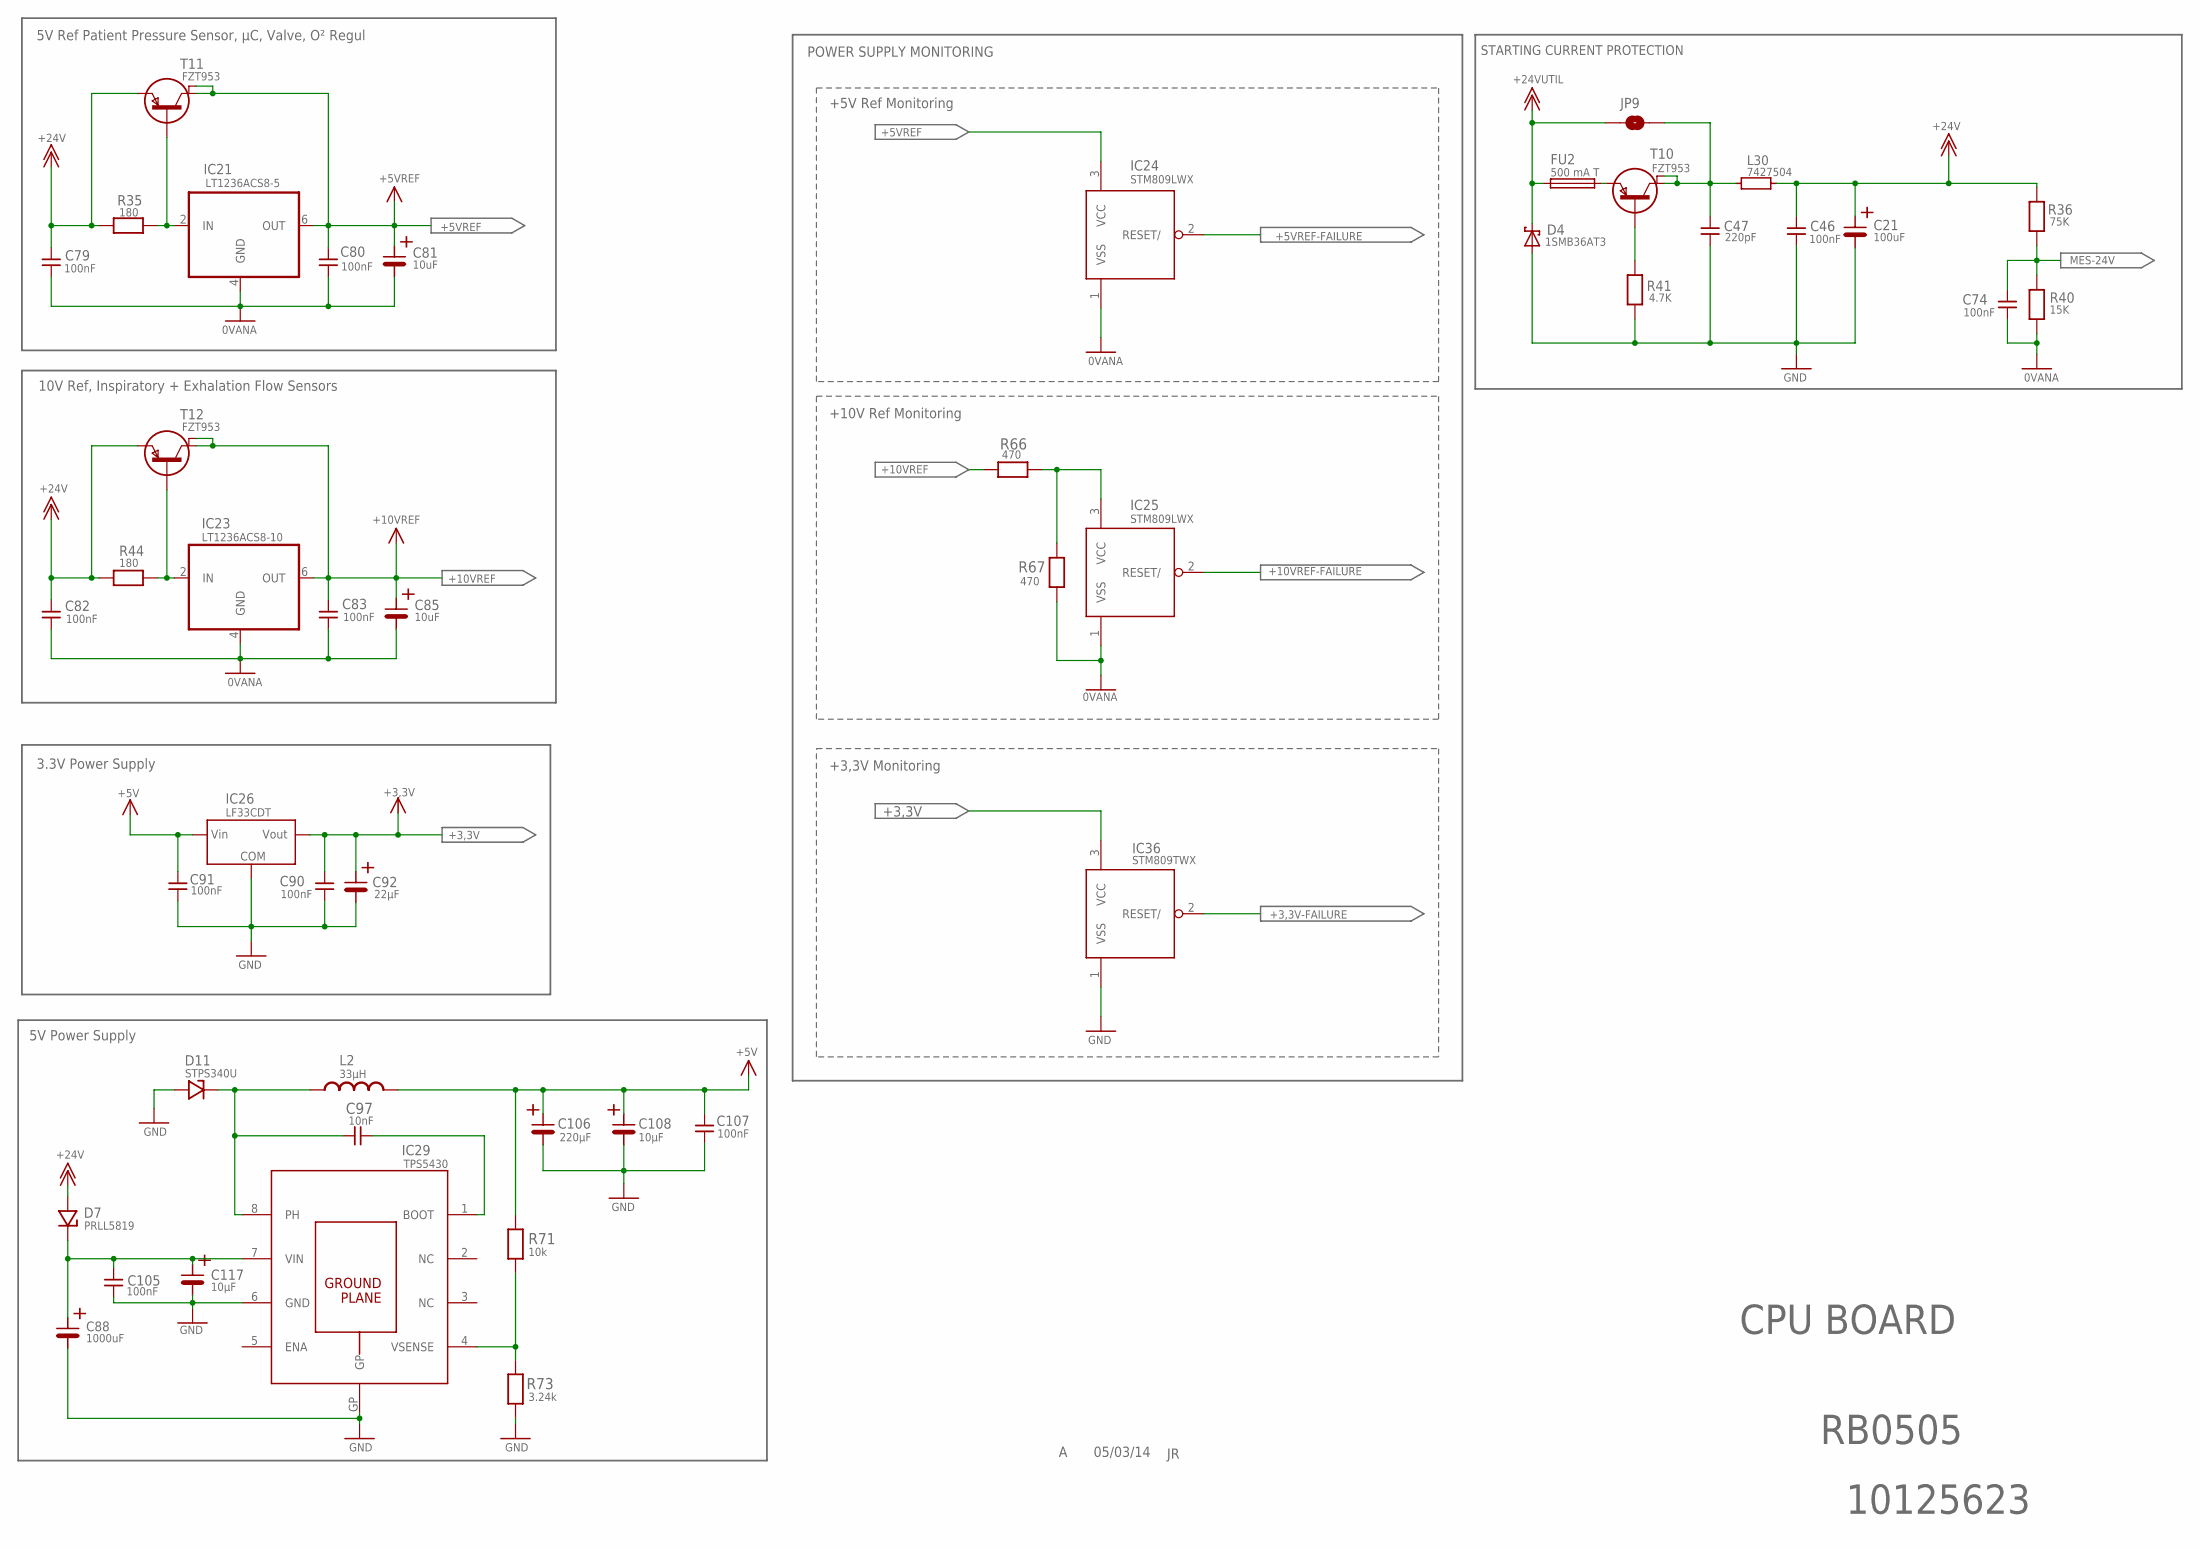
[picture p273: schematic 10125623A00.sch, sheet 5]

Parts:
C21: 100uF; MV100?F
C46, C74, C79, C80, C82, C83, C90, C91, C105, C107: 100nF; C0805
C47: 220pF; C0805
C81, C85: 10uF; TANTALD
C88: 1000uF; MV100?F
C92: 22µF; TANTALB
C97: 10nF; C0805
C106: 220µF; CHCMS_D8
C108, C117: 10µF; TANTALB
D4: 1SMB36AT3; C4111-15
D7: PRLL5819; SOD87
D11: STPS340U; SOT23DIO
FU2: 500 mA T; SLOBLO
IC21: LT1236ACS8-5; SO8
IC23: LT1236ACS8-10; SO8
IC24, IC25: STM809LWX; SOT23
IC26: LF33CDT; REGUL-DPAK
IC29: TPS5430; SO8POWERPAD
IC36: STM809TWX; SOT23
JP9: JUMP_0U; 0805
L2: 33µH; WE-TPC-MH
L30: 7427504; PERL-FER
R35, R44: 180; R0805
R36: 75K; R0805
R40: 15K; R0805
R41: 4.7K; R1206
R66, R67: 470; R0805
R71: 10k; R0805
R73: 3.24k; R0805
T10, T11, T12: FZT953; SOT223

Connections:
0VANA: C74.1, C79.1, C80.1, C81.-, C82.1, C83.1, C85.-, IC21.4 (GND), IC23.4 (GND), IC24.1 (VSS), IC25.1 (VSS), R40.2, R67.1
+3,3V: C90.2, C92.+, IC26.OUTPUT (VOUT), IC36.3 (VCC)
+3,3V-FAILURE: IC36.2 (RESET/)
+5V: C91.2, C106.+, C107.2, C108.+, IC26.INPUT (VIN), L2.1, R71.1
+5VREF: C80.2, C81.+, IC21.6 (OUT), IC24.3 (VCC), T11.2 (C), T11.4 (C2)
+5VREF-FAILURE: IC24.2 (RESET/)
+10VREF: C83.2, C85.+, IC23.6 (OUT), R66.1, T12.2 (C), T12.4 (C2)
+10VREF-FAILURE: IC25.2 (RESET/)
+24V: C21.+, C46.2, C79.2, C82.2, D7.A, L30.2, R35.1, R36.1, R44.1, T11.3 (E), T12.3 (E)
+24VUTIL: D4.K, FU2.1, JP9.1
GND: C21.-, C46.1, C47.1, C88.-, C90.1, C91.1, C92.-, C105.1, C106.-, C107.1, C108.-, C117.-, D4.A, D11.1 (A), IC26.GND (COM), IC29.6 (GND), IC29.GP, IC36.1 (VSS), R41.1, R73.1
MES-24V: C74.2, R36.2, R40.1
unnamed: IC21.2 (IN), R35.2, T11.1 (B)
unnamed: IC23.2 (IN), R44.2, T12.1 (B)
unnamed: IC29.4 (VSENSE), R71.2, R73.2
unnamed: C97.2, IC29.1 (BOOT)
unnamed: C88.+, C105.2, C117.+, D7.K, IC29.7 (VIN)
unnamed: C97.1, D11.3 (K), IC29.8 (PH), L2.2
unnamed: IC25.3 (VCC), R66.2, R67.2
unnamed: C47.2, JP9.2, L30.1, T10.2 (C), T10.4 (C2)
unnamed: R41.2, T10.1 (B)
unnamed: FU2.2, T10.3 (E)

Notes on the sheet:
5V Ref Patient Pressure Sensor, µC, Valve, O² Regul
10V Ref, Inspiratory + Exhalation Flow Sensors
3.3V Power Supply
5V Power Supply
CPU BOARD
RB0505
10125623
05/03/14
POWER SUPPLY MONITORING
+5V Ref Monitoring
+10V Ref Monitoring
+3,3V Monitoring
STARTING CURRENT PROTECTION
