L0op/medtronic-pb560/file-set-2/Electronic PCBAs/GR106769_CPU_PCBA/SCH/10125623A00.sch

## EAGLE design file-set-2/Electronic PCBAs/GR106769_CPU_PCBA/SCH/10125623A00.sch (continued)

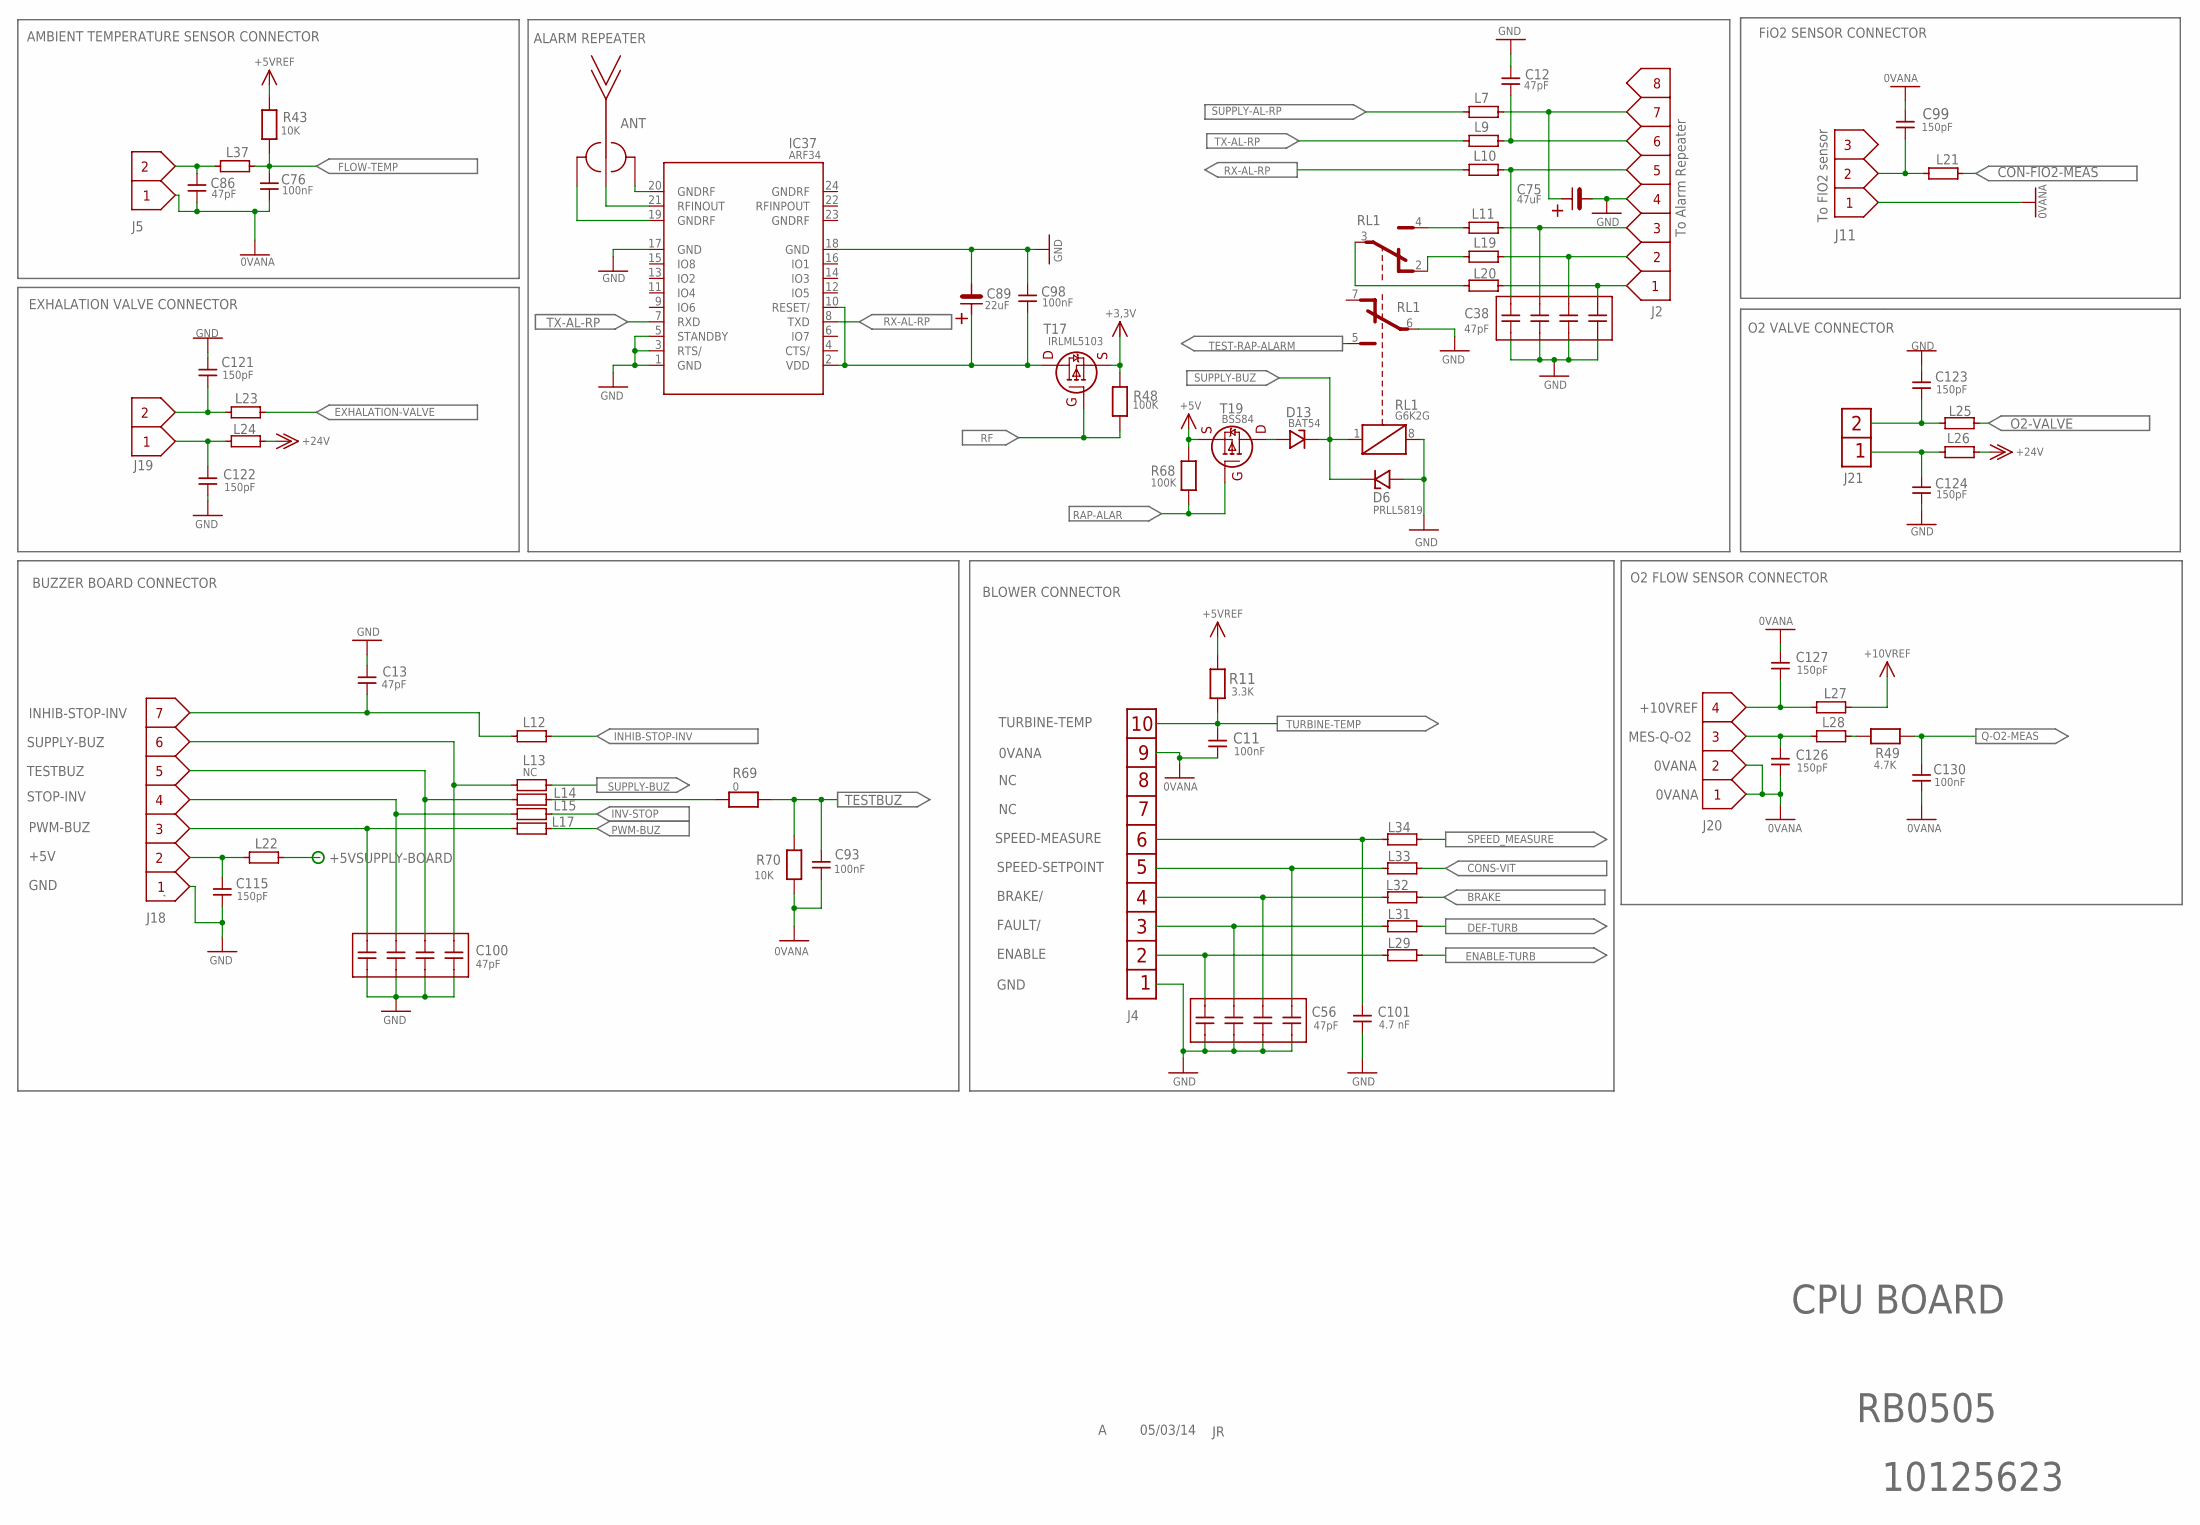
[picture p274: schematic 10125623A00.sch, sheet 6]

Parts:
ANT: ANTENNE
C11, C93, C98, C130: 100nF; C0805
C12, C13: 47pF; C0603
C38, C56, C100: 47pF; RESEAU_1
C75: 47uF; TANTALB
C76: 100nF; C0603
C86: 47pF; C0805
C89: 22uF; TANTALB
C99, C115, C121, C122, C123, C124, C126, C127: 150pF; C0603
C101: 4.7 nF; C0805
D6: PRLL5819; SOD87
D13: BAT54; SOT23DIO
IC37: ARF34
J2: B8B_ZR; 8BR
J4: 10BRMF; MF10BR
J5, J19: B2B_ZR; 2BR
J11: B3B_ZR; 3BR
J18: B7B_ZR_SM3_TF; 7B_ZR_SM3_TF
J20: B4B_ZR; 4BR
J21: 2BR254C
L7, L9, L10, L11, L12, L13, L14, L15, L17, L19, L20, L23, L24, L25, L26, L29, L31, L32, L33, L34, L37: 0603
L21, L22, L27, L28: 74279263; 0603
R11: 3.3K; R0805
R43, R70: 10K; R0805
R48, R68: 100K; R0805
R49: 4.7K; R0805
R69: 0; R0805
RL1: G6K2G
T17: IRLML5103; SOT23MOS
T19: BSS84; SOT23MOS

Connections:
0VANA: C11.1, C76.1, C86.1, C93.1, C99.2, C126.1, C127.2, C130.1, J4.9, J5.1, J11.1, J20.1, J20.2, R70.1
+3,3V: R48.1, T17.S
+5V: R68.2, T19.S
+5VREF: R11.2, R43.2
+5VSUPPLY-BOARD: L22.2
+10VREF: L27.2
+24V: L24.2, L26.2
BRAKE: L32.2
BRAKE/: C56.6, J4.4, L32.1
C-RAP-AL: L20.2, RL1.3 (L)
CON-FIO2-MEAS: L21.2
CONS-VIT: L33.2
DEF-TURB: L31.2
ENABLE: C56.8, J4.2, L29.1
ENABLE-TURB: L29.2
EXHALATION-VALVE: L23.2
FAULT/: C56.7, J4.3, L31.1
FLOW-TEMP: C76.2, L37.2, R43.1
GND: C12.2, C13.2, C38.1, C38.2, C38.3, C38.4, C56.1, C56.2, C56.3, C56.4, C75.-, C89.-, C98.2, C100.1, C100.2, C100.3, C100.4, C101.1, C115.1, C121.2, C122.1, C123.2, C124.1, D6.A, IC37.1 (GND), IC37.3 (RTS/), IC37.5 (STANDBY), IC37.17 (GND), IC37.18 (GND), J2.4, J4.1, J18.1, RL1.6 (L), RL1.8 (B1-)
INHIB-STOP-INV: L12.2
INV-STOP: L15.2
unnamed: C75.+, J2.7, L7.1
unnamed: C86.2, J5.2, L37.1
unnamed: C38.6, J2.3, L11.1
unnamed: C38.7, J2.2, L19.1
unnamed: C38.8, J2.1, L20.1
unnamed: L14.2, R69.1
unnamed: C99.1, J11.2, L21.1
unnamed: ANT.2, IC37.20 (GNDRF)
unnamed: ANT.1, IC37.21 (RFINOUT)
unnamed: C12.1, J2.6, L9.1
unnamed: C38.5, J2.5, L10.1
unnamed: C115.2, J18.2, L22.1
unnamed: C100.7, J18.4, L15.1
unnamed: C100.6, J18.5, L14.1
unnamed: C100.5, J18.6, L13.1
unnamed: ANT.3, IC37.19 (GNDRF)
unnamed: C89.+, C98.1, IC37.2 (VDD), IC37.10 (RESET/), T17.D
unnamed: C13.1, J18.7, L12.1
unnamed: C100.8, J18.3, L17.1
unnamed: D13.1 (A), T19.D
unnamed: C121.1, J19.2, L23.1
unnamed: C122.2, J19.1, L24.1
unnamed: C123.1, J21.2, L25.1
unnamed: C124.2, J21.1, L26.1
unnamed: C127.1, J20.4, L27.1
unnamed: C126.2, J20.3, L28.1
unnamed: L28.2, R49.1
O2-VALVE: L25.2
PWM-BUZ: L17.2
Q-O2-MEAS: C130.2, R49.2
R-RAP-AL: L19.2, RL1.2 (R)
RAP-ALAR: R68.1, T19.G
RF: R48.2, T17.G
RX-AL-RP: IC37.8 (TXD), L10.2
SPEED-MEASURE: C101.2, J4.6, L34.1
SPEED-SETPOINT: C56.5, J4.5, L33.1
SPEED_MEASURE: L34.2
SUPPLY-AL-RP: L7.2
SUPPLY-BUZ: D6.K, D13.3 (K), L13.2, RL1.1 (B2+)
T-RAP-AL: L11.2, RL1.4 (T)
TEST-RAP-ALARM: RL1.5 (T)
TESTBUZ: C93.2, R69.2, R70.2
TURBINE-TEMP: C11.2, J4.10, R11.1
TX-AL-RP: IC37.7 (RXD), L9.2

Notes on the sheet:
ALARM REPEATER
To Alarm Repeater
To FIO2 sensor
BLOWER CONNECTOR
FiO2 SENSOR CONNECTOR
BUZZER BOARD CONNECTOR
INHIB-STOP-INV
SUPPLY-BUZ
TESTBUZ
STOP-INV
PWM-BUZ
GND
+5V
EXHALATION VALVE CONNECTOR
O2 VALVE CONNECTOR
+10VREF
MES-Q-O2
0VANA
O2 FLOW SENSOR CONNECTOR
CPU BOARD
RB0505
10125623
05/03/14
AMBIENT TEMPERATURE SENSOR CONNECTOR

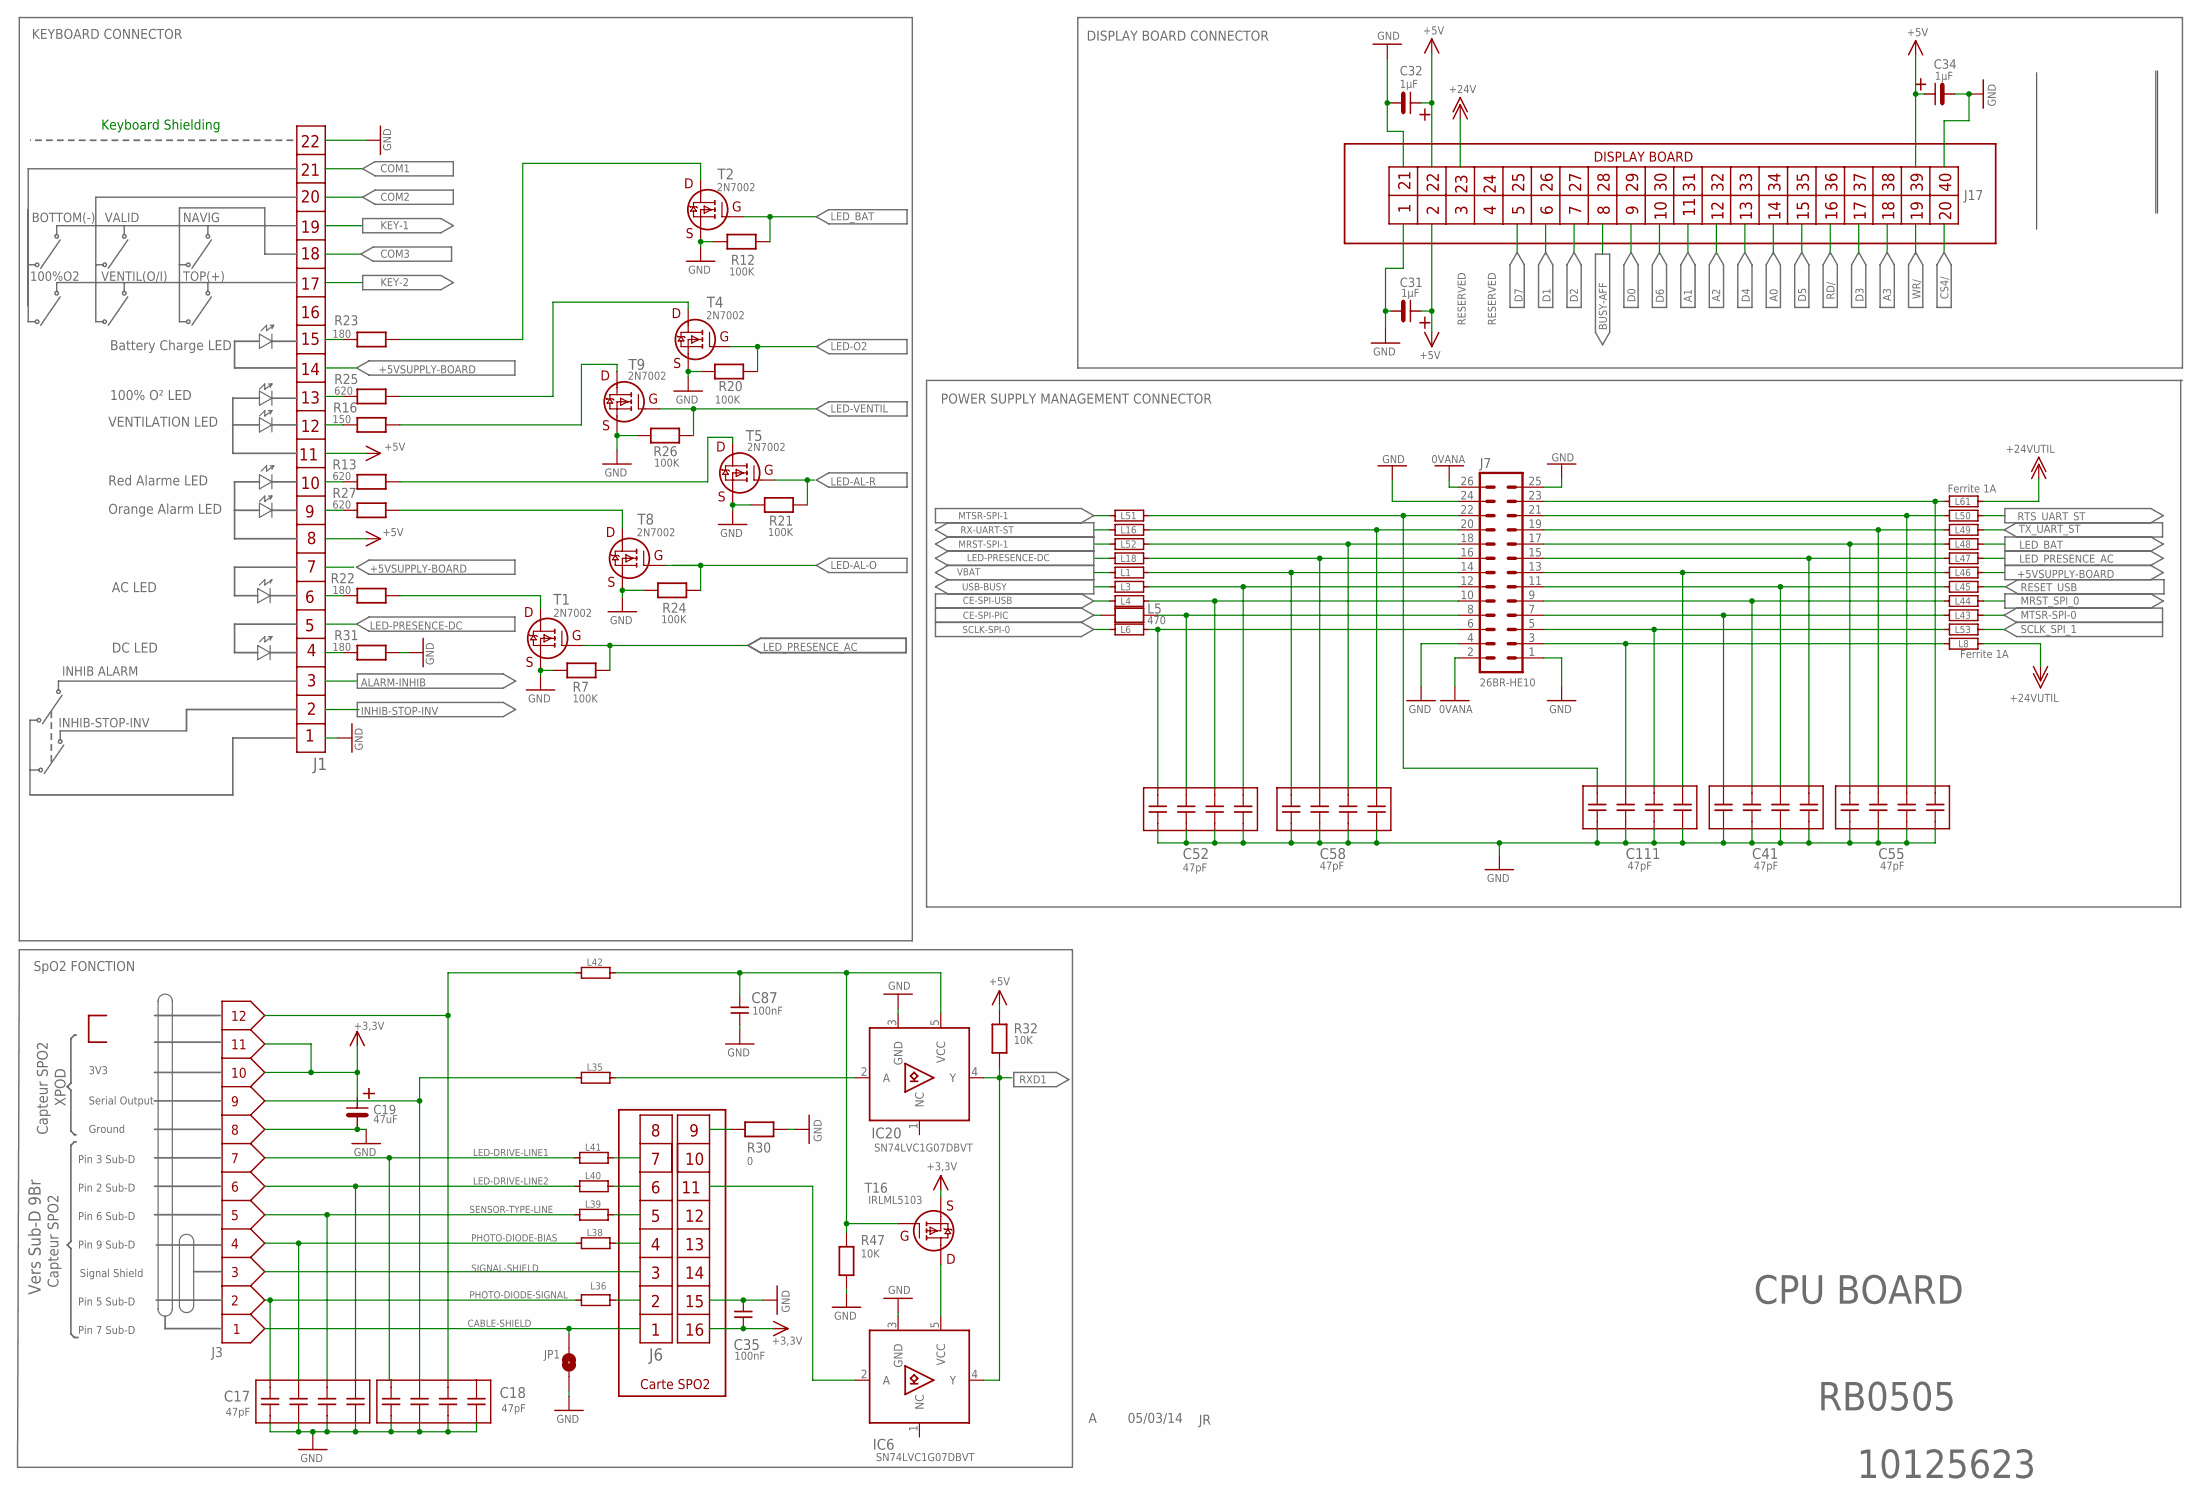
[picture p275: schematic 10125623A00.sch, sheet 7]

Parts:
C17, C18, C41, C52, C55, C58, C111: 47pF; RESEAU_1
C19: 47uF; TANTALB
C31, C32, C34: 1µF; TANTALB
C35: 100nF; C0805
C87: 100nF; C0603
IC6, IC20: SN74LVC1G07DBVT; SOT753_DBV
J1: ZIF-52610-2290
J3: 12BR
J6: 87606-408; 2X16BR
J7: 26BR-HE10
J17: FH_40BR; FH_SERIE
JP1: JUMP_0U; 0805
L1, L3, L4, L6, L16, L18, L35, L36, L38, L39, L40, L41, L42, L43, L44, L45, L46, L47, L48, L49, L50, L51, L52, L53: Ferrite 200mA; 0603
L5: 470; R0805
L8, L61: Ferrite 1A; PERL-FER
R7, R12, R20, R21, R24, R26: 100K; R0805
R13, R25, R27: 620; R0805
R16: 150; R1206
R22, R23, R31: 180; R1206
R30: 0; R0805
R32, R47: 10K; R0805
T1, T2, T4, T5, T8, T9: 2N7002; SOT23MOS
T16: IRLML5103; SOT23MOS

Connections:
0VANA: J7.2, J7.26
+3,3V: C19.+, C35.1, J3.10, J3.11, J6.16, T16.S
+5V: C31.+, C32.+, C34.+, J1.8B, J1.11B, J17.2, J17.22, J17.39, R32.2
+5VSUPPLY-BOARD: J1.7B, J1.14B, L46.2
+24V: J17.23
+24VUTIL: L8.2, L61.2
A0: J17.14
A1: J17.11
A2: J17.12
A3: J17.18
ALARM-INHIB: J1.3B
BUSY-AFF: J17.8
CABLE-SHIELD: J3.1, J6.1, JP1.2
CE-SPI-PIC: L5.1
CE-SPI-USB: L4.1
COM1: J1.21B
COM2: J1.20B
COM3: J1.18B
CS4/: J17.20
D0: J17.9
D1: J17.6
D2: J17.7
D3: J17.17
D4: J17.13
D5: J17.15
D6: J17.10
D7: J17.5
GND: C17.1, C17.2, C17.3, C17.4, C18.1, C18.2, C18.3, C18.4, C19.-, C31.-, C32.-, C34.-, C35.2, C41.1, C41.2, C41.3, C41.4, C52.1, C52.2, C52.3, C52.4, C55.1, C55.2, C55.3, C55.4, C58.1, C58.2, C58.3, C58.4, C87.1, C111.1, C111.2, C111.3, C111.4, IC6.3 (GND), IC20.3 (GND), J1.1B, J1.22B, J3.8, J6.15, J7.1, J7.4, J7.24, J7.25, J17.1, J17.21, J17.40, JP1.1, R7.2, R12.2, R20.2, R21.2, R24.2, R26.2, R30.1, R31.2, R47.1, T1.S, T2.S, T4.S, T5.S, T8.S, T9.S
INHIB-STOP-INV: J1.2B
KEY-1: J1.19B
KEY-2: J1.17B
LED-AL-O: R24.1, T8.G
LED-AL-R: R21.1, T5.G
LED-DRIVE-LINE1: C18.8, J3.7, L41.1
LED-DRIVE-LINE2: C17.5, J3.6, L40.1
LED-O2: R20.1, T4.G
LED-PRESENCE-DC: J1.5B, L18.1
LED-VENTIL: R26.1, T9.G
LED_BAT: L48.2, R12.1, T2.G
LED_PRESENCE_AC: L47.2, R7.1, T1.G
MRST-SPI-1: L52.1
MRST_SPI_0: L44.2
MTSR-SPI-0: L43.2
MTSR-SPI-1: L51.1
unnamed: J1.6B, R22.1
unnamed: R22.2, T1.D
unnamed: J1.15B, R23.1
unnamed: IC6.2 (A), J6.11
unnamed: J6.2, L36.2
unnamed: J6.4, L38.2
unnamed: J6.5, L39.2
unnamed: C87.2, IC20.5 (VCC), L42.2, R47.2, T16.G
unnamed: J6.6, L40.2
unnamed: J6.7, L41.2
unnamed: IC6.5 (VCC), T16.D
unnamed: IC20.2 (A), L35.2
unnamed: C41.8, J7.7, L43.1
unnamed: C18.6, J3.12, L42.1
unnamed: J1.4B, R31.1
unnamed: R23.2, T2.D
unnamed: C111.5, J7.13, L46.1
unnamed: J1.10B, R13.1
unnamed: J1.9B, R27.1
unnamed: C111.8, J7.22, L51.2
unnamed: C58.6, J7.18, L52.2
unnamed: C111.6, J7.5, L53.1
unnamed: C111.7, J7.3, L8.1
unnamed: C58.5, J7.20, L16.2
unnamed: J1.12B, R16.1
unnamed: J1.13B, R25.1
unnamed: R13.2, T5.D
unnamed: R27.2, T8.D
unnamed: R16.2, T9.D
unnamed: R25.2, T4.D
unnamed: C55.5, J7.23, L61.1
unnamed: C52.8, J7.6, L6.2
unnamed: C52.7, J7.8, L5.2
unnamed: C41.7, J7.9, L44.1
unnamed: C52.6, J7.10, L4.2
unnamed: C41.6, J7.11, L45.1
unnamed: C52.5, J7.12, L3.2
unnamed: C58.8, J7.14, L1.2
unnamed: C41.5, J7.15, L47.1
unnamed: C58.7, J7.16, L18.2
unnamed: C55.8, J7.17, L48.1
unnamed: C55.7, J7.19, L49.1
unnamed: C55.6, J7.21, L50.1
PHOTO-DIODE-BIAS: C17.7, J3.4, L38.1
PHOTO-DIODE-SIGNAL: C17.8, J3.2, L36.1
RD/: J17.16
RESET_USB: L45.2
RTS_UART_ST: L50.2
RX-UART-ST: L16.1
RXD1: IC6.4 (Y), IC20.4 (Y), R32.1
SCLK-SPI-0: L6.1
SCLK_SPI_1: L53.2
SENSOR-TYPE-LINE: C17.6, J3.5, L39.1
SIGNAL-SHIELD: J3.3, J6.3
SPO2-SERIAL-DATA-FORMAT: J6.9, R30.2
SPO2-SERIAL-OUT: C18.7, J3.9, L35.1
TX_UART_ST: L49.2
USB-BUSY: L3.1
VBAT: L1.1
WR/: J17.19

Notes on the sheet:
Red Alarme LED
AC LED
VENTILATION LED
DC LED
Orange Alarm LED
VALID
NAVIG
100%O2
VENTIL(O/I)
TOP(+)
KEYBOARD CONNECTOR
INHIB ALARM
100% O² LED
RESERVED
INHIB-STOP-INV
SpO2 FONCTION
Vers Sub-D 9Br
Pin 7 Sub-D
Pin 5 Sub-D
Pin 9 Sub-D
Pin 6 Sub-D
Pin 2 Sub-D
Pin 3 Sub-D
Signal Shield
Keyboard Shielding
Battery Charge LED
DISPLAY BOARD CONNECTOR
POWER SUPPLY MANAGEMENT CONNECTOR
BOTTOM(-)
CPU BOARD
RB0505
10125623
05/03/14
3V3
Serial Output
Ground
Capteur SPO2
XPOD
Carte SPO2
DISPLAY BOARD
